svenpetersen1965/C64-Keyboard/C64 Keyboard Standard Version/Rev. 0/Text/223_cover_sheet.docx

Project Documentation

C64 Mechanical Keyboard & Kernal Switcher

Project number: 223

Revision: 0

Date: 17.01.2025
