svenpetersen1965/C64-Keyboard/C64 Keyboard with Hot Swap Sockets/Rev. 2/Text/225_cover_sheet.docx

Project Documentation

C64 Mechanical Keyboard & Kernal Switcher
with Hot Swap Sockets

Project number: 225

Revision: 2

Date: 12.06.2026
