svenpetersen1965/C64-Keyboard/C64 Keyboard Standard Version/Rev. 2/Text/223_cover_sheet.docx

Project Documentation

C64 Mechanical Keyboard & Kernal Switcher

Project number: 223

Revision: 2

Date: 12.06.2026
