svenpetersen1965/C64-Keyboard/C64 Keyboard Standard Version/Rev. 1/Text/223_cover_sheet.docx

Project Documentation

C64 Mechanical Keyboard & Kernal Switcher

Project number: 223

Revision: 1

Date: 21.05.2026
