svenpetersen1965/C64-Keyboard/C64 Keyboard connector PCB/Rev. 0/text/224_cover_sheet.docx

Project Documentation

C64 Keyboard Connector PCB

Project number: 224

Revision: 0

Date: 04.06.2026
