svenpetersen1965/C64-Keyboard/Keycaps/text/230_cover_sheet.docx

How to: Keycaps

Project number: 230

Revision: 0.0

Date: 04.09.2026

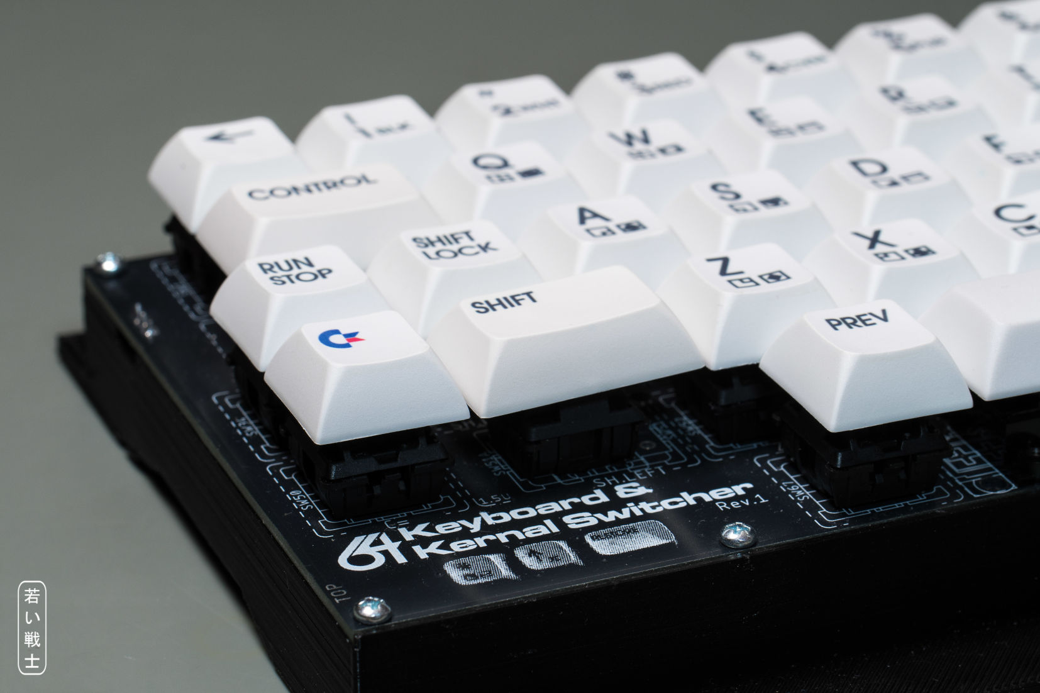
[picture p92: figure]
