svenpetersen1965/C64-Keyboard/C64 Keyboard Standard Version/Rev. 0/pictures/0258_-_C64_KB_PCBs.JPG

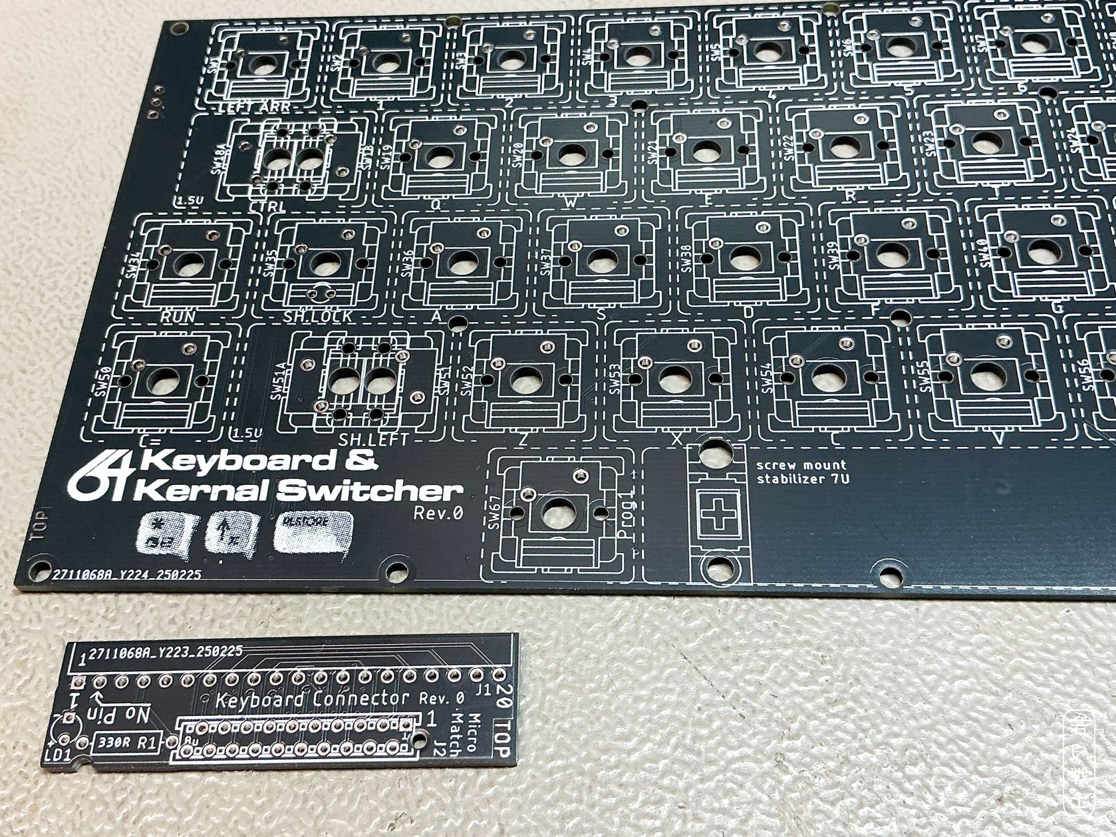
C64 Keyboard Standard Version/Rev. 0/pictures/0258_-_C64_KB_PCBs.JPG
