svenpetersen1965/C64-Keyboard/C64 Keyboard Standard Version/Rev. 0/pictures/0268_-_7U_stabilizer_L.JPG

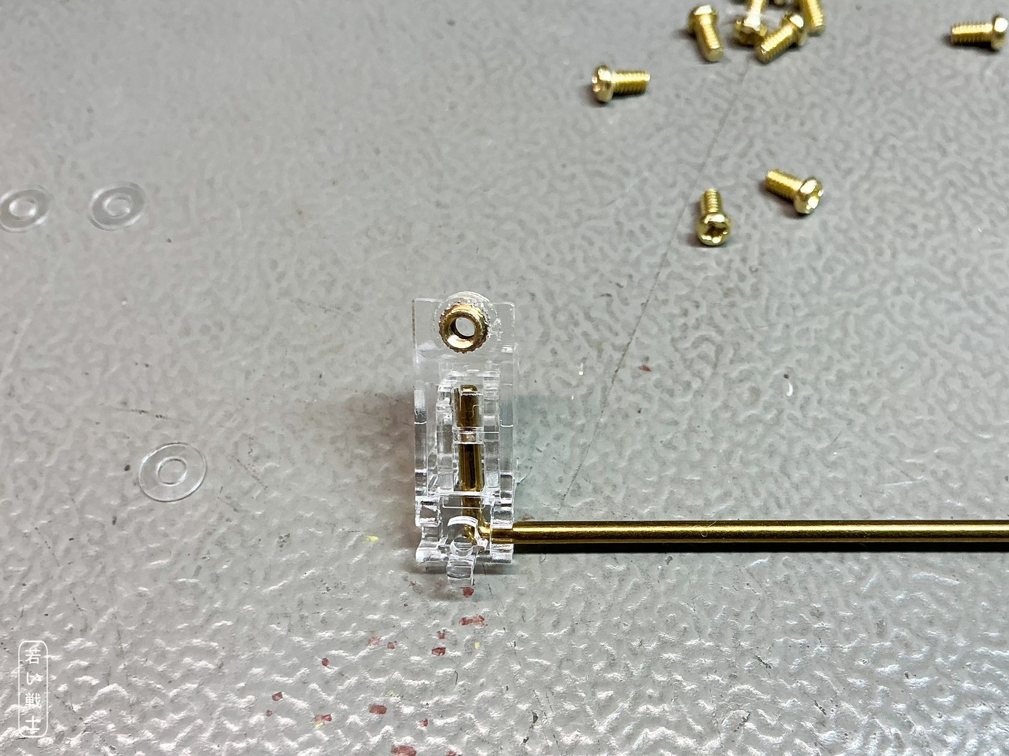
C64 Keyboard Standard Version/Rev. 0/pictures/0268_-_7U_stabilizer_L.JPG
