svenpetersen1965/C64-Keyboard/C64 Keyboard Standard Version/Rev. 0/pictures/0269_-_7U_stabilizer_R.JPG

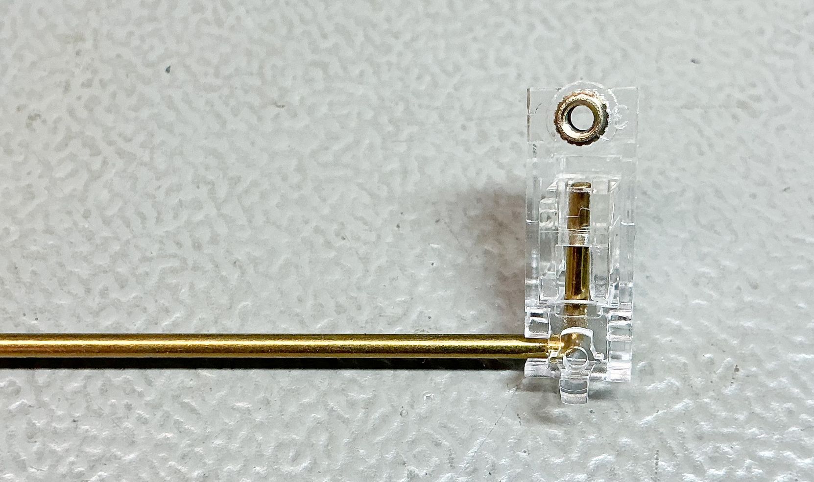
C64 Keyboard Standard Version/Rev. 0/pictures/0269_-_7U_stabilizer_R.JPG
