svenpetersen1965/C64-Keyboard/C64 Keyboard Standard Version/Rev. 0/pictures/0293_-_kb_in_retro_fuzion_case.JPG

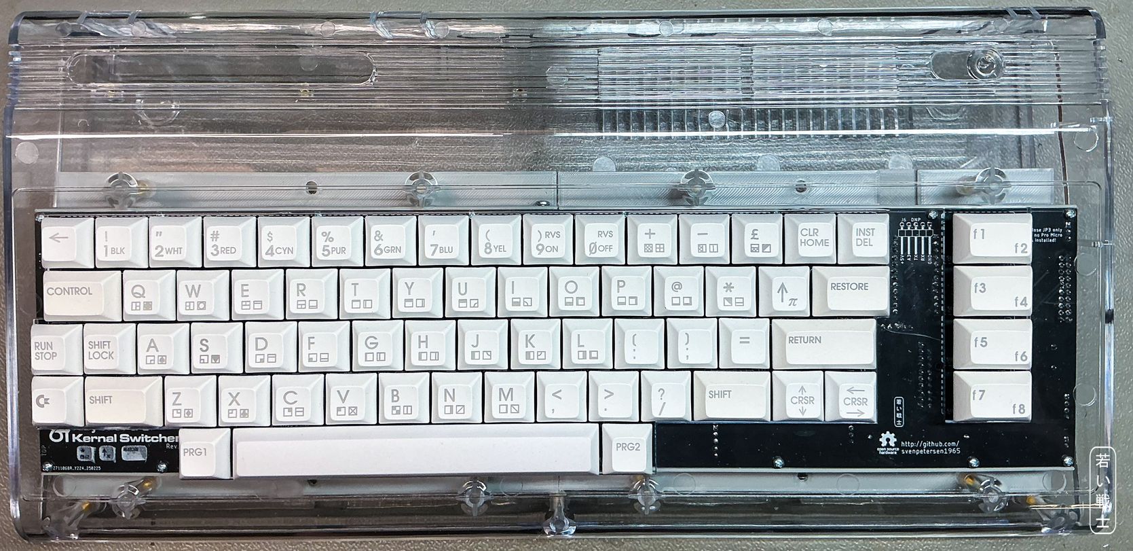
C64 Keyboard Standard Version/Rev. 0/pictures/0293_-_kb_in_retro_fuzion_case.JPG
