svenpetersen1965/C64-Keyboard/C64 Keyboard Standard Version/Rev. 0/pictures/0296_-_kb_in_dirty_breadbin.JPG

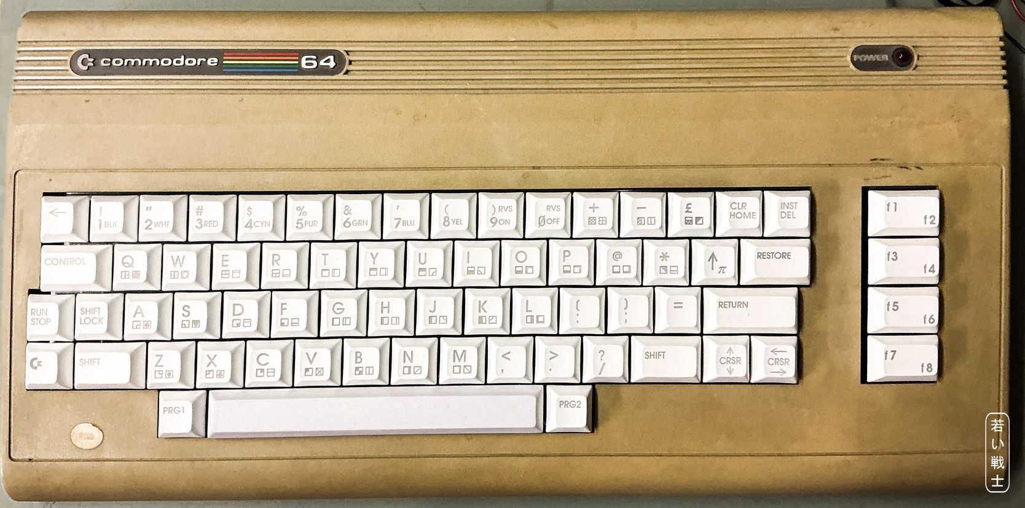
C64 Keyboard Standard Version/Rev. 0/pictures/0296_-_kb_in_dirty_breadbin.JPG
