svenpetersen1965/C64-Keyboard/C64 Keyboard Standard Version/Rev. 0/pictures/0303_-_collision_C64C.JPG

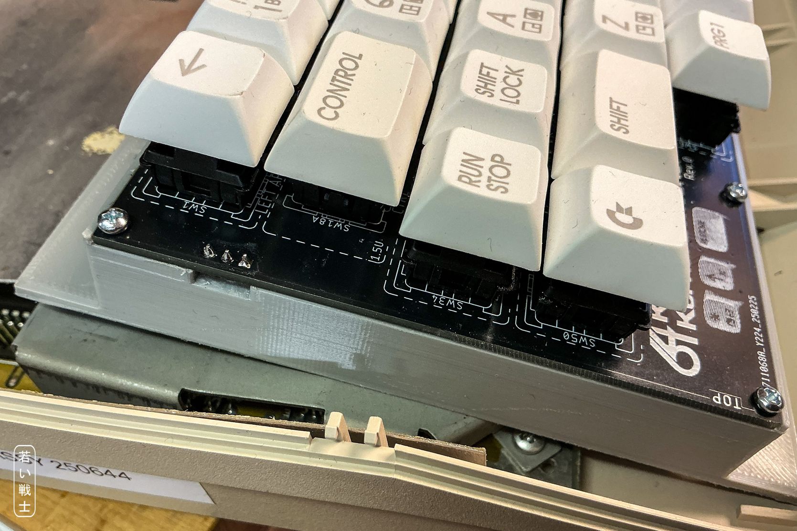
C64 Keyboard Standard Version/Rev. 0/pictures/0303_-_collision_C64C.JPG
