svenpetersen1965/C64-Keyboard/C64 Keyboard Standard Version/Rev. 0/pictures/0335_-_SE_layxout.JPG

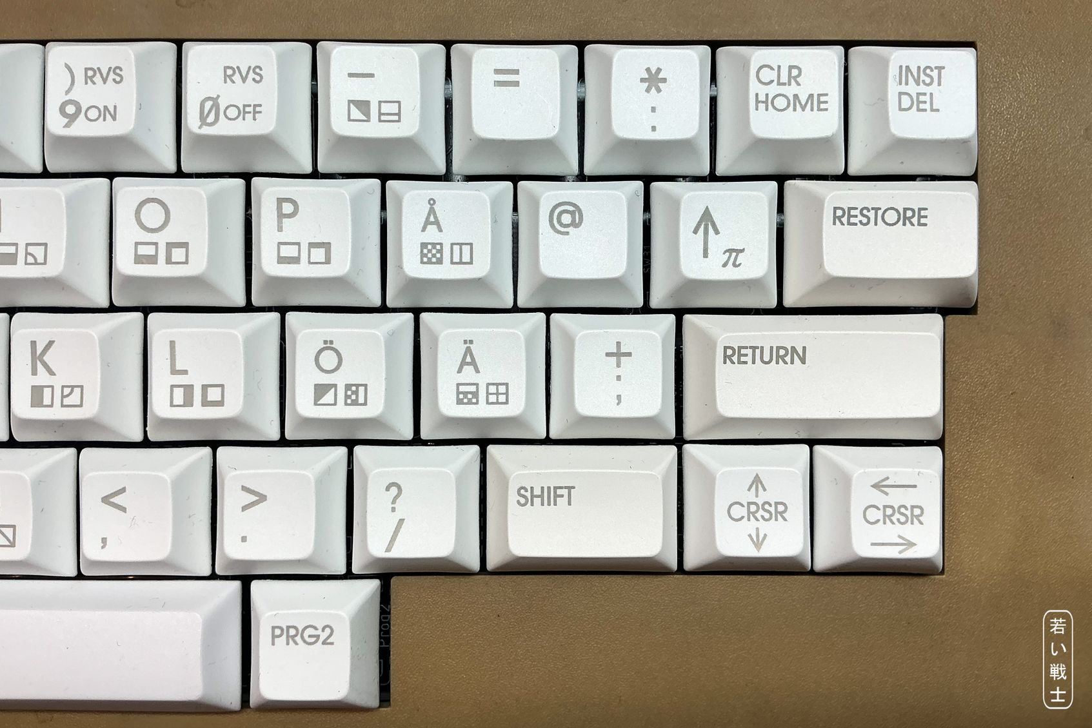
C64 Keyboard Standard Version/Rev. 0/pictures/0335_-_SE_layxout.JPG
