svenpetersen1965/C64-Keyboard/C64 Keyboard Standard Version/Rev. 0/pictures/0339_-_ES_layout.JPG

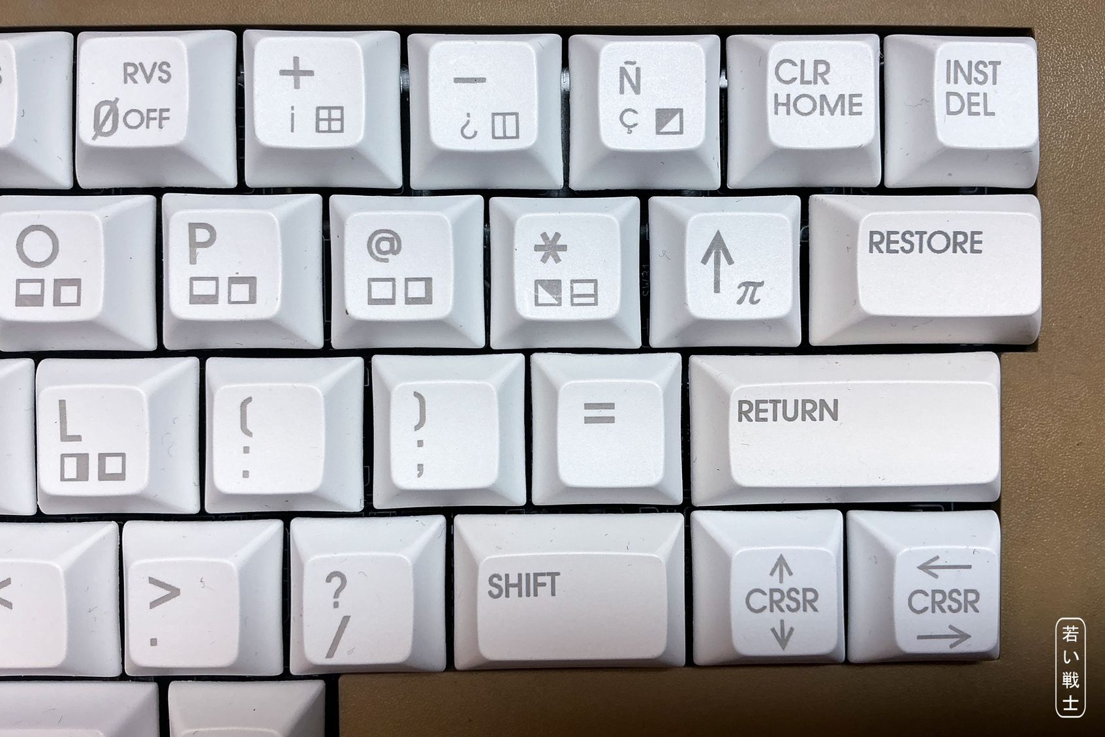
C64 Keyboard Standard Version/Rev. 0/pictures/0339_-_ES_layout.JPG
