svenpetersen1965/C64-Keyboard/C64 Keyboard Standard Version/Rev. 0/pictures/0346_-_complete_keyboard.JPG

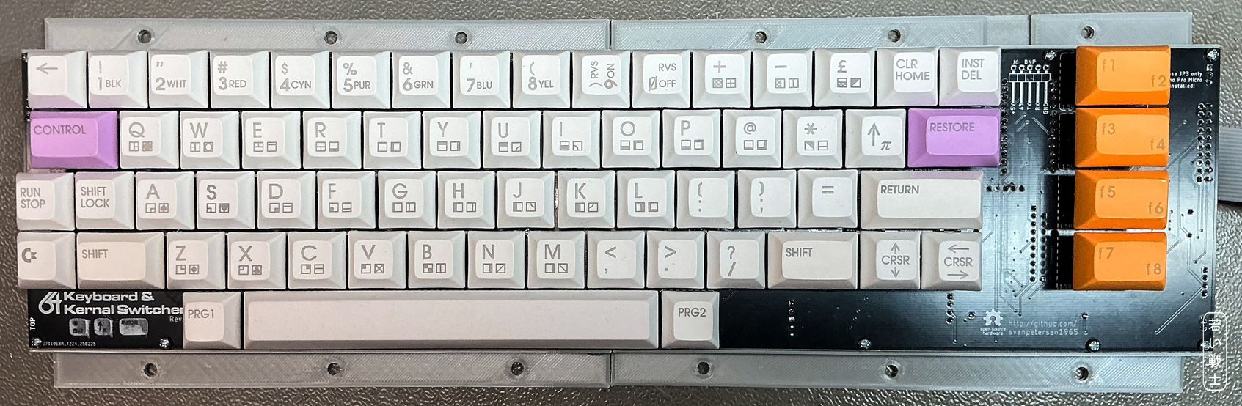
C64 Keyboard Standard Version/Rev. 0/pictures/0346_-_complete_keyboard.JPG
