svenpetersen1965/C64-Keyboard/C64 Keyboard Standard Version/Rev. 0/pictures/0347_-_bottom_w_stiffner.JPG

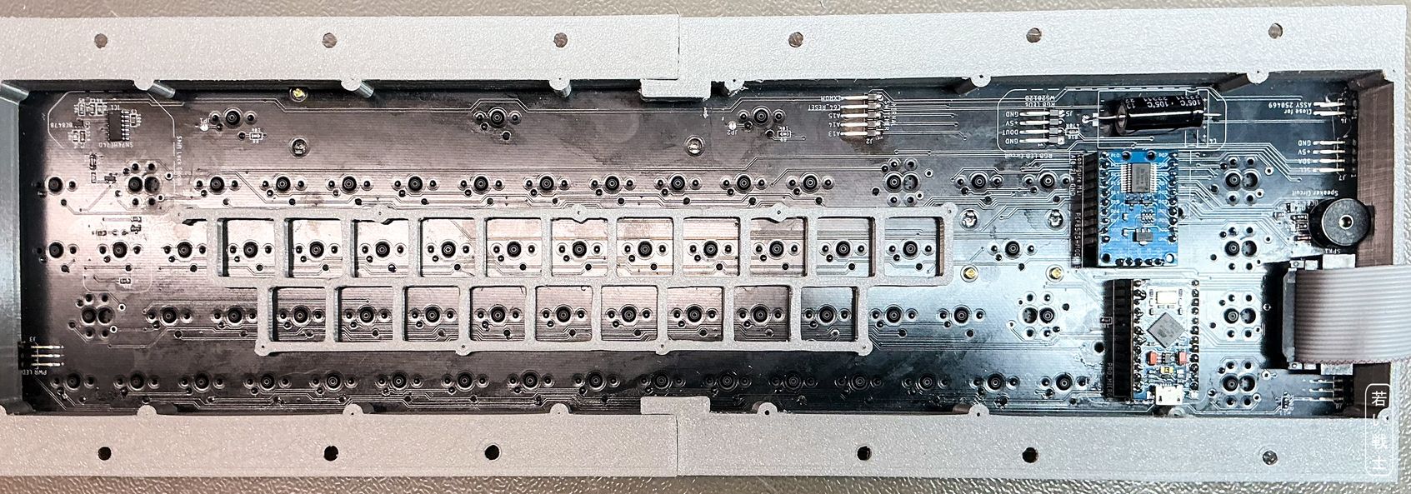
C64 Keyboard Standard Version/Rev. 0/pictures/0347_-_bottom_w_stiffner.JPG
