svenpetersen1965/C64-Keyboard/C64 Keyboard Standard Version/Rev. 0/pictures/4119_-_PCF8575_top.JPG

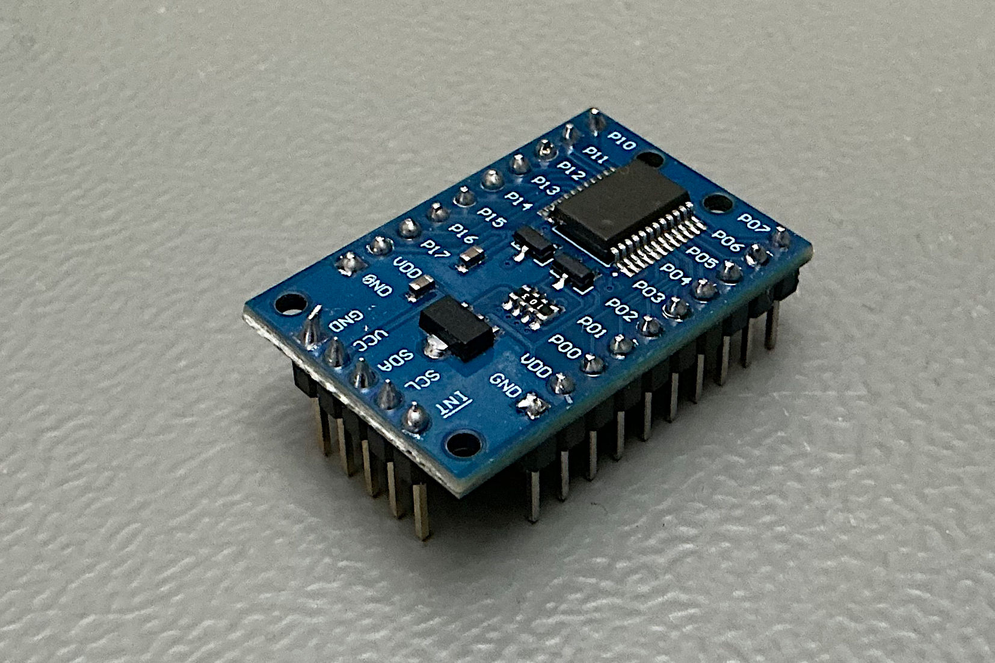
C64 Keyboard Standard Version/Rev. 0/pictures/4119_-_PCF8575_top.JPG
