svenpetersen1965/C64-Keyboard/C64 Keyboard Standard Version/Rev. 0/pictures/4126_-_J2_Kernal_Select.JPG

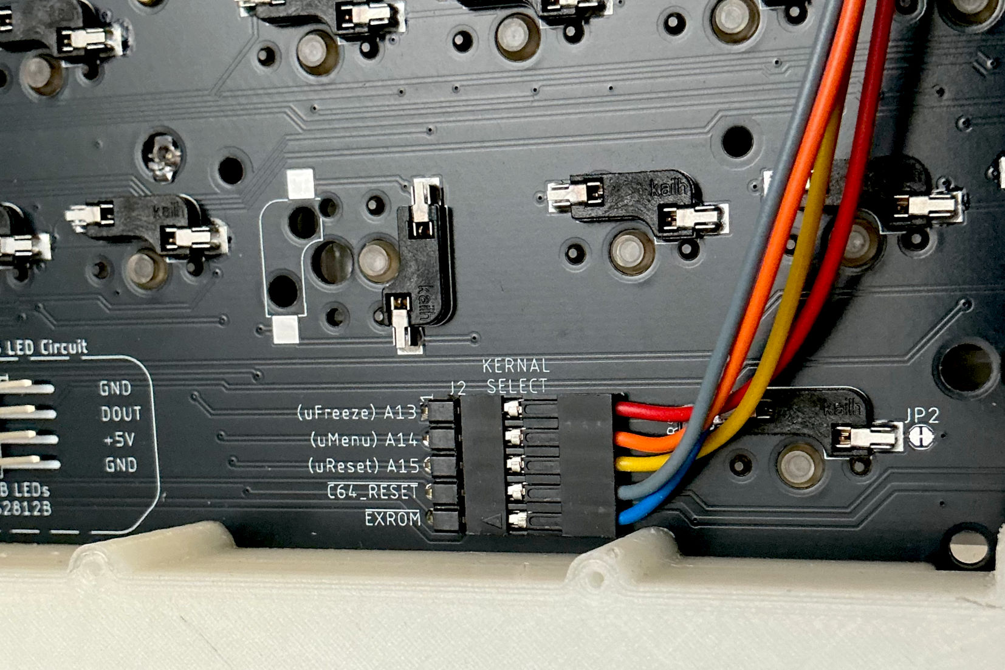
C64 Keyboard Standard Version/Rev. 0/pictures/4126_-_J2_Kernal_Select.JPG
