svenpetersen1965/C64-Keyboard/C64 Keyboard Standard Version/Rev. 0/pictures/4128_-_top_w_cables.JPG

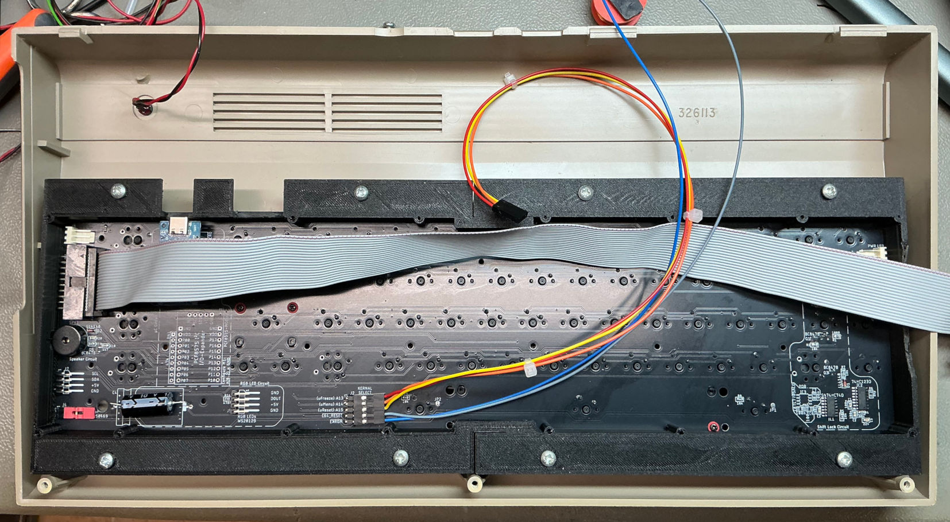
C64 Keyboard Standard Version/Rev. 0/pictures/4128_-_top_w_cables.JPG
