svenpetersen1965/C64-Keyboard/C64 Keyboard Standard Version/Rev. 0/pictures/4382_-_Shift_Lock.JPG

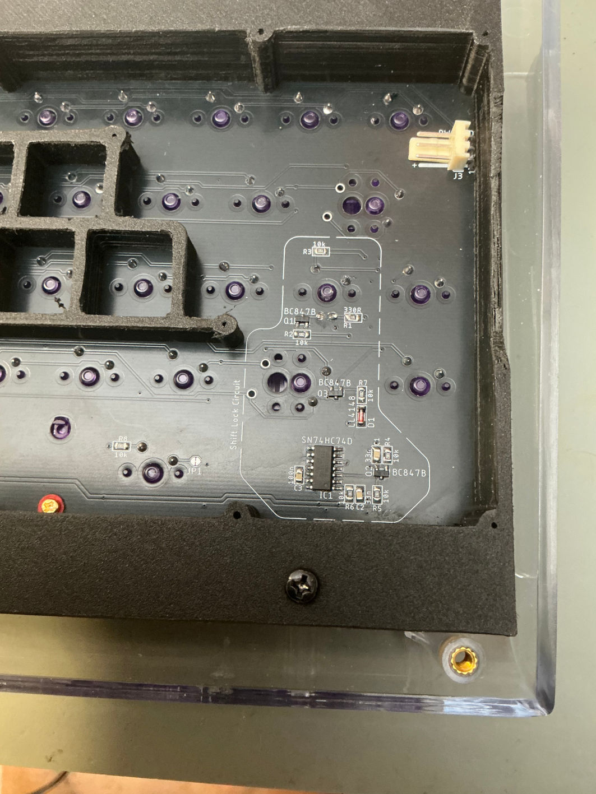
C64 Keyboard Standard Version/Rev. 0/pictures/4382_-_Shift_Lock.JPG
