svenpetersen1965/C64-Keyboard/C64 Keyboard Standard Version/Rev. 0/pictures/4384_-_RGB_LED.JPG

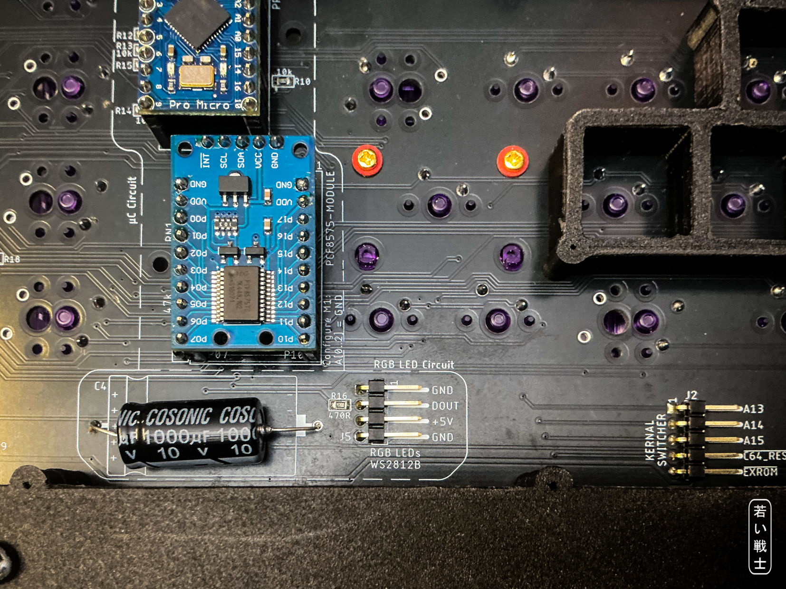
C64 Keyboard Standard Version/Rev. 0/pictures/4384_-_RGB_LED.JPG
