svenpetersen1965/C64-Keyboard/C64 Keyboard Standard Version/Rev. 0/pictures/4387_-_pro_micro_circuit.JPG

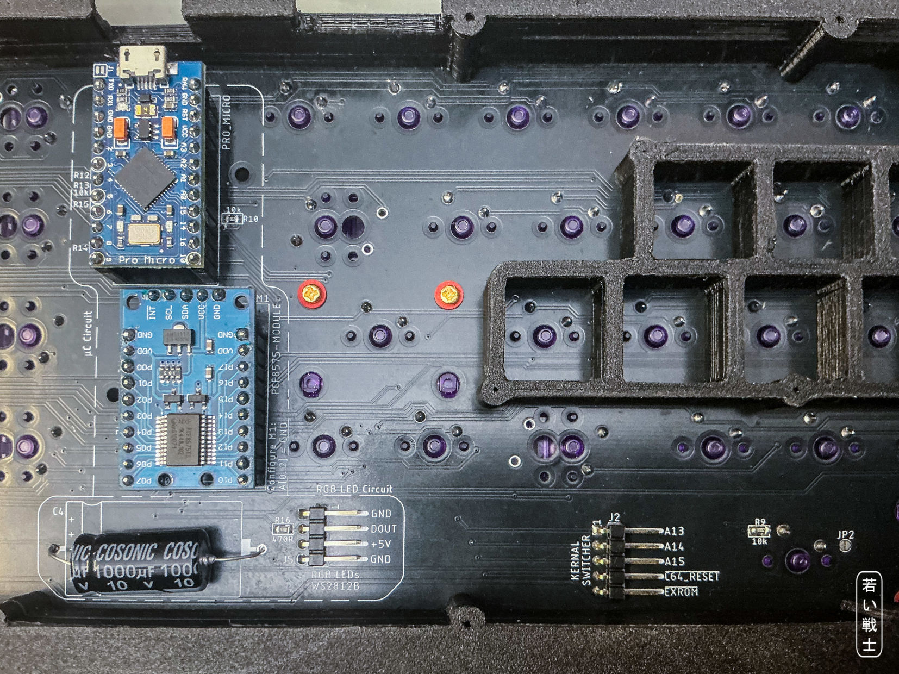
C64 Keyboard Standard Version/Rev. 0/pictures/4387_-_pro_micro_circuit.JPG
