svenpetersen1965/C64-Keyboard/C64 Keyboard Standard Version/Rev. 0/pictures/4558_-_ultimate_button_connector.JPG

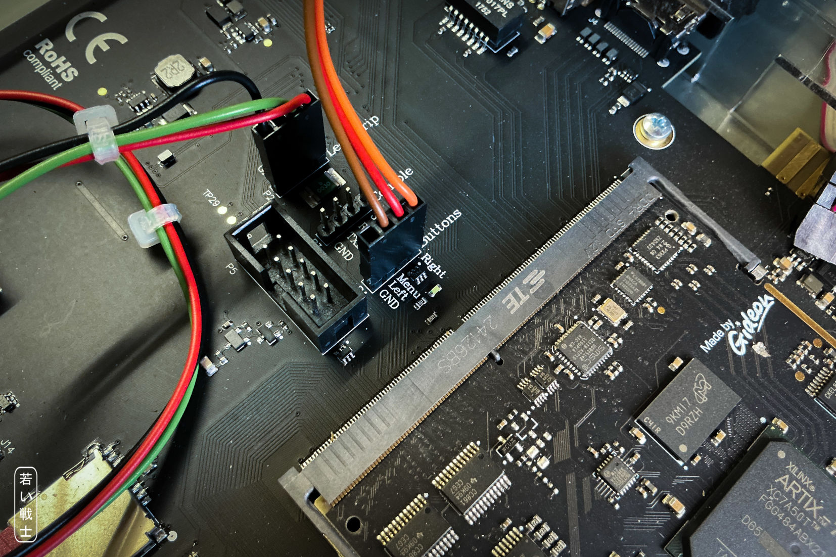
C64 Keyboard Standard Version/Rev. 0/pictures/4558_-_ultimate_button_connector.JPG
