svenpetersen1965/C64-Keyboard/C64 Keyboard Standard Version/Rev. 0/pictures/4559_-_ultimate_button_cable.JPG

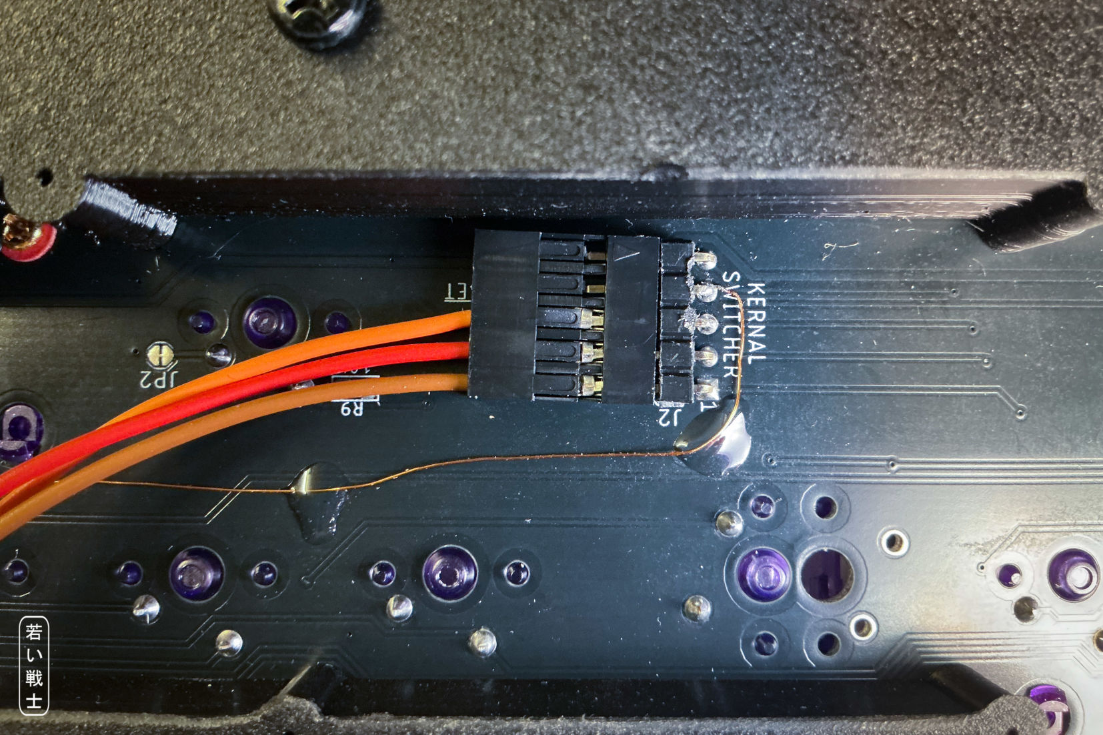
C64 Keyboard Standard Version/Rev. 0/pictures/4559_-_ultimate_button_cable.JPG
