svenpetersen1965/C64-Keyboard/C64 Keyboard Standard Version/Rev. 0/pictures/9813_-_switch_bouncing.JPG

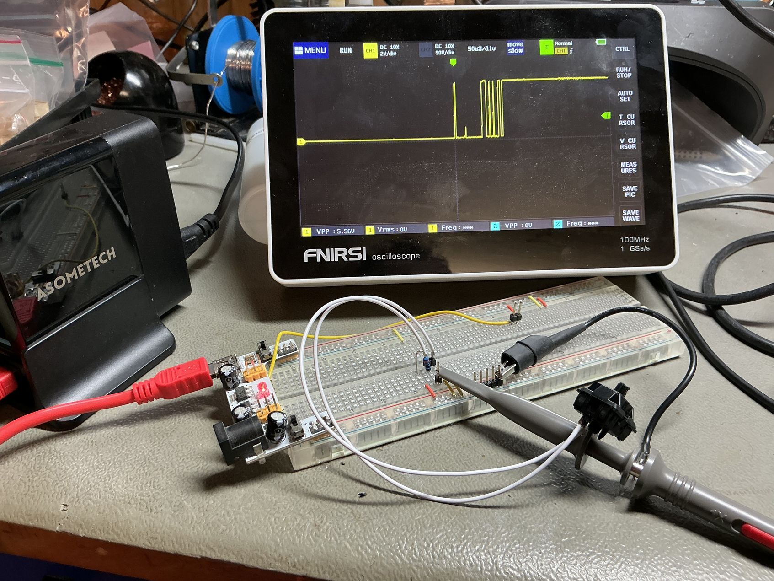
C64 Keyboard Standard Version/Rev. 0/pictures/9813_-_switch_bouncing.JPG
