svenpetersen1965/C64-Keyboard/C64 Keyboard Standard Version/Rev. 0/pictures/9957_-_measuring_key_position.JPG

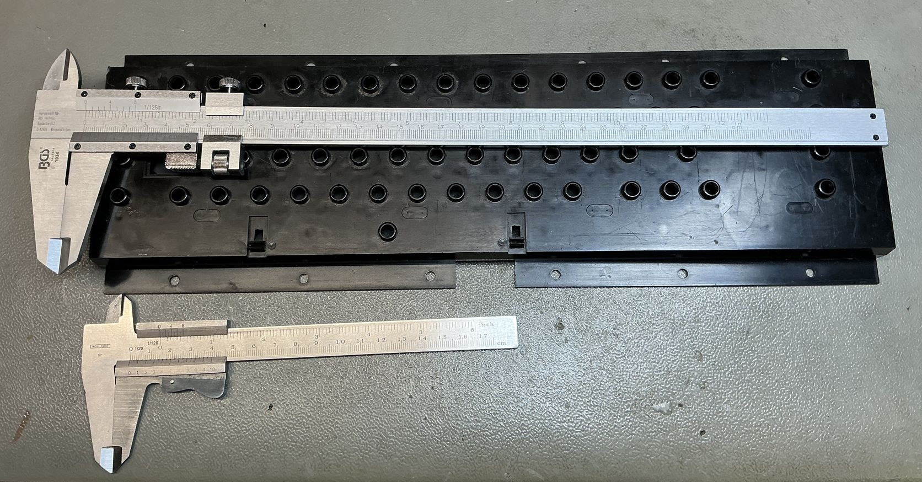
C64 Keyboard Standard Version/Rev. 0/pictures/9957_-_measuring_key_position.JPG
