svenpetersen1965/C64-Keyboard/C64 Keyboard Standard Version/Rev. 0/pictures/Ultimate_freeze_falling.png

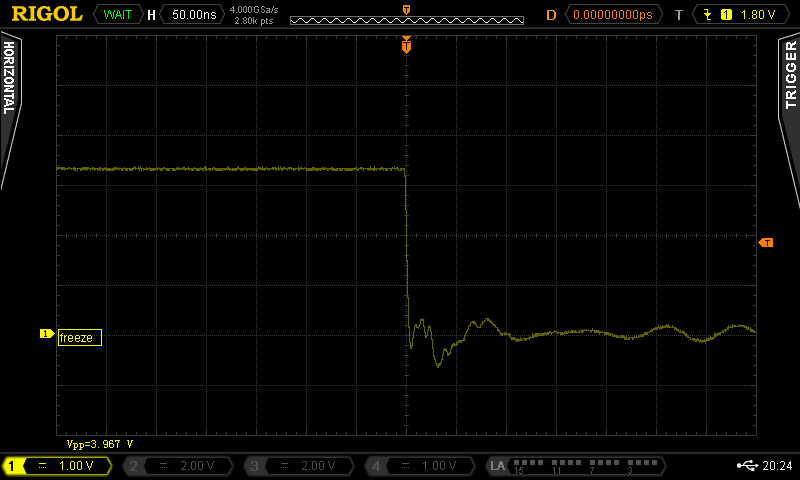
C64 Keyboard Standard Version/Rev. 0/pictures/Ultimate_freeze_falling.png
