svenpetersen1965/C64-Keyboard/C64 Keyboard Standard Version/Rev. 1/pictures/3988_-_v1_stabilizer.JPG

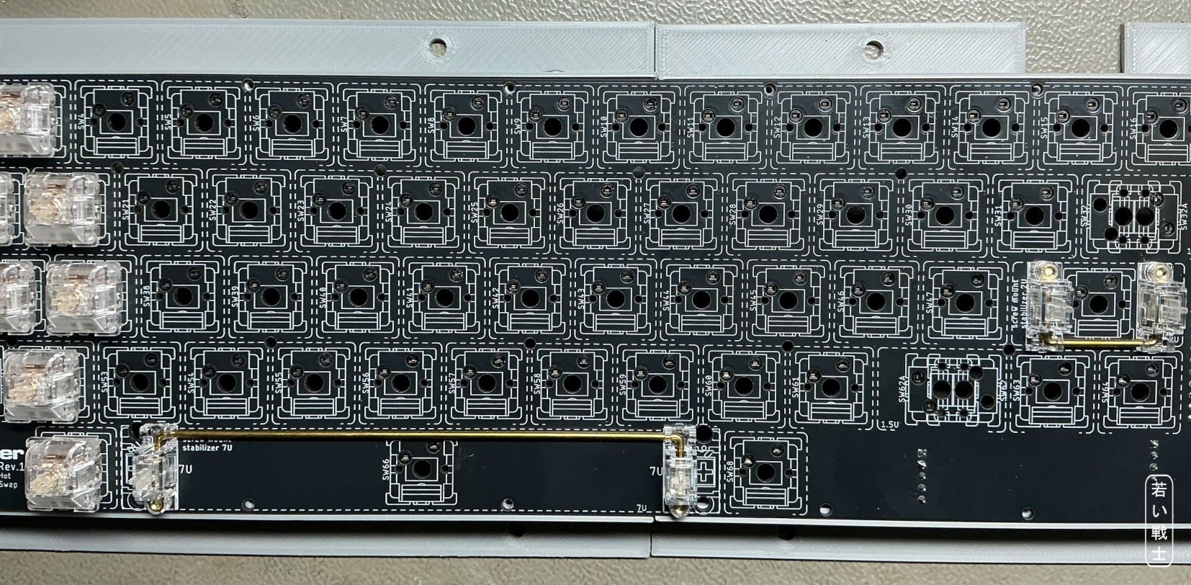
C64 Keyboard Standard Version/Rev. 1/pictures/3988_-_v1_stabilizer.JPG
