svenpetersen1965/C64-Keyboard/C64 Keyboard Standard Version/Rev. 1/pictures/3989_-_C64KB_v1_complete.JPG

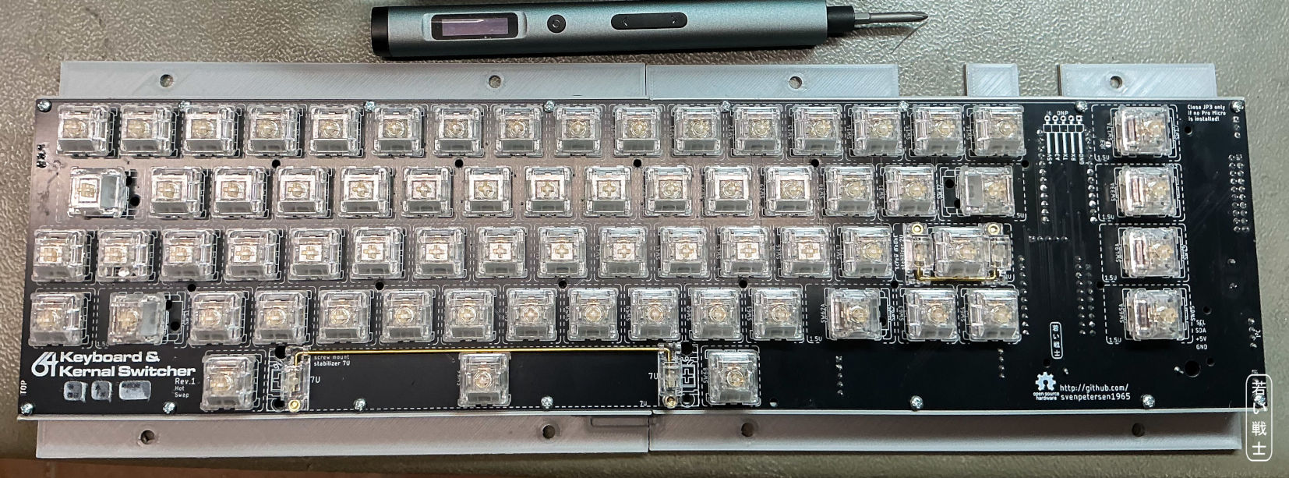
C64 Keyboard Standard Version/Rev. 1/pictures/3989_-_C64KB_v1_complete.JPG
