svenpetersen1965/C64-Keyboard/C64 Keyboard Standard Version/Rev. 1/pictures/4592_-_9U_stabilizer.JPG

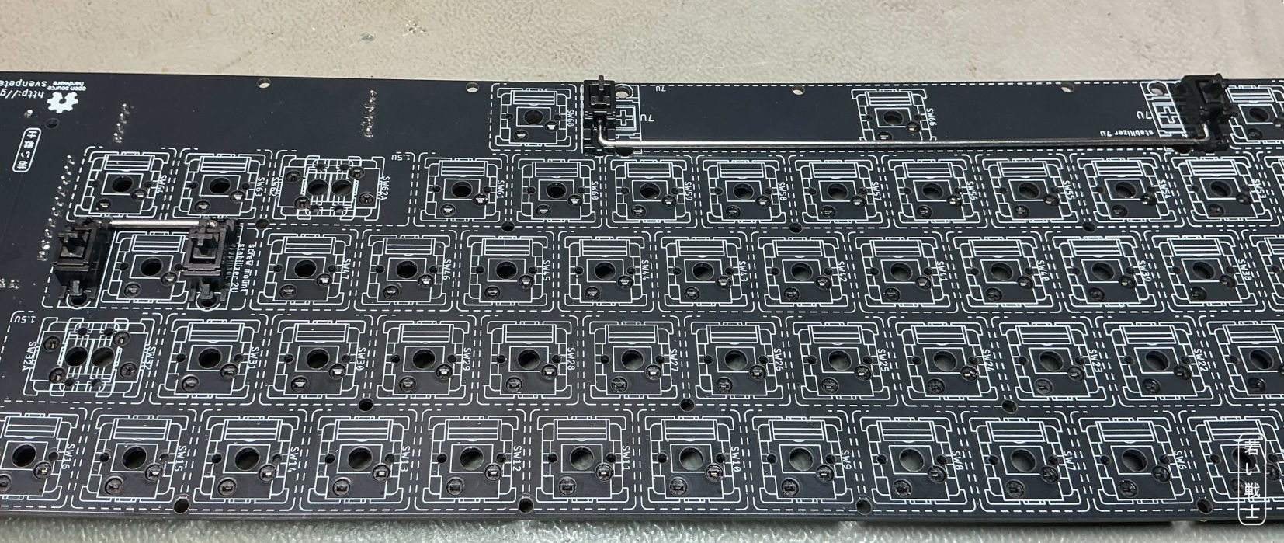
C64 Keyboard Standard Version/Rev. 1/pictures/4592_-_9U_stabilizer.JPG
