svenpetersen1965/C64-Keyboard/Cables/pictures/4047_-_Detail_MicroMatch.JPG

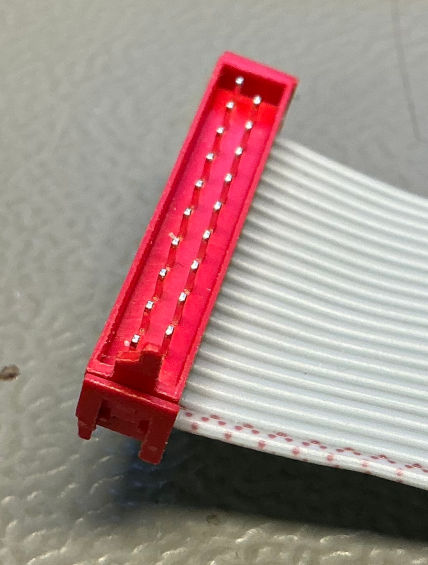
Cables/pictures/4047_-_Detail_MicroMatch.JPG
