svenpetersen1965/C64-Keyboard/Cables/pictures/4127_-_kernal_switcher_cable.JPG

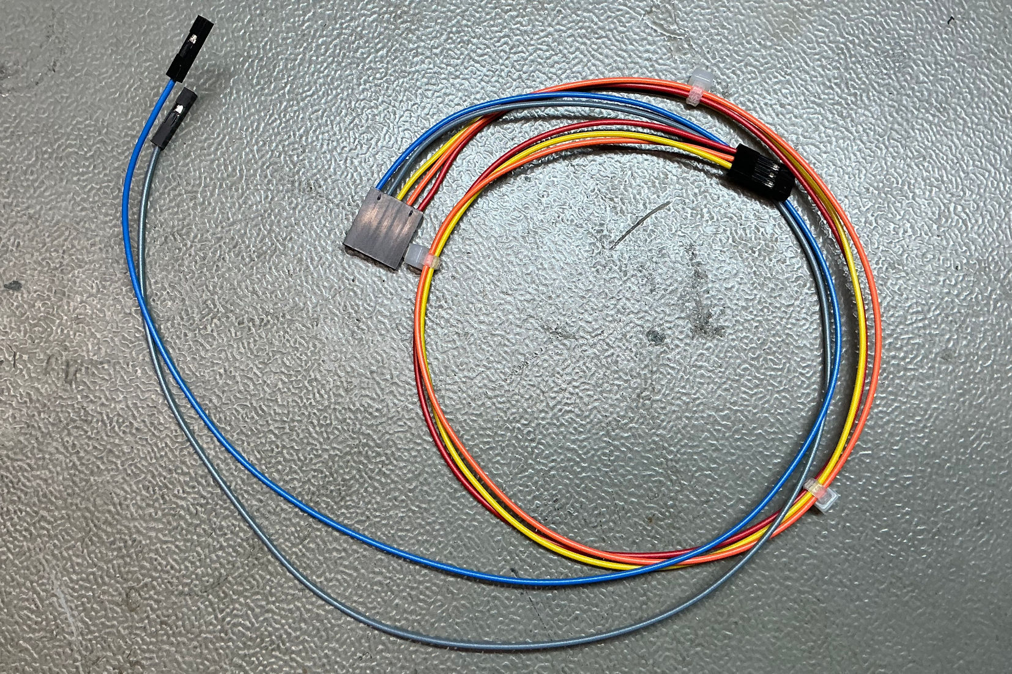
Cables/pictures/4127_-_kernal_switcher_cable.JPG
