svenpetersen1965/C64-Keyboard/Keycaps/Exported-DSA-keycaps/Danisch/SW45_AE.png

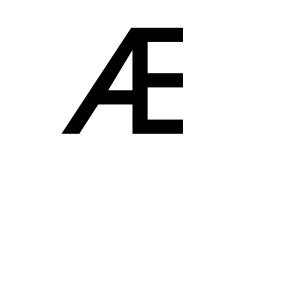
Keycaps/Exported-DSA-keycaps/Danisch/SW45_AE.png
