svenpetersen1965/C64-Keyboard/Keycaps/Exported-DSA-keycaps/Danisch/SW47_semicolon.png

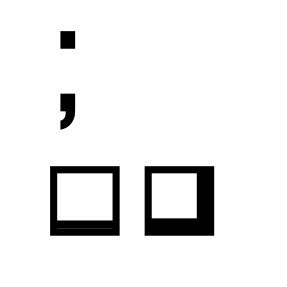
Keycaps/Exported-DSA-keycaps/Danisch/SW47_semicolon.png
