svenpetersen1965/C64-Keyboard/Keycaps/Exported-DSA-keycaps/Spanish/SW14_Ntilde.png

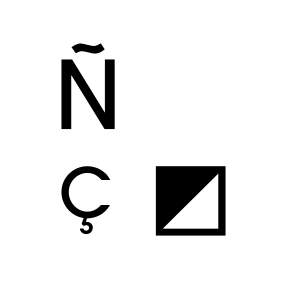
Keycaps/Exported-DSA-keycaps/Spanish/SW14_Ntilde.png
