svenpetersen1965/C64-Keyboard/Keycaps/Exported-DSA-keycaps/SW1_left_arrow.png

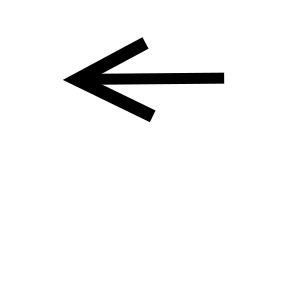
Keycaps/Exported-DSA-keycaps/SW1_left_arrow.png
