svenpetersen1965/C64-Keyboard/Keycaps/Exported-DSA-keycaps/SW2_1.png

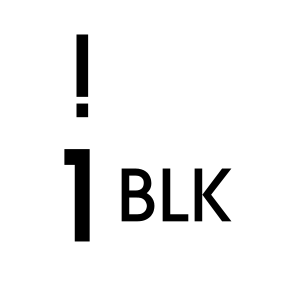
Keycaps/Exported-DSA-keycaps/SW2_1.png
