svenpetersen1965/C64-Keyboard/Keycaps/Exported-DSA-keycaps/SW4_3.png

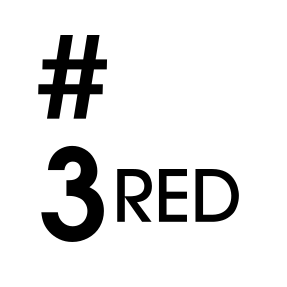
Keycaps/Exported-DSA-keycaps/SW4_3.png
