svenpetersen1965/C64-Keyboard/Keycaps/Exported-DSA-keycaps/SW6_5.png

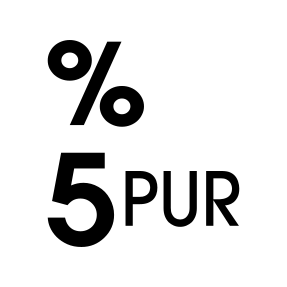
Keycaps/Exported-DSA-keycaps/SW6_5.png
