svenpetersen1965/C64-Keyboard/Keycaps/Exported-DSA-keycaps/SW11_0.png

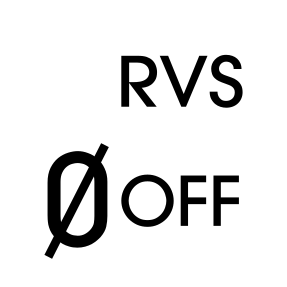
Keycaps/Exported-DSA-keycaps/SW11_0.png
