svenpetersen1965/C64-Keyboard/Keycaps/Exported-DSA-keycaps/SW15_clrhome.png

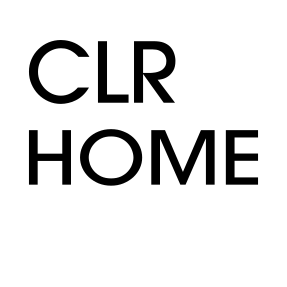
Keycaps/Exported-DSA-keycaps/SW15_clrhome.png
