svenpetersen1965/C64-Keyboard/Keycaps/Exported-DSA-keycaps/SW17_f1f2.png

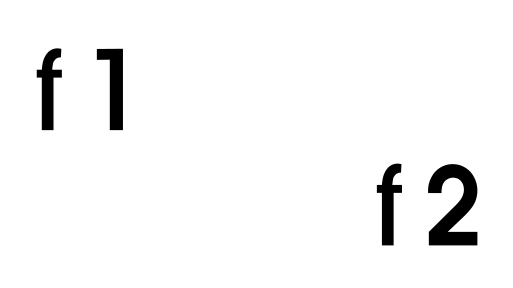
Keycaps/Exported-DSA-keycaps/SW17_f1f2.png
