svenpetersen1965/C64-Keyboard/Keycaps/Exported-DSA-keycaps/SW18_CONTROL.png

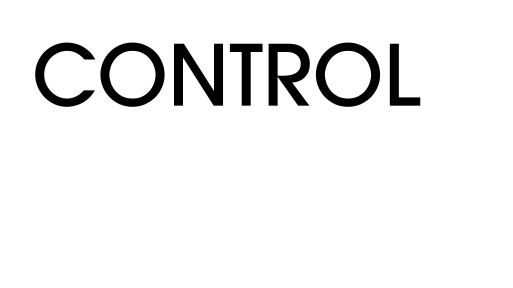
Keycaps/Exported-DSA-keycaps/SW18_CONTROL.png
