svenpetersen1965/C64-Keyboard/Keycaps/Exported-DSA-keycaps/SW22_R.png

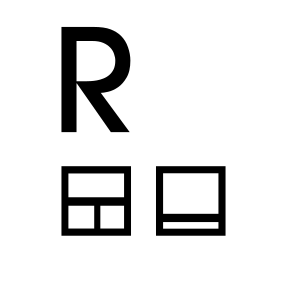
Keycaps/Exported-DSA-keycaps/SW22_R.png
