svenpetersen1965/C64-Keyboard/Keycaps/Exported-DSA-keycaps/SW24_Y.png

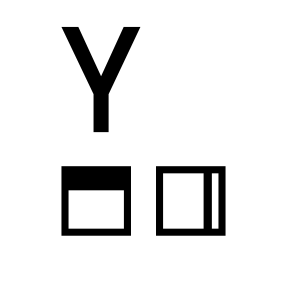
Keycaps/Exported-DSA-keycaps/SW24_Y.png
