svenpetersen1965/C64-Keyboard/Keycaps/Exported-DSA-keycaps/SW25_U.png

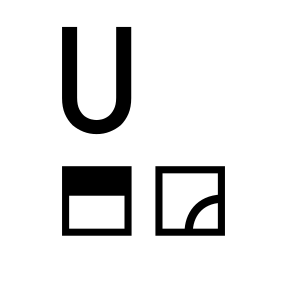
Keycaps/Exported-DSA-keycaps/SW25_U.png
