svenpetersen1965/C64-Keyboard/Keycaps/Exported-DSA-keycaps/SW26_I.png

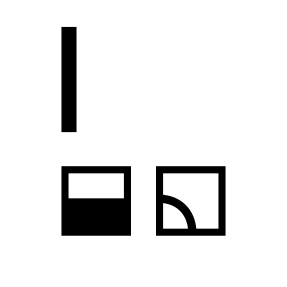
Keycaps/Exported-DSA-keycaps/SW26_I.png
