svenpetersen1965/C64-Keyboard/Keycaps/Exported-DSA-keycaps/SW29_at.png

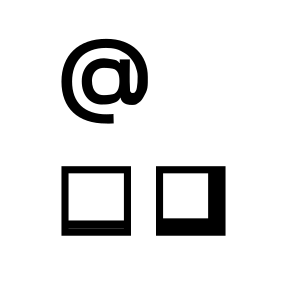
Keycaps/Exported-DSA-keycaps/SW29_at.png
