svenpetersen1965/C64-Keyboard/Keycaps/Exported-DSA-keycaps/SW31_up_arrow.png

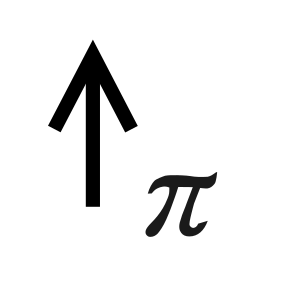
Keycaps/Exported-DSA-keycaps/SW31_up_arrow.png
