svenpetersen1965/C64-Keyboard/Keycaps/Exported-DSA-keycaps/SW33_f3f4.png

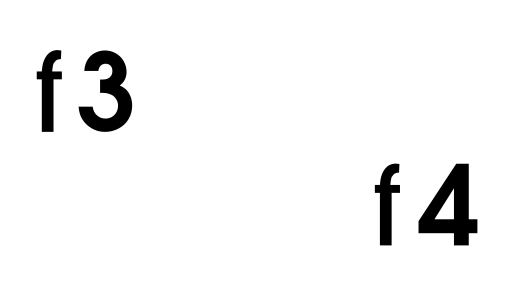
Keycaps/Exported-DSA-keycaps/SW33_f3f4.png
