svenpetersen1965/C64-Keyboard/Keycaps/Exported-DSA-keycaps/SW38_D.png

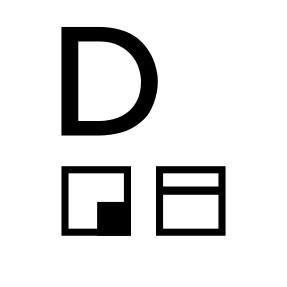
Keycaps/Exported-DSA-keycaps/SW38_D.png
