svenpetersen1965/C64-Keyboard/Keycaps/Exported-DSA-keycaps/SW39_F.png

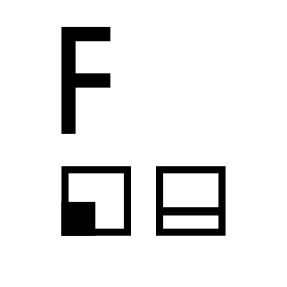
Keycaps/Exported-DSA-keycaps/SW39_F.png
