svenpetersen1965/C64-Keyboard/Keycaps/Exported-DSA-keycaps/SW44_L.png

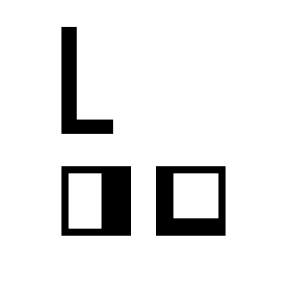
Keycaps/Exported-DSA-keycaps/SW44_L.png
