svenpetersen1965/C64-Keyboard/Keycaps/Exported-DSA-keycaps/SW50_64.png

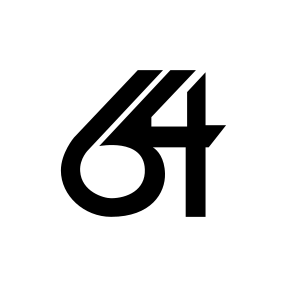
Keycaps/Exported-DSA-keycaps/SW50_64.png
