svenpetersen1965/C64-Keyboard/Keycaps/Exported-DSA-keycaps/SW50_C=.png

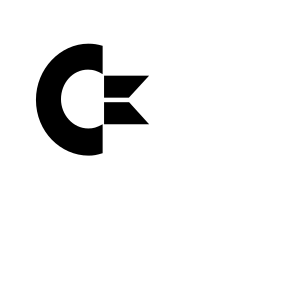
Keycaps/Exported-DSA-keycaps/SW50_C=.png
