svenpetersen1965/C64-Keyboard/Keycaps/Exported-DSA-keycaps/SW51_shift.png

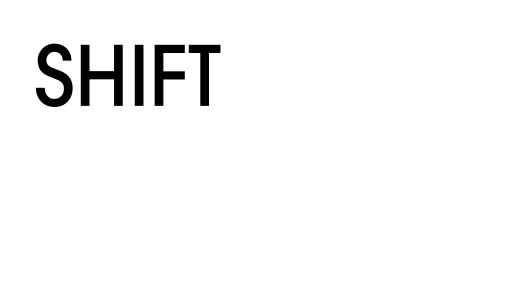
Keycaps/Exported-DSA-keycaps/SW51_shift.png
