svenpetersen1965/C64-Keyboard/Keycaps/Exported-DSA-keycaps/SW55_V.png

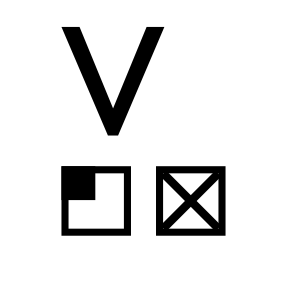
Keycaps/Exported-DSA-keycaps/SW55_V.png
