svenpetersen1965/C64-Keyboard/Keycaps/Exported-DSA-keycaps/SW56_B.png

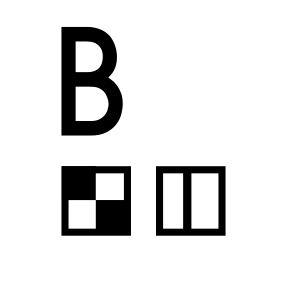
Keycaps/Exported-DSA-keycaps/SW56_B.png
