svenpetersen1965/C64-Keyboard/Keycaps/Exported-DSA-keycaps/SW59_comma.png

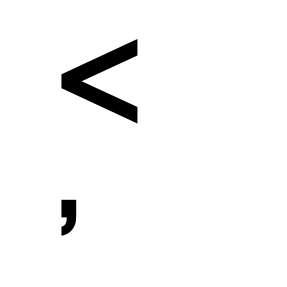
Keycaps/Exported-DSA-keycaps/SW59_comma.png
