svenpetersen1965/C64-Keyboard/Keycaps/Exported-DSA-keycaps/SW64_CRSRlr.png

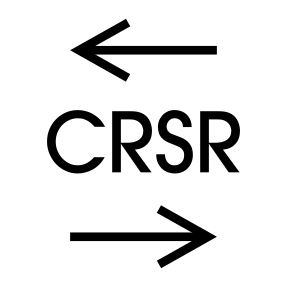
Keycaps/Exported-DSA-keycaps/SW64_CRSRlr.png
