svenpetersen1965/C64-Keyboard/Keycaps/Exported-DSA-keycaps/Swedish/SW12_minus.png

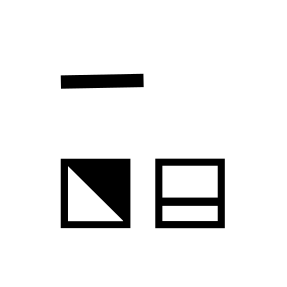
Keycaps/Exported-DSA-keycaps/Swedish/SW12_minus.png
