svenpetersen1965/C64-Keyboard/Keycaps/Exported-DSA-keycaps/Swedish/SW14_colon.png

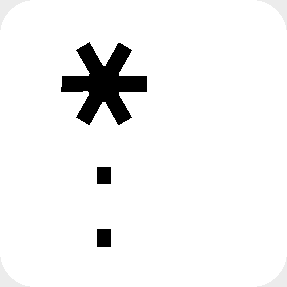
Keycaps/Exported-DSA-keycaps/Swedish/SW14_colon.png
