svenpetersen1965/C64-Keyboard/Keycaps/Exported-DSA-keycaps/Swedish/SW45_OE.png

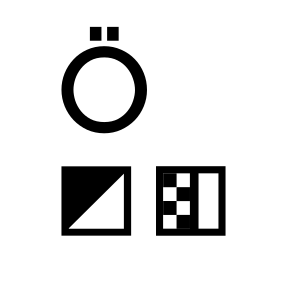
Keycaps/Exported-DSA-keycaps/Swedish/SW45_OE.png
