svenpetersen1965/C64-Keyboard/Keycaps/Exported-DSA-keycaps/Tray_1_0U_02.png

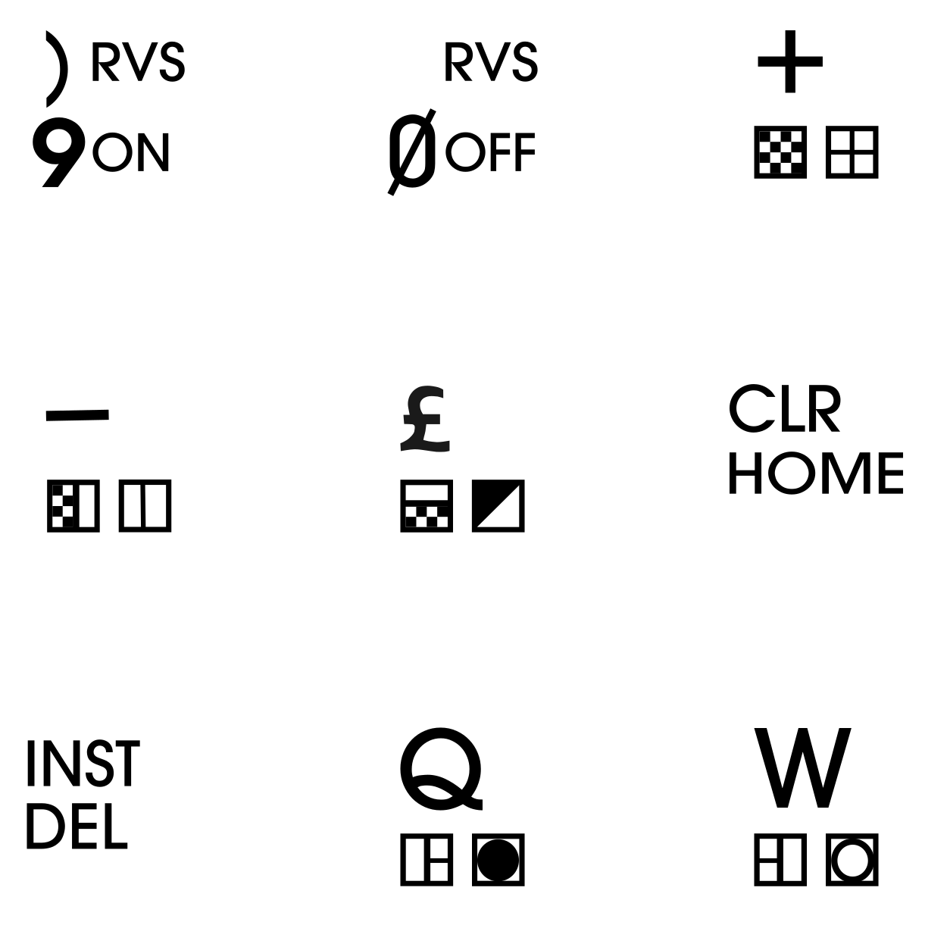
Keycaps/Exported-DSA-keycaps/Tray_1_0U_02.png
