svenpetersen1965/C64-Keyboard/Keycaps/Inkscape/resources/Ice-skating_bird_demon .png

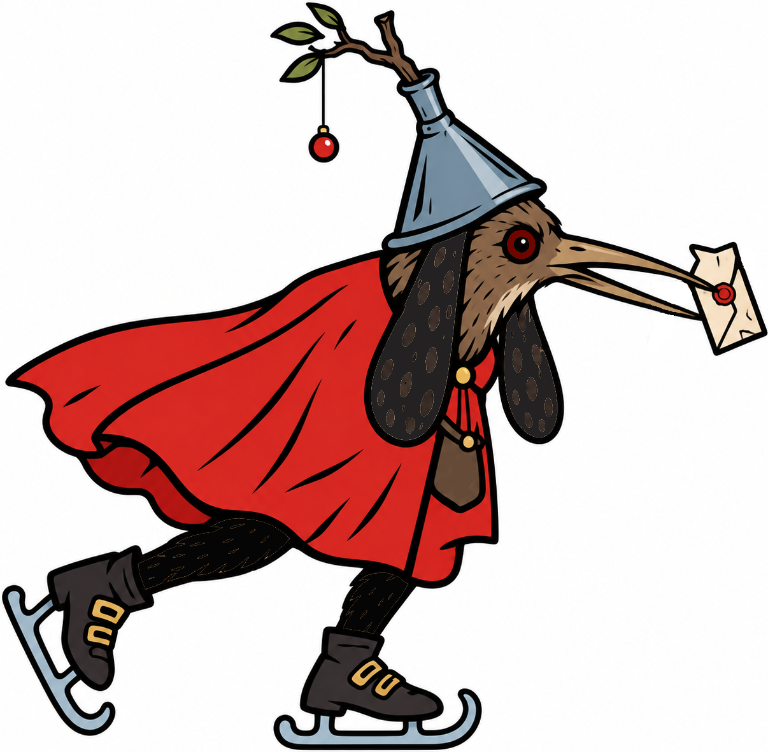
Keycaps/Inkscape/resources/Ice-skating_bird_demon .png
