svenpetersen1965/C64-Keyboard/Keycaps/pictures/0327_-_danish.JPG

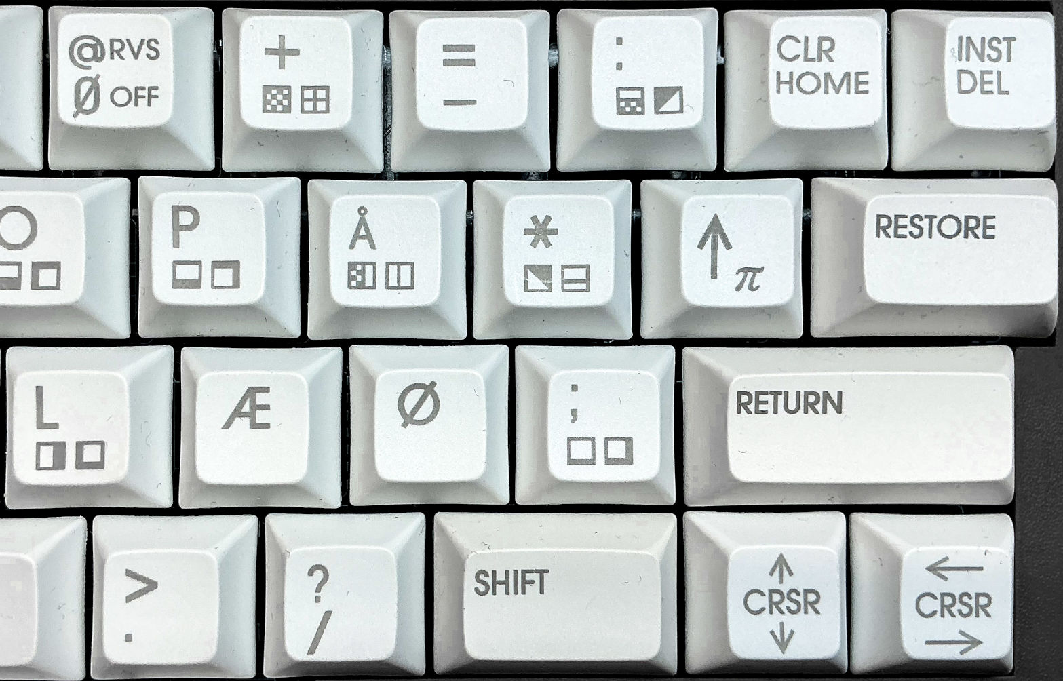
Keycaps/pictures/0327_-_danish.JPG
