svenpetersen1965/C64-Keyboard/Keycaps/pictures/0335_-_swedish.JPG

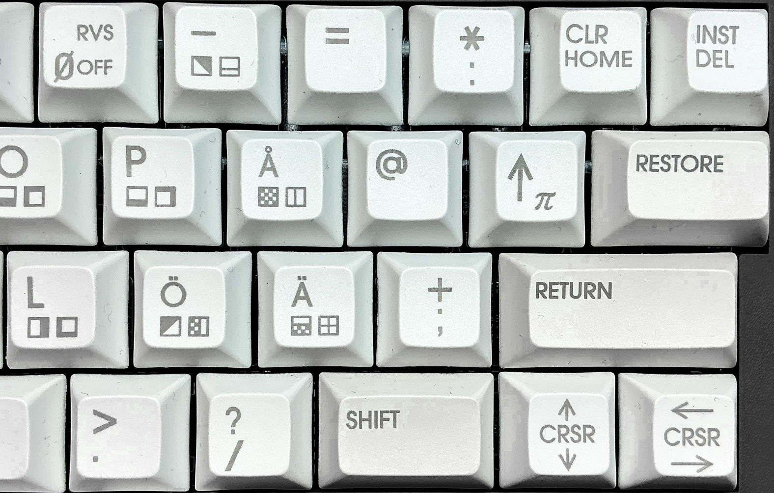
Keycaps/pictures/0335_-_swedish.JPG
