svenpetersen1965/C64-Keyboard/Keycaps/pictures/0339_-_spanish.JPG

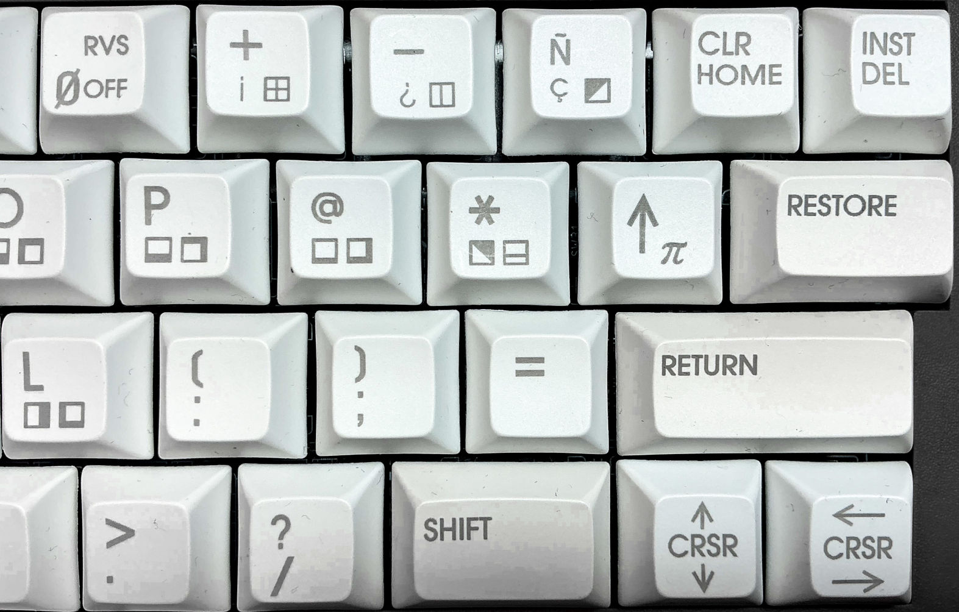
Keycaps/pictures/0339_-_spanish.JPG
