svenpetersen1965/C64-Keyboard/Keycaps/pictures/4339_-_Laser_marking_tray.jpg

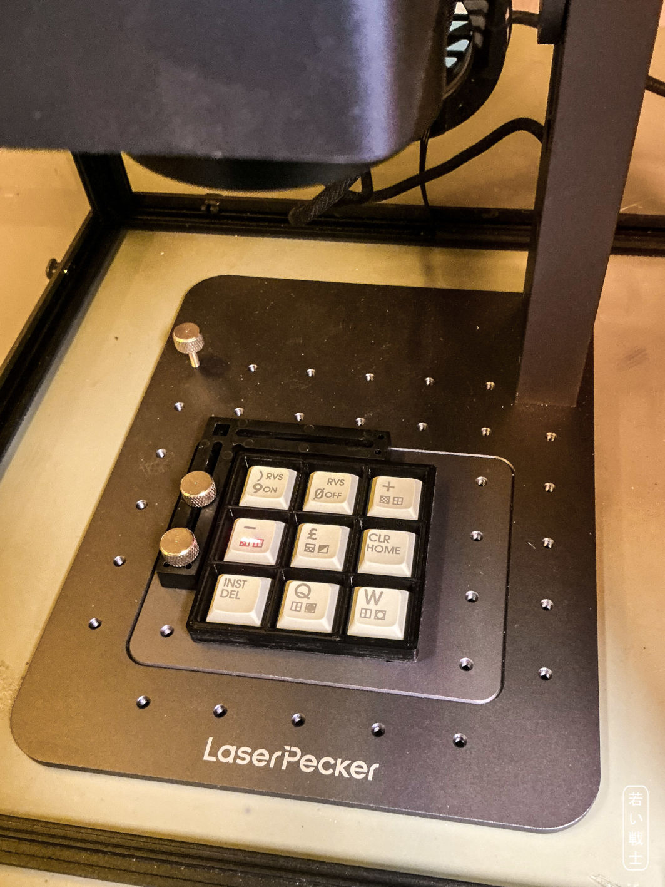
Keycaps/pictures/4339_-_Laser_marking_tray.jpg
