svenpetersen1965/C64-Keyboard/Keycaps/pictures/4645_-_UV-decals.JPG

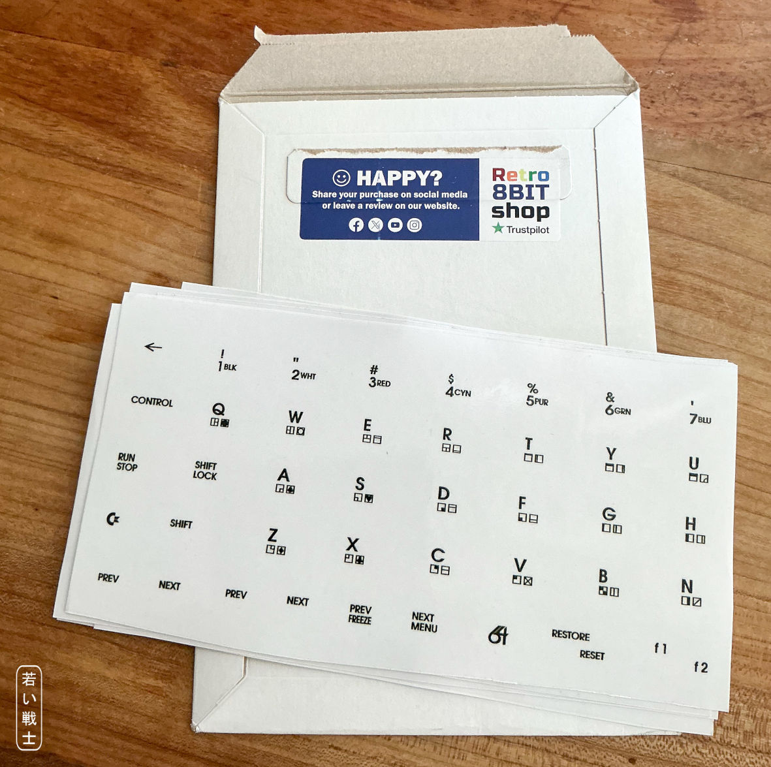
Keycaps/pictures/4645_-_UV-decals.JPG
