svenpetersen1965/C64-Keyboard/Keycaps/pictures/4649_-_UV_decals_application_tools.JPG

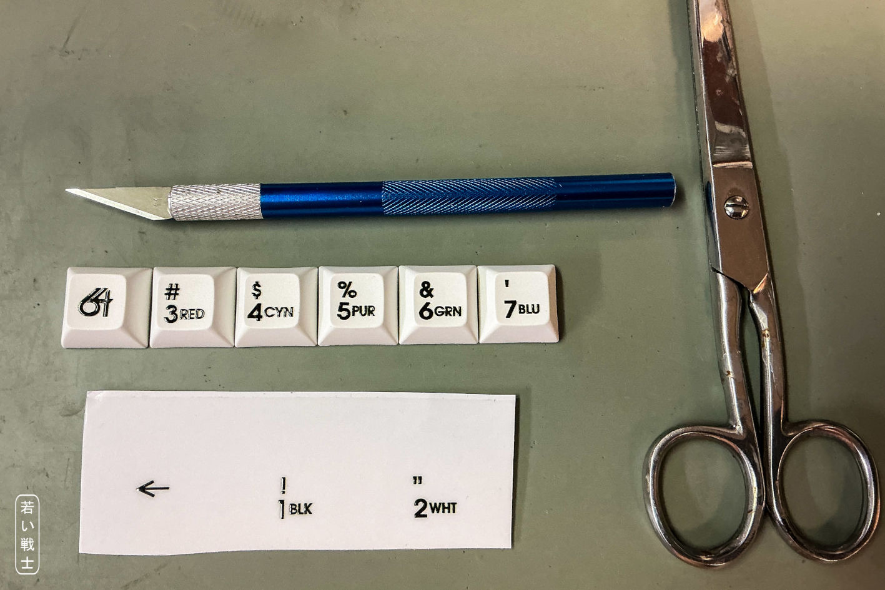
Keycaps/pictures/4649_-_UV_decals_application_tools.JPG
