svenpetersen1965/C64-Keyboard/Keycaps/pictures/4667_-_UV_decals_keycap_set.JPG

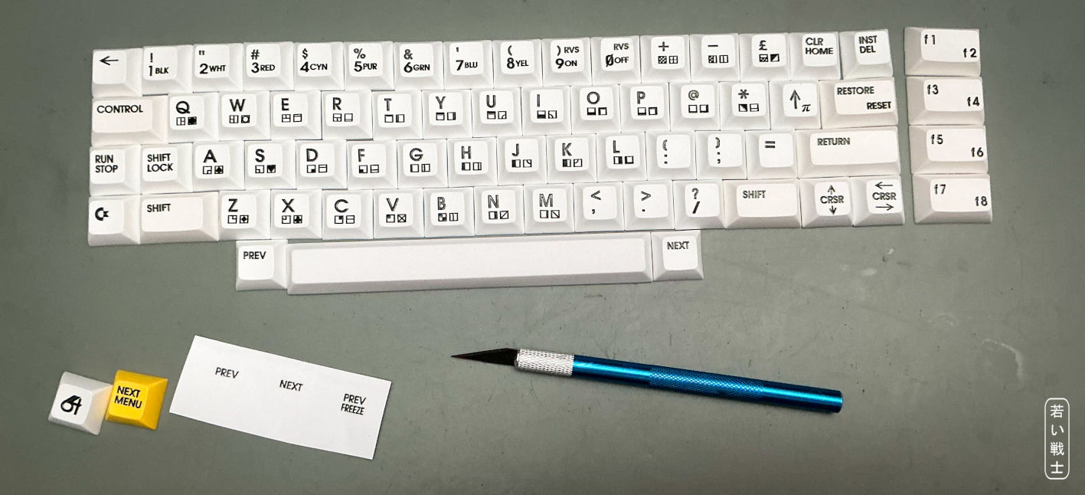
Keycaps/pictures/4667_-_UV_decals_keycap_set.JPG
