svenpetersen1965/C64-Keyboard/Keycaps/pictures/4779_-_white_UV_decals.JPG

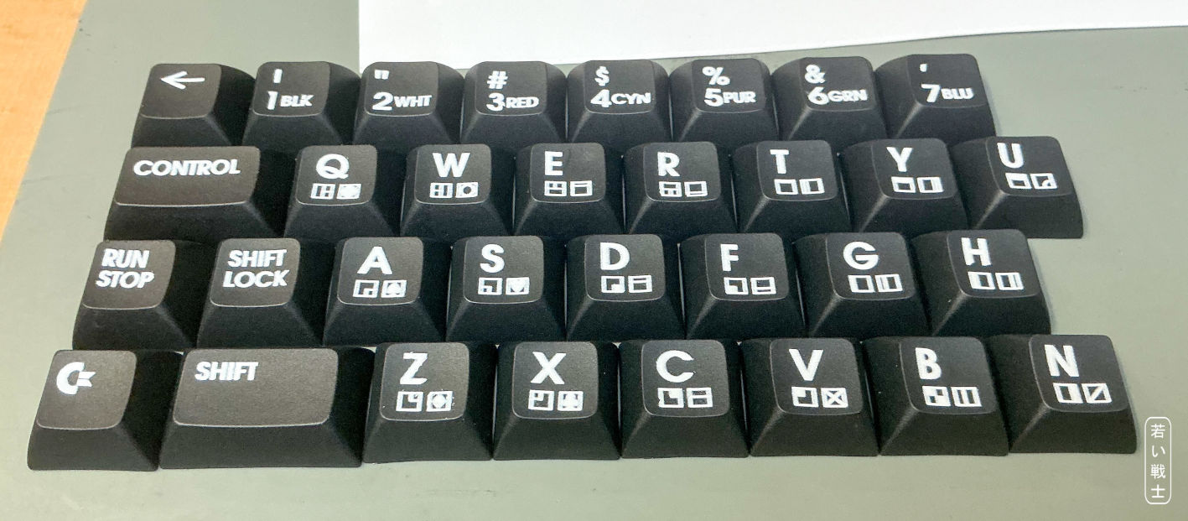
Keycaps/pictures/4779_-_white_UV_decals.JPG
