svenpetersen1965/C64-Keyboard/Keycaps/pictures/4784_-_all_all_black_keyboard.JPG

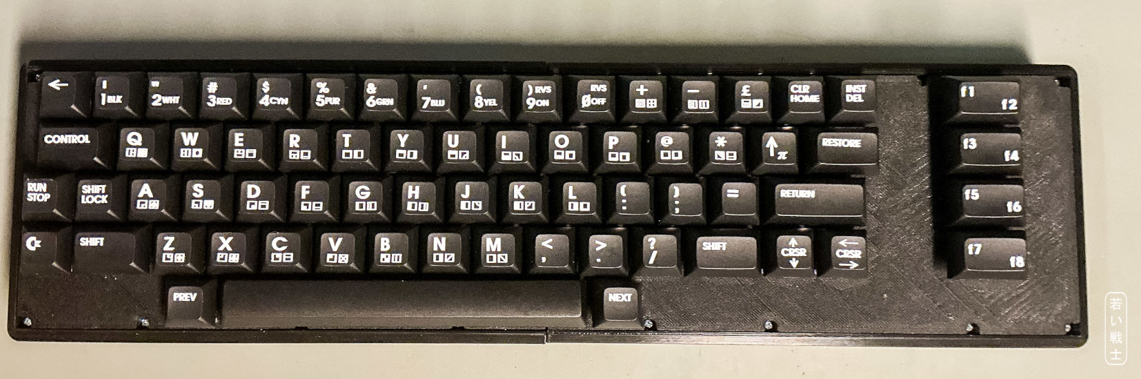
Keycaps/pictures/4784_-_all_all_black_keyboard.JPG
