svenpetersen1965/C64-Keyboard/Keycaps/pictures/4918_-_USB_keyb_original_keycaps.JPG

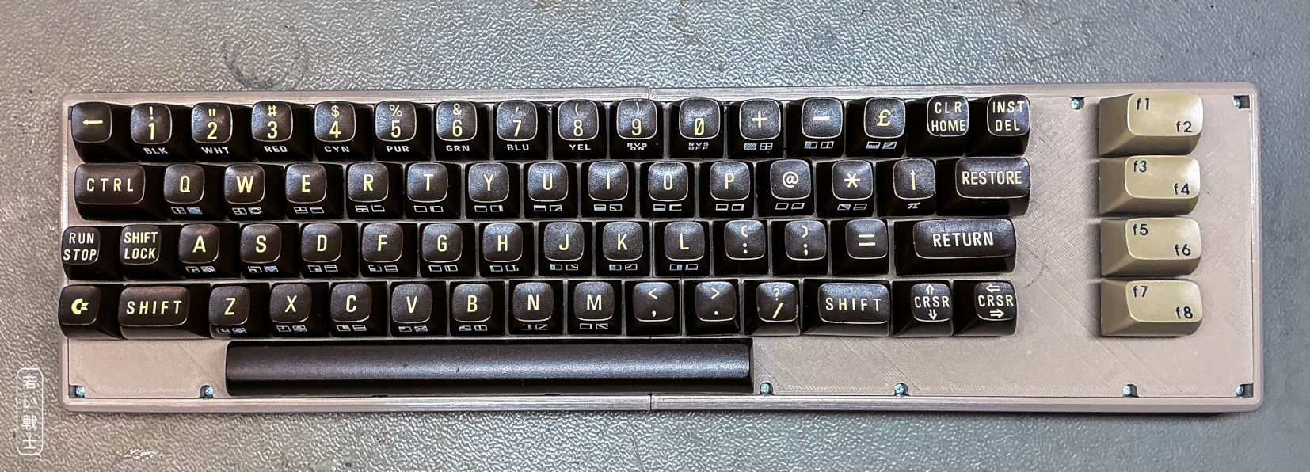
Keycaps/pictures/4918_-_USB_keyb_original_keycaps.JPG
