svenpetersen1965/C64-Keyboard/Keycaps/pictures/4963_-_laser_colors.jpg

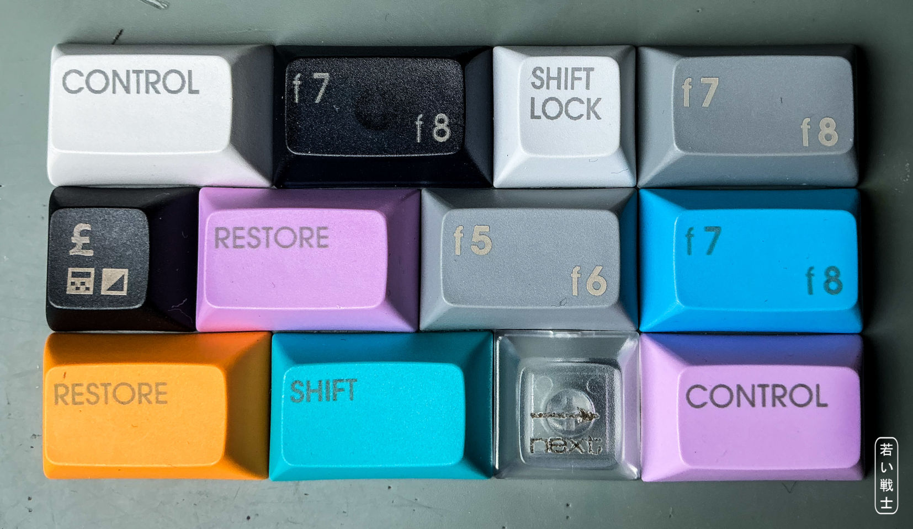
Keycaps/pictures/4963_-_laser_colors.jpg
