svenpetersen1965/C64-Keyboard/Keycaps/pictures/5132_-_engraved_keycap.JPG

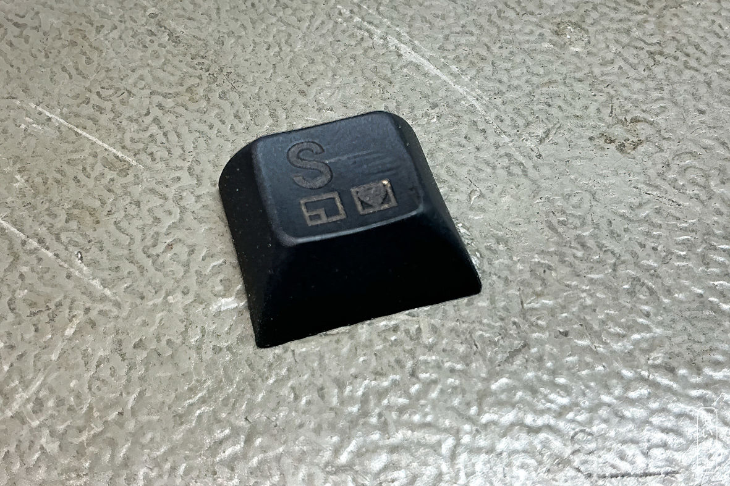
Keycaps/pictures/5132_-_engraved_keycap.JPG
