svenpetersen1965/C64-Keyboard/Keycaps/pictures/5200_-_filled_legends_rotary_tool.JPG

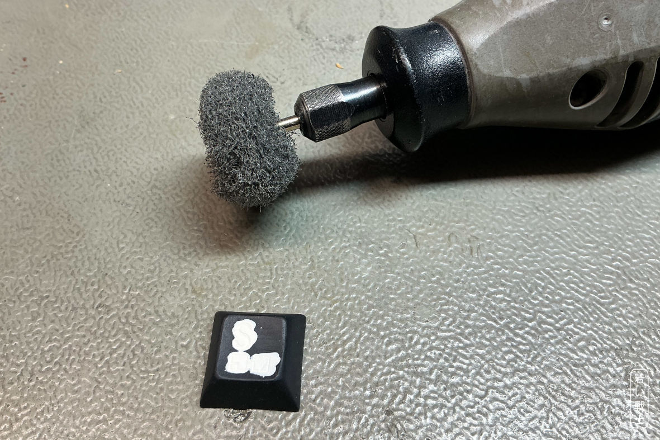
Keycaps/pictures/5200_-_filled_legends_rotary_tool.JPG
