svenpetersen1965/C64-Keyboard/Keycaps/pictures/5201_-_polished_filled_keycap.JPG

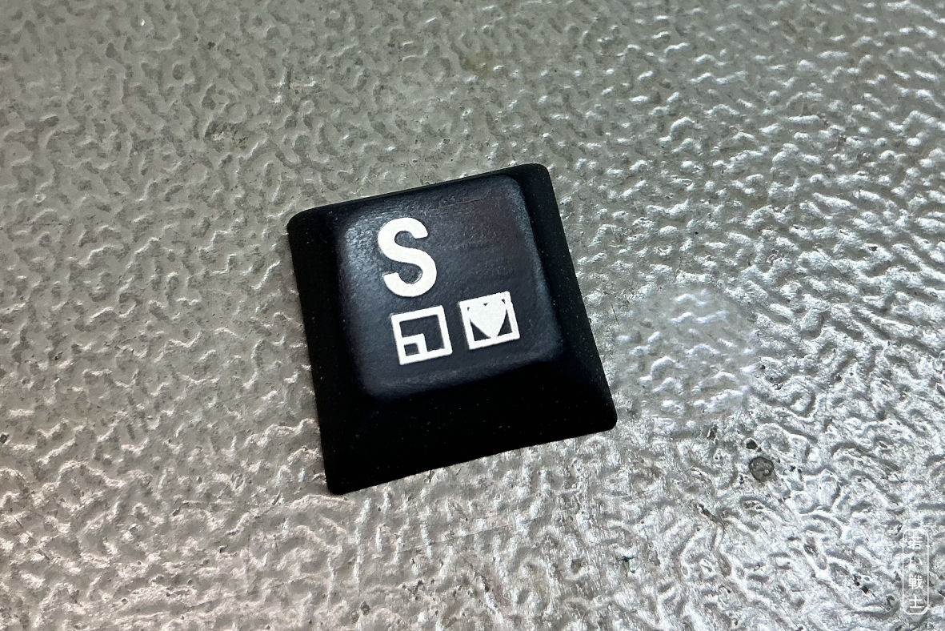
Keycaps/pictures/5201_-_polished_filled_keycap.JPG
