svenpetersen1965/C64-Keyboard/Keycaps/pictures/5218_-_Keycap_adapters.JPG

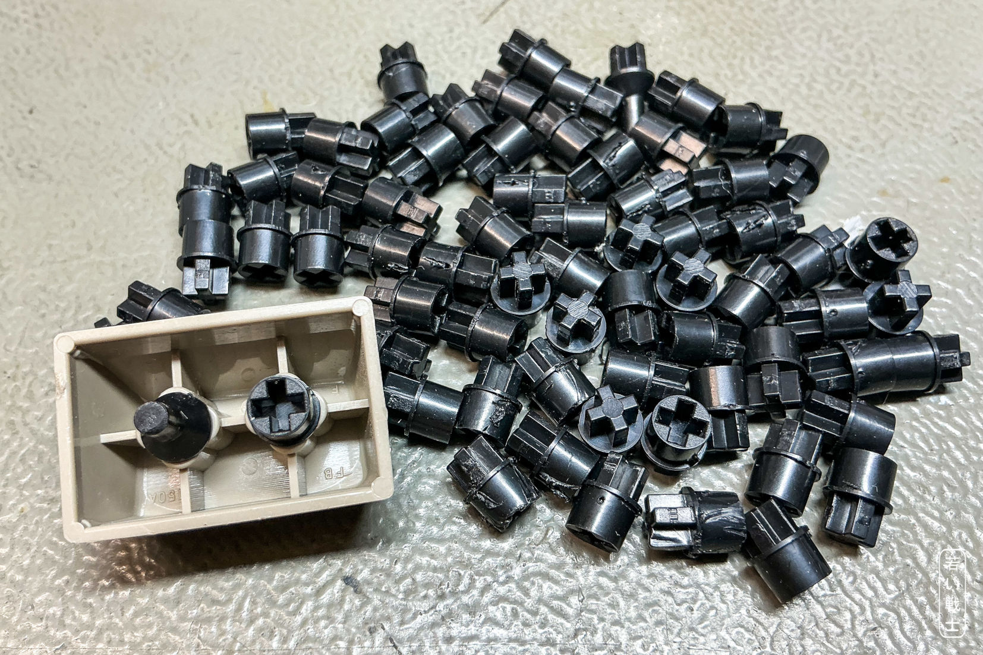
Keycaps/pictures/5218_-_Keycap_adapters.JPG
