svenpetersen1965/C64-Keyboard/Keycaps/pictures/5257_-_DyeSub_cutting.JPG

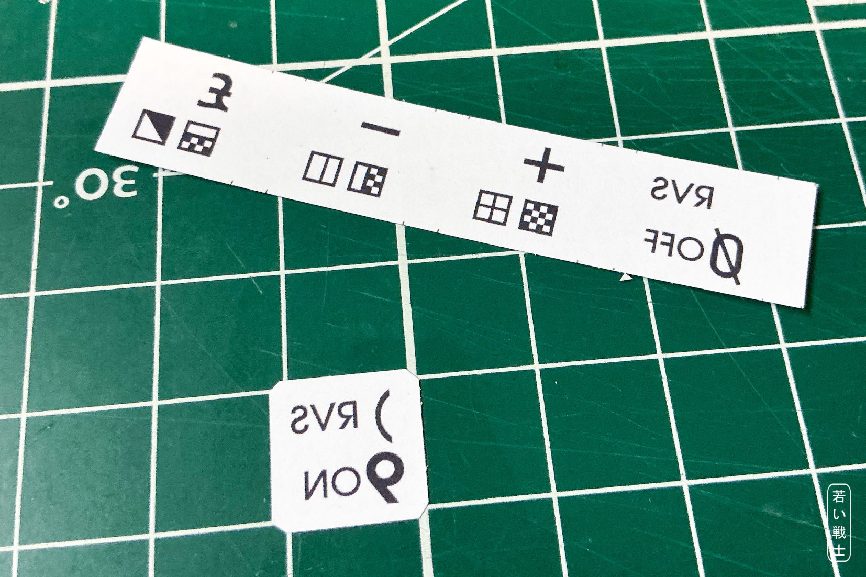
Keycaps/pictures/5257_-_DyeSub_cutting.JPG
