svenpetersen1965/C64-Keyboard/Keycaps/pictures/5258_-_DyeSub_paper_on_tape.JPG

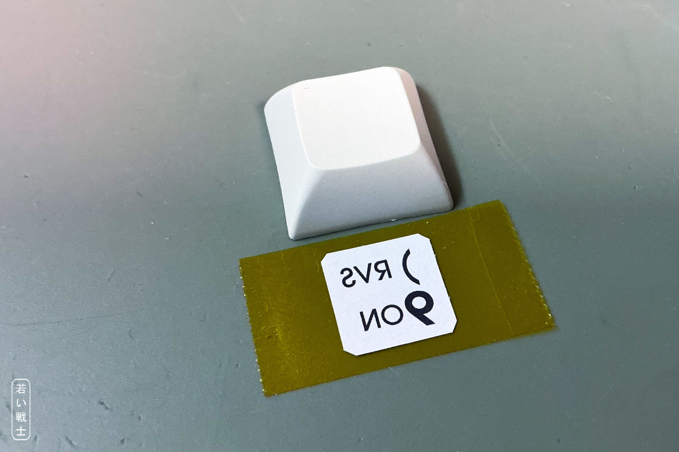
Keycaps/pictures/5258_-_DyeSub_paper_on_tape.JPG
