svenpetersen1965/C64-Keyboard/Keycaps/pictures/5259_-_DyeSub_Tape_on_keycap.JPG

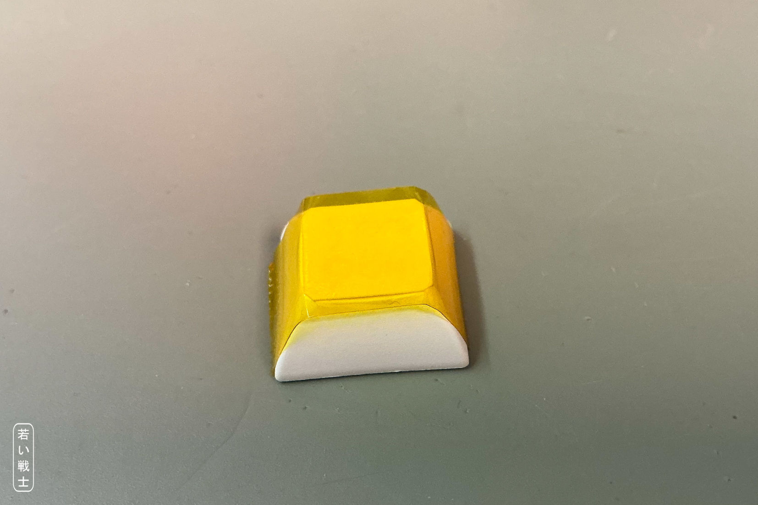
Keycaps/pictures/5259_-_DyeSub_Tape_on_keycap.JPG
