svenpetersen1965/C64-Keyboard/Keycaps/pictures/5260_-_DyeSub_finished.JPG

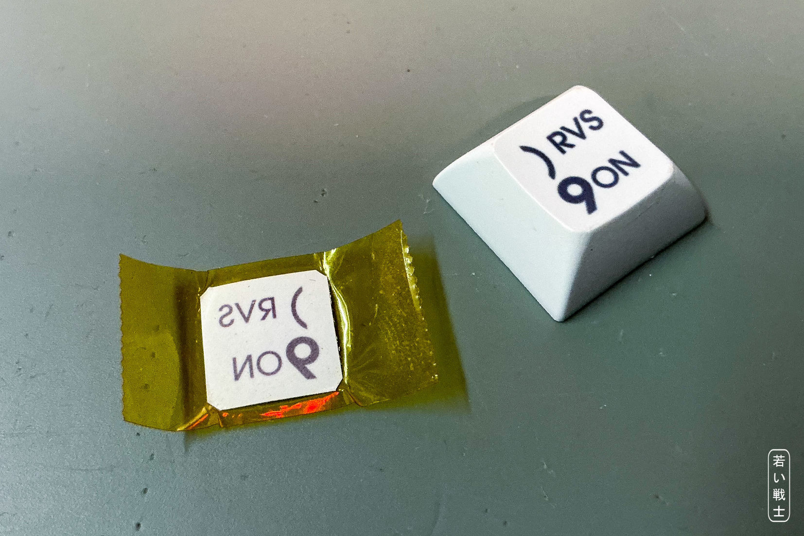
Keycaps/pictures/5260_-_DyeSub_finished.JPG
