svenpetersen1965/C64-Keyboard/Keycaps/pictures/5277_-_DyeSub_Aluminium_Foil_Mold.JPG

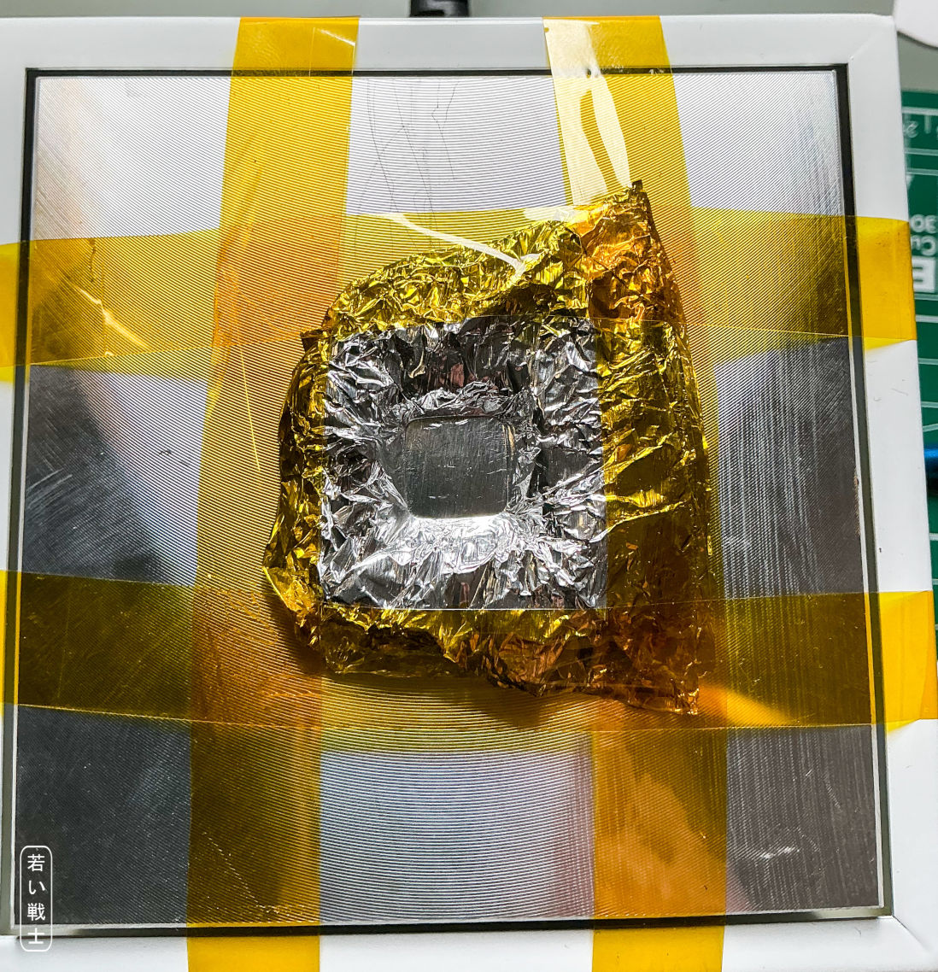
Keycaps/pictures/5277_-_DyeSub_Aluminium_Foil_Mold.JPG
