svenpetersen1965/C64-Keyboard/Keycaps/pictures/5301_-_DyeSub_pressing.JPG

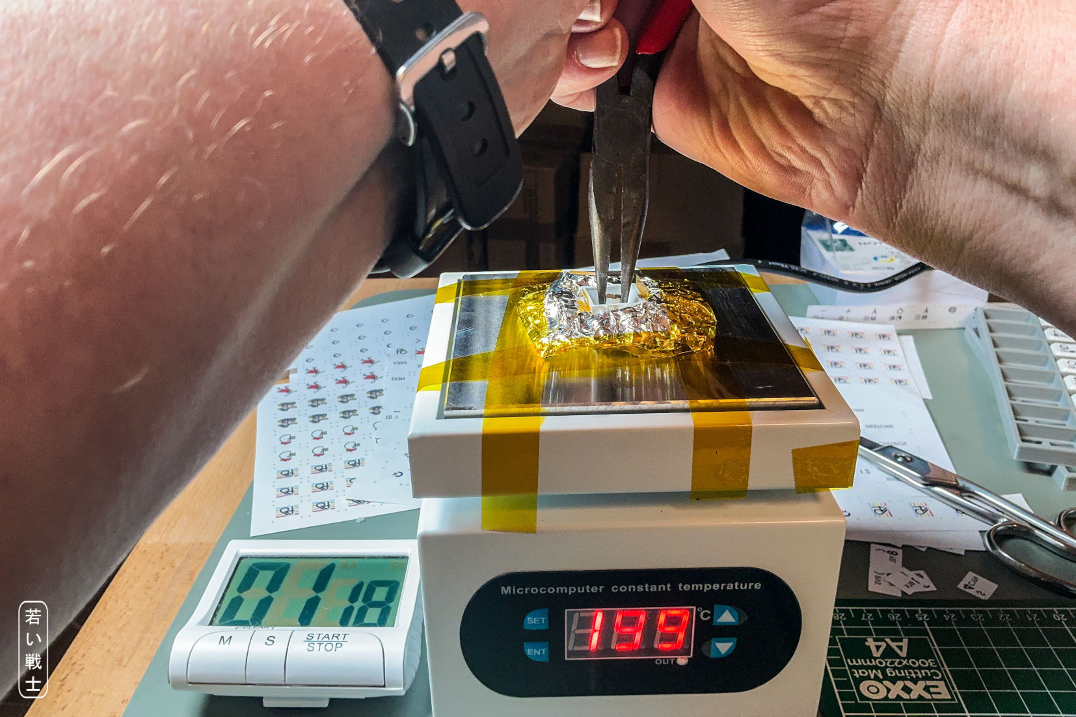
Keycaps/pictures/5301_-_DyeSub_pressing.JPG
