svenpetersen1965/C64-Keyboard/Keycaps/pictures/5308_-_transfer_paper_residues.JPG

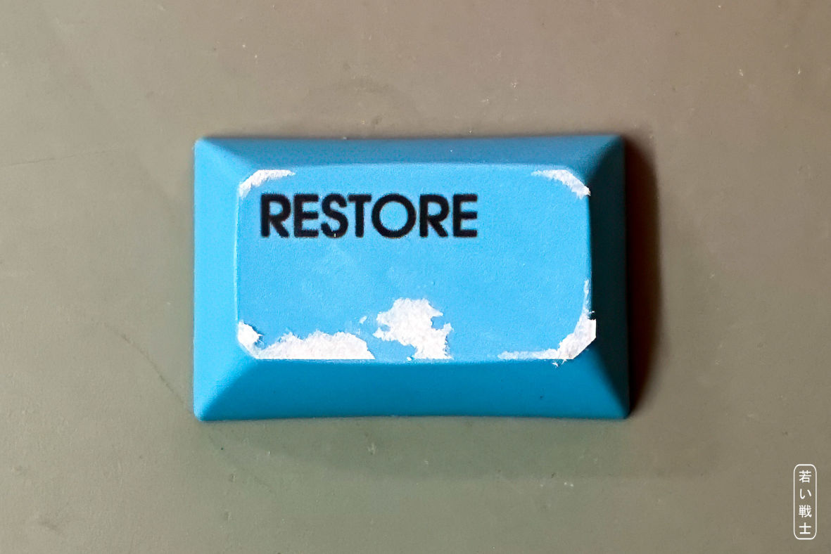
Keycaps/pictures/5308_-_transfer_paper_residues.JPG
