svenpetersen1965/C64-Keyboard/Keycaps/pictures/5314_-_DyeSub_Keycaps_in_IPA.JPG

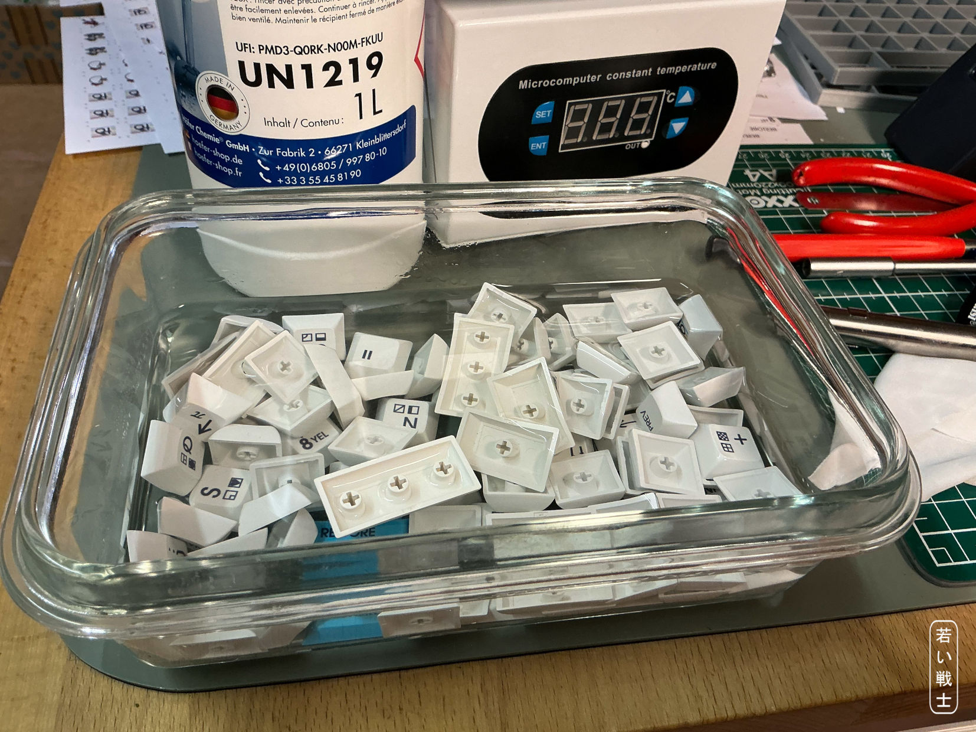
Keycaps/pictures/5314_-_DyeSub_Keycaps_in_IPA.JPG
