svenpetersen1965/C64-Keyboard/Keycaps/pictures/5317_-_DyeSub_Hot_soapy_water.JPG

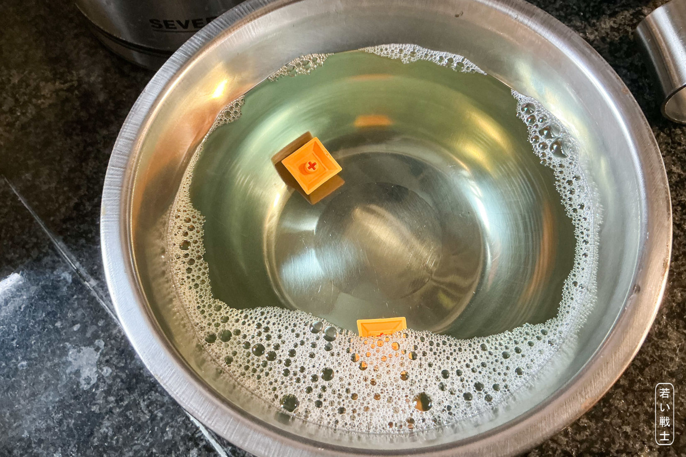
Keycaps/pictures/5317_-_DyeSub_Hot_soapy_water.JPG
