svenpetersen1965/C64-Keyboard/Keycaps/pictures/5320_-_DyeSub_Work_bench.JPG

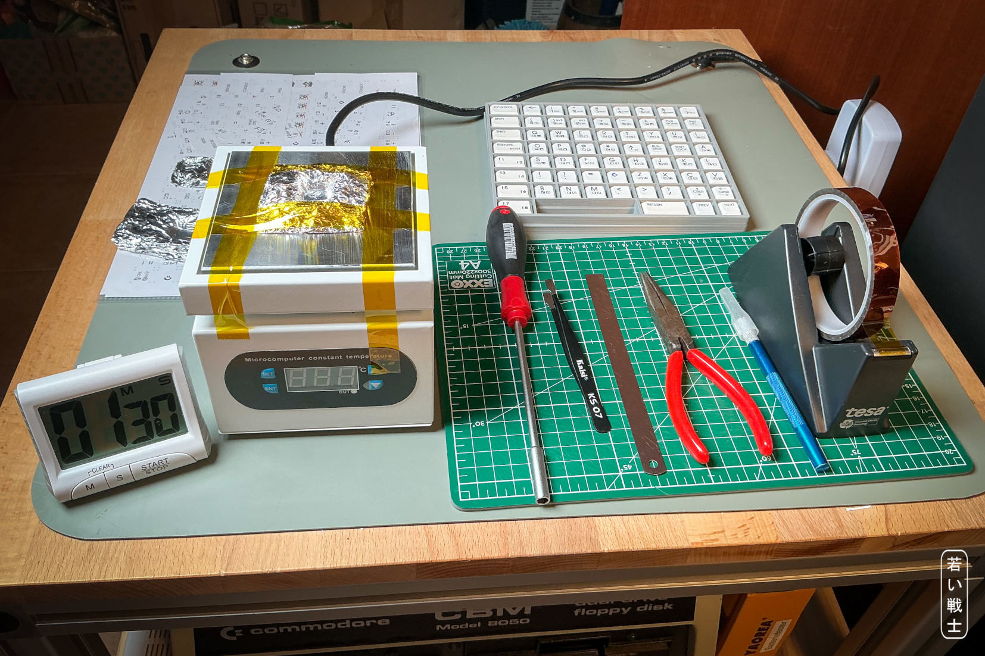
Keycaps/pictures/5320_-_DyeSub_Work_bench.JPG
