svenpetersen1965/C64-Keyboard/Keycaps/pictures/5922_-_Fiber_Laser_Keycaps.JPG

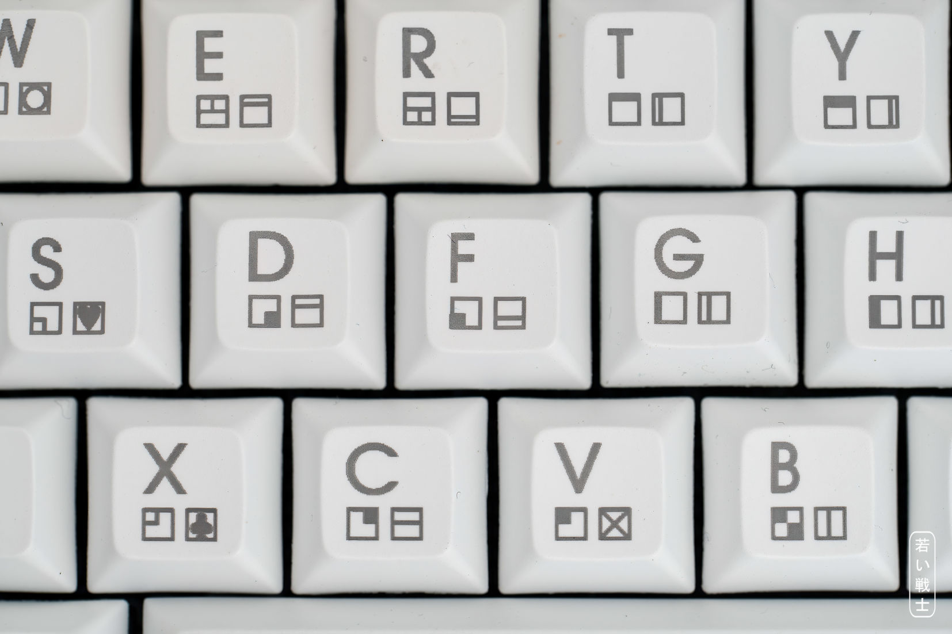
Keycaps/pictures/5922_-_Fiber_Laser_Keycaps.JPG
