svenpetersen1965/C64-Keyboard/Keycaps/pictures/5930_-_black_UV-decals_Keycaps.JPG

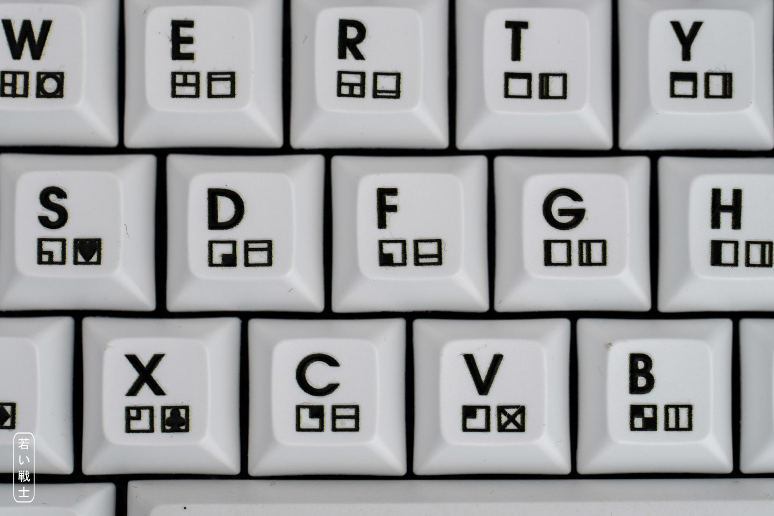
Keycaps/pictures/5930_-_black_UV-decals_Keycaps.JPG
