svenpetersen1965/C64-Keyboard/Keycaps/pictures/5945_-_laser_marking_colored_keycaps.JPG

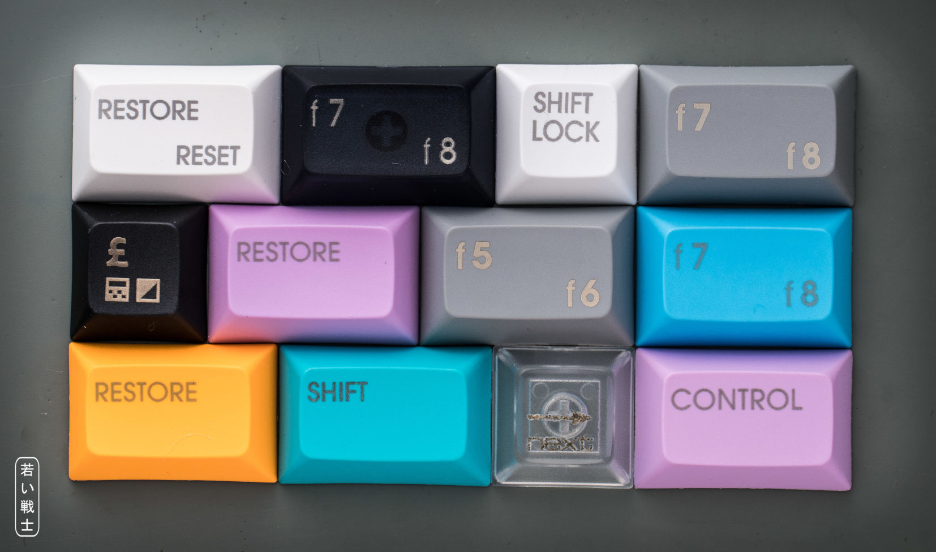
Keycaps/pictures/5945_-_laser_marking_colored_keycaps.JPG
