svenpetersen1965/C64-Keyboard/Keycaps/pictures/5947_-_UV-decal_M.JPG

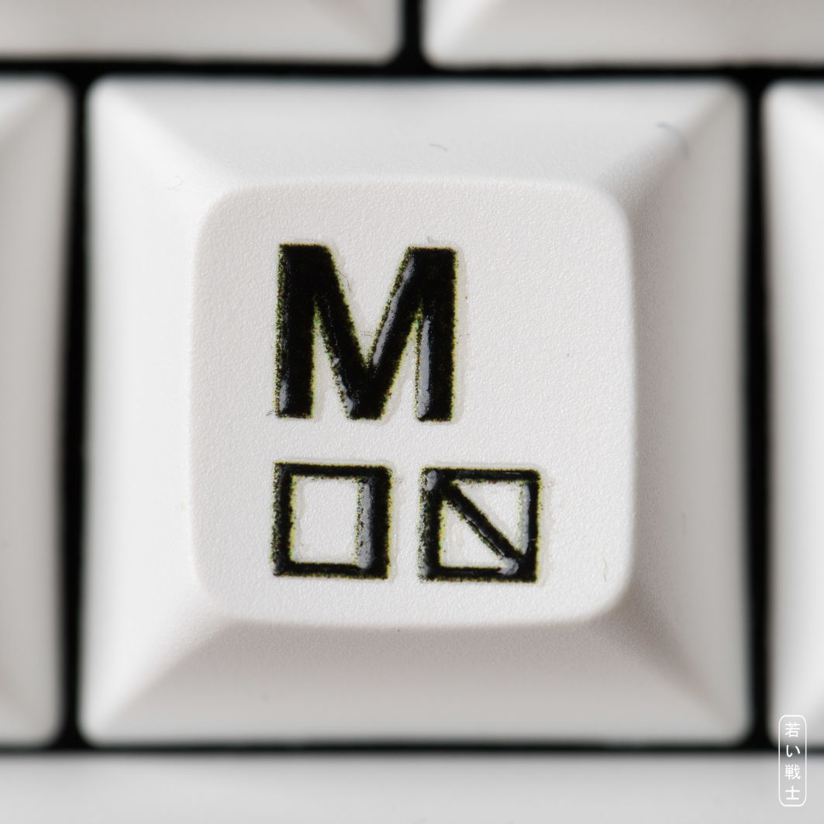
Keycaps/pictures/5947_-_UV-decal_M.JPG
