svenpetersen1965/C64-Keyboard/Keycaps/pictures/5952_-_laser_G.JPG

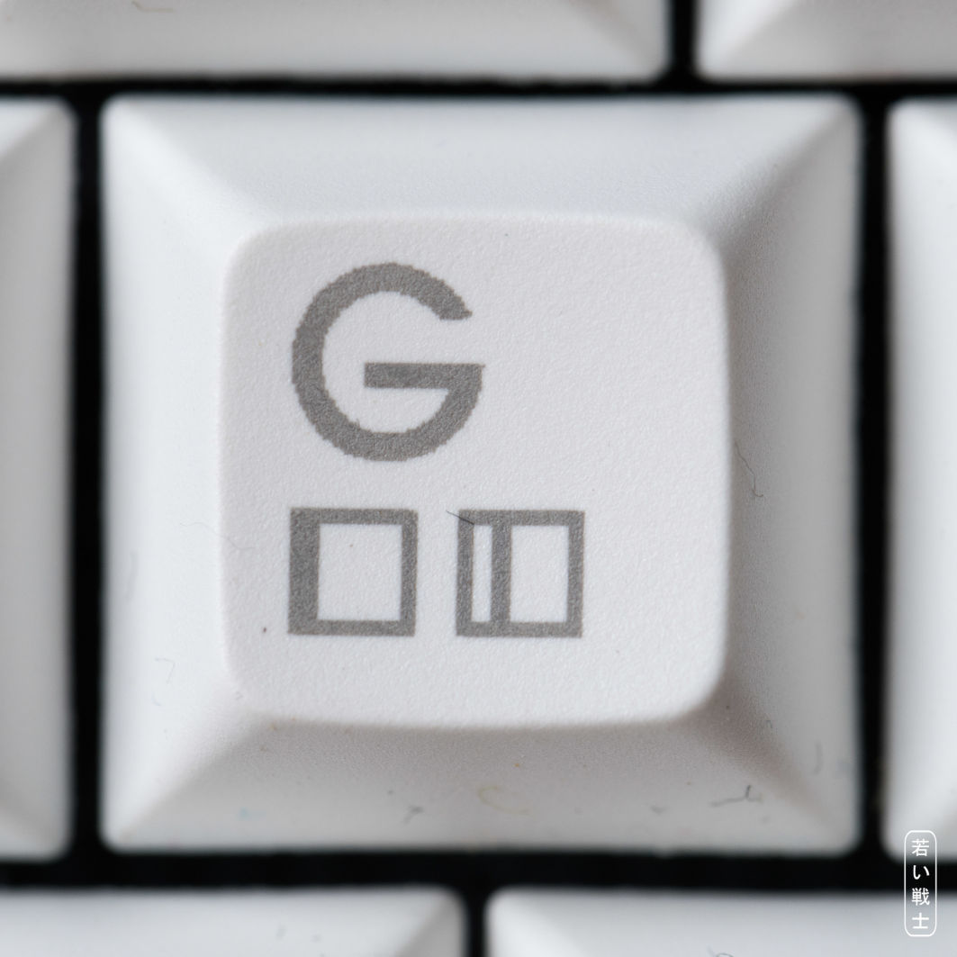
Keycaps/pictures/5952_-_laser_G.JPG
