svenpetersen1965/C64-Keyboard/Keycaps/pictures/5961_-_UV-decal_+.JPG

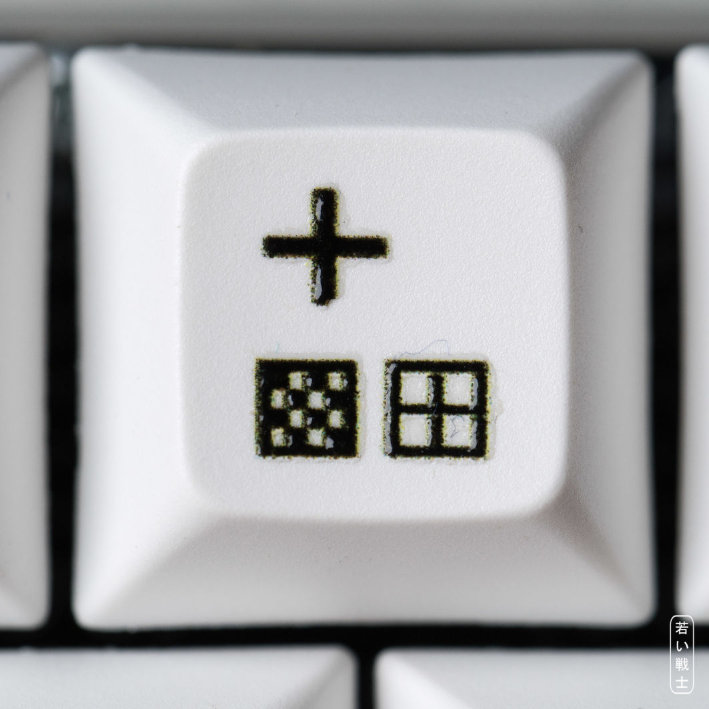
Keycaps/pictures/5961_-_UV-decal_+.JPG
