svenpetersen1965/C64-Keyboard/Keycaps/pictures/5962_-_UV-decal_Q.JPG

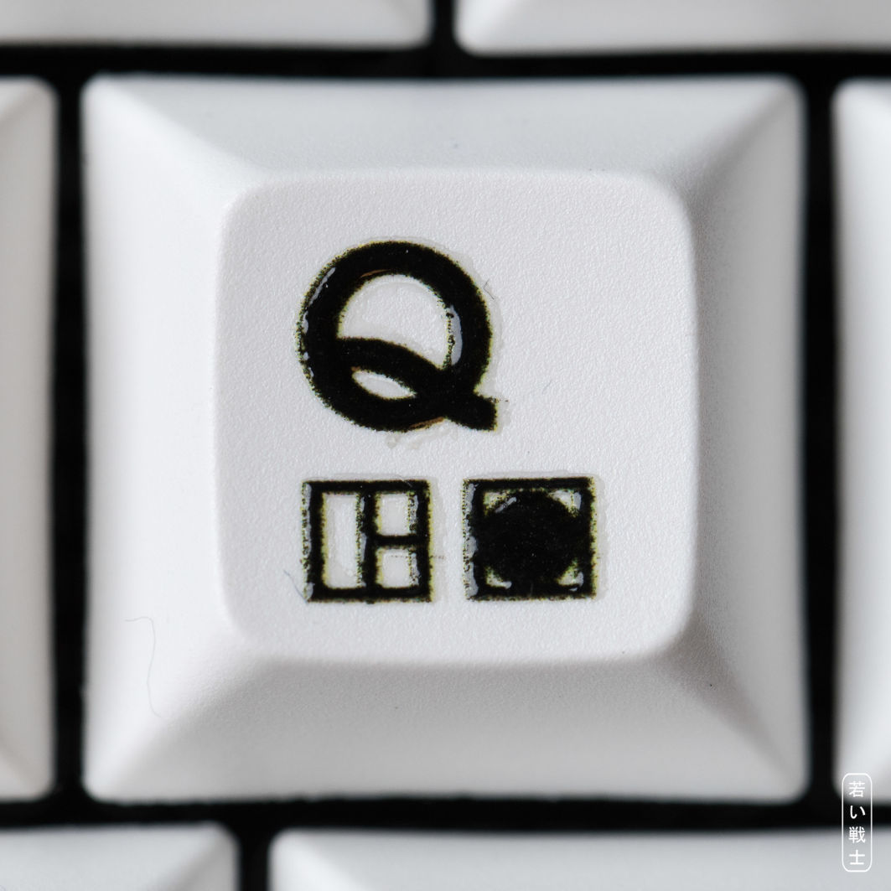
Keycaps/pictures/5962_-_UV-decal_Q.JPG
