svenpetersen1965/C64-Keyboard/Keycaps/pictures/5964_-_UV-decal_white_M.JPG

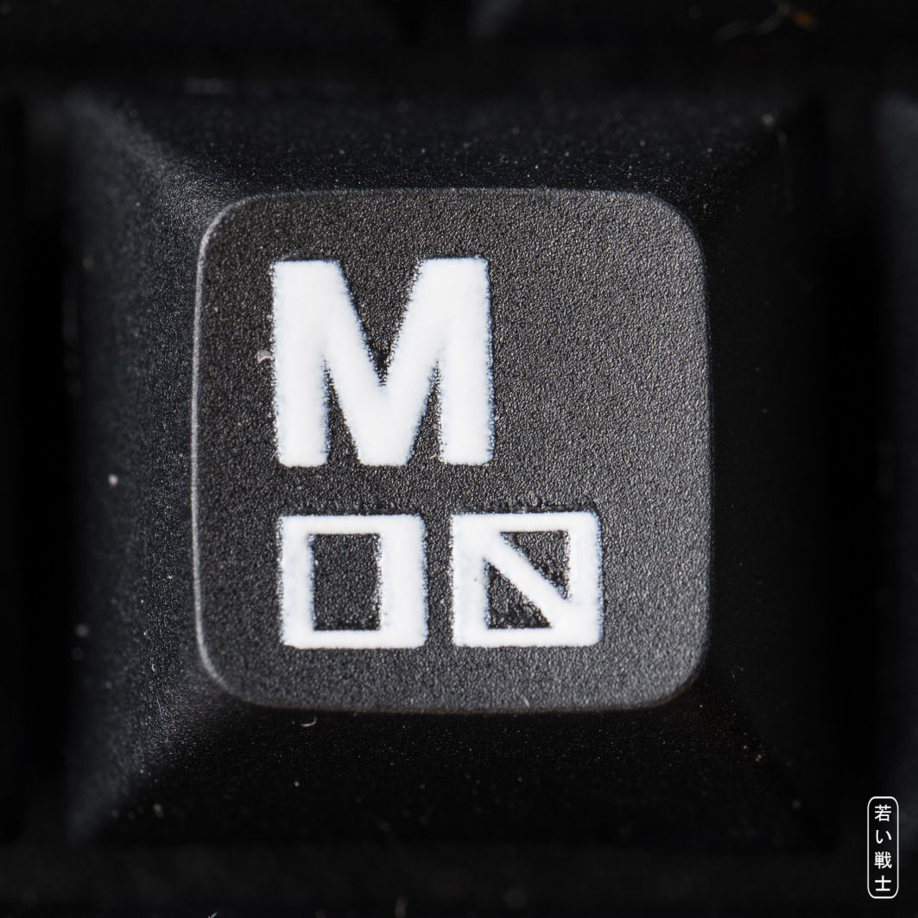
Keycaps/pictures/5964_-_UV-decal_white_M.JPG
