svenpetersen1965/C64-Keyboard/Keycaps/pictures/5966_-_UV-decal_white_SHIFT.JPG

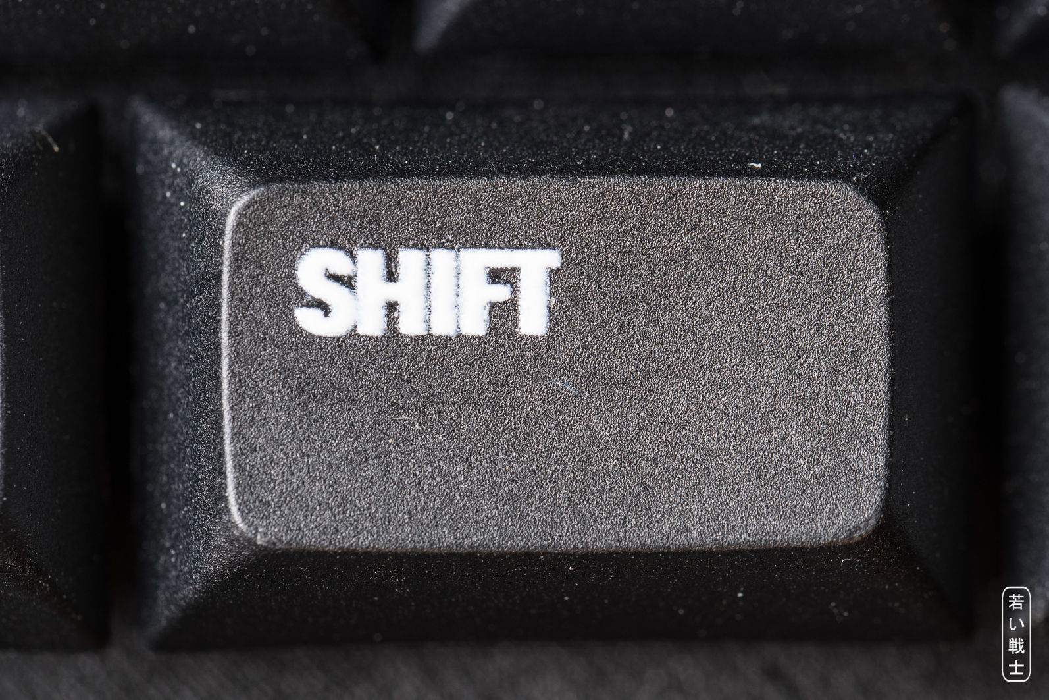
Keycaps/pictures/5966_-_UV-decal_white_SHIFT.JPG
