svenpetersen1965/C64-Keyboard/Keycaps/pictures/5968_-_UV-decal_white_+.JPG

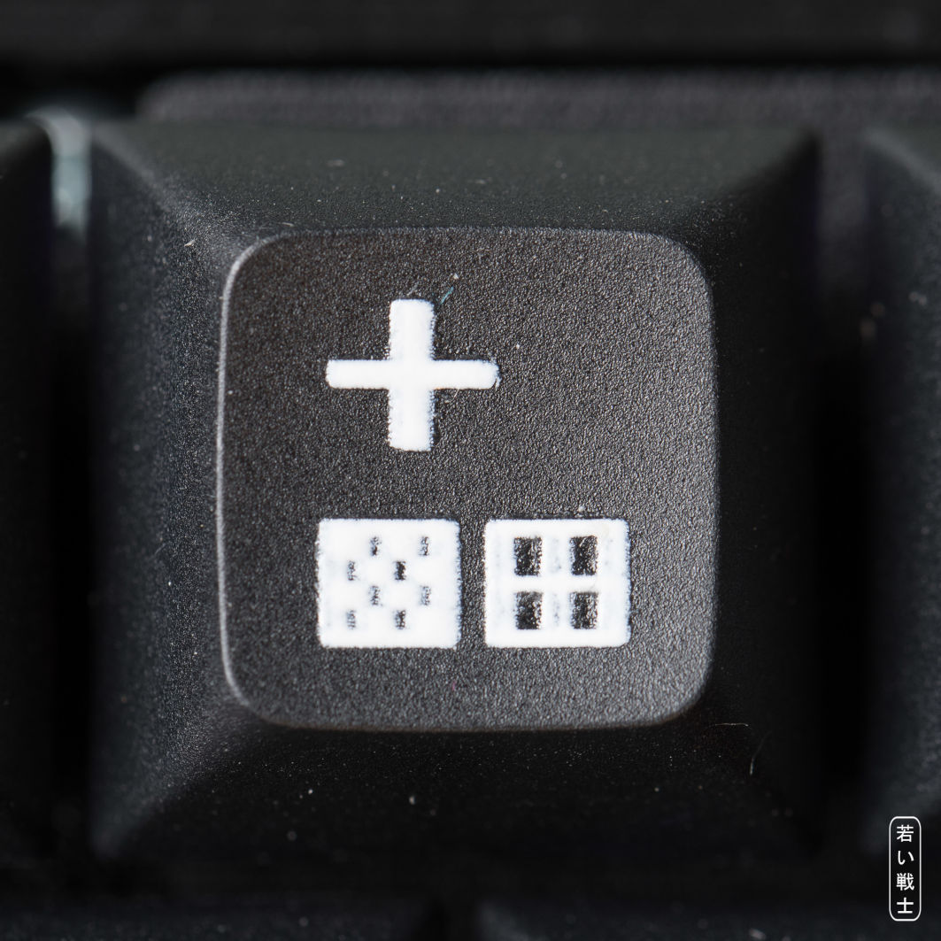
Keycaps/pictures/5968_-_UV-decal_white_+.JPG
