svenpetersen1965/C64-Keyboard/Keycaps/pictures/5970_-_UV-decal_white_Q.JPG

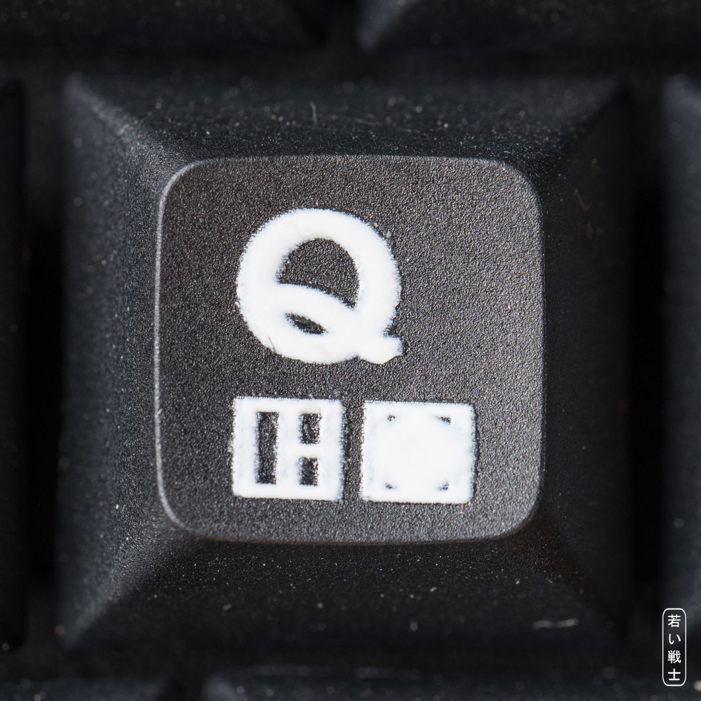
Keycaps/pictures/5970_-_UV-decal_white_Q.JPG
