svenpetersen1965/C64-Keyboard/Keycaps/pictures/5971_-_laser_M.JPG

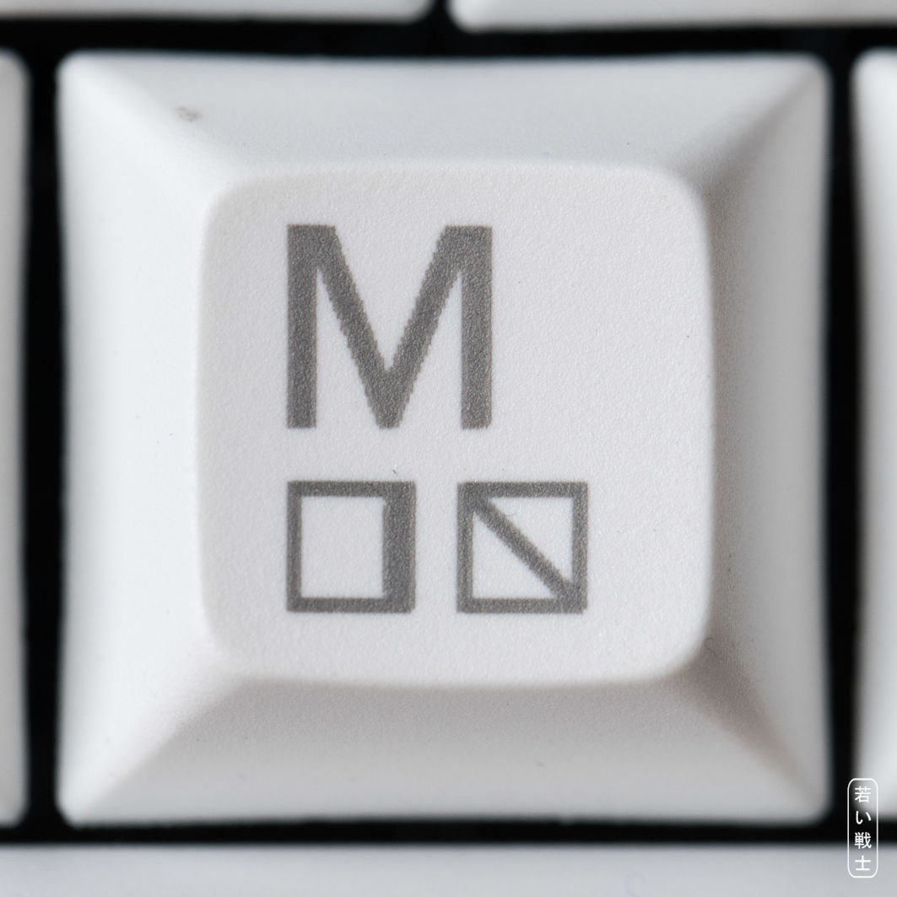
Keycaps/pictures/5971_-_laser_M.JPG
