svenpetersen1965/C64-Keyboard/Keycaps/pictures/5974_-_laser_+.JPG

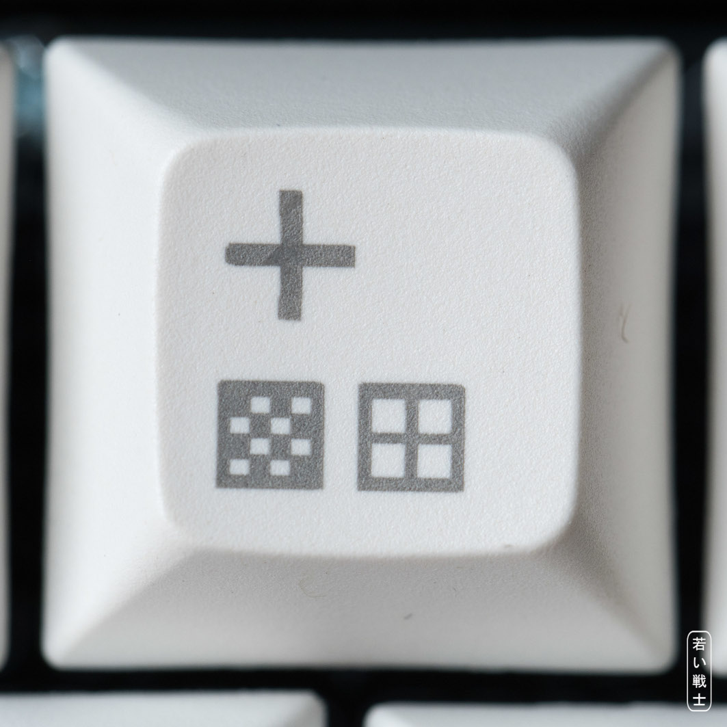
Keycaps/pictures/5974_-_laser_+.JPG
