svenpetersen1965/C64-Keyboard/Keycaps/pictures/5976_-_laser_Q.JPG

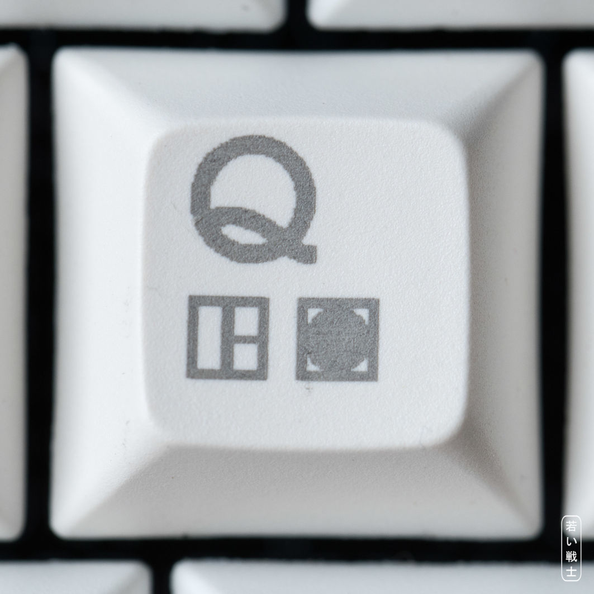
Keycaps/pictures/5976_-_laser_Q.JPG
