svenpetersen1965/C64-Keyboard/Keycaps/pictures/5977_-_laser_SHIFT.JPG

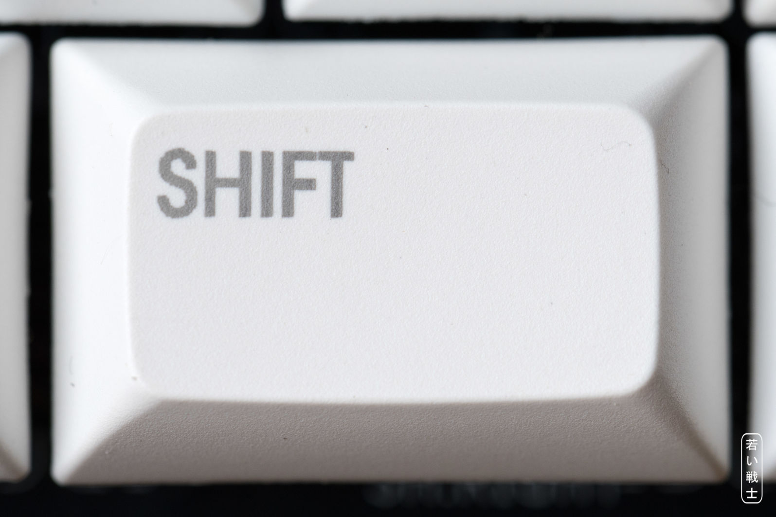
Keycaps/pictures/5977_-_laser_SHIFT.JPG
