svenpetersen1965/C64-Keyboard/Keycaps/pictures/5981_-_UV-decal_SHIFT.JPG

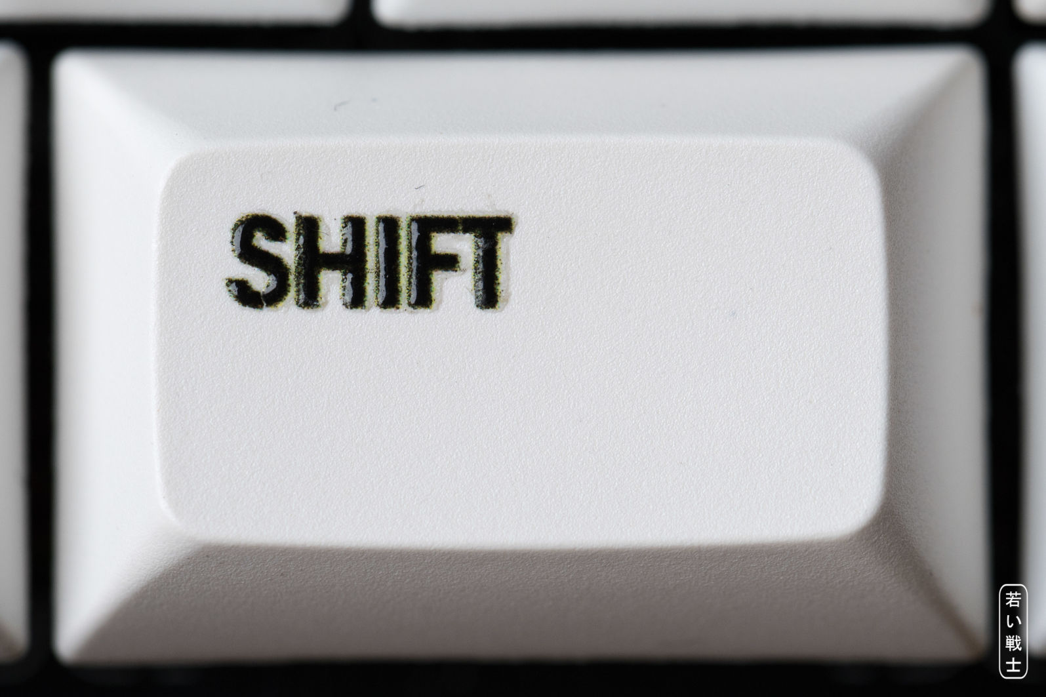
Keycaps/pictures/5981_-_UV-decal_SHIFT.JPG
