svenpetersen1965/C64-Keyboard/Keycaps/pictures/6025_-_DSA_keycap_G_profile.JPG

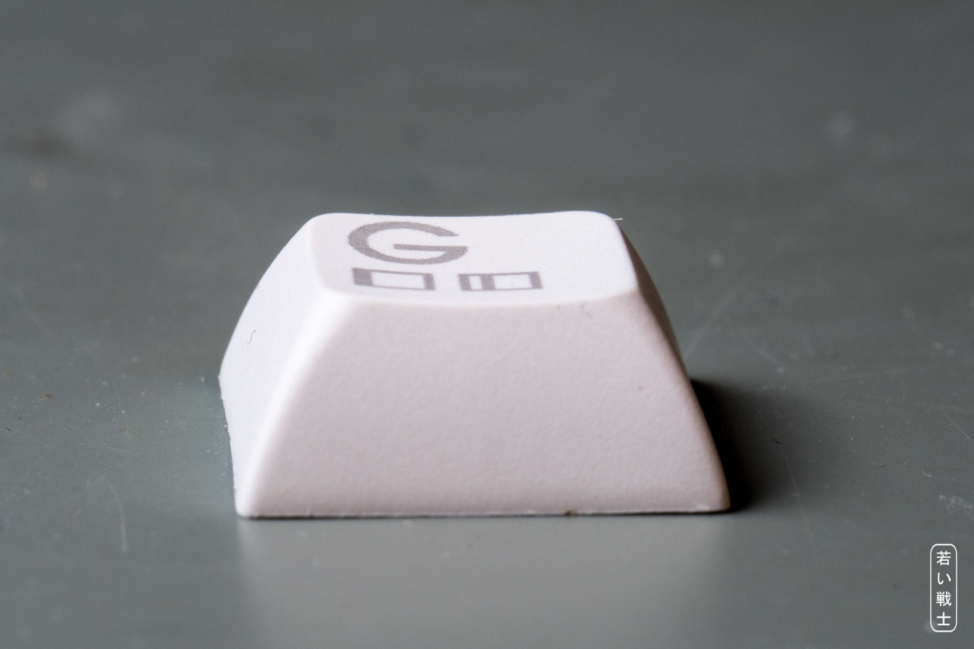
Keycaps/pictures/6025_-_DSA_keycap_G_profile.JPG
