svenpetersen1965/C64-Keyboard/Keycaps/pictures/6040_-_cleanroom_whipes.JPG

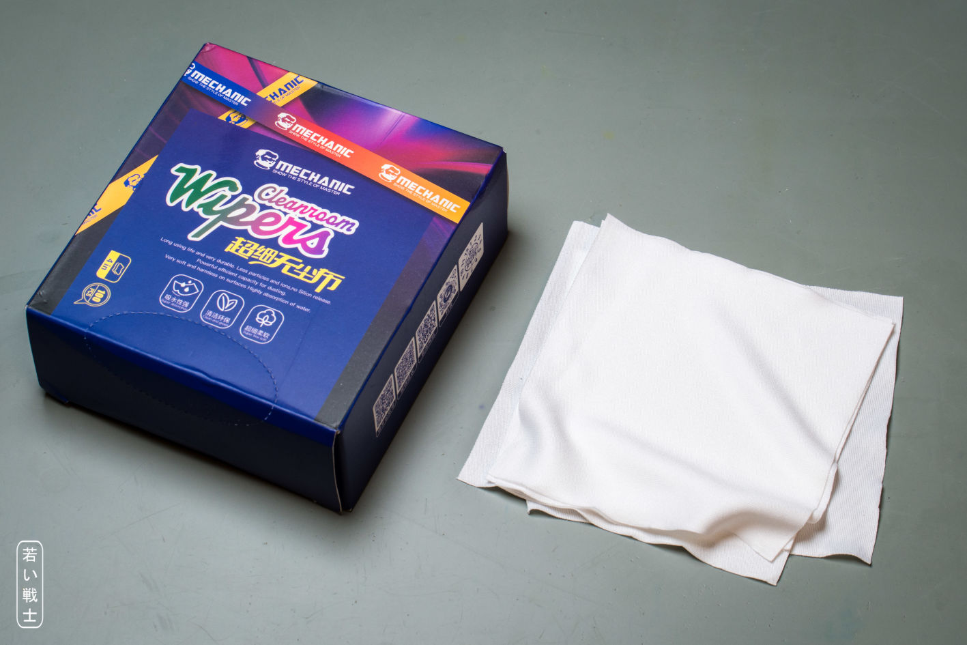
Keycaps/pictures/6040_-_cleanroom_whipes.JPG
