svenpetersen1965/C64-Keyboard/Keycaps/pictures/6083_-_pollished_filled_S.JPG

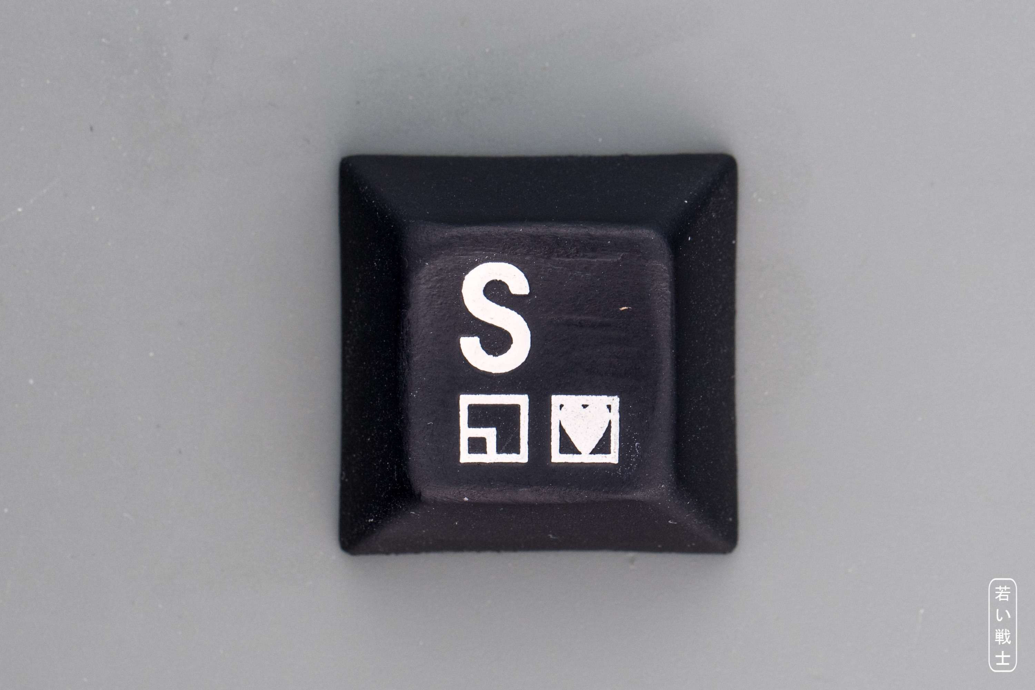
Keycaps/pictures/6083_-_pollished_filled_S.JPG
