svenpetersen1965/C64-Keyboard/Keycaps/pictures/6097_-_colored_keycaps.JPG

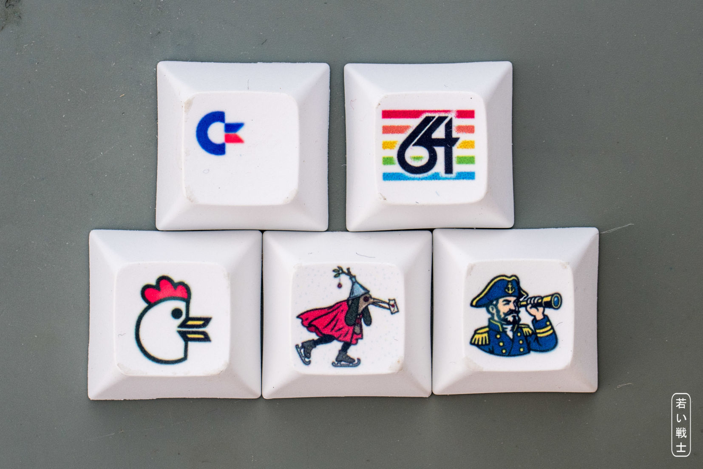
Keycaps/pictures/6097_-_colored_keycaps.JPG
