svenpetersen1965/C64-Keyboard/Keycaps/pictures/6099_-_F_J_Homing_keycaps.JPG

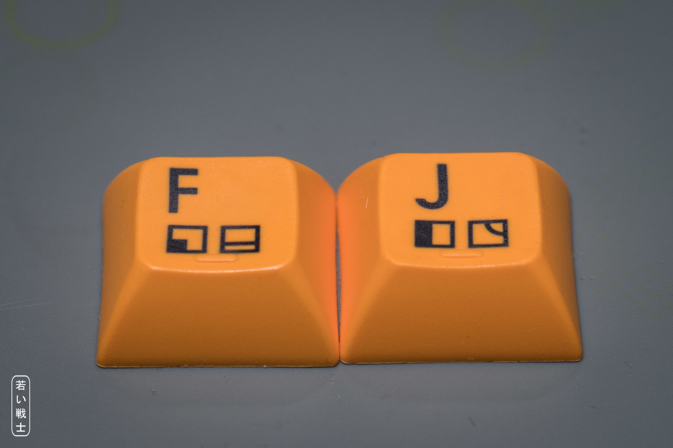
Keycaps/pictures/6099_-_F_J_Homing_keycaps.JPG
