svenpetersen1965/C64-Keyboard/Keycaps/pictures/6117_-_Dye_Sub_Keyboard_frontal.JPG

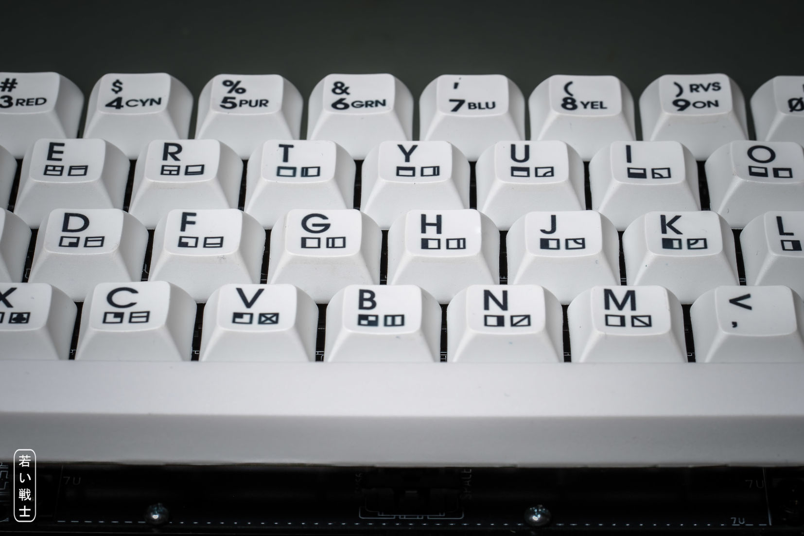
Keycaps/pictures/6117_-_Dye_Sub_Keyboard_frontal.JPG
