svenpetersen1965/C64-Keyboard/Keycaps/pictures/6123_-_Dye_Sublimation_Keycaps.JPG

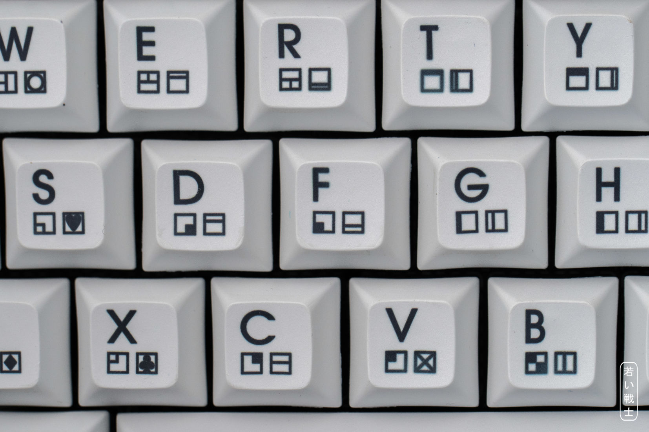
Keycaps/pictures/6123_-_Dye_Sublimation_Keycaps.JPG
