svenpetersen1965/C64-Keyboard/Keycaps/pictures/6125_-_DyeSub_M.JPG

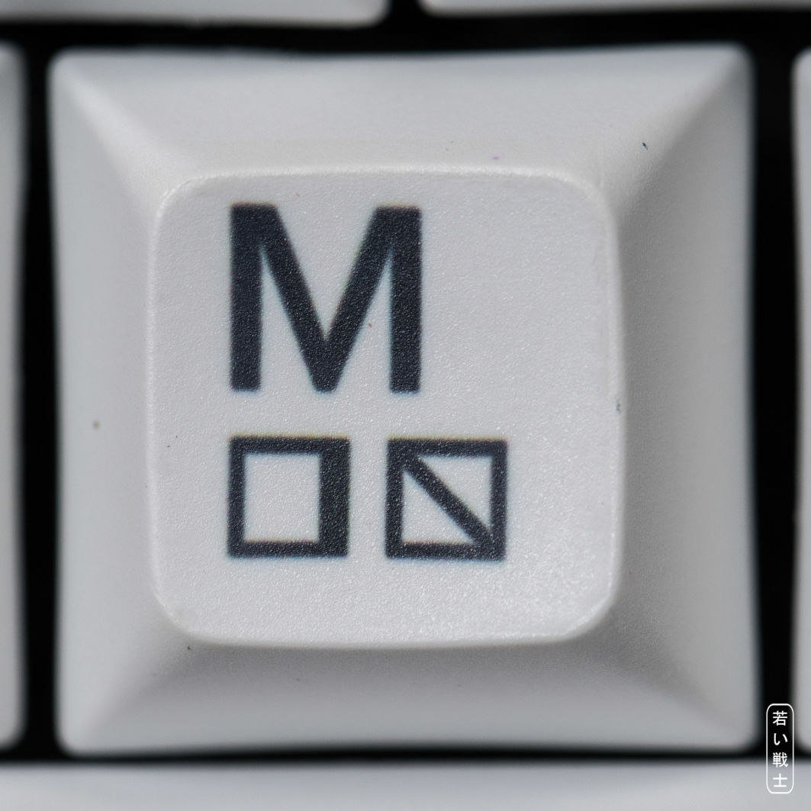
Keycaps/pictures/6125_-_DyeSub_M.JPG
