svenpetersen1965/C64-Keyboard/Keycaps/pictures/6133_-_DyeSub_Q.JPG

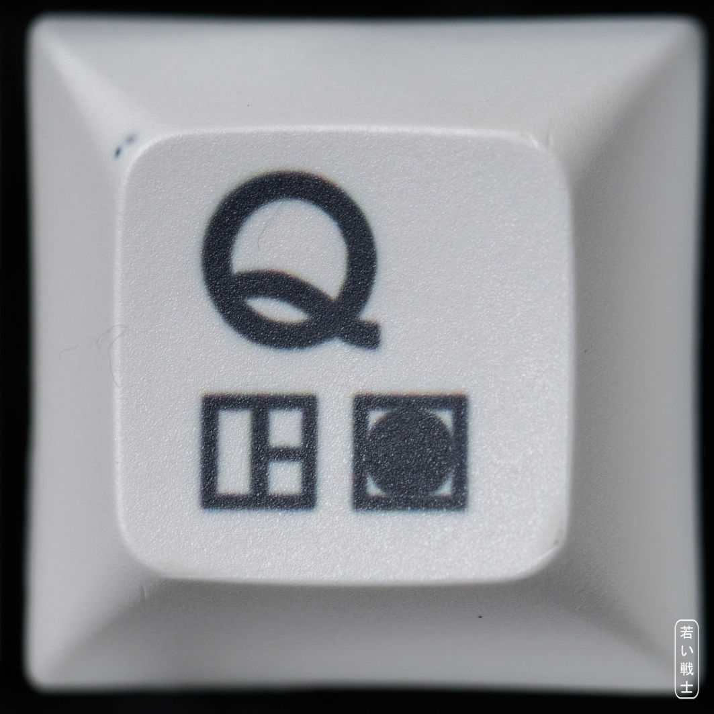
Keycaps/pictures/6133_-_DyeSub_Q.JPG
