svenpetersen1965/C64-Keyboard/Keycaps/pictures/6136_-_DyeSub_SHIFT.JPG

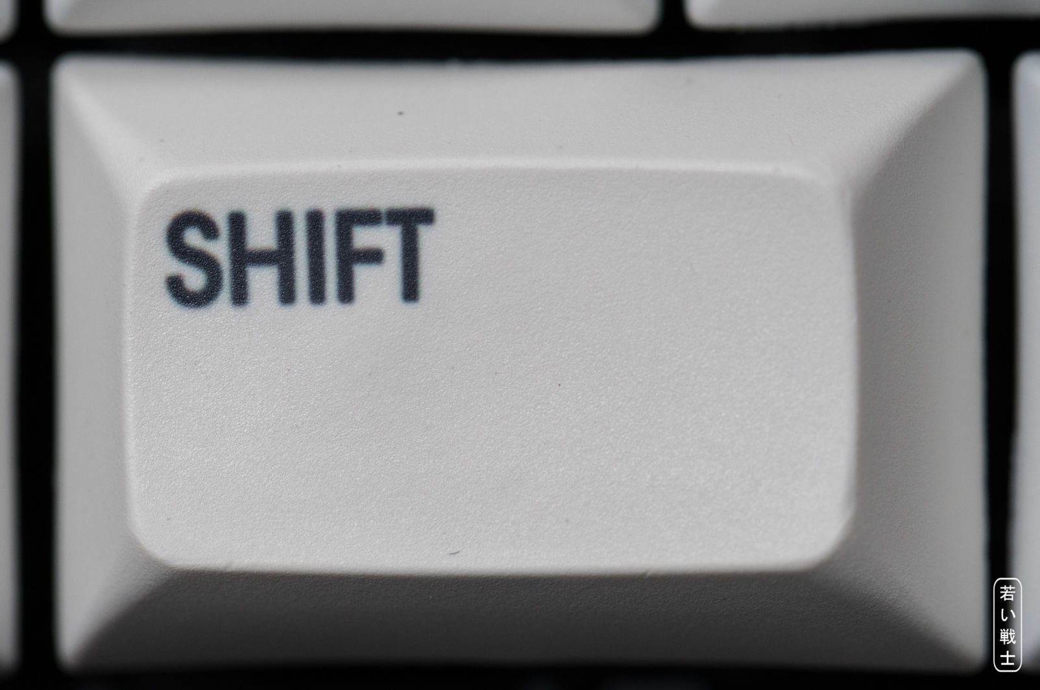
Keycaps/pictures/6136_-_DyeSub_SHIFT.JPG
