svenpetersen1965/C64-Keyboard/Keycaps/pictures/6142_-_DyeSub_Fails.JPG

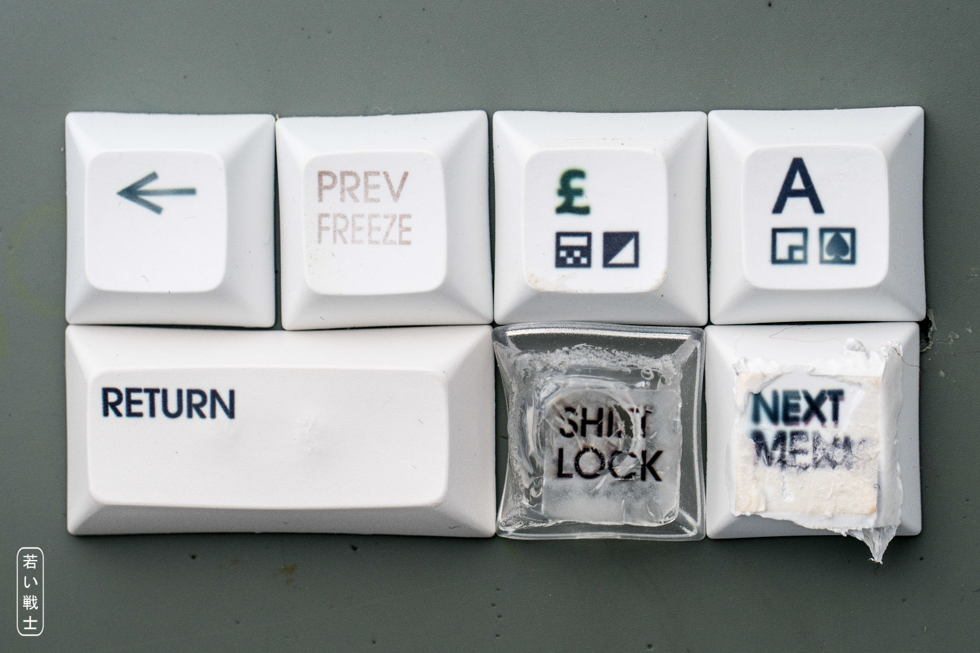
Keycaps/pictures/6142_-_DyeSub_Fails.JPG
