svenpetersen1965/C64-Keyboard/Keycaps/pictures/6144_-_DyeSub_colors.JPG

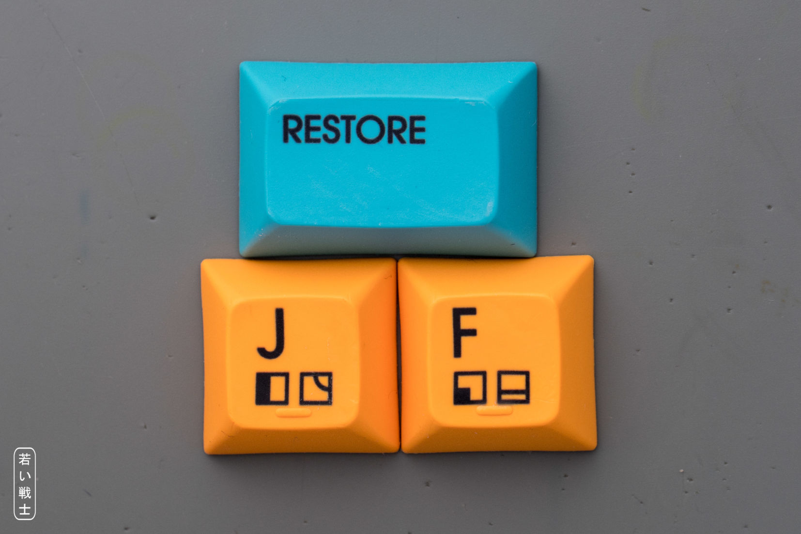
Keycaps/pictures/6144_-_DyeSub_colors.JPG
