svenpetersen1965/C64-Keyboard/Keycaps/pictures/6149_-_DyeSub_Fail_corners.JPG

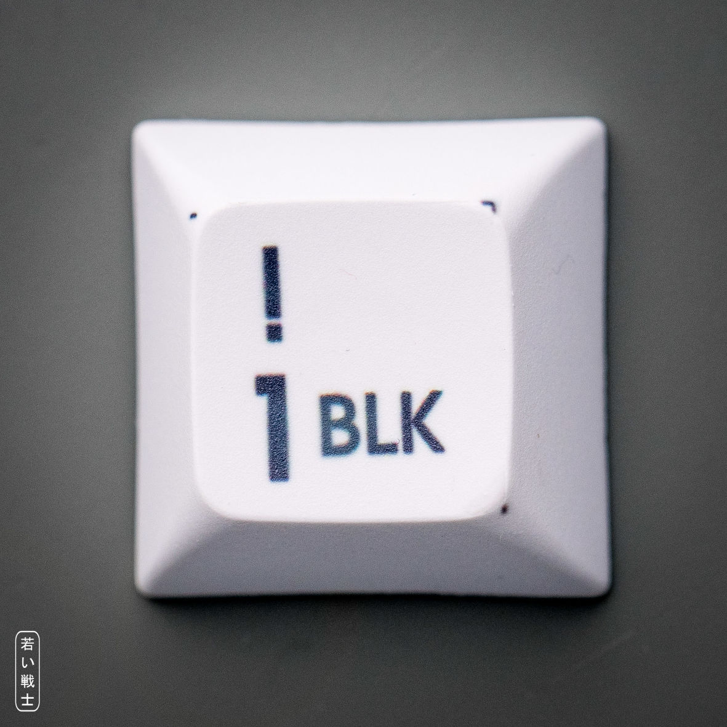
Keycaps/pictures/6149_-_DyeSub_Fail_corners.JPG
