svenpetersen1965/C64-Keyboard/Keycaps/pictures/9963_-_scanning_keycaps.JPG

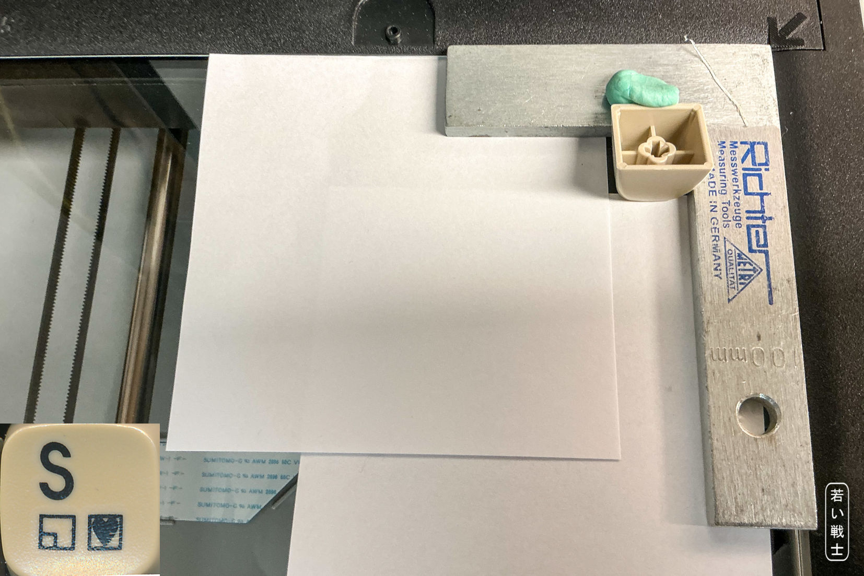
Keycaps/pictures/9963_-_scanning_keycaps.JPG
