svenpetersen1965/C64-Keyboard/Keycaps/pictures/DSA_keycaps_DyeSub_scaled_down.png

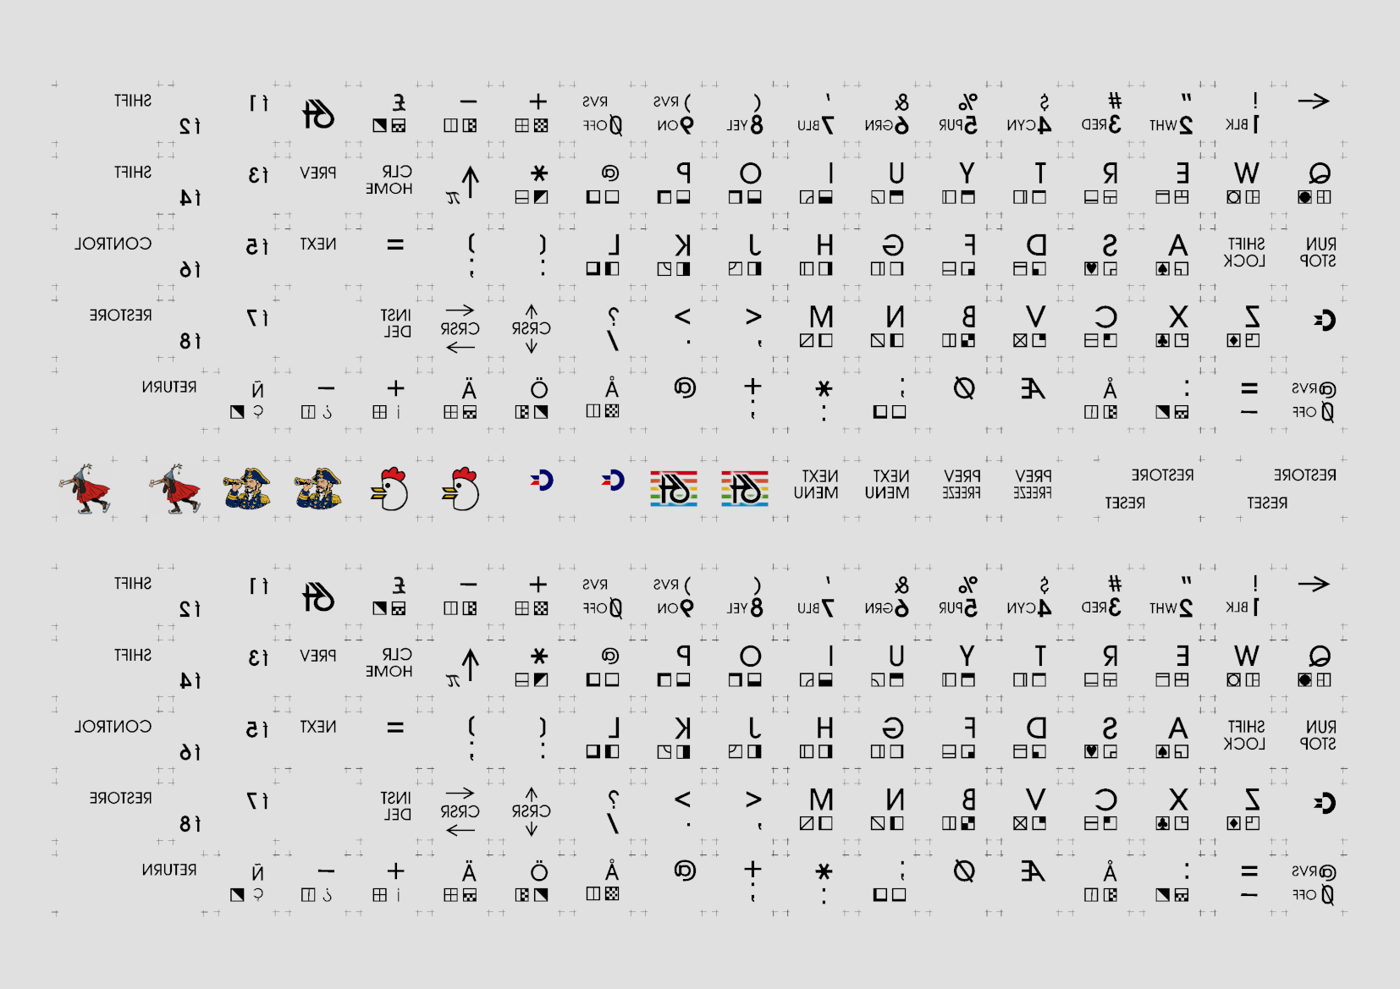
Keycaps/pictures/DSA_keycaps_DyeSub_scaled_down.png
