svenpetersen1965/C64-Keyboard/Keycaps/pictures/DSA_keycaps_in_single_tray_no_font.png

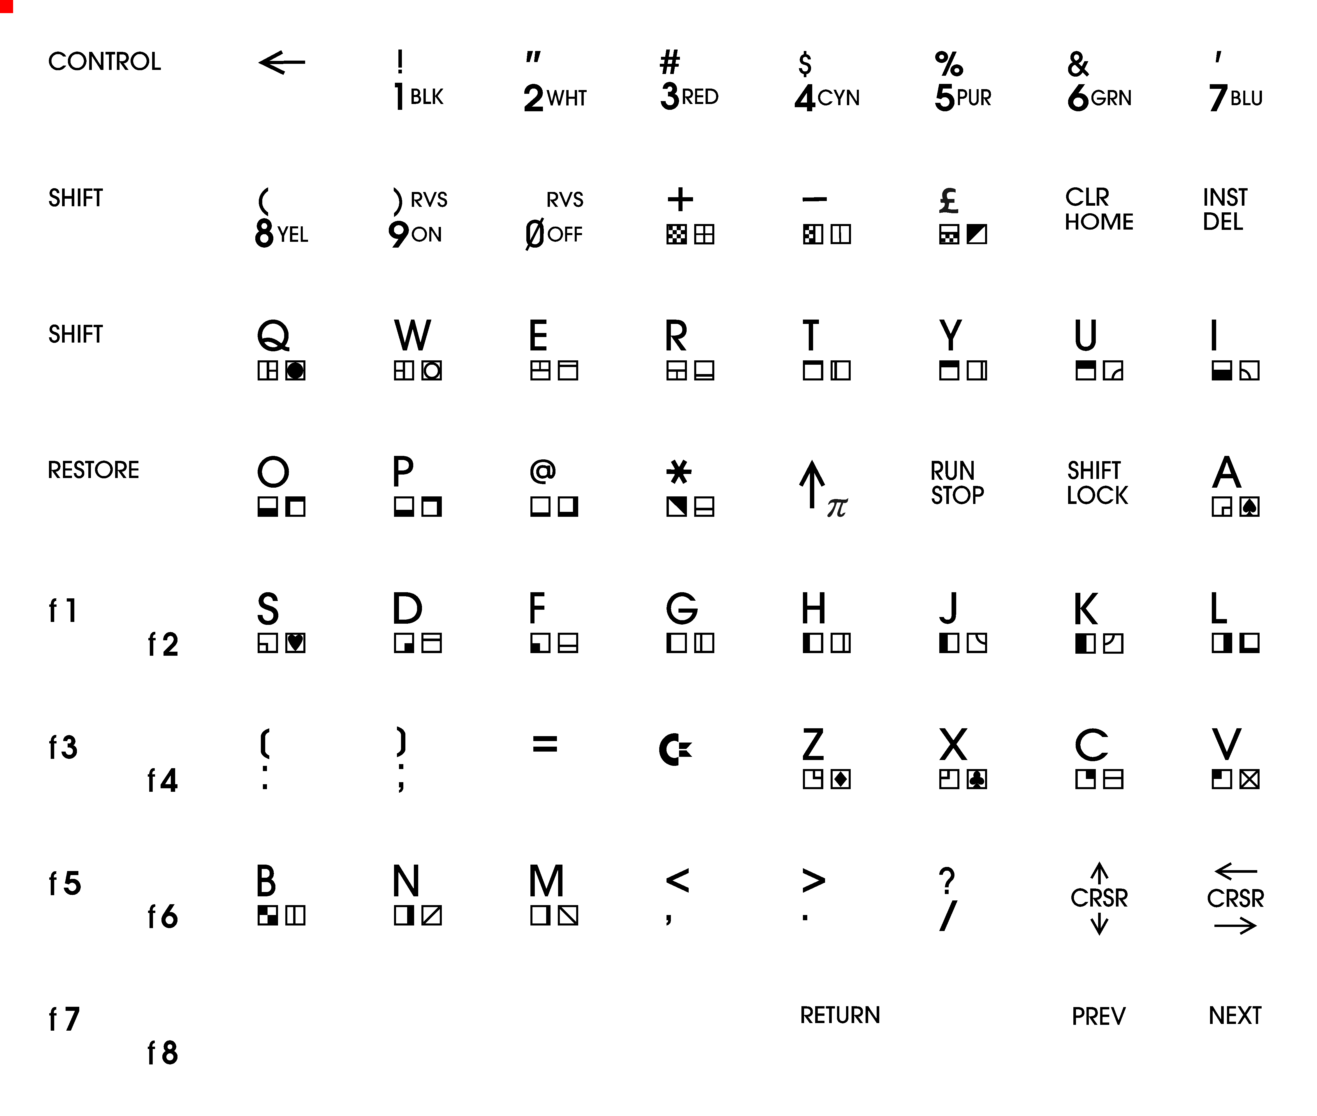
Keycaps/pictures/DSA_keycaps_in_single_tray_no_font.png
