svenpetersen1965/C64-Keyboard/Keycaps/pictures/kb_layout_danish.png

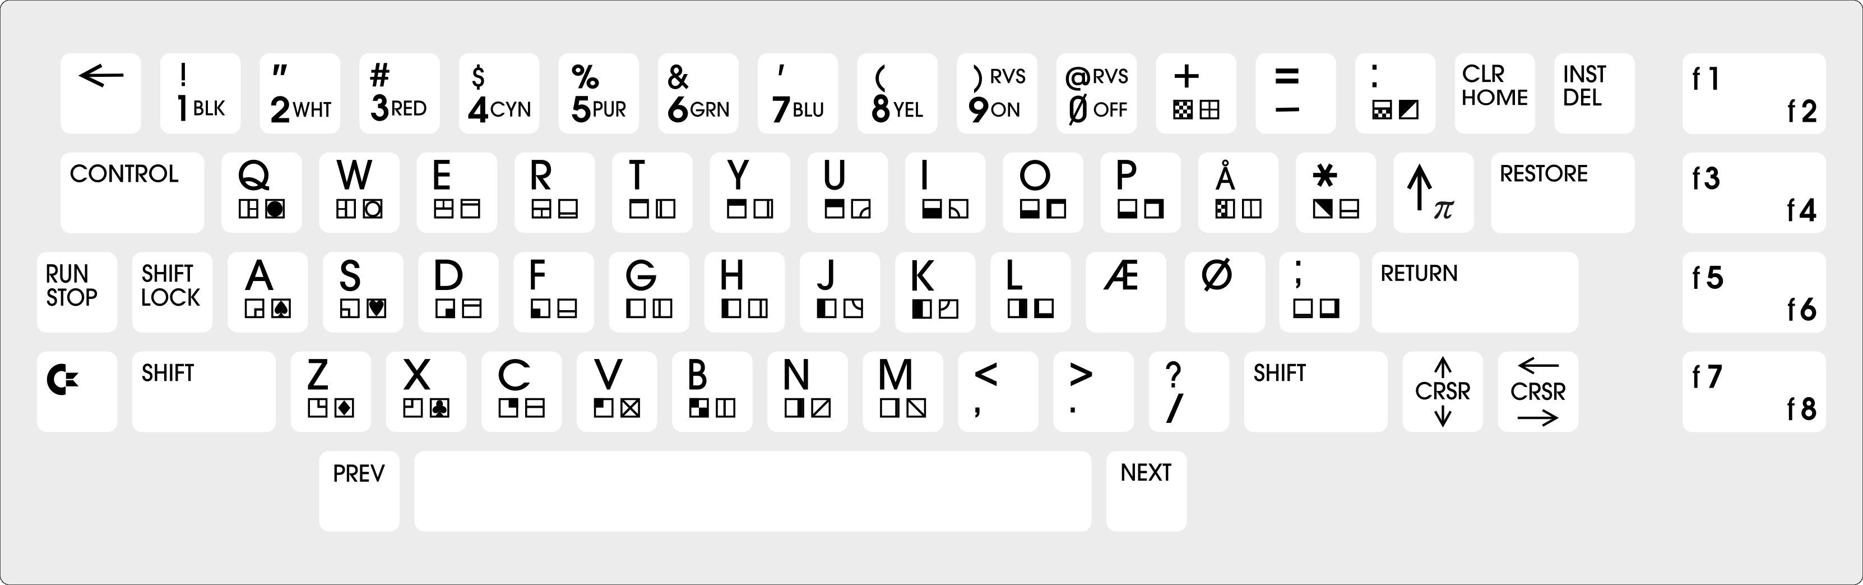
Keycaps/pictures/kb_layout_danish.png
