svenpetersen1965/C64-Keyboard/Keycaps/pictures/KB_layout_spanish.png

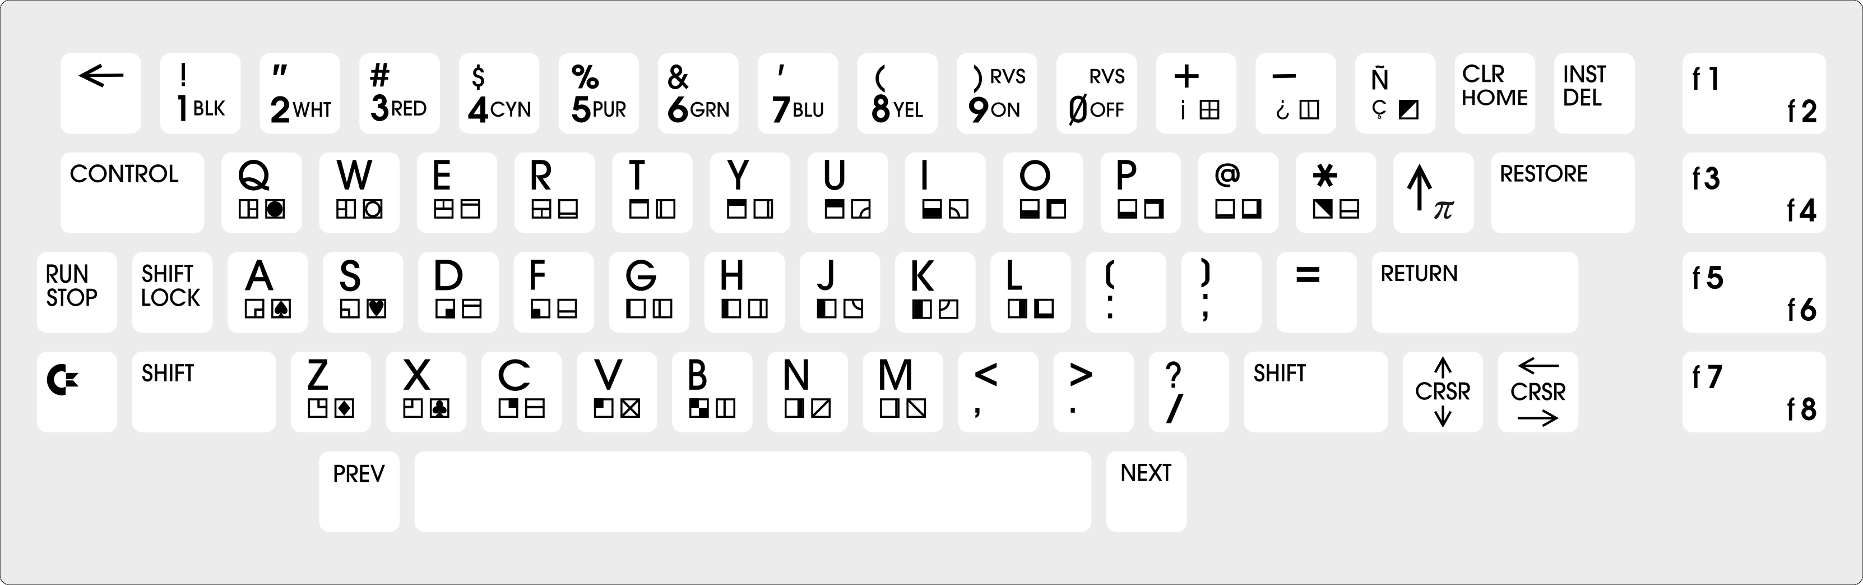
Keycaps/pictures/KB_layout_spanish.png
