svenpetersen1965/C64-Keyboard/Keycaps/pictures/kb_layout_swedish.png

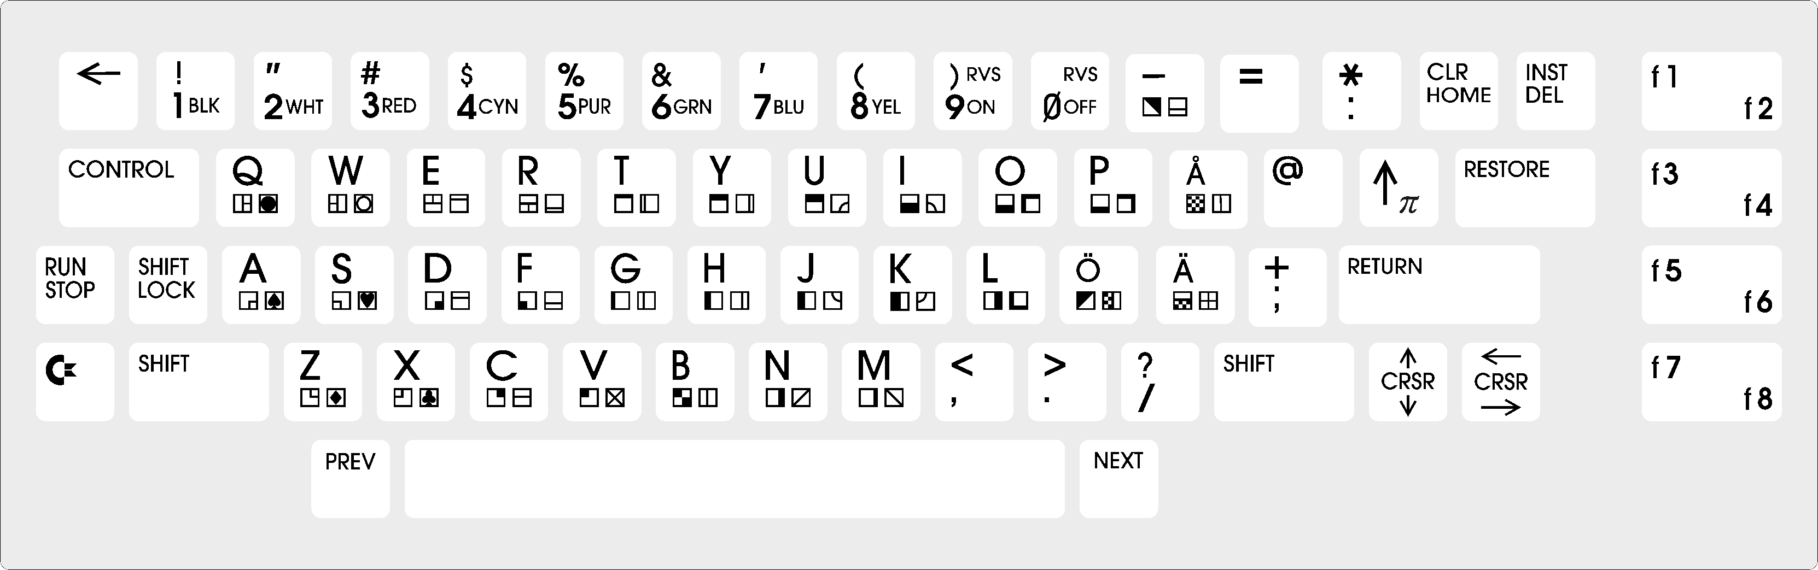
Keycaps/pictures/kb_layout_swedish.png
