svenpetersen1965/C64-Keyboard/Keycaps/pictures/keycap_Profiles_rnd.png

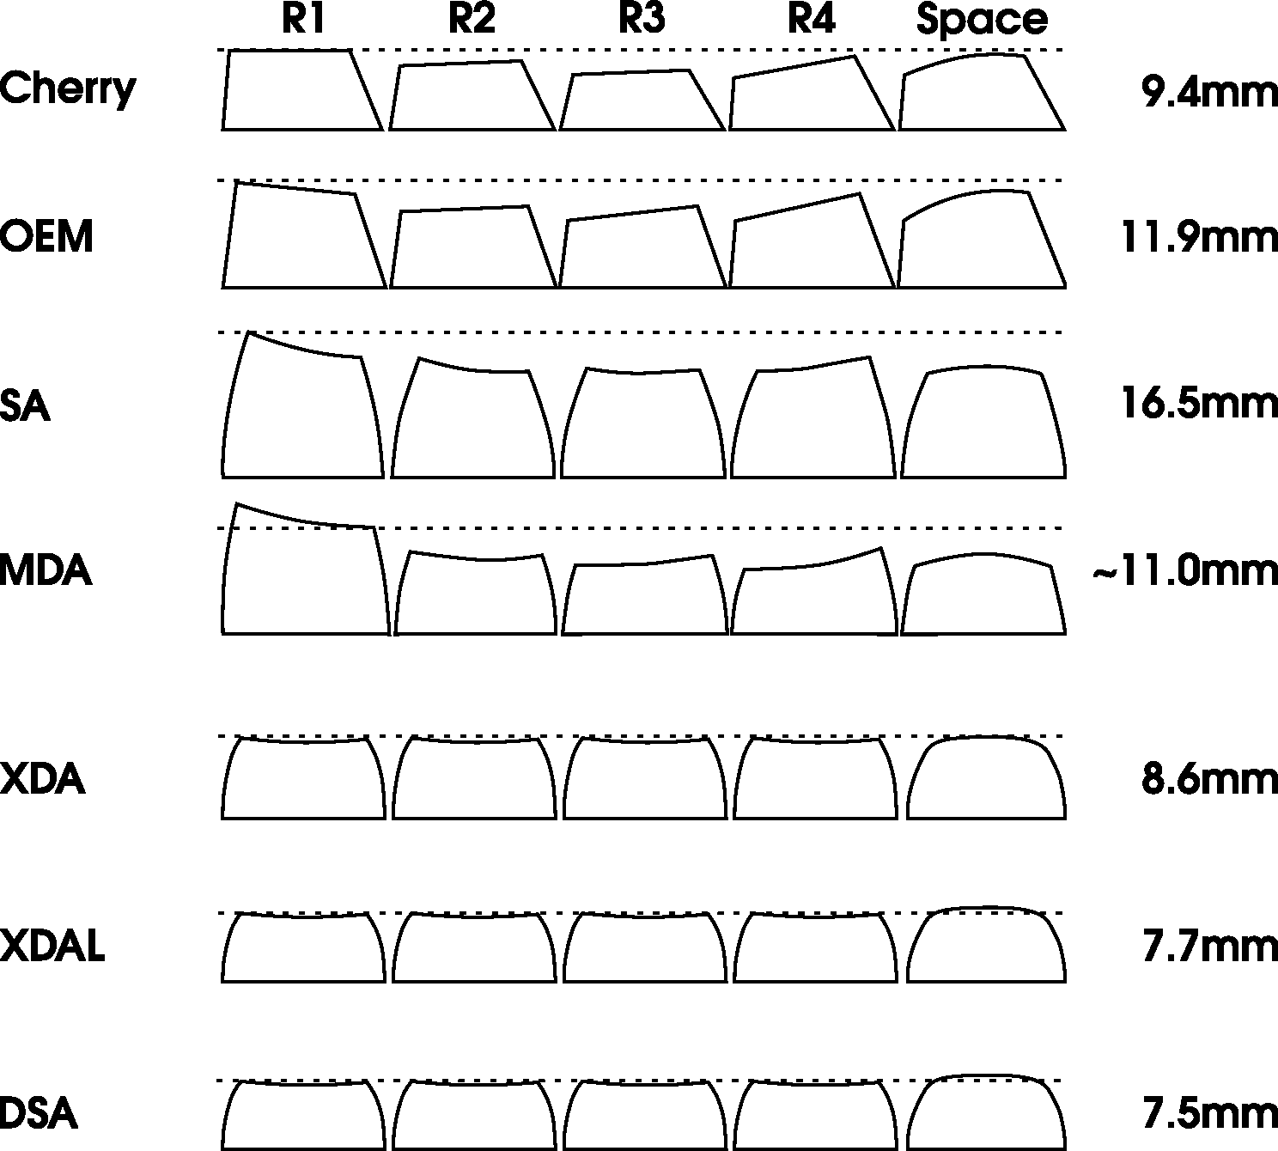
Keycaps/pictures/keycap_Profiles_rnd.png
