svenpetersen1965/C64-Keyboard/Keycaps/pictures/UV-decal_perspective.JPG

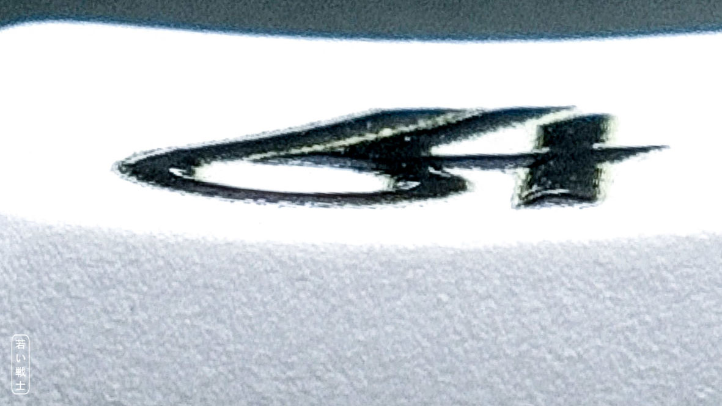
Keycaps/pictures/UV-decal_perspective.JPG
