svenpetersen1965/C64-Keyboard/Keycaps/Scans_original_keycaps/SW1_arrow_left.jpg

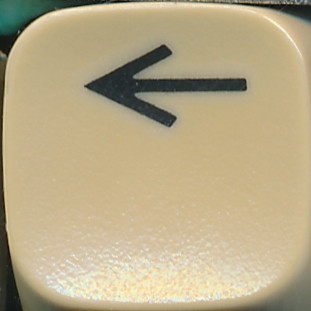
Keycaps/Scans_original_keycaps/SW1_arrow_left.jpg
