svenpetersen1965/C64-Keyboard/Keycaps/Scans_original_keycaps/SW2_1.jpg

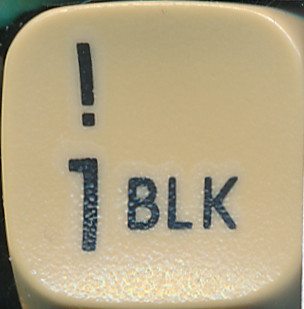
Keycaps/Scans_original_keycaps/SW2_1.jpg
