svenpetersen1965/C64-Keyboard/Keycaps/Scans_original_keycaps/SW5_4.jpg

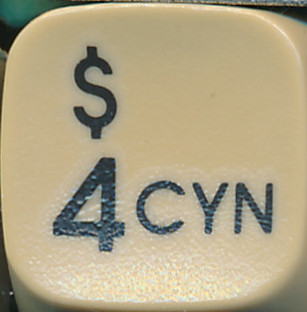
Keycaps/Scans_original_keycaps/SW5_4.jpg
