svenpetersen1965/C64-Keyboard/Keycaps/Scans_original_keycaps/SW6_5.jpg

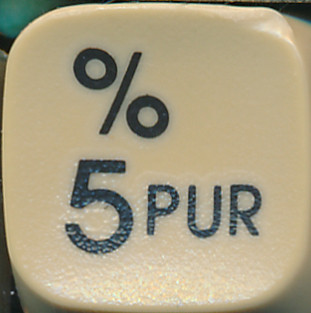
Keycaps/Scans_original_keycaps/SW6_5.jpg
