svenpetersen1965/C64-Keyboard/Keycaps/Scans_original_keycaps/SW9_8.jpg

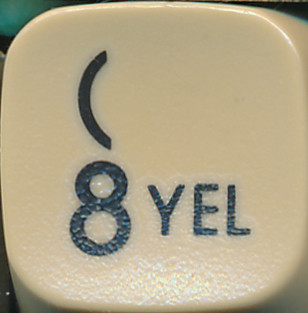
Keycaps/Scans_original_keycaps/SW9_8.jpg
