svenpetersen1965/C64-Keyboard/Keycaps/Scans_original_keycaps/SW12_plus.jpg

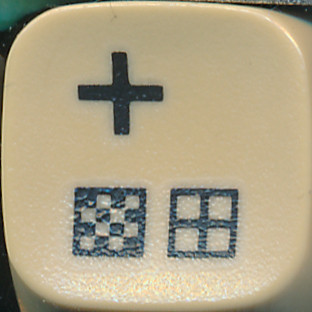
Keycaps/Scans_original_keycaps/SW12_plus.jpg
