svenpetersen1965/C64-Keyboard/Keycaps/Scans_original_keycaps/SW18_control.jpg

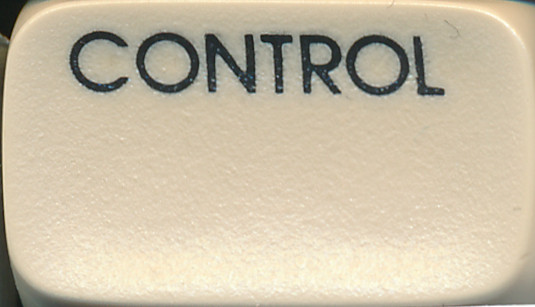
Keycaps/Scans_original_keycaps/SW18_control.jpg
