svenpetersen1965/C64-Keyboard/Keycaps/Scans_original_keycaps/SW20_w.jpg

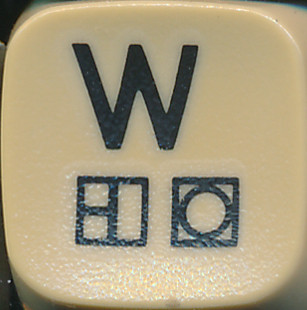
Keycaps/Scans_original_keycaps/SW20_w.jpg
