svenpetersen1965/C64-Keyboard/Keycaps/Scans_original_keycaps/SW21_e.jpg

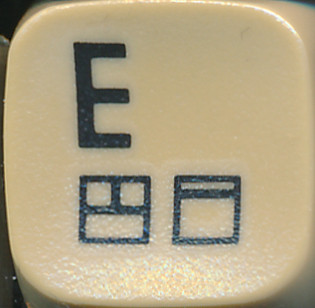
Keycaps/Scans_original_keycaps/SW21_e.jpg
