svenpetersen1965/C64-Keyboard/Keycaps/Scans_original_keycaps/SW23_t.jpg

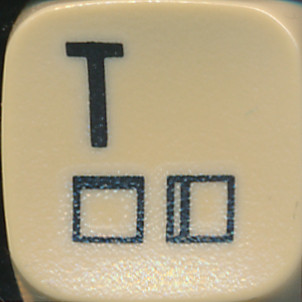
Keycaps/Scans_original_keycaps/SW23_t.jpg
