svenpetersen1965/C64-Keyboard/Keycaps/Scans_original_keycaps/SW24_y.jpg

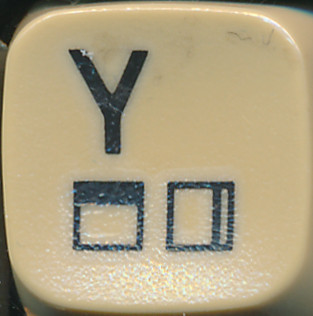
Keycaps/Scans_original_keycaps/SW24_y.jpg
