svenpetersen1965/C64-Keyboard/Keycaps/Scans_original_keycaps/SW29_at.jpg

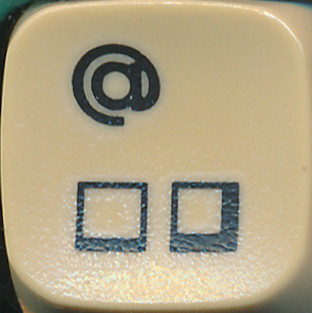
Keycaps/Scans_original_keycaps/SW29_at.jpg
