svenpetersen1965/C64-Keyboard/Keycaps/Scans_original_keycaps/SW30_asterisk.jpg

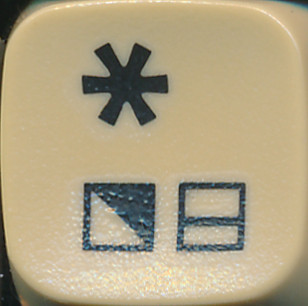
Keycaps/Scans_original_keycaps/SW30_asterisk.jpg
