svenpetersen1965/C64-Keyboard/Keycaps/Scans_original_keycaps/SW31_up_arrow.jpg

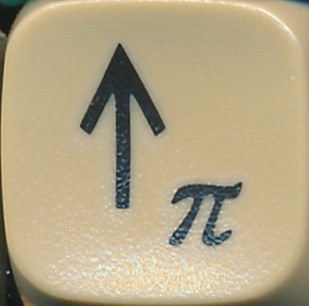
Keycaps/Scans_original_keycaps/SW31_up_arrow.jpg
