svenpetersen1965/C64-Keyboard/Keycaps/Scans_original_keycaps/SW32_restore.jpg

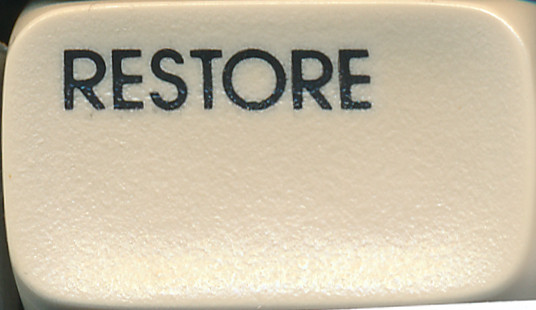
Keycaps/Scans_original_keycaps/SW32_restore.jpg
