svenpetersen1965/C64-Keyboard/Keycaps/Scans_original_keycaps/SW34_run.jpg

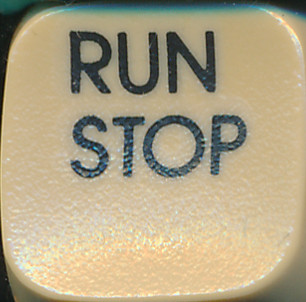
Keycaps/Scans_original_keycaps/SW34_run.jpg
