svenpetersen1965/C64-Keyboard/Keycaps/Scans_original_keycaps/SW38_d.jpg

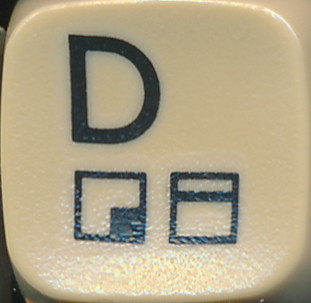
Keycaps/Scans_original_keycaps/SW38_d.jpg
