svenpetersen1965/C64-Keyboard/Keycaps/Scans_original_keycaps/SW45_colon.jpg

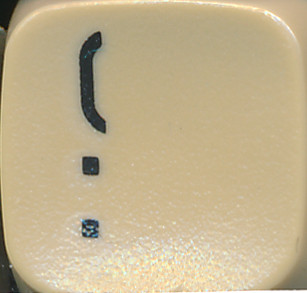
Keycaps/Scans_original_keycaps/SW45_colon.jpg
