svenpetersen1965/C64-Keyboard/Keycaps/Scans_original_keycaps/SW48_return.jpg

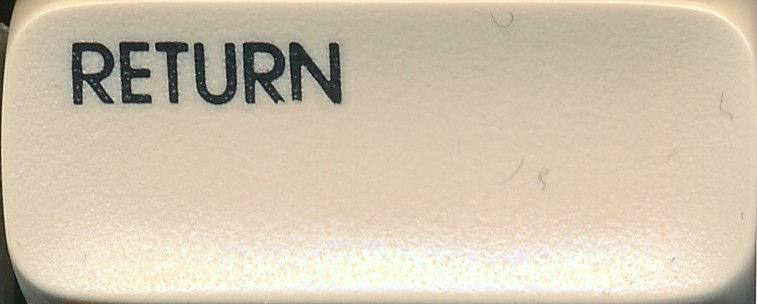
Keycaps/Scans_original_keycaps/SW48_return.jpg
