svenpetersen1965/C64-Keyboard/Keycaps/Scans_original_keycaps/SW50_commodore.jpg

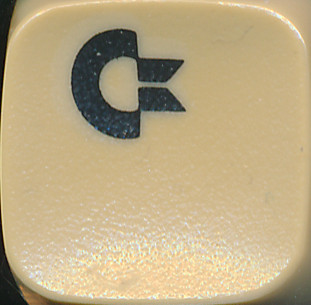
Keycaps/Scans_original_keycaps/SW50_commodore.jpg
