svenpetersen1965/C64-Keyboard/Keycaps/Scans_original_keycaps/SW53_x.jpg

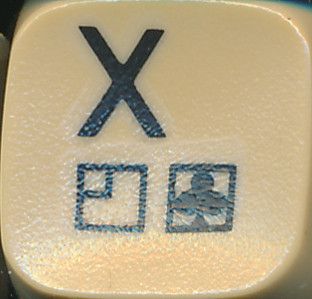
Keycaps/Scans_original_keycaps/SW53_x.jpg
