svenpetersen1965/C64-Keyboard/Keycaps/Scans_original_keycaps/SW54_c.jpg

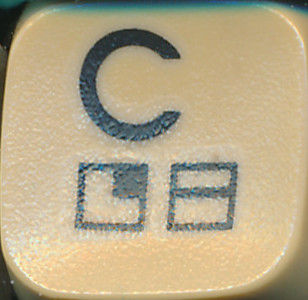
Keycaps/Scans_original_keycaps/SW54_c.jpg
