svenpetersen1965/C64-Keyboard/Keycaps/Scans_original_keycaps/SW55_v.jpg

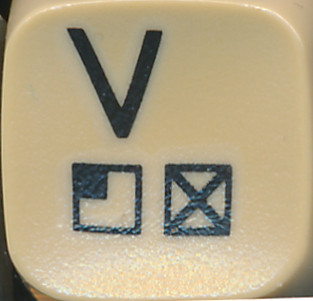
Keycaps/Scans_original_keycaps/SW55_v.jpg
