svenpetersen1965/C64-Keyboard/Keycaps/Scans_original_keycaps/SW56_b.jpg

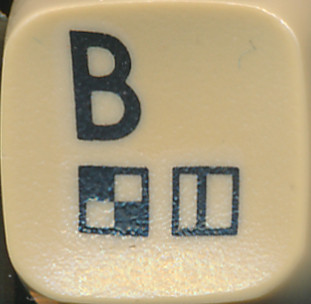
Keycaps/Scans_original_keycaps/SW56_b.jpg
