svenpetersen1965/C64-Keyboard/Keycaps/Scans_original_keycaps/SW60_period.jpg

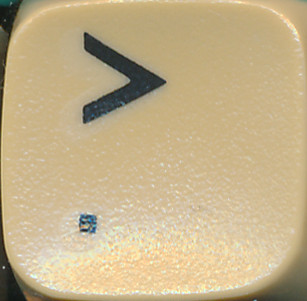
Keycaps/Scans_original_keycaps/SW60_period.jpg
