svenpetersen1965/C64-Keyboard/Keycaps/Scans_original_keycaps/SW61_slash.jpg

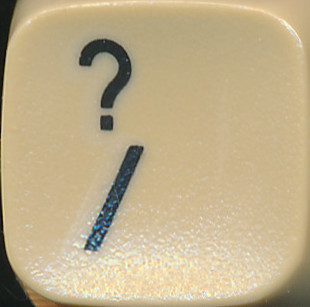
Keycaps/Scans_original_keycaps/SW61_slash.jpg
