svenpetersen1965/C64-Keyboard/Keycaps/Scans_original_keycaps/SW63_crsr_ud.jpg

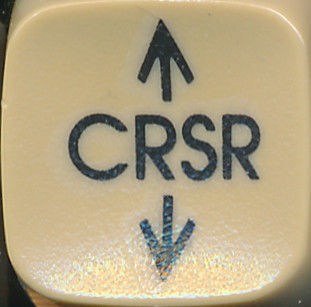
Keycaps/Scans_original_keycaps/SW63_crsr_ud.jpg
