svenpetersen1965/C64-Keyboard/Keycaps/Scans_original_keycaps/SW65_f7.jpg

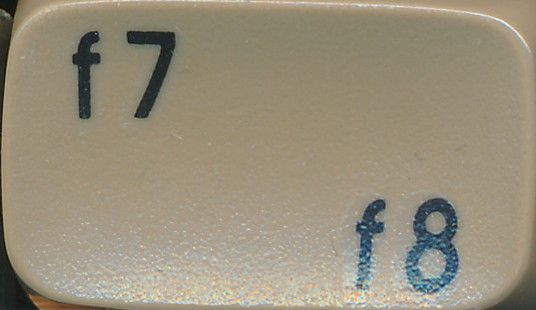
Keycaps/Scans_original_keycaps/SW65_f7.jpg
