svenpetersen1965/C64-Keyboard/pictures/6162_-_C64KBD_DyeSub.JPG

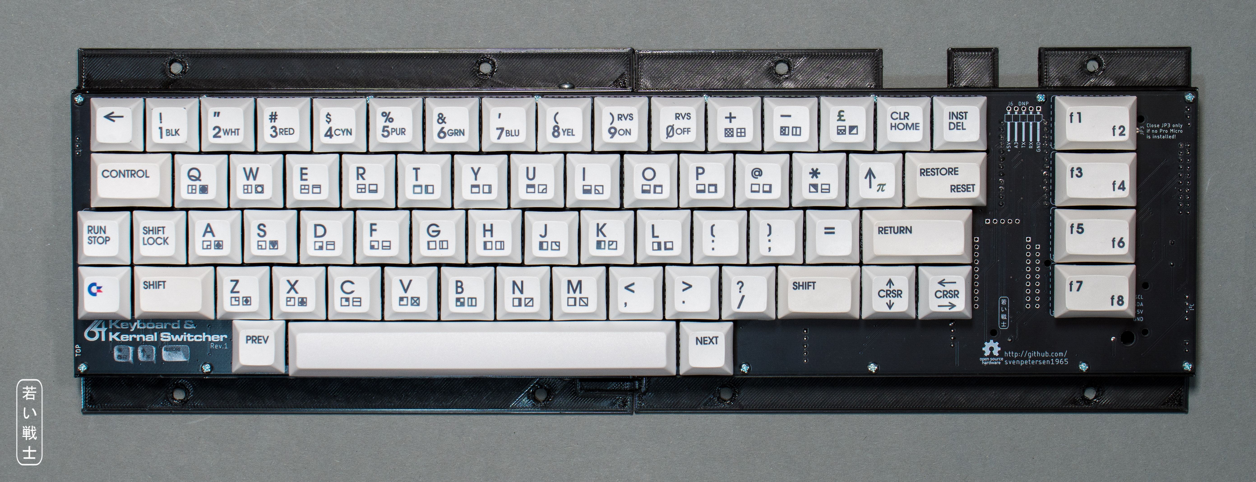
pictures/6162_-_C64KBD_DyeSub.JPG
