svenpetersen1965/C64-Keyboard/pictures/6164_-_C64KBD_black_usb.JPG

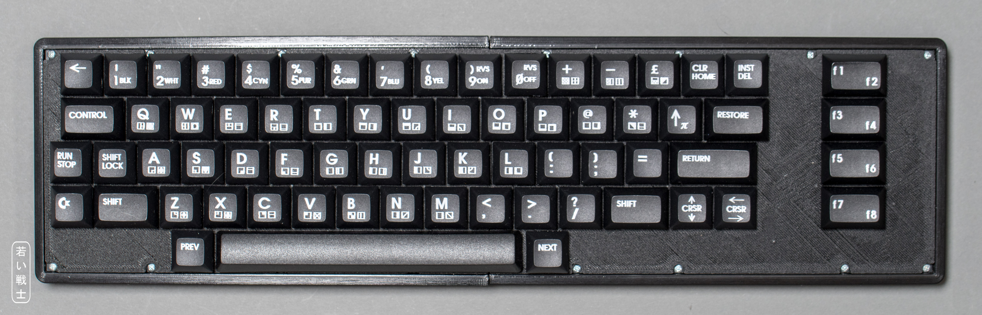
pictures/6164_-_C64KBD_black_usb.JPG
