svenpetersen1965/C64-Keyboard/Software/Pictures/4634_-_reset_switch.JPG

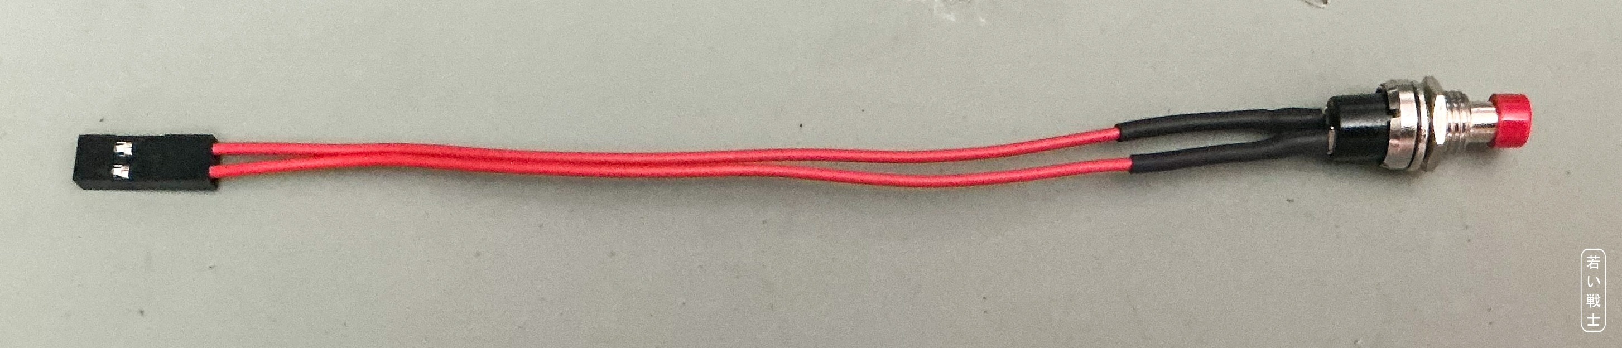
Software/Pictures/4634_-_reset_switch.JPG
