svenpetersen1965/C64-Keyboard/Software/Pictures/Arduino_IDE_done_uploading..png

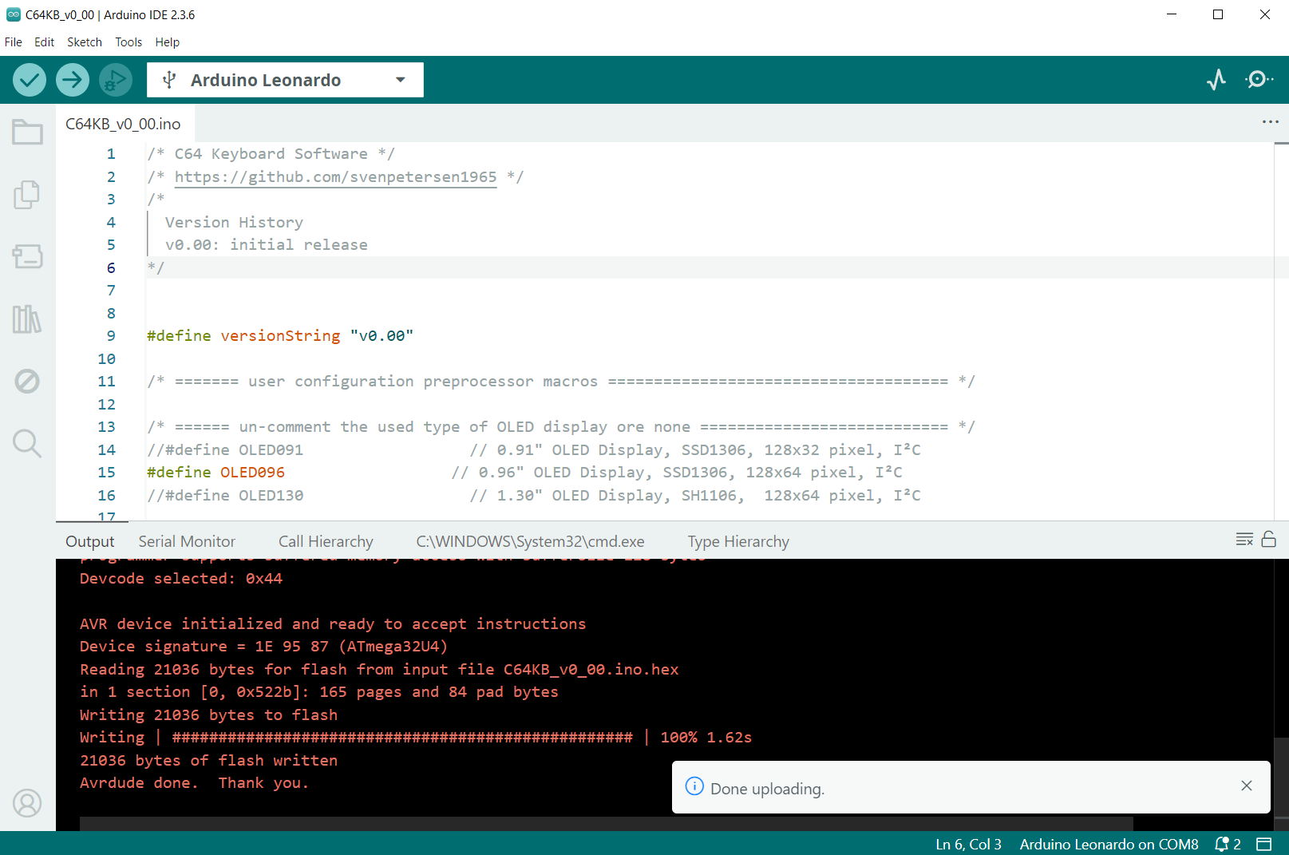
Software/Pictures/Arduino_IDE_done_uploading..png
