svenpetersen1965/C64-Keyboard/Software/Pictures/Arduino_IDE_waiting..png

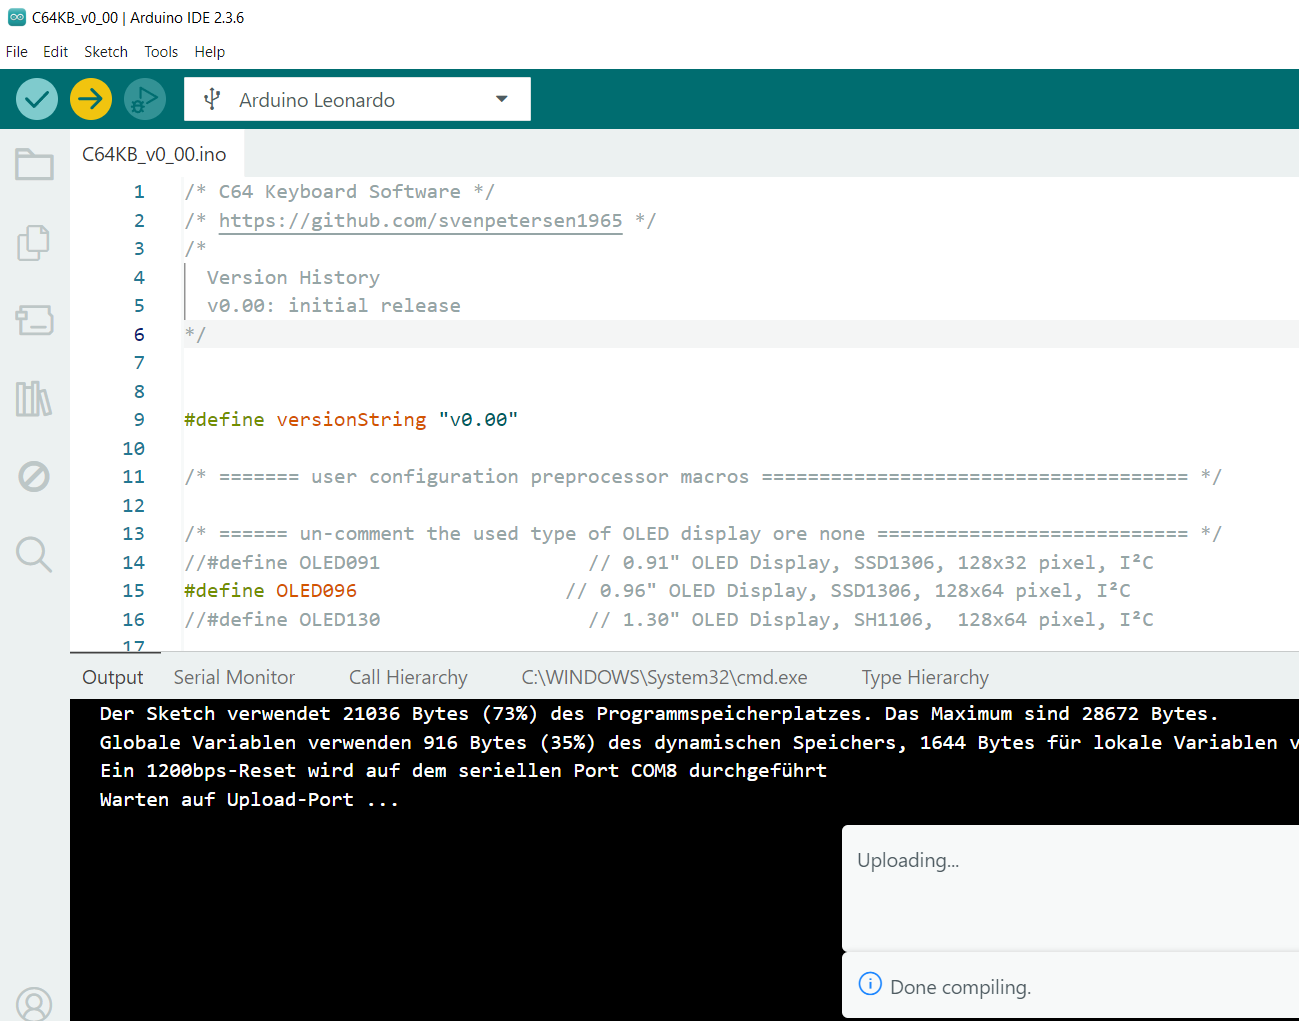
Software/Pictures/Arduino_IDE_waiting..png
