svenpetersen1965/C64-Keyboard/Software/Pictures/Clips-key.png

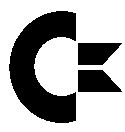
Software/Pictures/Clips-key.png
