svenpetersen1965/C64-Keyboard/Software/Pictures/f1-key.png

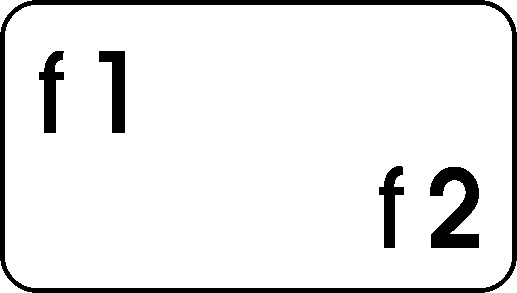
Software/Pictures/f1-key.png
