svenpetersen1965/C64-Keyboard/Software/Pictures/f3-key.png

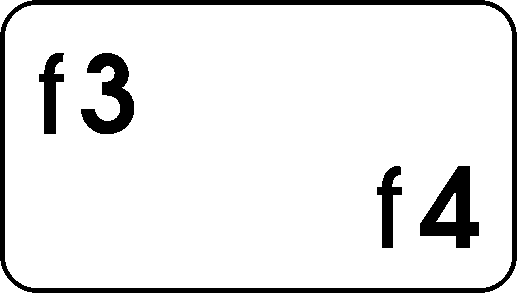
Software/Pictures/f3-key.png
