svenpetersen1965/C64-Keyboard/Software/Pictures/f7-key.png

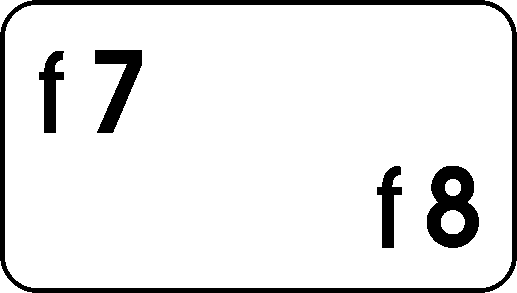
Software/Pictures/f7-key.png
