svenpetersen1965/C64-Keyboard/Software/Pictures/FREEZE-key.png

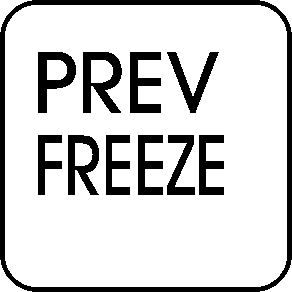
Software/Pictures/FREEZE-key.png
