svenpetersen1965/C64-Keyboard/Software/Pictures/MENU-key.png

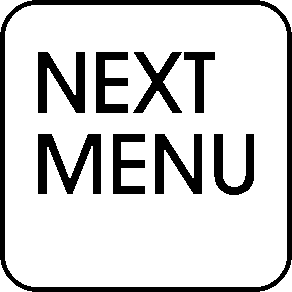
Software/Pictures/MENU-key.png
