svenpetersen1965/C64-Keyboard/Software/Pictures/NEXT-key.png

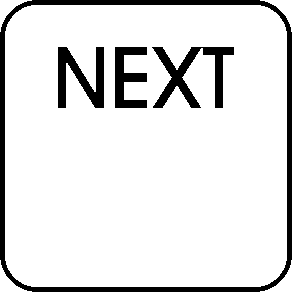
Software/Pictures/NEXT-key.png
