svenpetersen1965/C64-Keyboard/Software/Pictures/PREV-key.png

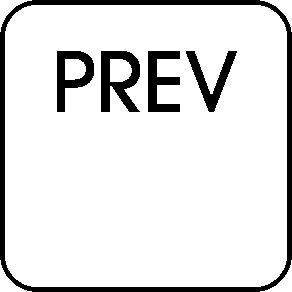
Software/Pictures/PREV-key.png
