svenpetersen1965/C64-Keyboard/Software/Pictures/RESTORE-key.png

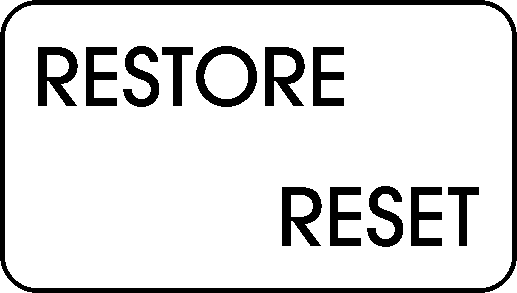
Software/Pictures/RESTORE-key.png
