svenpetersen1965/C64-Keyboard/C64 Keyboard connector PCB/Rev. 0/Excel/Keyboard_C64_connector_PCB.csv

Qty | Value | Device | Package | Parts | Description
1 |  | 3MM | 3MM | LD1
1 | 330R | RES04 | R-10 | R1
1 | BL1-85AXX-20U | BL1-85AXX-20U | BL1-85AXX-20U | J1
1 | MICMA20B | MICMA20B | MICMA20B | J2
1 | OPEN_SOURCE_HW | OPEN_SOURCE_HW | OPENHW | U$9
