svenpetersen1965/C64-Keyboard/Key_Positions/C64_keyboard_meassures.xlsx

Sheet: measured
h = | 97.2 | mm
h(pcb) = | 96.4 | mm
Δh/2 = | 0.4 | mm
w = | 385.6 | mm
key | dia | x | y | Cx | Cy | dx | Spalte1
left arrow | 9.25 | 17.77 | 10.78 | 1 | 5 | 0.00
1 | 9.30 | 36.65 | 10.75 | 2 | 5 | 18.88
2 | 9.30 | 55.65 | 10.85 | 3 | 5 | 19.00
3 | 9.30 | 74.75 | 10.65 | 4 | 5 | 19.10
4 | 9.30 | 93.75 | 10.65 | 5 | 5 | 19.00
5 | 9.25 | 112.78 | 10.68 | 6 | 5 | 19.03 |  | row5
6 | 9.30 | 131.90 | 10.75 | 7 | 5 | 19.12 |  | avg(dx) | geo avg | med(dx) | Stdev(dx)
7 | 9.35 | 150.77 | 10.68 | 8 | 5 | 18.87 |  | 19.03 | 19.02 | 19.00 | 0.14
8 | 9.30 | 170.05 | 10.80 | 9 | 5 | 19.28
9 | 9.30 | 189.10 | 10.60 | 10 | 5 | 19.05 | measured | avg(y) | median(y) | Stdev(y)
0 | 9.35 | 208.07 | 10.77 | 11 | 5 | 18.97 |  | 10.73 | 10.75 | 0.08
+ | 9.30 | 227.05 | 10.75 | 12 | 5 | 18.97
- | 9.30 | 245.95 | 10.85 | 13 | 5 | 18.90 |  | xoffs
£ | 9.35 | 264.82 | 10.68 | 14 | 5 | 18.88 |  | 17.77
CLR | 9.35 | 284.18 | 10.68 | 15 | 5 | 19.35
INST | 9.30 | 303.10 | 10.85 | 16 | 5 | 18.92
F1 | 9.35 | 353.77 | 10.62 | 17 | 5
CONTROL | 9.30 | 27.20 | 29.90 | 1 | 4 | 0.00 |  | row4
Q | 9.20 | 46.25 | 29.95 | 2 | 4 | 19.05 |  | avg(dx) | geo avg | med(dx) | Stdev(dx)
W | 9.30 | 65.30 | 29.80 | 3 | 4 | 19.05 |  | 19.03 | 19.03 | 19.01 | 0.18
E | 9.20 | 84.15 | 29.80 | 4 | 4 | 18.85
R | 9.25 | 103.12 | 29.77 | 5 | 4 | 18.98 |  | avg(y) | median(y) | Stdev(y)
T | 9.25 | 122.08 | 30.08 | 6 | 4 | 18.95 |  | 29.81 | 29.80 | 0.13
Y | 9.30 | 141.45 | 29.75 | 7 | 4 | 19.37
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
f1 | 27.5 | 9.5 | -4.75 | 1.5 |  |  | dx avg(row5) | 19.03
f3 | 27.5 | 9.5 | -4.75 | 1.5 |  |  | dx avg(row4) | 19.03
f5 | 27.5 | 9.5 | -4.75 | 1.5 |  |  | dx avg(row3) | 19.04
f7 | 27.5 | 9.5 | -4.75 | 1.5 |  |  | dx avg(row2) | 19.06
all others | 18 |  |  | 1.0 |  |  | avg | 19.04

Sheet: calculated
Errechnet | dx | dy
 | 19.04 | 19.05 | mm
key | x | y | Cx | Cy
left arrow | 17.60 | 10.75 | 1 | 5 | 0,7"
1 | 36.64 | 10.75 | 2 | 5
2 | 55.68 | 10.75 | 3 | 5
3 | 74.72 | 10.75 | 4 | 5
4 | 93.76 | 10.75 | 5 | 5
5 | 112.80 | 10.75 | 6 | 5
6 | 131.84 | 10.75 | 7 | 5
7 | 150.88 | 10.75 | 8 | 5
8 | 169.92 | 10.75 | 9 | 5
9 | 188.96 | 10.75 | 10 | 5
0 | 208.00 | 10.75 | 11 | 5
+ | 227.04 | 10.75 | 12 | 5
- | 246.08 | 10.75 | 13 | 5
£ | 265.12 | 10.75 | 14 | 5
CLR | 284.16 | 10.75 | 15 | 5
INST | 303.20 | 10.75 | 16 | 5
F1 | 353.85 | 10.75 | 17 | 5
CONTROL | 27.20 | 29.80 | 1 | 4 | 1,07"
Q | 46.24 | 29.80 | 2 | 4
W | 65.28 | 29.80 | 3 | 4
E | 84.32 | 29.80 | 4 | 4
R | 103.36 | 29.80 | 5 | 4
T | 122.40 | 29.80 | 6 | 4
Y | 141.44 | 29.80 | 7 | 4
U | 160.48 | 29.80 | 8 | 4
I | 179.52 | 29.80 | 9 | 4
O | 198.56 | 29.80 | 10 | 4
P | 217.60 | 29.80 | 11 | 4
@ | 236.64 | 29.80 | 12 | 4
* | 255.68 | 29.80 | 13 | 4
up arrow | 274.72 | 29.80 | 14 | 4
RESTORE | 293.76 | 29.80 | 15 | 4
F3 | 353.85 | 29.80 | 16 | 4
RUN | 12.80 | 48.85 | 1 | 3 | 0,51"
SHIFT LOCK | 31.84 | 48.85 | 2 | 3
A | 50.88 | 48.85 | 3 | 3
S | 69.92 | 48.85 | 4 | 3
D | 88.96 | 48.85 | 5 | 3
F | 108.00 | 48.85 | 6 | 3
G | 127.04 | 48.85 | 7 | 3
H | 146.08 | 48.85 | 8 | 3
J | 165.12 | 48.85 | 9 | 3
K | 184.16 | 48.85 | 10 | 3
L | 203.20 | 48.85 | 11 | 3
[ | 222.24 | 48.85 | 12 | 3
] | 241.28 | 48.85 | 13 | 3
equals | 260.32 | 48.85 | 14 | 3
RETURN | 288.88 | 48.85 | 15 | 3
F5 | 353.85 | 48.85 | 16 | 3
C= | 12.80 | 67.90 | 1 | 2 | 0,51"
Shift Left | 41.36 | 67.90 | 2 | 2
Z | 60.40 | 67.90 | 3 | 2
X | 79.44 | 67.90 | 4 | 2
C | 98.48 | 67.90 | 5 | 2
V | 117.52 | 67.90 | 6 | 2
B | 136.56 | 67.90 | 7 | 2
N | 155.60 | 67.90 | 8 | 2
M | 174.64 | 67.90 | 9 | 2
, | 193.68 | 67.90 | 10 | 2
. | 212.72 | 67.90 | 11 | 2
/ | 231.76 | 67.90 | 12 | 2
Shift Right | 260.32 | 67.90 | 13 | 2
CRSR up/dn | 279.36 | 67.90 | 14 | 2
CRSR l/r | 298.40 | 67.90 | 15 | 2
F7 | 353.85 | 67.90 | 16 | 2
Space | 141.38 | 86.95 | 1 | 1 | 5,57"

Sheet: deviation
Abweichungen
key | x | y | Cx | Cy | rx² | Σrx² | Stdev | ry² | Σry²
left arrow | -0.17 | -0.03 | 1 | 5 | 0.03 | 0.21 | 0.11 | 0.000625 | 0.11
1 | -0.01 | 0.00 | 2 | 5 | 0.0001 |  |  | 0.00
2 | 0.03 | -0.10 | 3 | 5 | 0.0009 |  |  | 0.01
3 | -0.03 | 0.10 | 4 | 5 | 0.0009 |  |  | 0.01
4 | 0.01 | 0.10 | 5 | 5 | 0.0001 |  |  | 0.01
5 | 0.02 | 0.07 | 6 | 5 | 0.000625 |  |  | 0.01
6 | -0.06 | 0.00 | 7 | 5 | 0.0036 |  |  | 0.00
7 | 0.10 | 0.07 | 8 | 5 | 0.01 |  |  | 0.01
8 | -0.13 | -0.05 | 9 | 5 | 0.02 |  |  | 0.0025
9 | -0.14 | 0.15 | 10 | 5 | 0.02 |  |  | 0.02
0 | -0.08 | -0.02 | 11 | 5 | 0.01 |  |  | 0.000625
+ | -0.01 | 0.00 | 12 | 5 | 0.0001 |  |  | 0.00
- | 0.13 | -0.10 | 13 | 5 | 0.02 |  |  | 0.01
£ | 0.29 | 0.07 | 14 | 5 | 0.09 |  |  | 0.01
CLR | -0.02 | 0.07 | 15 | 5 | 0.000225 |  |  | 0.01
INST | 0.10 | -0.10 | 16 | 5 | 0.01 |  |  | 0.01
F1 | 0.07 | 0.12 | 17 | 5 | 0.01 |  |  | 0.02
CONTROL | 0.00 | -0.10 | 1 | 4 | 0.00 | 0.39 | 0.15 | 0.01 | 0.28
Q | -0.01 | -0.15 | 2 | 4 | 0.0001 |  |  | 0.02
W | -0.02 | 0.00 | 3 | 4 | 0.0004 |  |  | 0.00
E | 0.17 | 0.00 | 4 | 4 | 0.03 |  |  | 0.00
R | 0.23 | 0.03 | 5 | 4 | 0.06 |  |  | 0.000625
T | 0.32 | -0.28 | 6 | 4 | 0.11 |  |  | 0.08
Y | -0.01 | 0.05 | 7 | 4 | 0.0001 |  |  | 0.0025
U | -0.32 | -0.05 | 8 | 4 | 0.10 |  |  | 0.0025
I | -0.18 | 0.05 | 9 | 4 | 0.03 |  |  | 0.0025
O | 0.01 | -0.05 | 10 | 4 | 0.0001 |  |  | 0.0025
P | 0.10 | 0.00 | 11 | 4 | 0.01 |  |  | 0.00
@ | -0.01 | 0.15 | 12 | 4 | 0.0001 |  |  | 0.02
* | -0.12 | 0.15 | 13 | 4 | 0.01 |  |  | 0.02
up arrow | 0.17 | -0.25 | 14 | 4 | 0.03 |  |  | 0.06
RESTORE | 0.11 | 0.05 | 15 | 4 | 0.01 |  |  | 0.0025
F3 | -0.03 | 0.23 | 16 | 4 | 0.000625 |  |  | 0.05
RUN | -0.05 | 0.05 | 1 | 3 | 0.0025 | 0.12 | 0.08 | 0.0025 | 0.17
SHIFT LOCK | 0.04 | -0.15 | 2 | 3 | 0.0016 |  |  | 0.02
A | -0.02 | 0.20 | 3 | 3 | 0.0004 |  |  | 0.04
S | -0.03 | 0.05 | 4 | 3 | 0.0009 |  |  | 0.0025
D | 0.11 | 0.10 | 5 | 3 | 0.01 |  |  | 0.01
F | 0.12 | 0.08 | 6 | 3 | 0.02 |  |  | 0.01
G | 0.04 | 0.05 | 7 | 3 | 0.0016 |  |  | 0.0025
H | -0.12 | 0.05 | 8 | 3 | 0.01 |  |  | 0.0025
J | -0.18 | 0.10 | 9 | 3 | 0.03 |  |  | 0.01
K | 0.01 | 0.20 | 10 | 3 | 0.0001 |  |  | 0.04
L | -0.13 | -0.02 | 11 | 3 | 0.02 |  |  | 0.000625
[ | -0.06 | 0.00 | 12 | 3 | 0.0036 |  |  | 0.00
] | -0.02 | -0.15 | 13 | 3 | 0.0004 |  |  | 0.02
equals | -0.01 | 0.02 | 14 | 3 | 2.5e-05 |  |  | 0.000625
RETURN | -0.12 | 0.05 | 15 | 3 | 0.01 |  |  | 0.0025
F5 | 0.00 | 0.05 | 16 | 3 | 0.00 |  |  | 0.0025
C= | -0.10 | -0.15 | 1 | 2 | 0.01 | 0.14 | 0.09 | 0.02 | 0.16
Shift Left | 0.19 | -0.07 | 2 | 2 | 0.03 |  |  | 0.01
Z | 0.05 | 0.05 | 3 | 2 | 0.0025 |  |  | 0.0025
X | -0.01 | -0.10 | 4 | 2 | 0.0001 |  |  | 0.01
C | 0.13 | -0.05 | 5 | 2 | 0.02 |  |  | 0.0025
V | 0.07 | 0.10 | 6 | 2 | 0.0049 |  |  | 0.01
B | -0.04 | -0.05 | 7 | 2 | 0.0016 |  |  | 0.0025
N | 0.02 | 0.03 | 8 | 2 | 0.000625 |  |  | 0.000625
M | -0.06 | 0.10 | 9 | 2 | 0.0036 |  |  | 0.01
, | -0.12 | 0.00 | 10 | 2 | 0.01 |  |  | 0.00
. | -0.08 | 0.20 | 11 | 2 | 0.01 |  |  | 0.04
/ | 0.01 | 0.10 | 12 | 2 | 0.0001 |  |  | 0.01
Shift Right | -0.13 | -0.05 | 13 | 2 | 0.02 |  |  | 0.0025
CRSR up/dn | -0.07 | 0.12 | 14 | 2 | 0.004225 |  |  | 0.02
CRSR l/r | -0.15 | 0.00 | 15 | 2 | 0.02 |  |  | 0.00
F7 | 0.00 | 0.15 | 16 | 2 | 0.00 |  |  | 0.02
Space | 0.00 | -0.03 | 1 | 1 | 0.00

Sheet: PCB
h = | 97.2 | mm
h(pcb) = | 96.4 | mm
Δh/2 = | 0.4 | mm
w = | 385.6 | mm
key | x | y | Cx | Cy | Reference | row | col
left arrow | 17.60 | 86.05 | 1 | 5 | SW1 | 1 | 7
1 | 36.64 | 86.05 | 2 | 5 | SW2 | 0 | 7
2 | 55.68 | 86.05 | 3 | 5 | SW3 | 3 | 7
3 | 74.72 | 86.05 | 4 | 5 | SW4 | 0 | 1
4 | 93.76 | 86.05 | 5 | 5 | SW5 | 3 | 1
5 | 112.80 | 86.05 | 6 | 5 | SW6 | 0 | 2
6 | 131.84 | 86.05 | 7 | 5 | SW7 | 3 | 2
7 | 150.88 | 86.05 | 8 | 5 | SW8 | 0 | 3
8 | 169.92 | 86.05 | 9 | 5 | SW9 | 3 | 3
9 | 188.96 | 86.05 | 10 | 5 | SW10 | 0 | 4
0 | 208.00 | 86.05 | 11 | 5 | SW11 | 3 | 4
+ | 227.04 | 86.05 | 12 | 5 | SW12 | 0 | 5
- | 246.08 | 86.05 | 13 | 5 | SW13 | 3 | 5
£ | 265.12 | 86.05 | 14 | 5 | SW14 | 0 | 6
CLR | 284.16 | 86.05 | 15 | 5 | SW15 | 3 | 6
INST | 303.20 | 86.05 | 16 | 5 | SW16 | 0 | 0
F1 | 353.85 | 86.05 | 17 | 5 | SW17 | 4 | 0
CONTROL | 27.20 | 67.00 | 1 | 4 | SW18 | 2 | 7
Q | 46.24 | 67.00 | 2 | 4 | SW19 | 6 | 7
W | 65.28 | 67.00 | 3 | 4 | SW20 | 1 | 1
E | 84.32 | 67.00 | 4 | 4 | SW21 | 6 | 1
R | 103.36 | 67.00 | 5 | 4 | SW22 | 1 | 2
T | 122.40 | 67.00 | 6 | 4 | SW23 | 6 | 2
Y | 141.44 | 67.00 | 7 | 4 | SW24 | 1 | 3
U | 160.48 | 67.00 | 8 | 4 | SW25 | 6 | 3
I | 179.52 | 67.00 | 9 | 4 | SW26 | 1 | 4
O | 198.56 | 67.00 | 10 | 4 | SW27 | 6 | 4
P | 217.60 | 67.00 | 11 | 4 | SW28 | 1 | 5
@ | 236.64 | 67.00 | 12 | 4 | SW29 | 6 | 5
* | 255.68 | 67.00 | 13 | 4 | SW30 | 1 | 6
up arrow | 274.72 | 67.00 | 14 | 4 | SW31 | 6 | 6
RESTORE | 293.76 | 67.00 | 15 | 4 | SW32 | GND | RESTORE
F3 | 353.85 | 67.00 | 16 | 4 | SW33 | 5 | 0
RUN | 12.80 | 47.95 | 1 | 3 | SW34 | 7 | 7
SHIFT LOCK | 31.84 | 47.95 | 2 | 3 | SW35 | 7 | 1
A | 50.88 | 47.95 | 3 | 3 | SW36 | 2 | 1
S | 69.92 | 47.95 | 4 | 3 | SW37 | 5 | 1
D | 88.96 | 47.95 | 5 | 3 | SW38 | 2 | 2
F | 108.00 | 47.95 | 6 | 3 | SW39 | 5 | 2
G | 127.04 | 47.95 | 7 | 3 | SW40 | 2 | 3
H | 146.08 | 47.95 | 8 | 3 | SW41 | 5 | 3
J | 165.12 | 47.95 | 9 | 3 | SW42 | 2 | 4
K | 184.16 | 47.95 | 10 | 3 | SW43 | 5 | 4
L | 203.20 | 47.95 | 11 | 3 | SW44 | 2 | 5
[ | 222.24 | 47.95 | 12 | 3 | SW45 | 5 | 5
] | 241.28 | 47.95 | 13 | 3 | SW46 | 2 | 6
equals | 260.32 | 47.95 | 14 | 3 | SW47 | 5 | 6
RETURN | 288.88 | 47.95 | 15 | 3 | SW48 | 1 | 0
F5 | 353.85 | 47.95 | 16 | 3 | SW49 | 6 | 0
C= | 12.80 | 28.90 | 1 | 2 | SW50 | 5 | 7
Shift Left | 41.36 | 28.90 | 2 | 2 | SW51 | 7 | 1
Z | 60.40 | 28.90 | 3 | 2 | SW52 | 4 | 1
X | 79.44 | 28.90 | 4 | 2 | SW53 | 7 | 2
C | 98.48 | 28.90 | 5 | 2 | SW54 | 4 | 2
V | 117.52 | 28.90 | 6 | 2 | SW55 | 7 | 3
B | 136.56 | 28.90 | 7 | 2 | SW56 | 4 | 3
N | 155.60 | 28.90 | 8 | 2 | SW57 | 7 | 4
M | 174.64 | 28.90 | 9 | 2 | SW58 | 4 | 4
, | 193.68 | 28.90 | 10 | 2 | SW59 | 7 | 5
. | 212.72 | 28.90 | 11 | 2 | SW60 | 4 | 5
/ | 231.76 | 28.90 | 12 | 2 | SW61 | 7 | 6
Shift Right | 260.32 | 28.90 | 13 | 2 | SW62 | 4 | 6
CRSR up/dn | 279.36 | 28.90 | 14 | 2 | SW63 | 7 | 0
CRSR l/r | 298.40 | 28.90 | 15 | 2 | SW64 | 2 | 0
F7 | 353.85 | 28.90 | 16 | 2 | SW65 | 3 | 0
Space | 141.38 | 9.85 | 1 | 1 | SW66 | 4 | 7

Sheet: Mounting holes
PCB y | 96.4
Width x | 385.60
Width y | 126.70
Drill diameter | 4.65
Distance y | 114.25
Distance box | 101.10
x1 | 34.12
x2 | 97.33
x3 | 160.82
x4 | 224.77
x5 | 288.27
x6 | 351.47
y1 | -8.925
y2 | 105.325
top | 111.55
bottom | -15.15
top box | 98.75
bottom box | -2.35
