svenpetersen1965/C64-Keyboard/C64 Keyboard with Hot Swap Sockets/Rev. 2/excel/Keyboard_C64_HotSwap.csv

Qty | Value | Device | Package | Parts | Description | KEY
2 |  | CLOSED | CP_CL | JP1, JP2 | Closed Cutpad
1 |  | OPEN | CP_OP | JP3 | open Cutpad
1 |  | PINHD-1X2/90 | 1X02/90 | J4
2 |  | PINHD-1X3/90 | 1X03/90 | J3, J8
2 |  | PINHD-1X4/90 | 1X04/90 | J5, J7
2 |  | PINHD-1X590° | 1X05/90 | J2, J6
1 |  | PINHD-2X10WH | 2X10WH | J1
1 | 1000u/16V | C30X16L | C30X16L | C4
1 | 100R | R-0805 | 0805 | R1
4 | 100n | C-0805 | 0805 | C1, C2, C3, C5
3 | 100n | CAP010805 | 0805 | C6, C8, C9
11 | 10k | R-0805 | 0805 | R2, R3, R5, R7, R8, R9, R10, R12, R13, R14, R15
2 | 27k | R-0805 | 0805 | R4, R20
1 | 330R | RES040805 | 0805 | R11
1 | 33R | R-0805 | 0805 | R19
1 | 470R | R-0805 | 0805 | R16
1 | 47k | RN08 | RN-9 | RN1
1 | 4k7 | R-0805 | 0805 | R18
1 | 4u7 | CAP010805 | 0805 | C7
1 | 74HC123D | 74123 | SO-16 | IC2
3 | BC847B | BC846 | SOT23 | Q1, Q3, Q5
2 | LL4148 | LL4148 | SOD80C | D1, D2
1 | MX+LEDHSWP | MX+LEDHSWP | CHERRYMX_HSWP_LD | SW35 |  | SH.LOCK
1 | MXHOTSWAP | MXHOTSWAP | CHERRYMX_HOTSWAP | SW30 |  | *
1 | MXHOTSWAP | MXHOTSWAP | CHERRYMX_HOTSWAP | SW12 |  | +
1 | MXHOTSWAP | MXHOTSWAP | CHERRYMX_HOTSWAP | SW13 |  | -
1 | MXHOTSWAP | MXHOTSWAP | CHERRYMX_HOTSWAP | SW61 |  | /
1 | MXHOTSWAP | MXHOTSWAP | CHERRYMX_HOTSWAP | SW11 |  | 0
1 | MXHOTSWAP | MXHOTSWAP | CHERRYMX_HOTSWAP | SW2 |  | 1
1 | MXHOTSWAP | MXHOTSWAP | CHERRYMX_HOTSWAP | SW3 |  | 2
1 | MXHOTSWAP | MXHOTSWAP | CHERRYMX_HOTSWAP | SW4 |  | 3
1 | MXHOTSWAP | MXHOTSWAP | CHERRYMX_HOTSWAP | SW5 |  | 4
1 | MXHOTSWAP | MXHOTSWAP | CHERRYMX_HOTSWAP | SW6 |  | 5
1 | MXHOTSWAP | MXHOTSWAP | CHERRYMX_HOTSWAP | SW7 |  | 6
1 | MXHOTSWAP | MXHOTSWAP | CHERRYMX_HOTSWAP | SW8 |  | 7
1 | MXHOTSWAP | MXHOTSWAP | CHERRYMX_HOTSWAP | SW9 |  | 8
1 | MXHOTSWAP | MXHOTSWAP | CHERRYMX_HOTSWAP | SW10 |  | 9
1 | MXHOTSWAP | MXHOTSWAP | CHERRYMX_HOTSWAP | SW47 |  | =
1 | MXHOTSWAP | MXHOTSWAP | CHERRYMX_HOTSWAP | SW29 |  | @
1 | MXHOTSWAP | MXHOTSWAP | CHERRYMX_HOTSWAP | SW36 |  | A
1 | MXHOTSWAP | MXHOTSWAP | CHERRYMX_HOTSWAP | SW56 |  | B
1 | MXHOTSWAP | MXHOTSWAP | CHERRYMX_HOTSWAP | SW54 |  | C
1 | MXHOTSWAP | MXHOTSWAP | CHERRYMX_HOTSWAP | SW50 |  | C=
1 | MXHOTSWAP | MXHOTSWAP | CHERRYMX_HOTSWAP | SW64 |  | CRSR.lr
1 | MXHOTSWAP | MXHOTSWAP | CHERRYMX_HOTSWAP | SW63 |  | CRSR.ud
2 | MXHOTSWAP | MXHOTSWAP | CHERRYMX_HOTSWAP | SW18, SW18A |  | CTRL
1 | MXHOTSWAP | MXHOTSWAP | CHERRYMX_HOTSWAP | SW38 |  | D
1 | MXHOTSWAP | MXHOTSWAP | CHERRYMX_HOTSWAP | SW16 |  | DEL
1 | MXHOTSWAP | MXHOTSWAP | CHERRYMX_HOTSWAP | SW21 |  | E
1 | MXHOTSWAP | MXHOTSWAP | CHERRYMX_HOTSWAP | SW39 |  | F
2 | MXHOTSWAP | MXHOTSWAP | CHERRYMX_HOTSWAP | SW17, SW17A |  | F1
2 | MXHOTSWAP | MXHOTSWAP | CHERRYMX_HOTSWAP | SW33, SW33A |  | F3
2 | MXHOTSWAP | MXHOTSWAP | CHERRYMX_HOTSWAP | SW49, SW49A |  | F5
2 | MXHOTSWAP | MXHOTSWAP | CHERRYMX_HOTSWAP | SW65, SW65A |  | F7
1 | MXHOTSWAP | MXHOTSWAP | CHERRYMX_HOTSWAP | SW40 |  | G
1 | MXHOTSWAP | MXHOTSWAP | CHERRYMX_HOTSWAP | SW41 |  | H
1 | MXHOTSWAP | MXHOTSWAP | CHERRYMX_HOTSWAP | SW15 |  | HOME
1 | MXHOTSWAP | MXHOTSWAP | CHERRYMX_HOTSWAP | SW26 |  | I
1 | MXHOTSWAP | MXHOTSWAP | CHERRYMX_HOTSWAP | SW42 |  | J
1 | MXHOTSWAP | MXHOTSWAP | CHERRYMX_HOTSWAP | SW43 |  | K
1 | MXHOTSWAP | MXHOTSWAP | CHERRYMX_HOTSWAP | SW44 |  | L
1 | MXHOTSWAP | MXHOTSWAP | CHERRYMX_HOTSWAP | SW1 |  | LEFT ARR
1 | MXHOTSWAP | MXHOTSWAP | CHERRYMX_HOTSWAP | SW58 |  | M
1 | MXHOTSWAP | MXHOTSWAP | CHERRYMX_HOTSWAP | SW57 |  | N
1 | MXHOTSWAP | MXHOTSWAP | CHERRYMX_HOTSWAP | SW68 |  | Next
1 | MXHOTSWAP | MXHOTSWAP | CHERRYMX_HOTSWAP | SW27 |  | O
1 | MXHOTSWAP | MXHOTSWAP | CHERRYMX_HOTSWAP | SW28 |  | P
1 | MXHOTSWAP | MXHOTSWAP | CHERRYMX_HOTSWAP | SW67 |  | Prev
1 | MXHOTSWAP | MXHOTSWAP | CHERRYMX_HOTSWAP | SW19 |  | Q
1 | MXHOTSWAP | MXHOTSWAP | CHERRYMX_HOTSWAP | SW22 |  | R
2 | MXHOTSWAP | MXHOTSWAP | CHERRYMX_HOTSWAP | SW32, SW32A |  | RESTORE
1 | MXHOTSWAP | MXHOTSWAP | CHERRYMX_HOTSWAP | SW48 |  | RETURN
1 | MXHOTSWAP | MXHOTSWAP | CHERRYMX_HOTSWAP | SW34 |  | RUN
1 | MXHOTSWAP | MXHOTSWAP | CHERRYMX_HOTSWAP | SW37 |  | S
2 | MXHOTSWAP | MXHOTSWAP | CHERRYMX_HOTSWAP | SW51, SW51A |  | SH.LEFT
2 | MXHOTSWAP | MXHOTSWAP | CHERRYMX_HOTSWAP | SW62, SW62A |  | SH.RIGHT
1 | MXHOTSWAP | MXHOTSWAP | CHERRYMX_HOTSWAP | SW66 |  | SPACE
1 | MXHOTSWAP | MXHOTSWAP | CHERRYMX_HOTSWAP | SW23 |  | T
1 | MXHOTSWAP | MXHOTSWAP | CHERRYMX_HOTSWAP | SW25 |  | U
1 | MXHOTSWAP | MXHOTSWAP | CHERRYMX_HOTSWAP | SW31 |  | UP ARR
1 | MXHOTSWAP | MXHOTSWAP | CHERRYMX_HOTSWAP | SW55 |  | V
1 | MXHOTSWAP | MXHOTSWAP | CHERRYMX_HOTSWAP | SW20 |  | W
1 | MXHOTSWAP | MXHOTSWAP | CHERRYMX_HOTSWAP | SW53 |  | X
1 | MXHOTSWAP | MXHOTSWAP | CHERRYMX_HOTSWAP | SW24 |  | Y
1 | MXHOTSWAP | MXHOTSWAP | CHERRYMX_HOTSWAP | SW52 |  | Z
1 | MXHOTSWAP | MXHOTSWAP | CHERRYMX_HOTSWAP | SW45 |  | [
1 | MXHOTSWAP | MXHOTSWAP | CHERRYMX_HOTSWAP | SW46 |  | ]
1 | MXHOTSWAP | MXHOTSWAP | CHERRYMX_HOTSWAP | SW59 |  | comma
1 | MXHOTSWAP | MXHOTSWAP | CHERRYMX_HOTSWAP | SW60 |  | period
1 | MXHOTSWAP | MXHOTSWAP | CHERRYMX_HOTSWAP | SW14 |  | £
1 | OPEN_SOURCE_HW | OPEN_SOURCE_HW | OPENHW | U$90
1 | PCF8575-MODULE | PCF8575-MODUL | PCF8575MODUL | M1
1 | PRO_MICRO | PRO_MICRO | PRO_MICRO | M2
1 | RMP-14P/HT | RMP-14P/HT | RMP-14P/HT | SPK1
1 | SN74HC74D | 7474HC | SO-14 | IC1 | Dual D-Flip-Flop SO14
1 | TL7705ACD | TL7705ACD | SO8 | IC3
