svenpetersen1965/C64-Keyboard/3D printables/pictures/4583_-_USB_case_parts.JPG

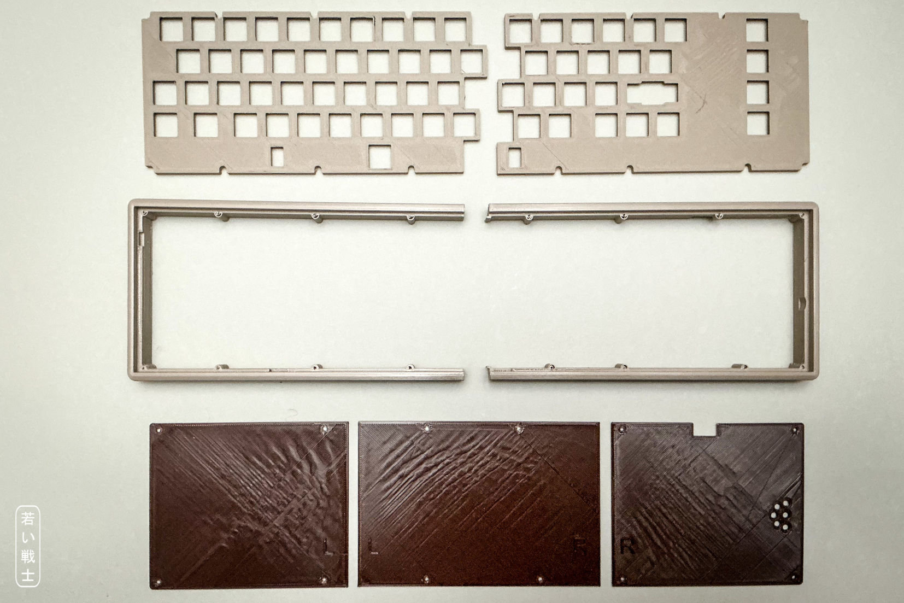
3D printables/pictures/4583_-_USB_case_parts.JPG
