svenpetersen1965/C64-Keyboard/3D printables/pictures/3991_-_C64KB_Mounting_frame.JPG

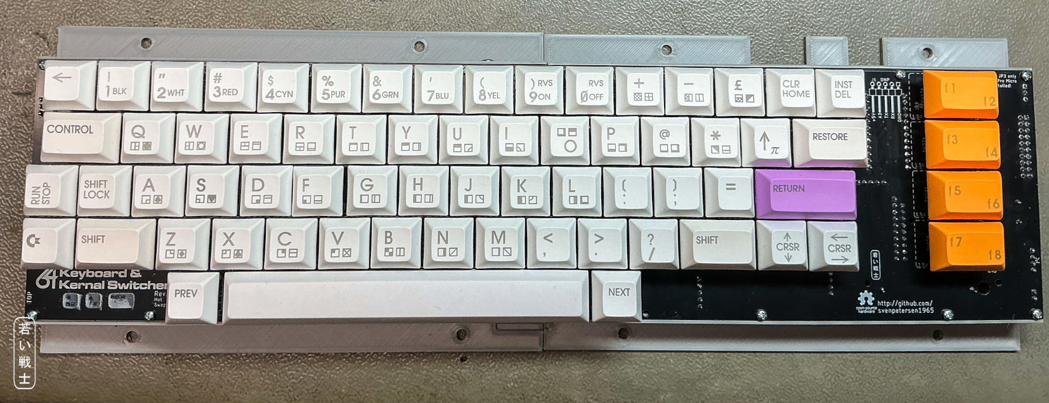
3D printables/pictures/3991_-_C64KB_Mounting_frame.JPG
