svenpetersen1965/C64-Keyboard/3D printables/pictures/4554_-_USB_case_Ultimate.JPG

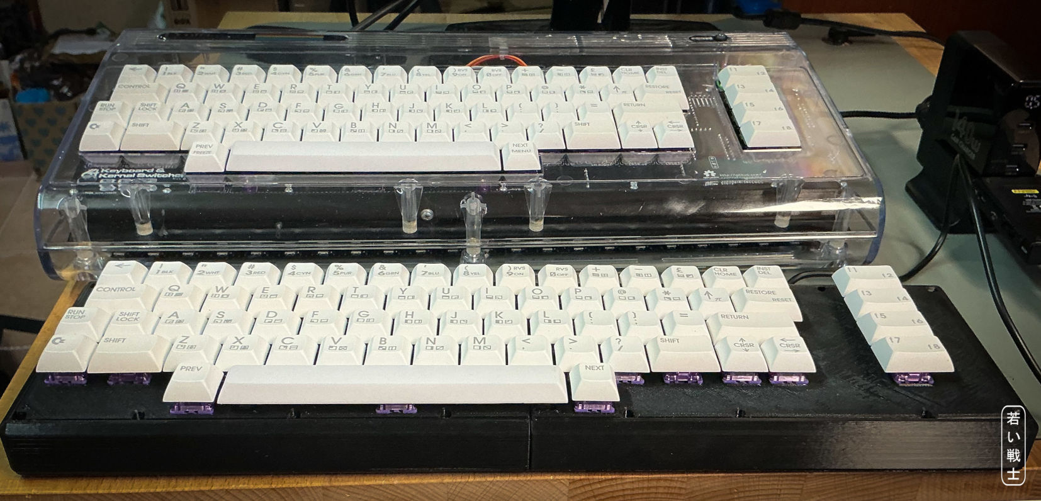
3D printables/pictures/4554_-_USB_case_Ultimate.JPG
