svenpetersen1965/C64-Keyboard/3D printables/pictures/4564_-_Switches_on_plate.JPG

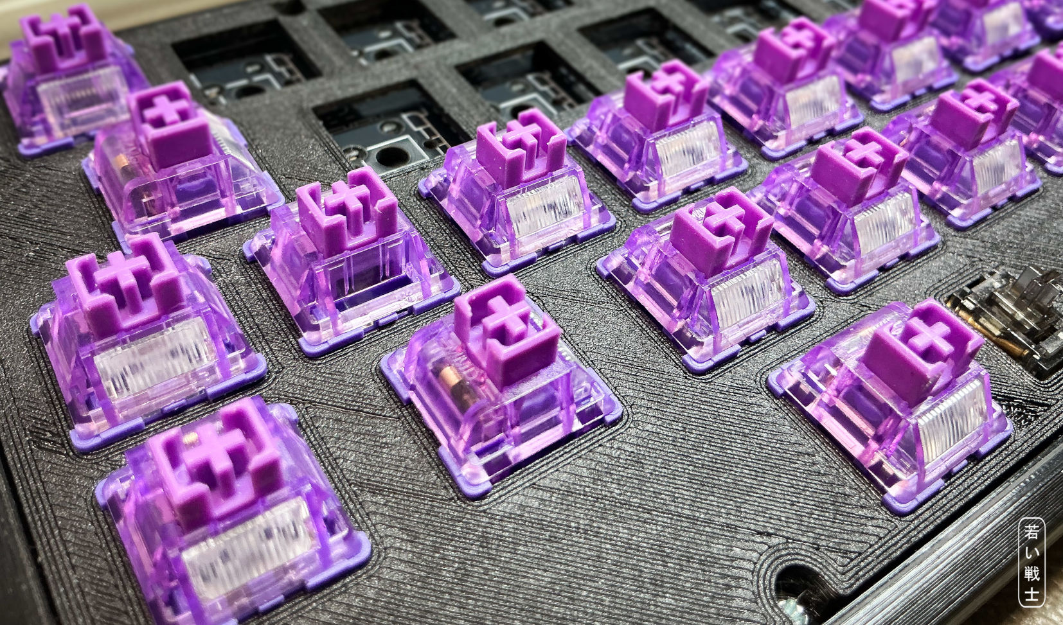
3D printables/pictures/4564_-_Switches_on_plate.JPG
