svenpetersen1965/C64-Keyboard/C64 Keyboard Standard Version/Rev. 0/pictures/0272_-_stabilizer_installation_top.JPG

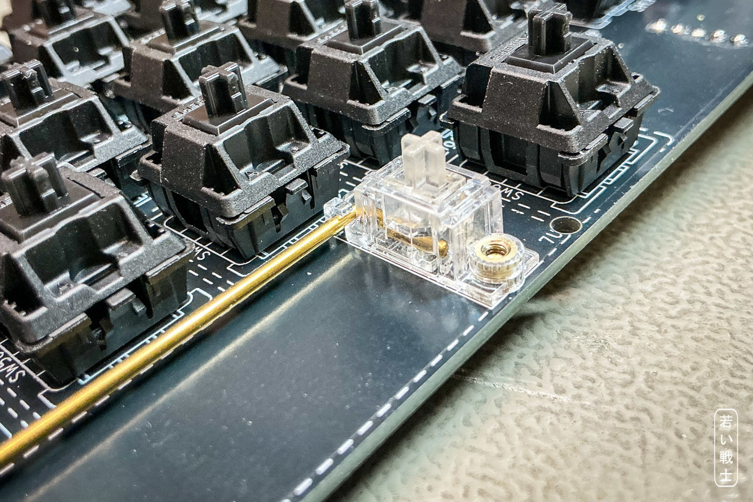
C64 Keyboard Standard Version/Rev. 0/pictures/0272_-_stabilizer_installation_top.JPG
