svenpetersen1965/C64-Keyboard/C64 Keyboard Standard Version/Rev. 0/pictures/0285_-_kb_cable_installed.JPG

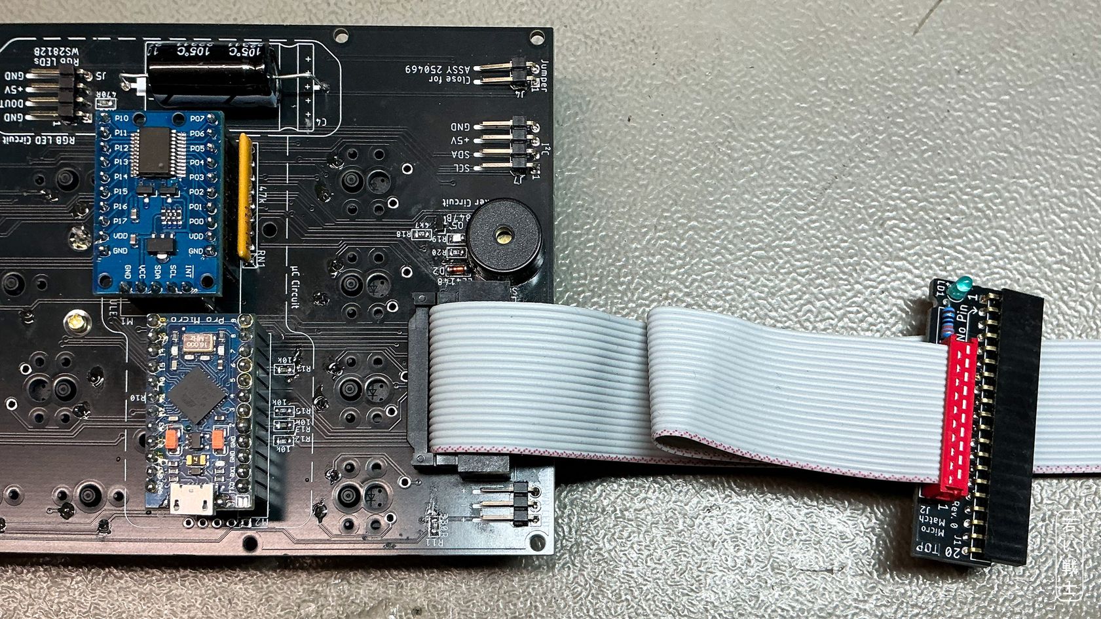
C64 Keyboard Standard Version/Rev. 0/pictures/0285_-_kb_cable_installed.JPG
