svenpetersen1965/C64-Keyboard/C64 Keyboard Standard Version/Rev. 0/pictures/0298_-_kb_installed_right.JPG

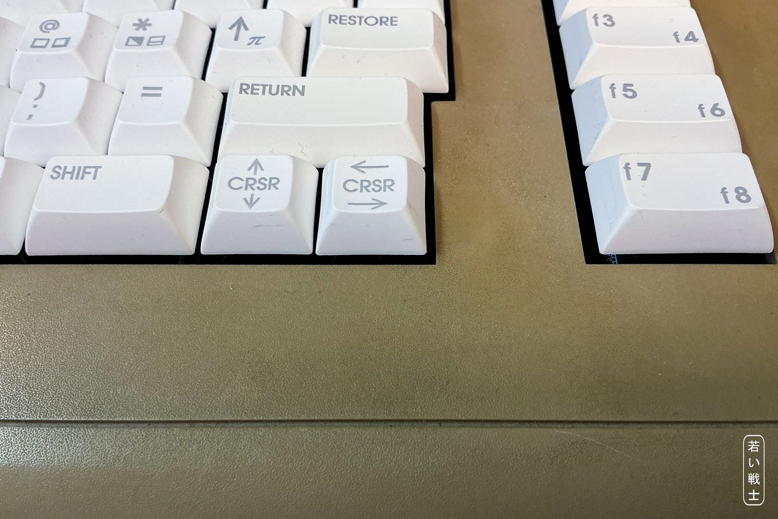
C64 Keyboard Standard Version/Rev. 0/pictures/0298_-_kb_installed_right.JPG
