svenpetersen1965/C64-Keyboard/C64 Keyboard Standard Version/Rev. 0/pictures/0299_-_kb_installed_left.JPG

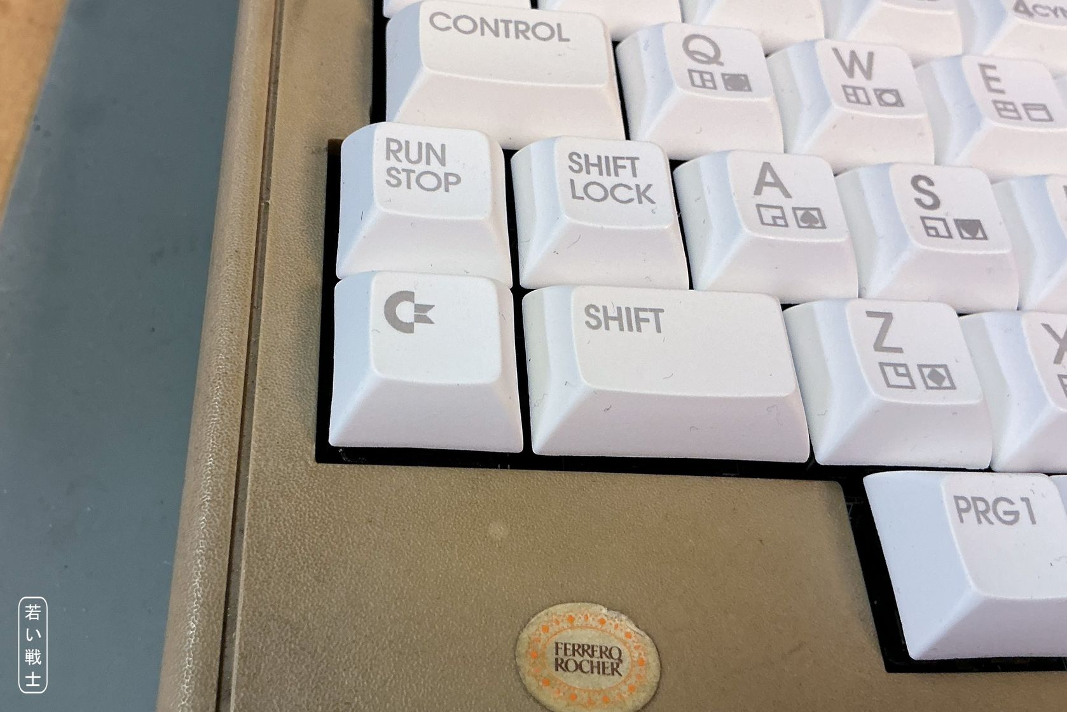
C64 Keyboard Standard Version/Rev. 0/pictures/0299_-_kb_installed_left.JPG
