svenpetersen1965/C64-Keyboard/C64 Keyboard Standard Version/Rev. 0/pictures/0300_-_kb_installed_bottom.JPG

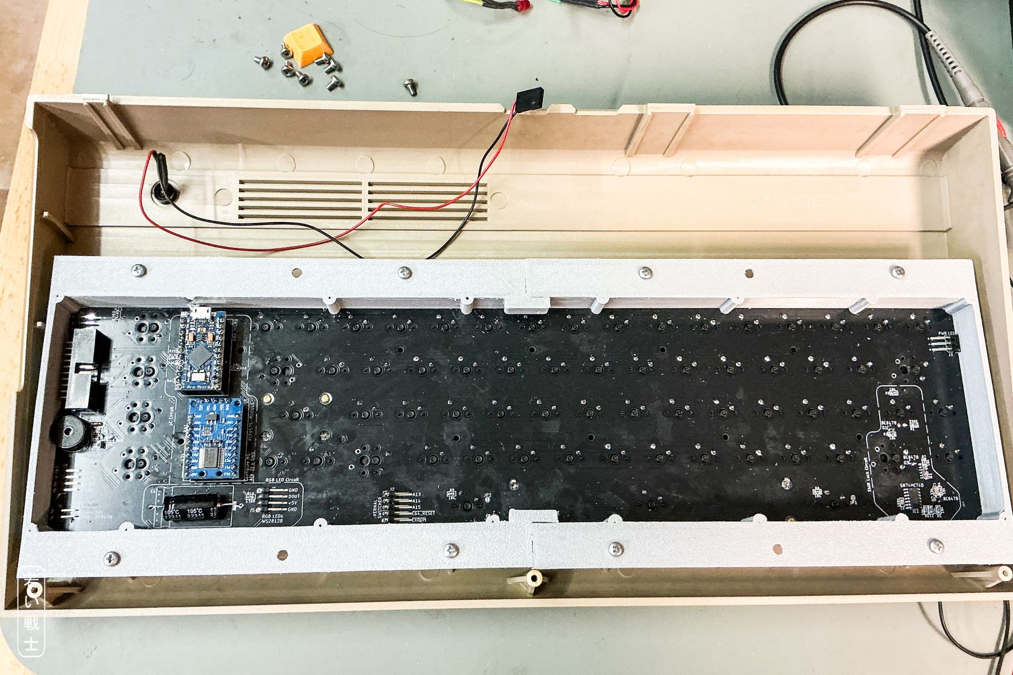
C64 Keyboard Standard Version/Rev. 0/pictures/0300_-_kb_installed_bottom.JPG
