svenpetersen1965/C64-Keyboard/C64 Keyboard Standard Version/Rev. 0/pictures/0301_-_kb_installed_C64C_clip_case.JPG

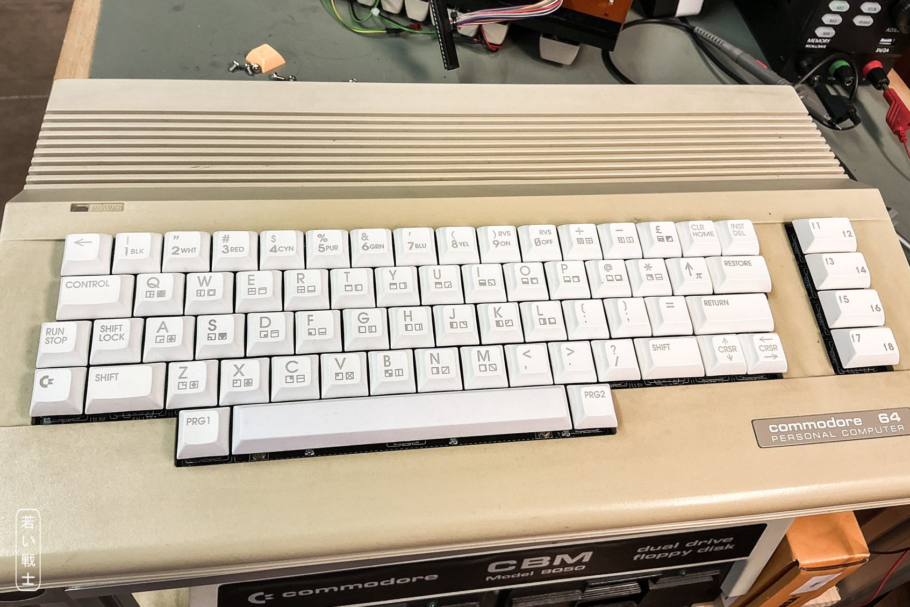
C64 Keyboard Standard Version/Rev. 0/pictures/0301_-_kb_installed_C64C_clip_case.JPG
