svenpetersen1965/C64-Keyboard/C64 Keyboard Standard Version/Rev. 0/pictures/0316_-_breadbin_installation_inside.JPG

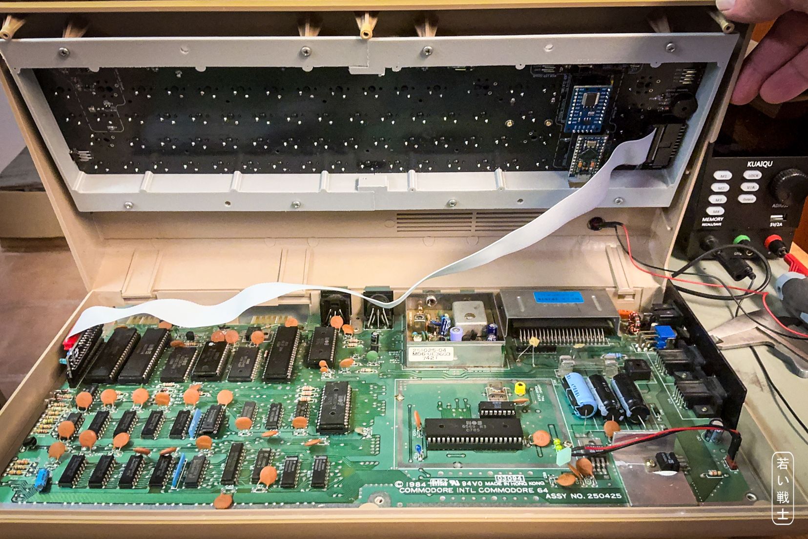
C64 Keyboard Standard Version/Rev. 0/pictures/0316_-_breadbin_installation_inside.JPG
