svenpetersen1965/C64-Keyboard/Keycaps/pictures/6078_-_C64_keyboard_UV_print_white.JPG

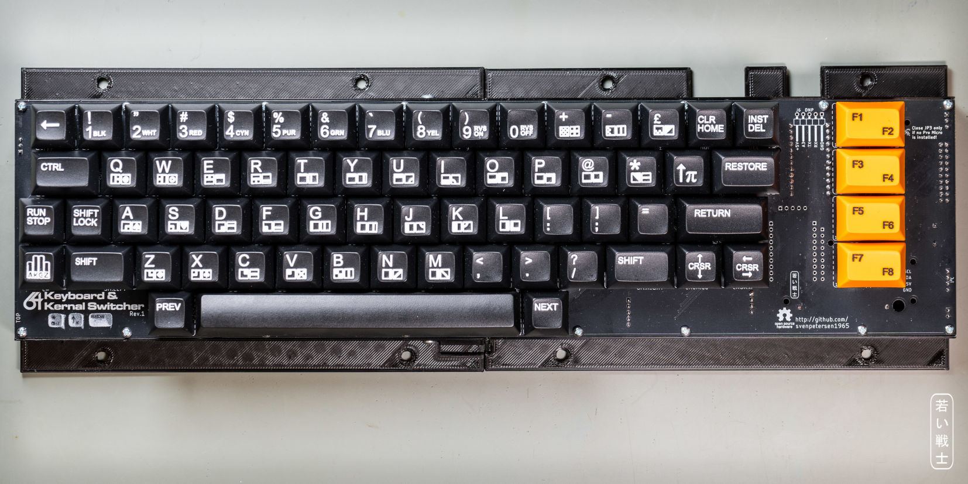
Keycaps/pictures/6078_-_C64_keyboard_UV_print_white.JPG
