svenpetersen1965/C64-Keyboard/pictures/3990_-_assembly_switches_stabilizers.JPG

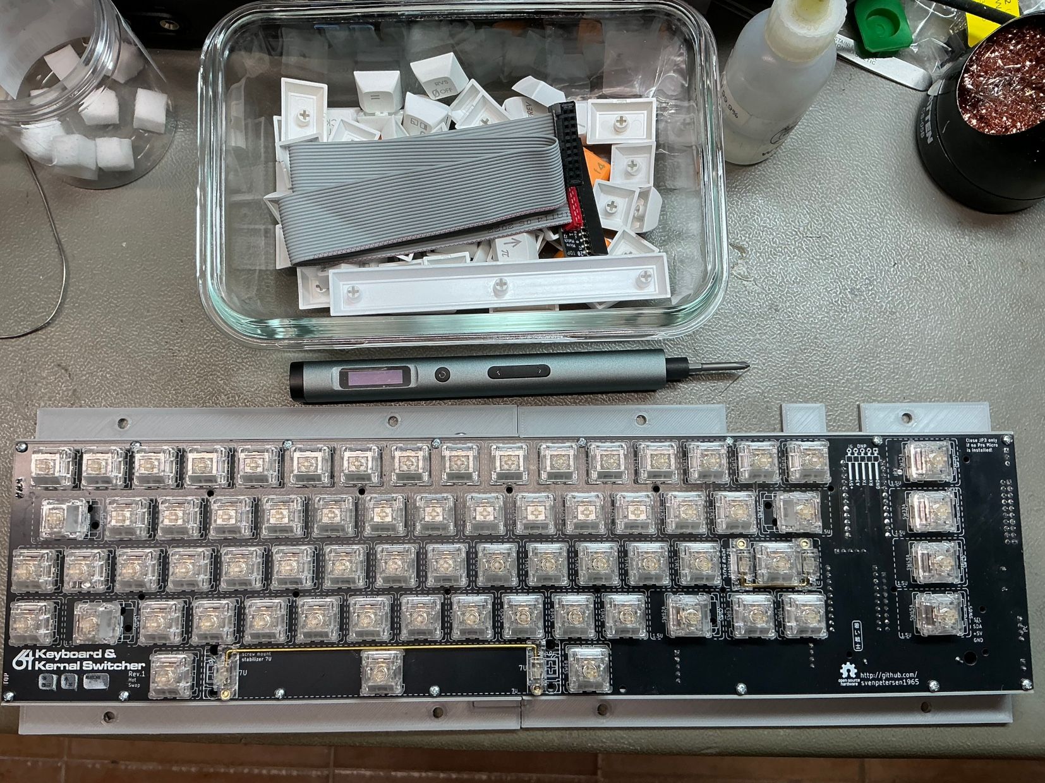
pictures/3990_-_assembly_switches_stabilizers.JPG
