svenpetersen1965/C64-Keyboard/C64 Keyboard Standard Version/Rev. 0/pictures/0284_-_KB_matrix_test.JPG

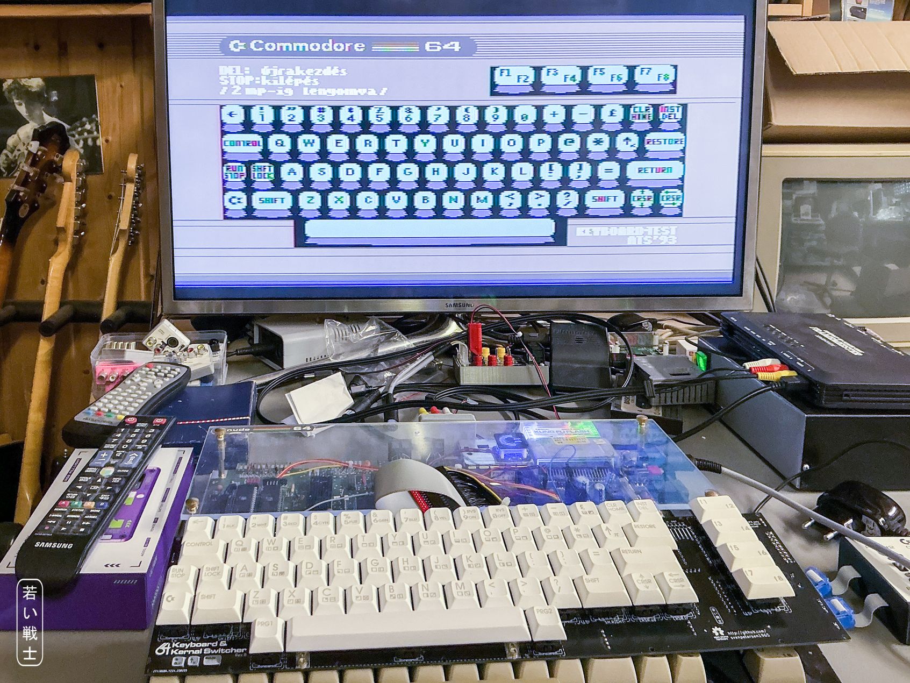
C64 Keyboard Standard Version/Rev. 0/pictures/0284_-_KB_matrix_test.JPG
