svenpetersen1965/C64-Keyboard/C64 Keyboard Standard Version/Rev. 0/pictures/4477_-_ultimate_button_test.JPG

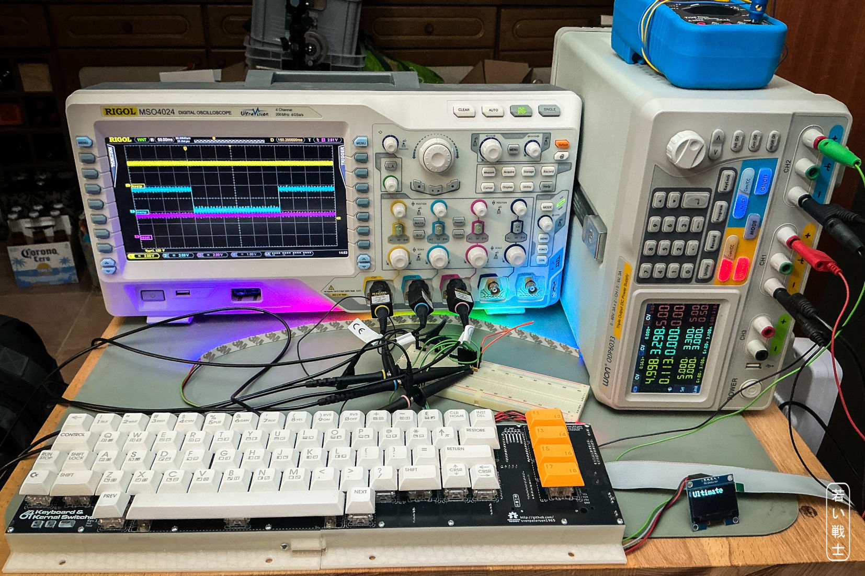
C64 Keyboard Standard Version/Rev. 0/pictures/4477_-_ultimate_button_test.JPG
