svenpetersen1965/C64-Keyboard/Keycaps/uv_decal_wear_test/UV_decal_after_isopropanol.JPG

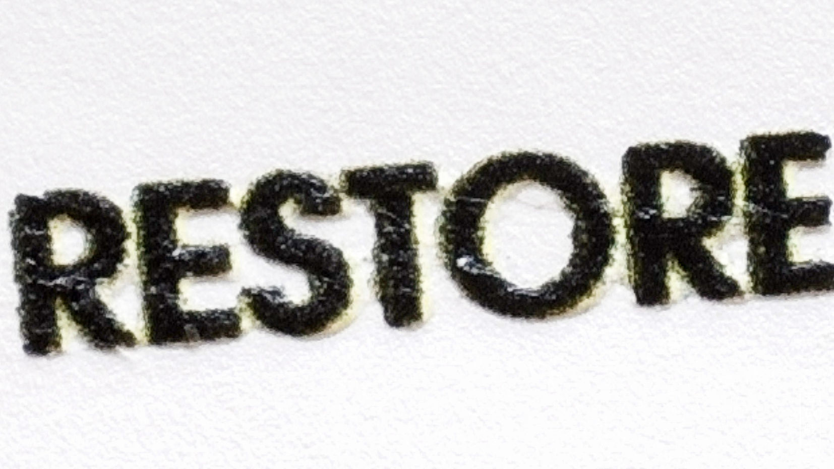
Keycaps/uv_decal_wear_test/UV_decal_after_isopropanol.JPG
