svenpetersen1965/C64-Keyboard/Keycaps/uv_decal_wear_test/UV_decal_embossed.JPG

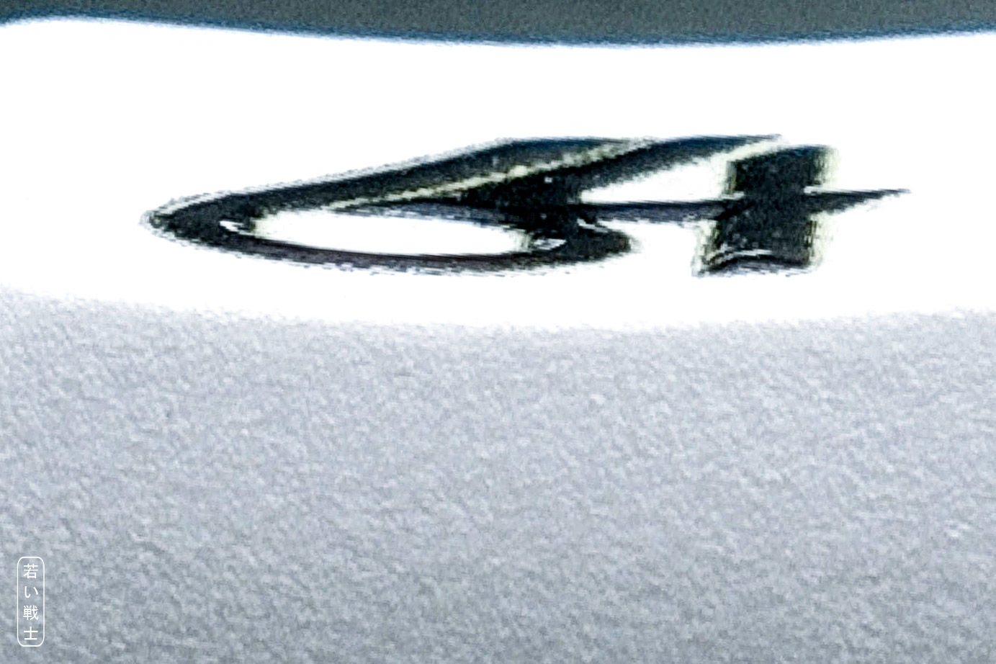
Keycaps/uv_decal_wear_test/UV_decal_embossed.JPG
