svenpetersen1965/C64-Keyboard/C64 Keyboard connector PCB/Rev. 0/pdf/C64KBConPCB_v0.pdf

# Project Documentation

## C64 Keyboard Connector PCB

## Project number: 224

## Revision: 0

## Date: 04.06.2026

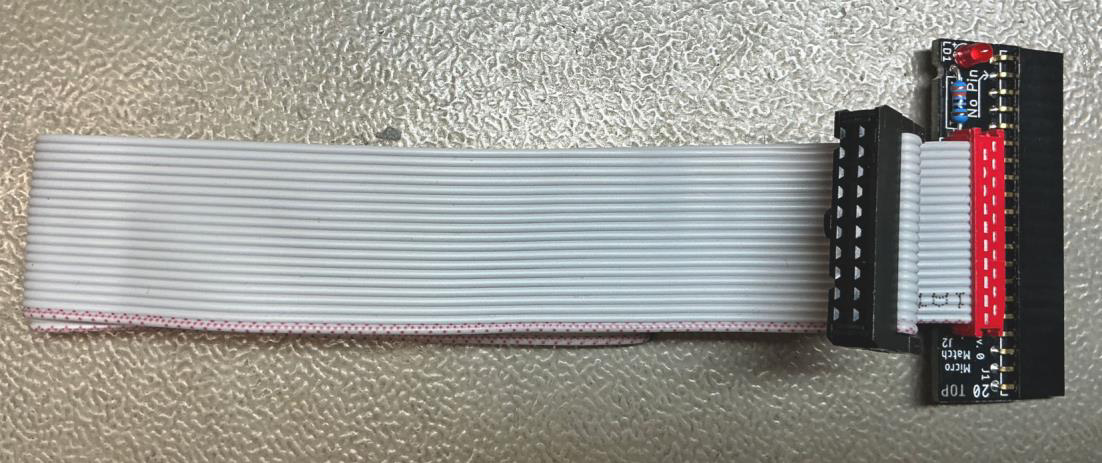
[picture p375: figure]
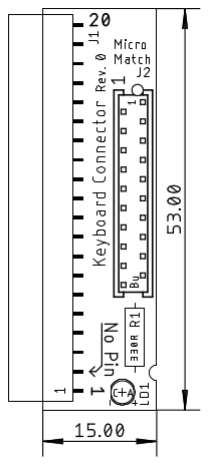
[picture p376: figure]

C64KBConPCB_ModD.docx | | 05.06.2026 16:21
Drafted by Sven Petersen | Page 1 of 3 | Doc.-No.: 224-6-01-00

### C64 Keyboard Connector PCB Rev. 0

### Module Description

## Introduction

The purpose of this PCB is to connect the C64 Keyboard (Project. No. 223 or 225) to the C64/Ultimate64 Keyboard Connector.

Figure 1: C64 Keyboard Connector PCB with ribbon cable

The connector for the ribbon cable is a MicroMatch series connector (red). They are low profile, so the cable does not collide with the side of the case when connected to a C64 long board. The C64 Keyboard has a 2x10p pin header, so the ribbon cable has two different types of connectors attached.

## Dimensions

Figure 2: Dimensions of the PCB

C64KBConPCB_ModD.docx | | 05.06.2026 16:21
Drafted by Sven Petersen | Page 2 of 3 | Doc.-No.: 224-6-01-00

## Pinouts

### J1 – Connector to mainboard

2.54mm pitch socket, 90°

Pin | Signal
1 GND
2 No pin
3 /RESTORE
4 +5V
5 ROW3
6 ROW6
7 ROW5
8 ROW4
9 ROW7
10 ROW2
11 ROW1
12 ROW0
13 COL0
14 COL6
15 COL5
16 COL4
17 COL3
18 COL2
19 COL1
20 COL7

### J2 – Ribbon Cable Connector

MicroMatch Socket, 20 pins

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

C64KBConPCB_ModD.docx | | 05.06.2026 16:21
Drafted by Sven Petersen | Page 3 of 3 | Doc.-No.: 224-6-01-00

## Cable

The cable is a 20p ribbon cable of 45cm with one side attached to a 2x10p IDC socket with strain relief on the keyboard side and a 20 pin MicroMatch connector (male) on the side of this PCB. The cable is shown in drawing number 224-3-01-00.

Both connector types are easy to attach, since they are both IDC (insulation-displacement contact), so you only require a vice to compress them, after the ribbon cable is positioned.

The length of 45cm is the longest possible, calculated for a C64 longboard (the keyboard connector is top left on the mainboard). For short boards, 30cm is long enough

## Revision History

### Rev. 0

- Working prototype

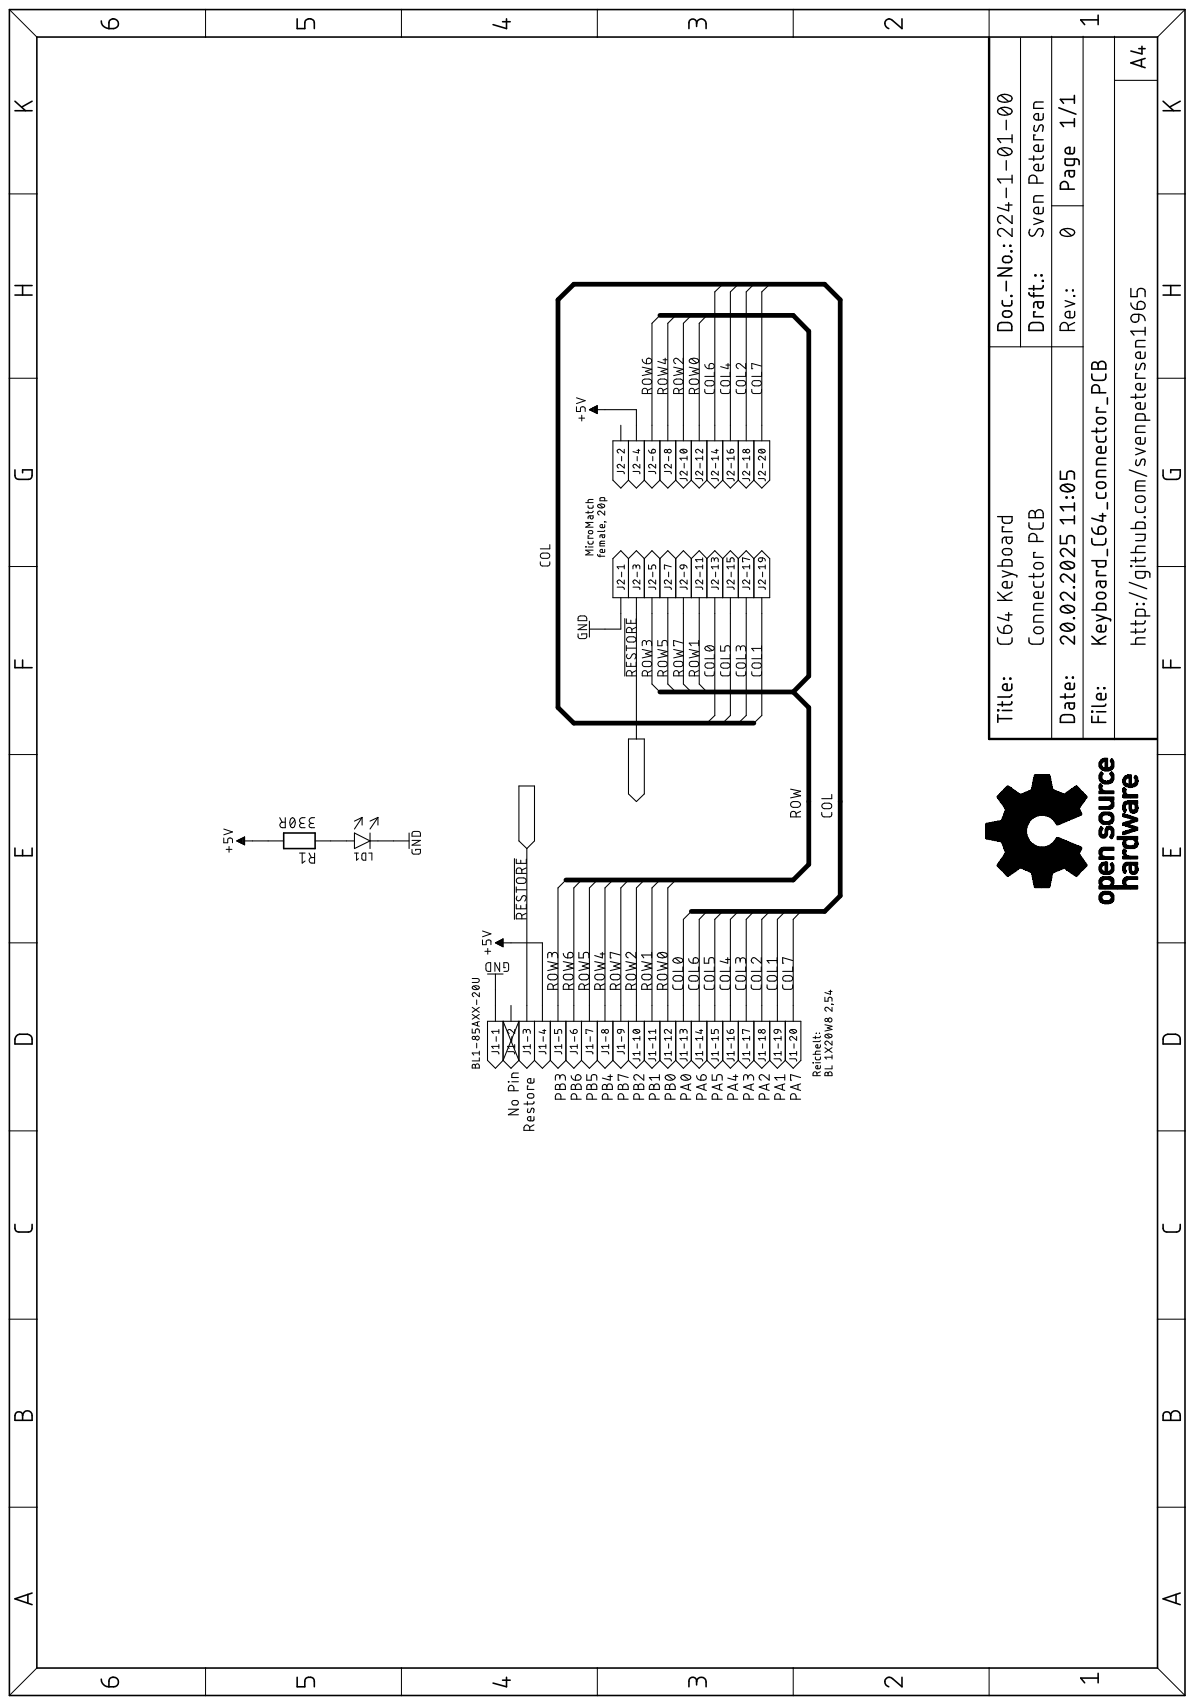
[picture p377: page 5]

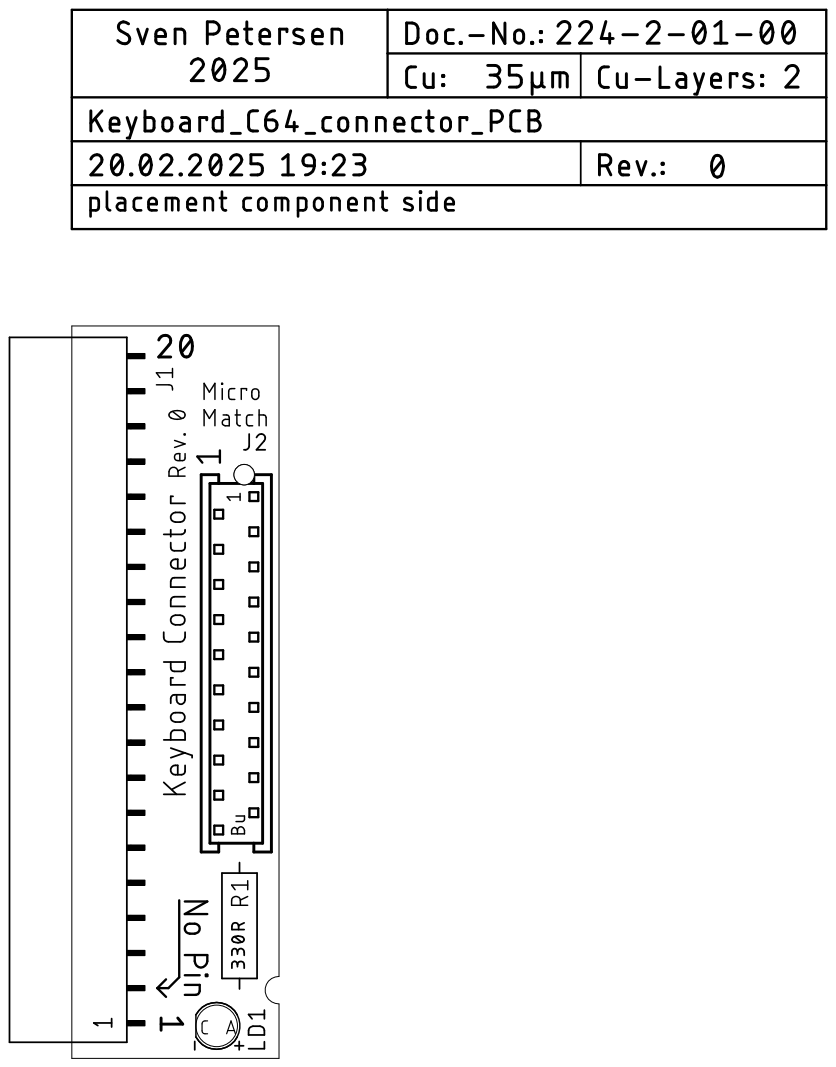
[picture p378: page 6]

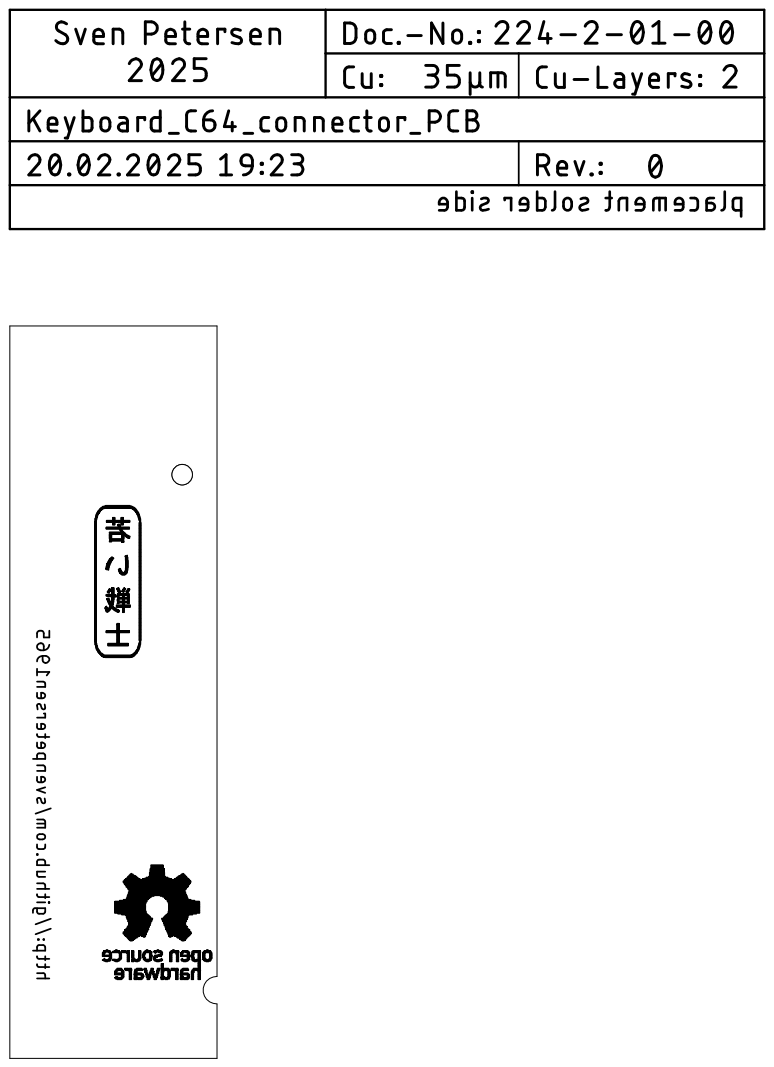
[picture p379: page 7]

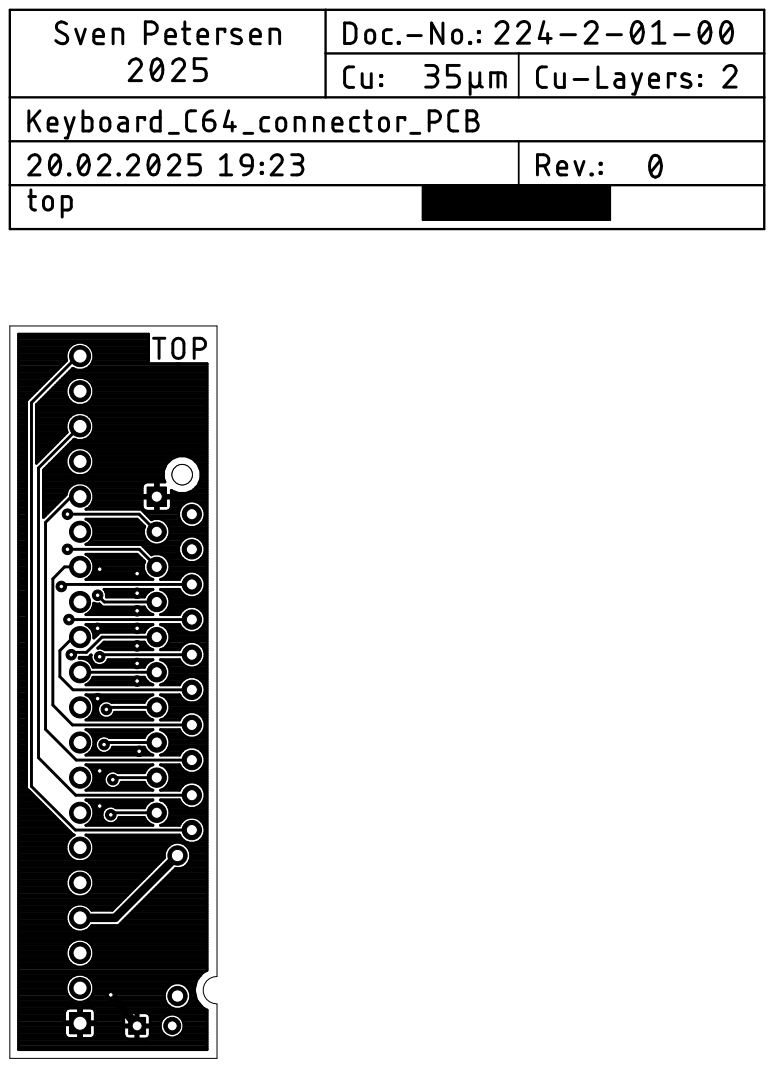
[picture p380: page 8]

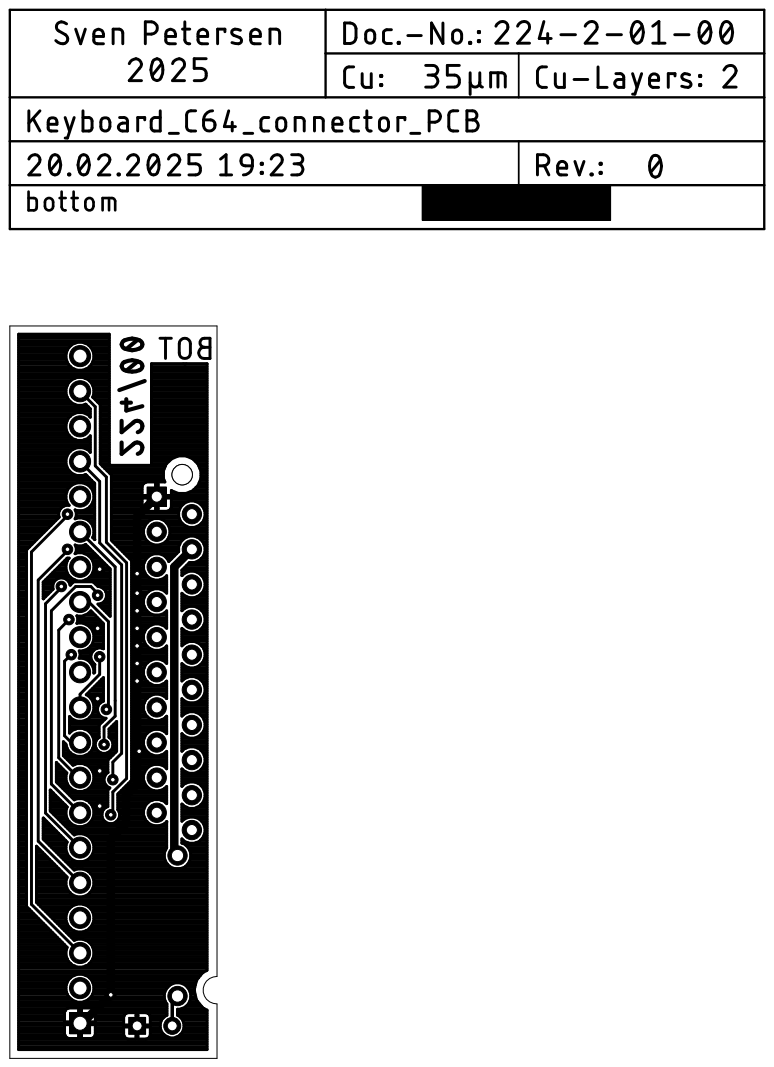
[picture p381: page 9]

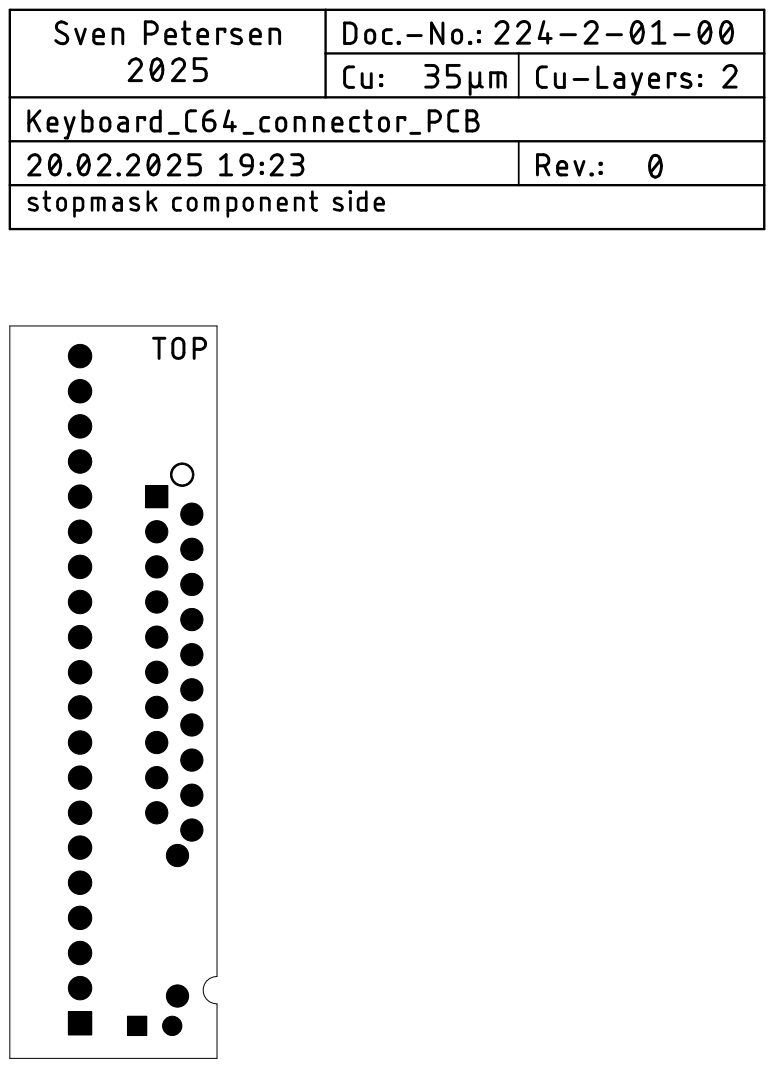
[picture p382: page 10]

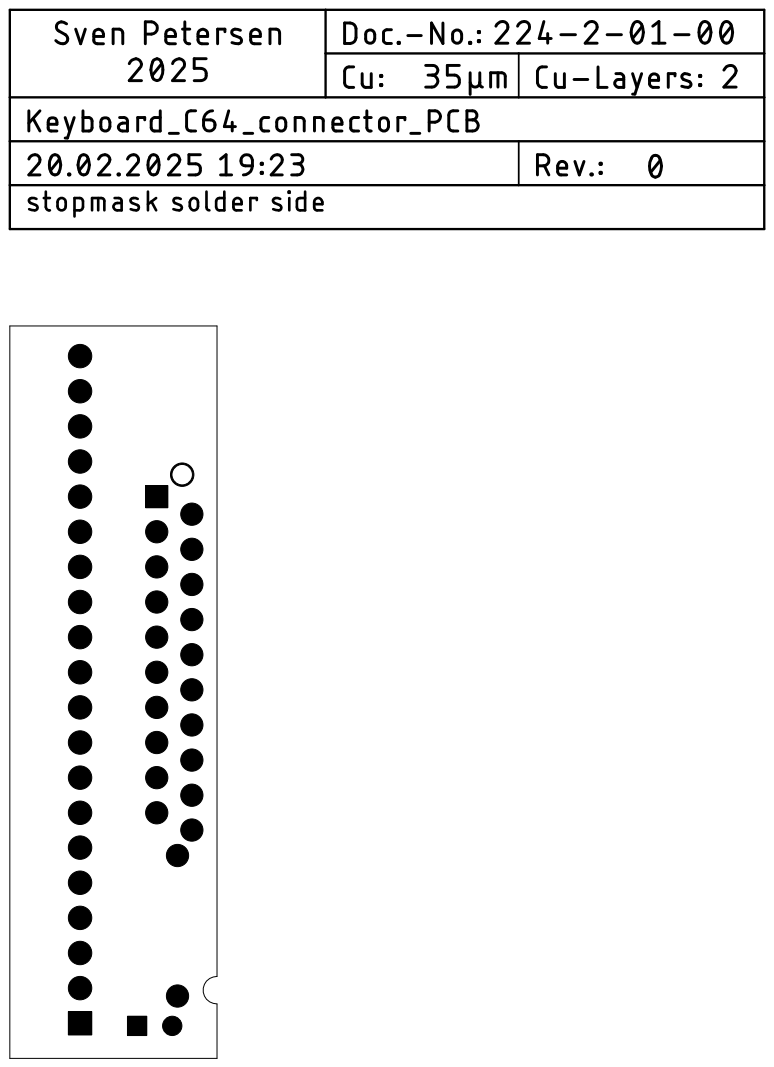
[picture p383: page 11]

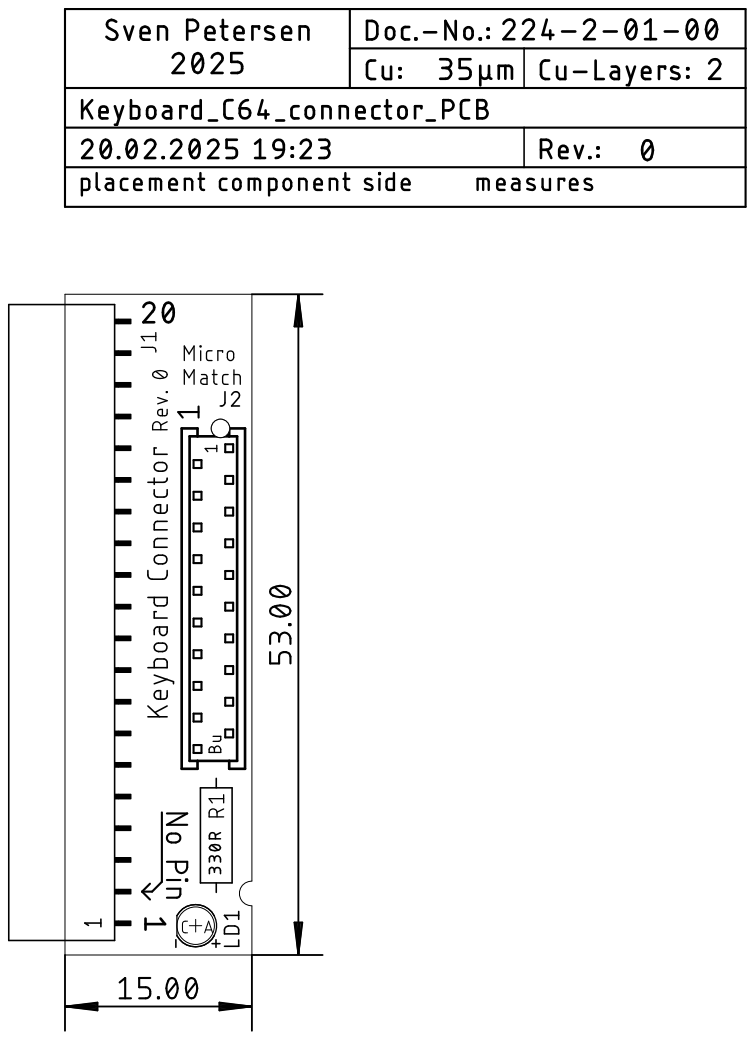
[picture p384: page 12]

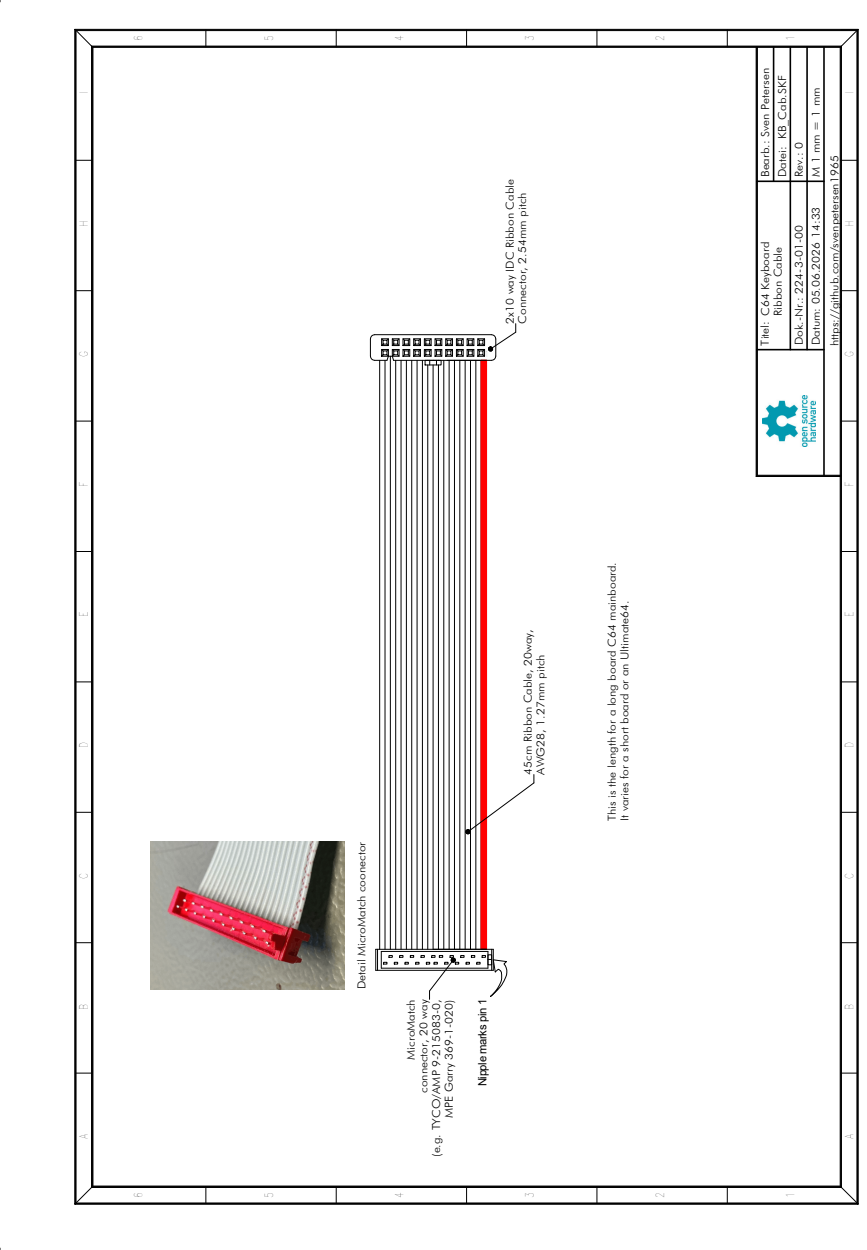
[picture p385: page 13]
Rev.: 0; Datei:; Titel:; Dok.-Nr.: 224-3-01-00; Datum: 05.06.2026 14:33; C64 Keyboard; Connector, 2.54mm pitch; MicroMatch; connector, 20 way; (e.g. TYCO/AMP 9-215083-0,; MPE Garry 369-1-020); 45cm Ribbon Cable, 20way,

Bearb.: Sven Petersen

Ribbon Cable KB_Cab.SKF

https://github.com/svenpetersen1965

2x10 way IDC Ribbon Cable

AWG28, 1.27mm pitch 1 Detail MicroMatch coonector

This is the length for a long board C64 mainboard.

It varies for a short board or an Ultimate64.

Nipple marks pin 1

Pos. Qty Value Footprint Ref.-No. Comment

1 1 224-2-01-00 2 Layer PCB Rev. 0 2 layer, Cu 35µ, HASL, 53.0mm x 15.0mm, 1.6mm FR4

### 1 LED, green, 3mm 3MM LD1 Standard LED, 3mm, green

1 330R R-10 R1 Metal film resistor, 1/4W & 10% or better

1 BL1-85AXX-20U BL1-85AXX-20U J1 1x20 pin socket connector, 90°, e.g. MPE Garry, Reichelt BL

1x20W8 2,54

1 369-1-020 or 2-215079-0 MICMA20B J2 20 pin MicroMatch, femal, PCB-mount, e.g. MPE Garry,

Reichelt MPE 369-1-020 or TE Connectivity 2-215079-0

1 45cm ribbon cable cable 20 way, AWG28, 1.27mm

1 IDC header Micro Match,

20-pin

cable Reichelt MPE 369-1-020 or TE Connectivity 9-215083-0

1 20-pin IDC socket with
strain relief, 2.54mm

cable e.g. Reichelt PFL 20

## C64 Keyboard Connector PCB Rev. 0

## Bill of Material Rev. 0.0

C64KB_ConPCB_BOM_v0_0.xlsx

Drafted by Sven Petersen Page 1 of 1

05.06.2026 16:45
Doc.No.: xxx-5-01-00.0
