svenpetersen1965/C64-Keyboard/C64 Keyboard Standard Version/Rev. 0/pdf/sch_brd.pdf

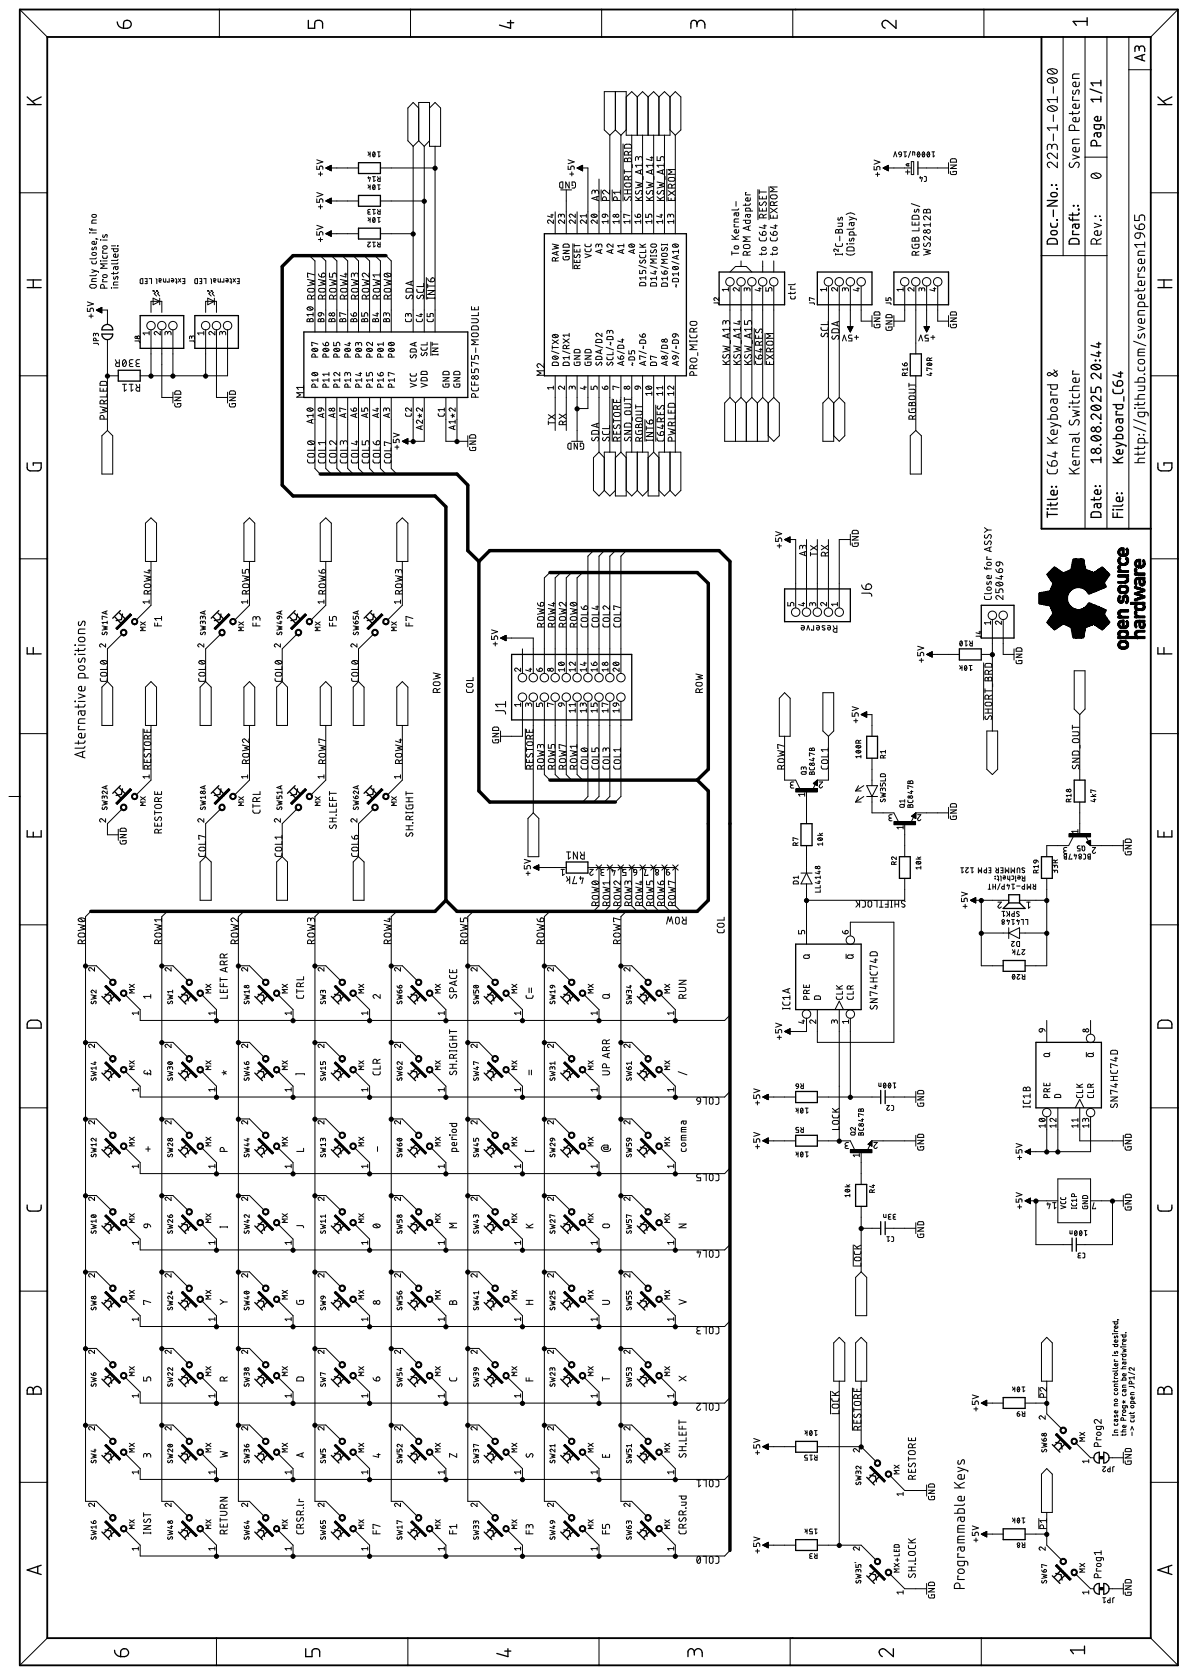
[picture p386: page 1]

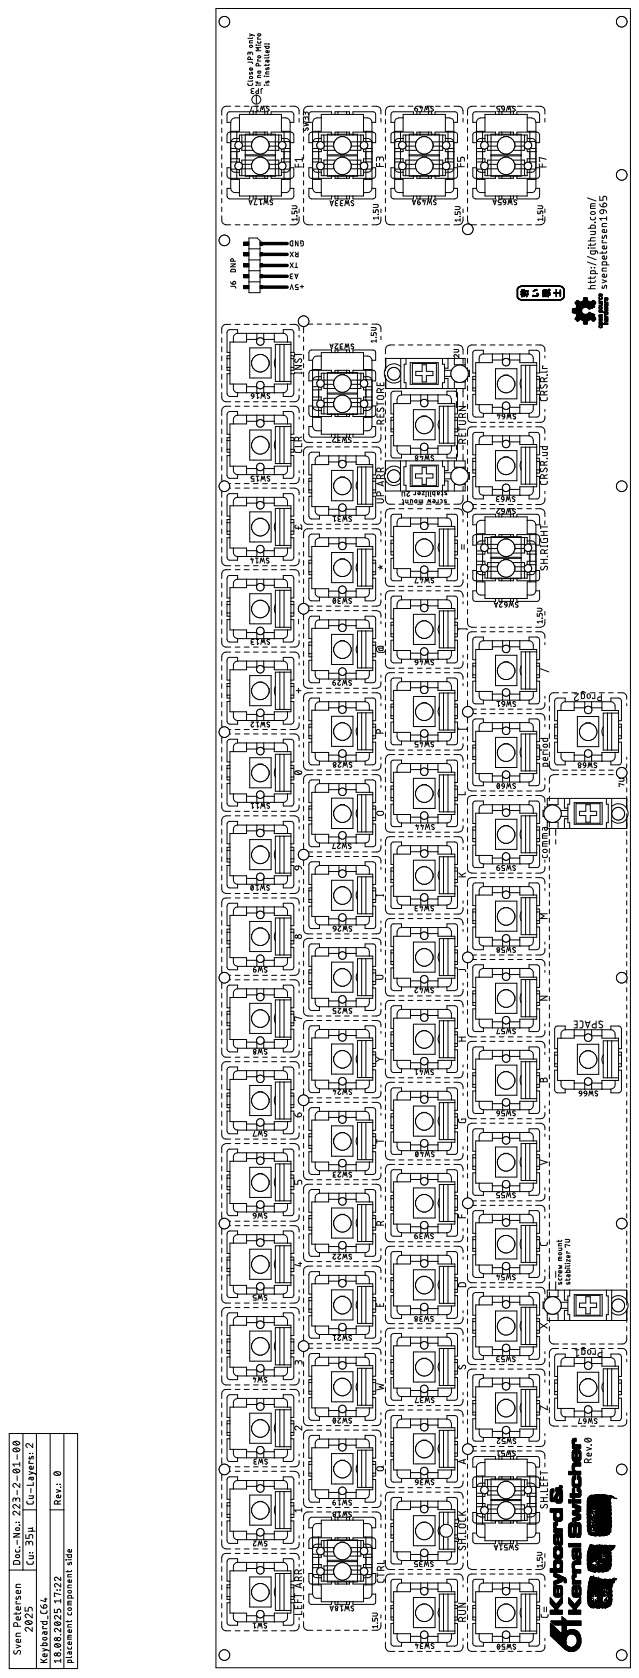
[picture p387: page 2]

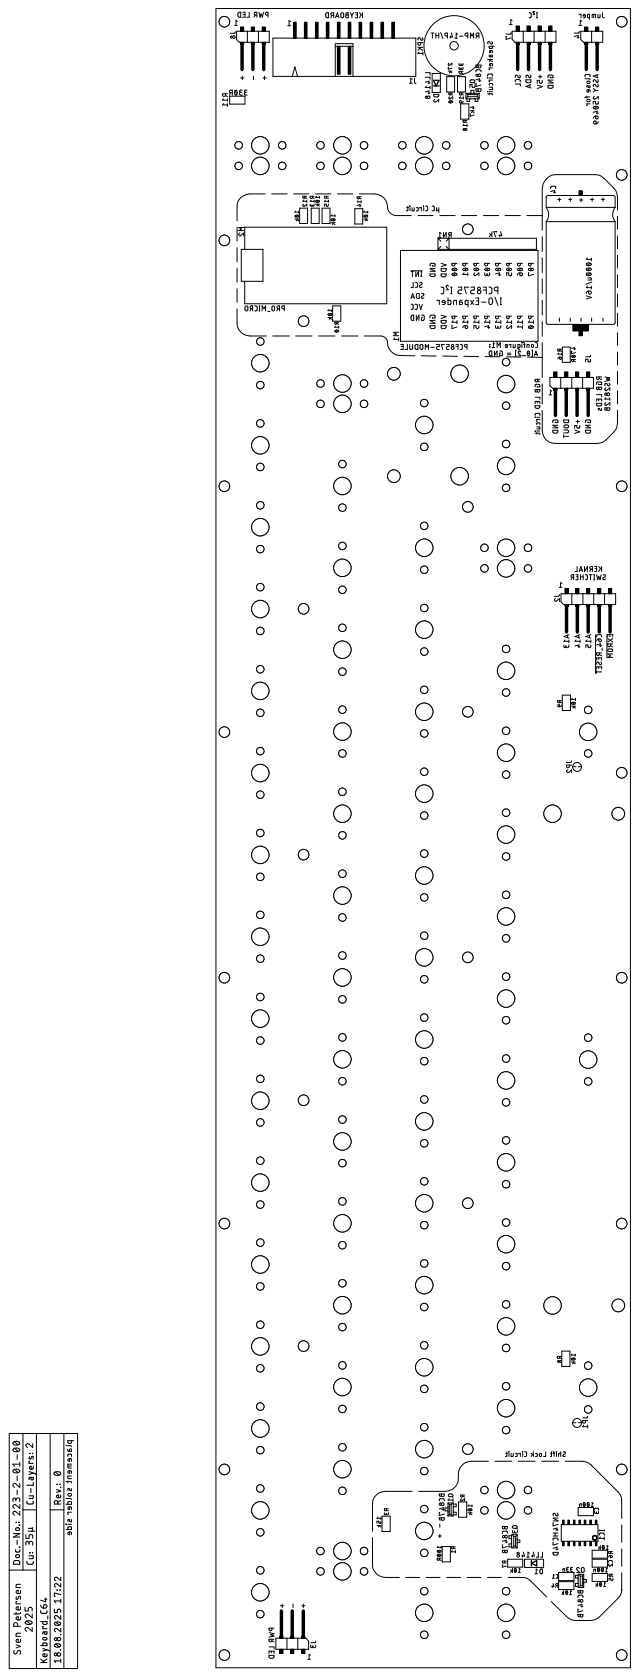
[picture p388: page 3]

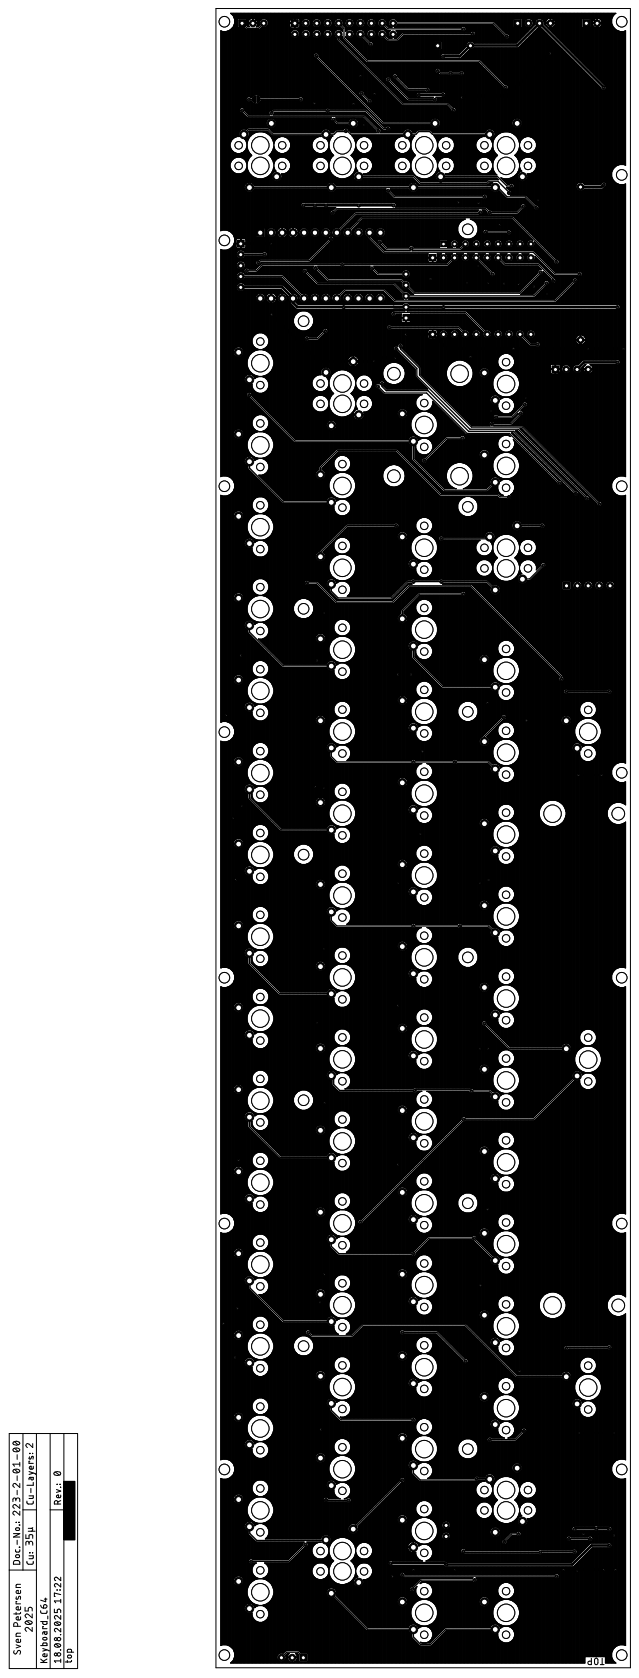
[picture p389: page 4]

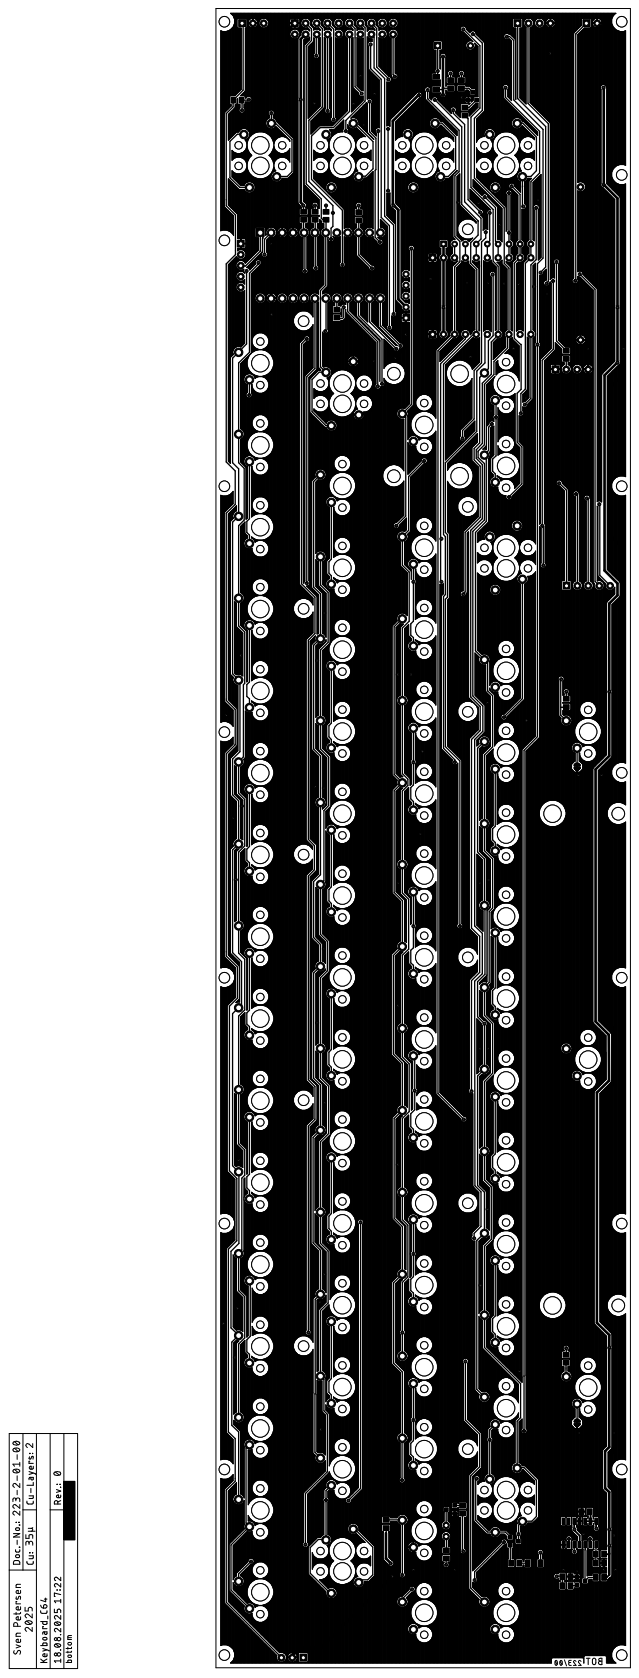
[picture p390: page 5]

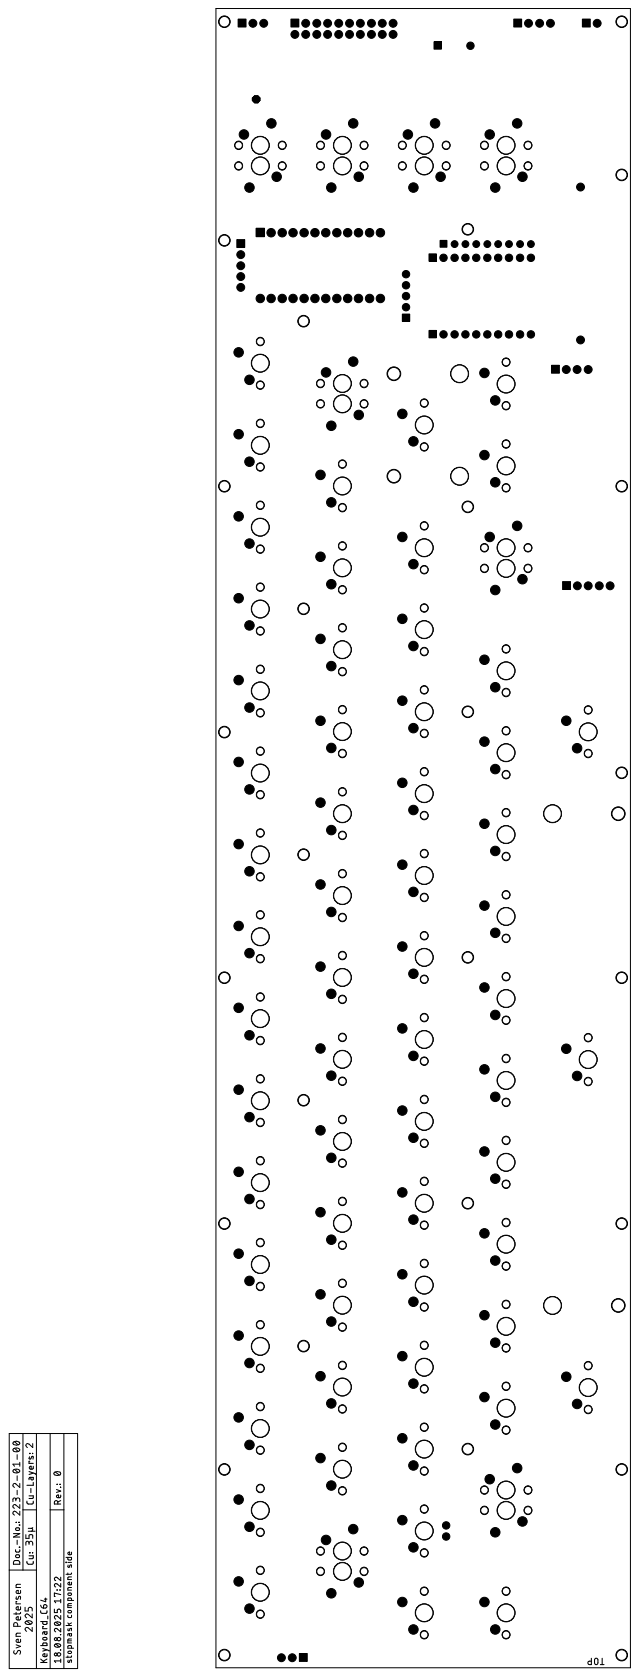
[picture p391: page 6]

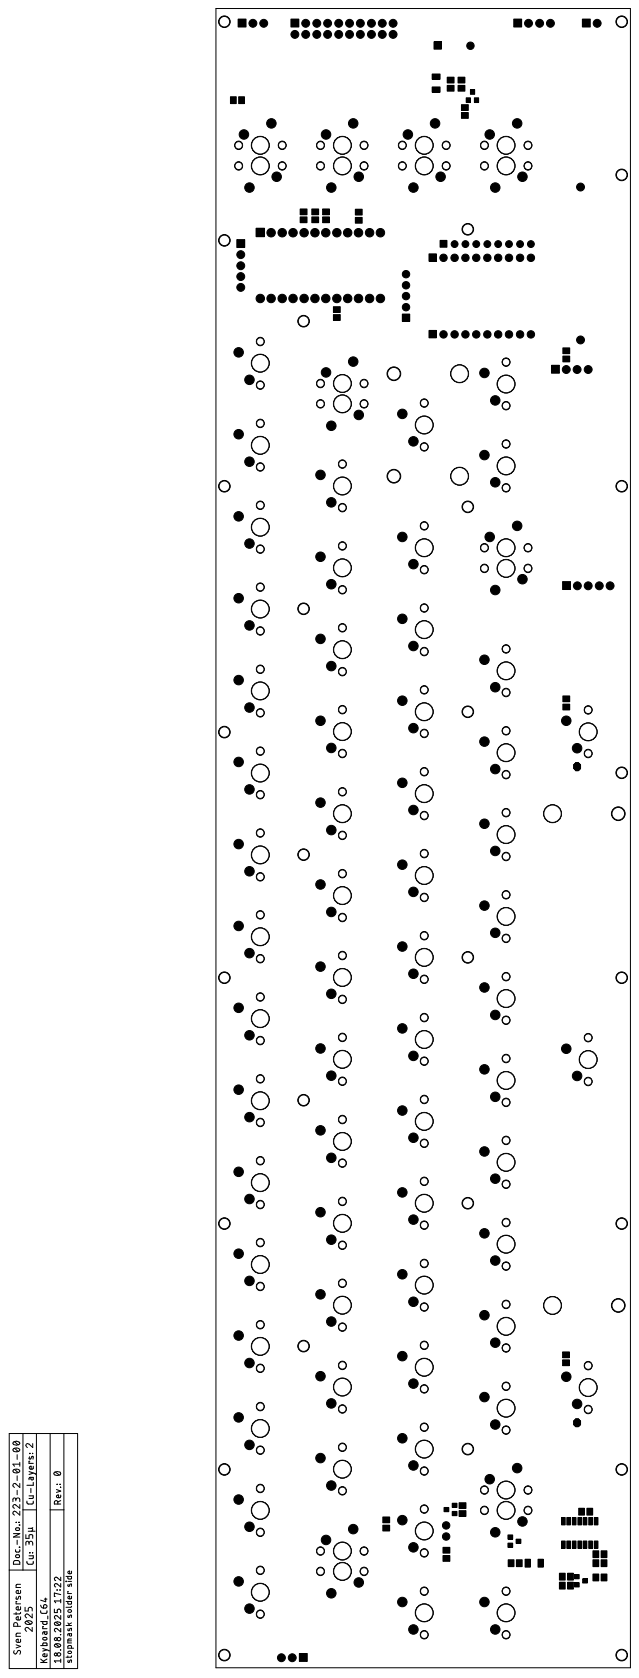
[picture p392: page 7]

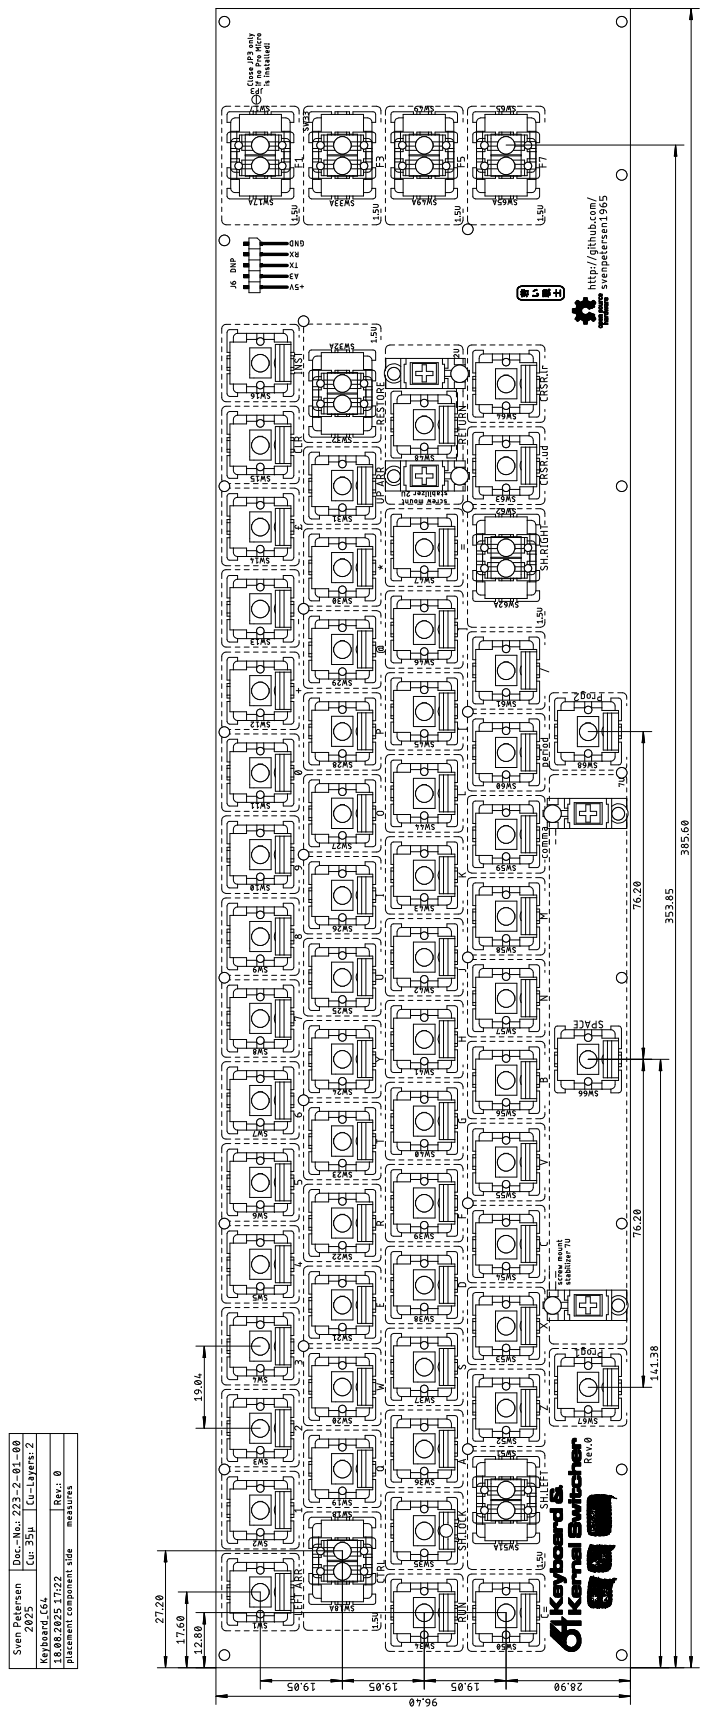
[picture p393: page 8]
