svenpetersen1965/C64-Keyboard/C64 Keyboard with Hot Swap Sockets/Rev. 2/pdf/sch_brd.pdf

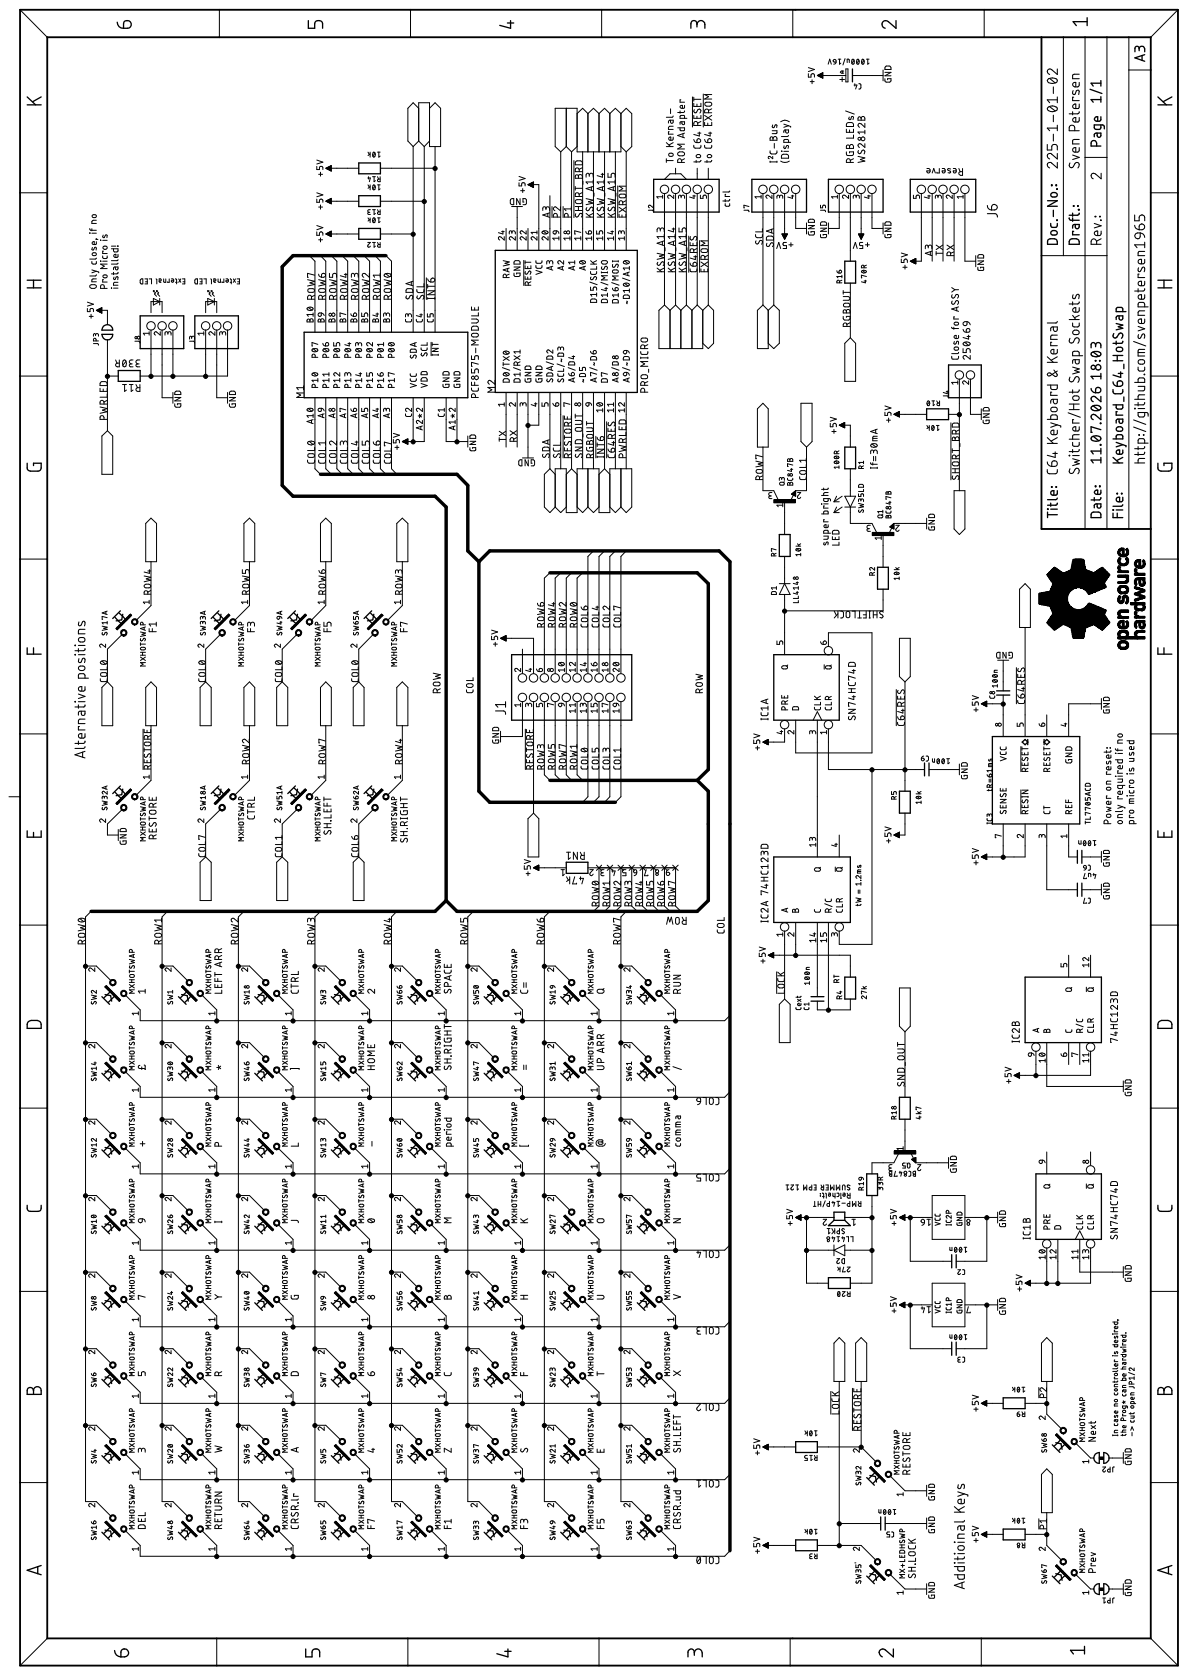
[picture p394: page 1]

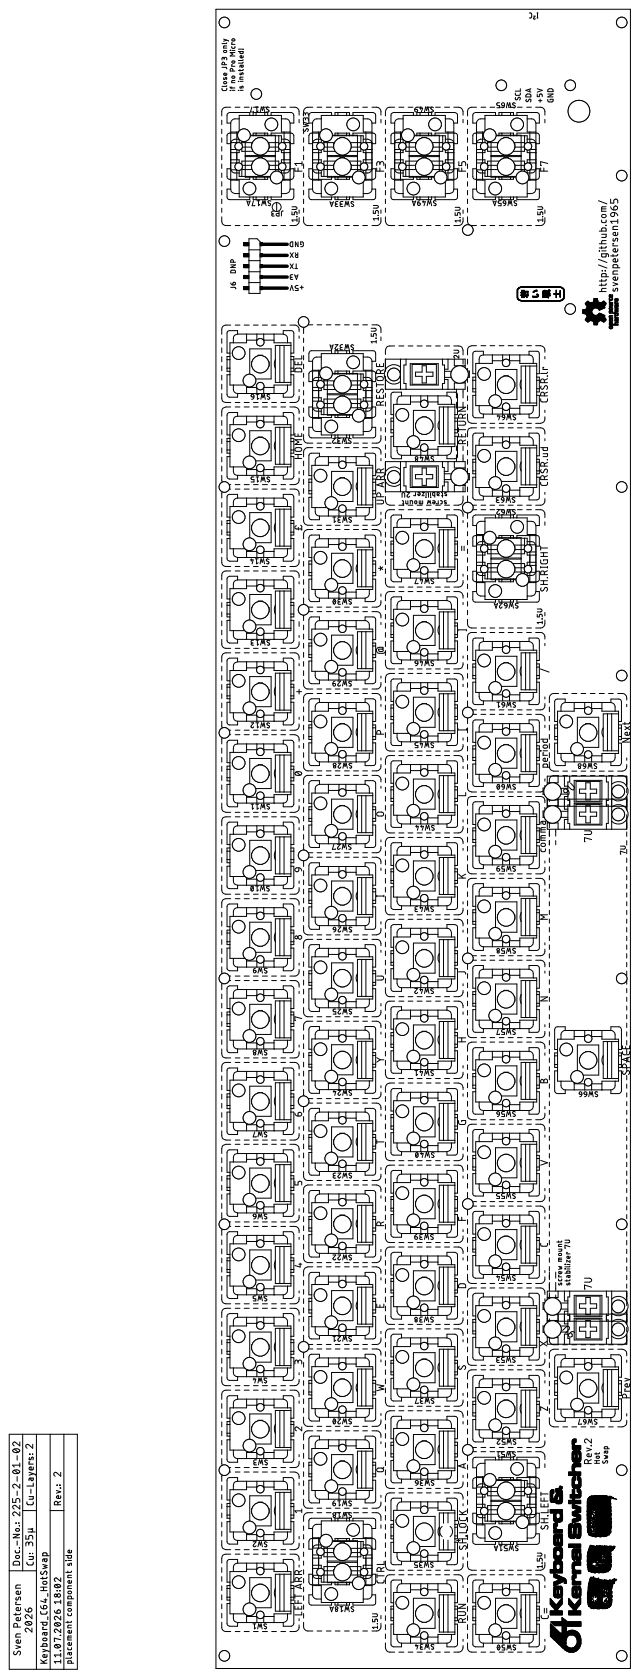
[picture p395: page 2]

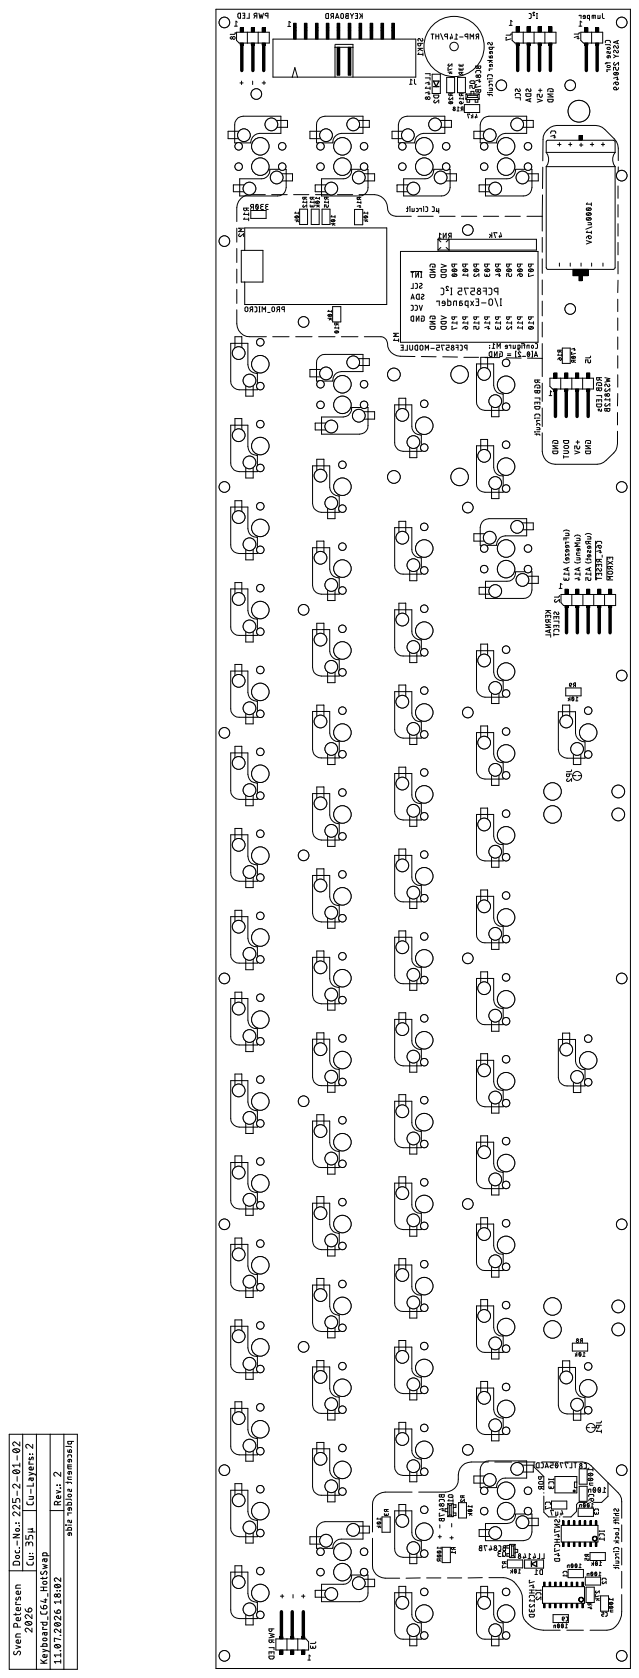
[picture p396: page 3]

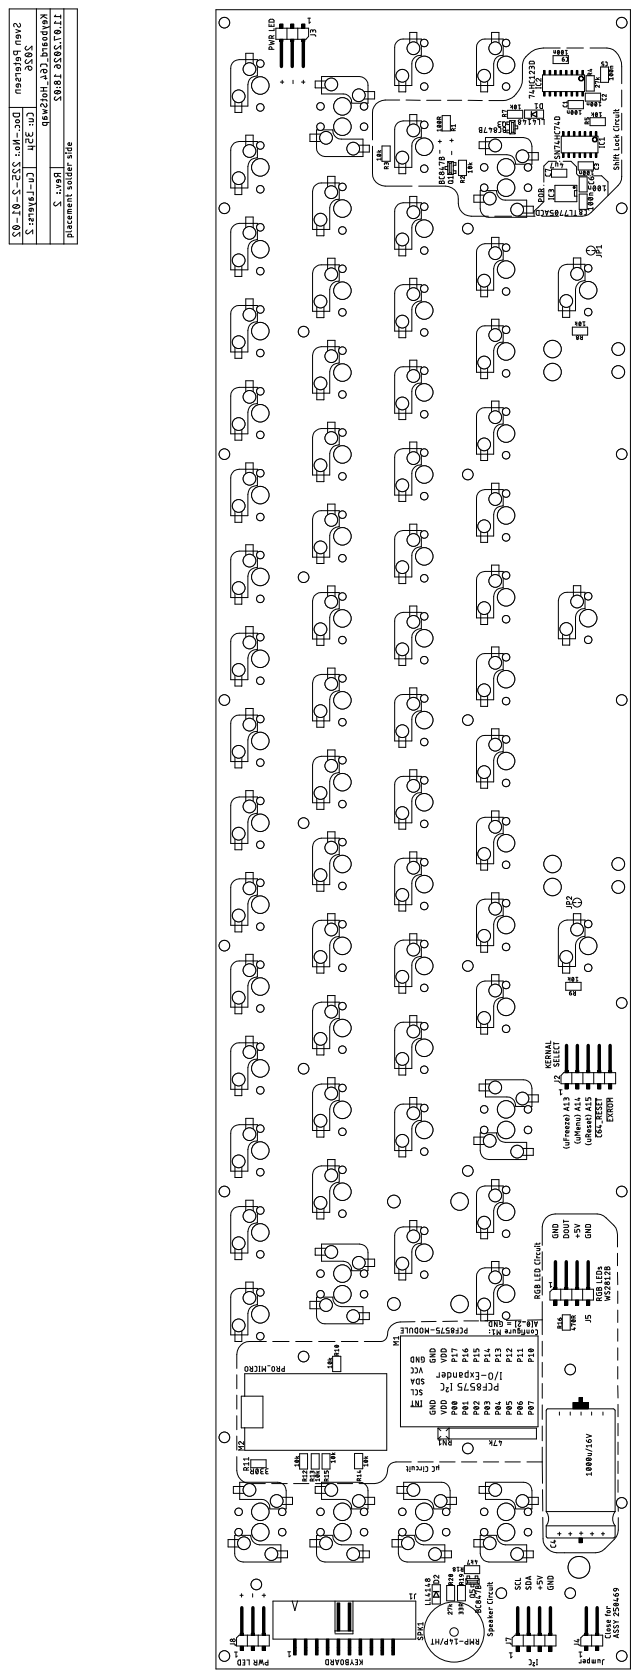
[picture p397: page 4]

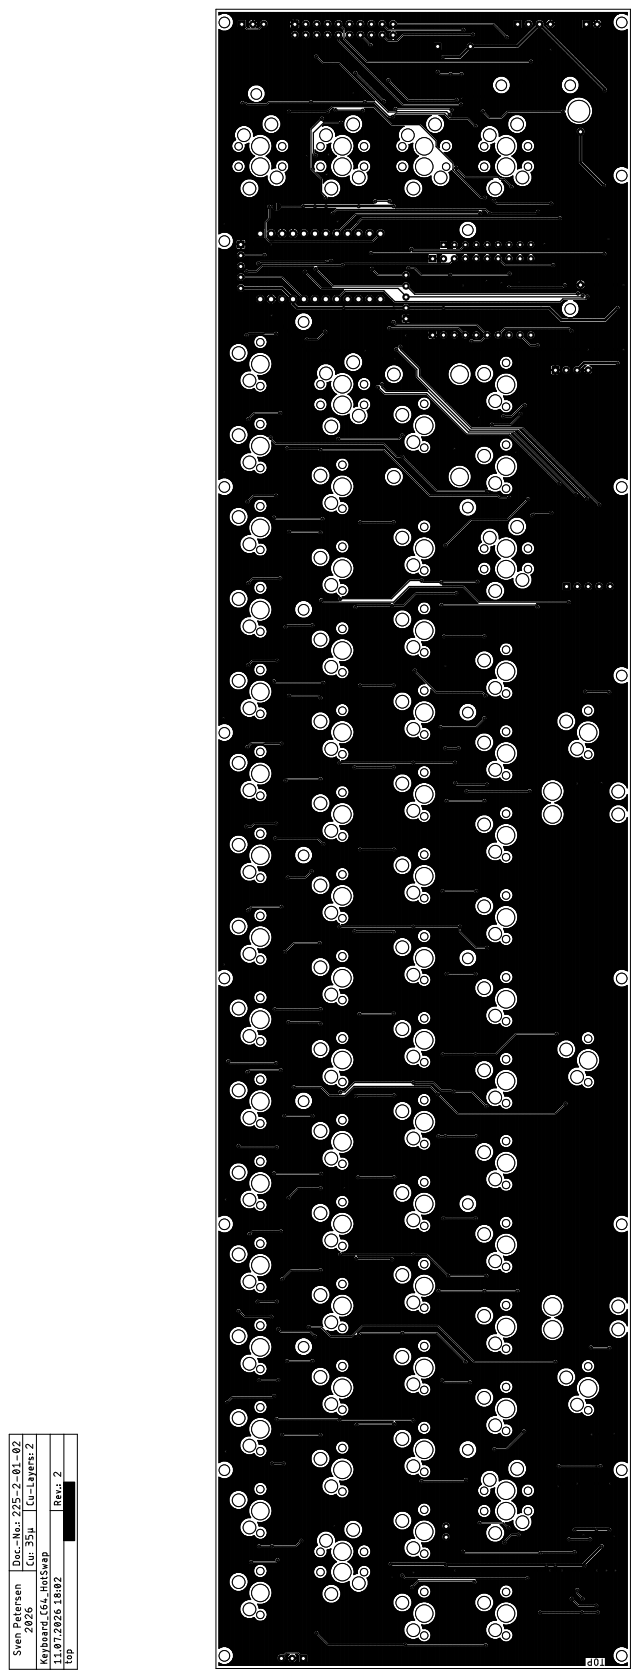
[picture p398: page 5]

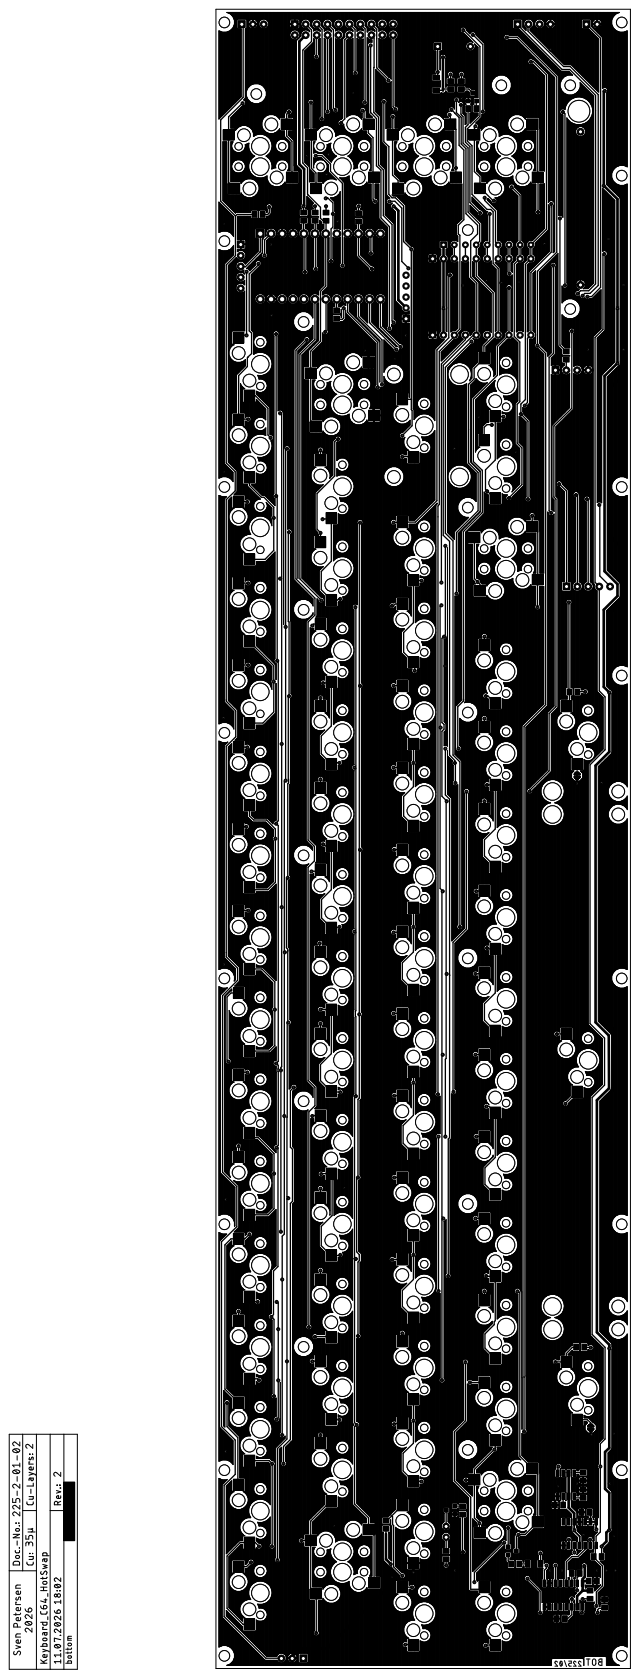
[picture p399: page 6]

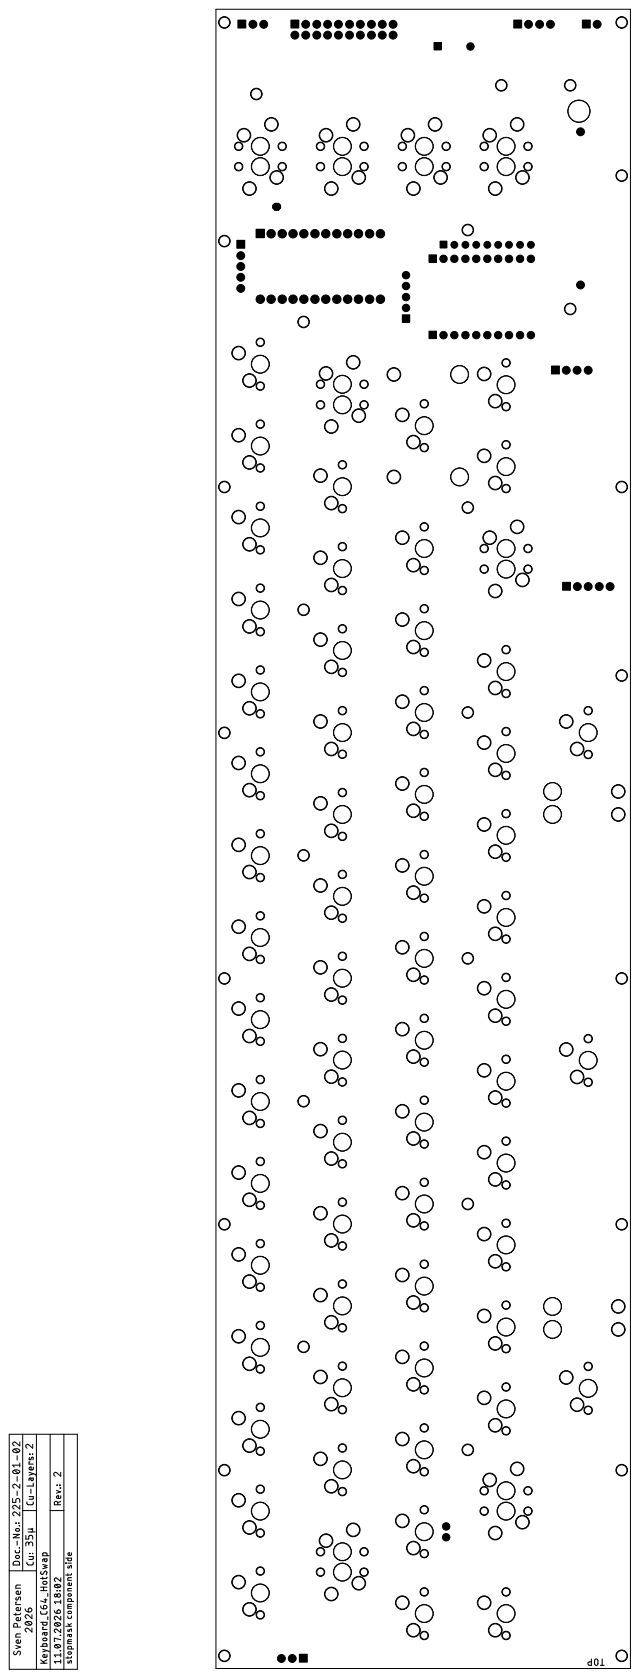
[picture p400: page 7]

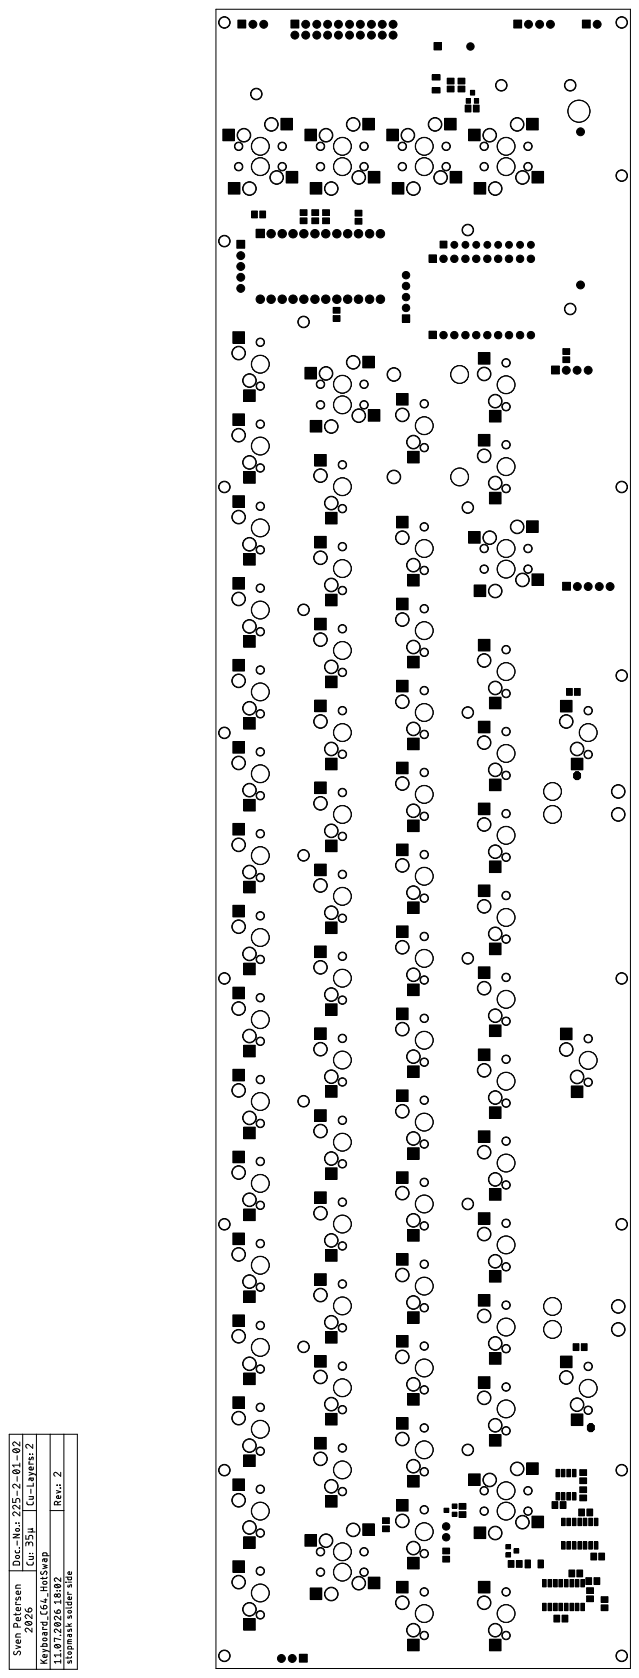
[picture p401: page 8]

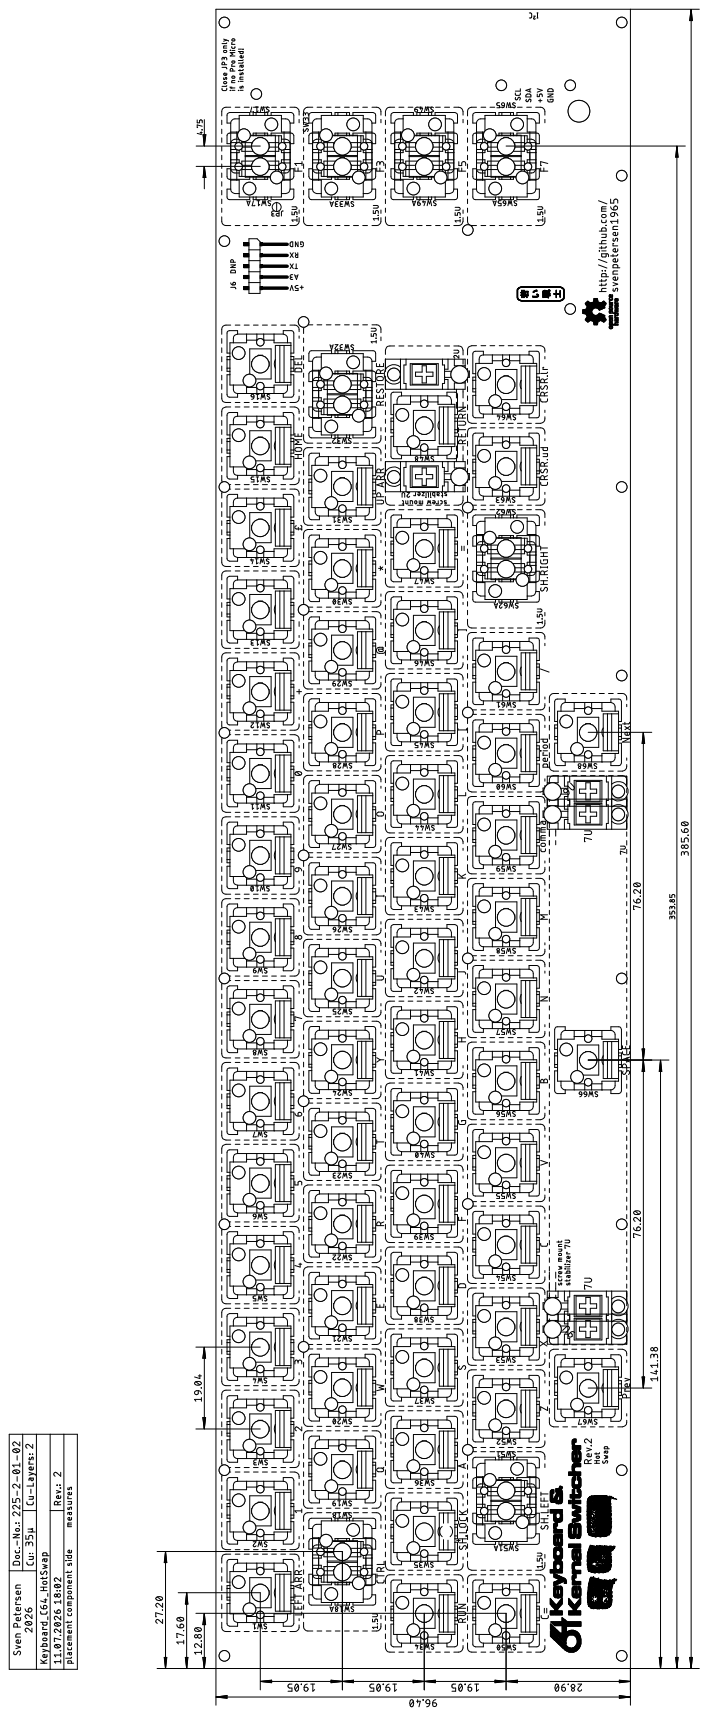
[picture p402: page 9]
