svenpetersen1965/C64-Keyboard/C64 Keyboard with Hot Swap Sockets/Rev. 1/pdf/sch_brd.pdf

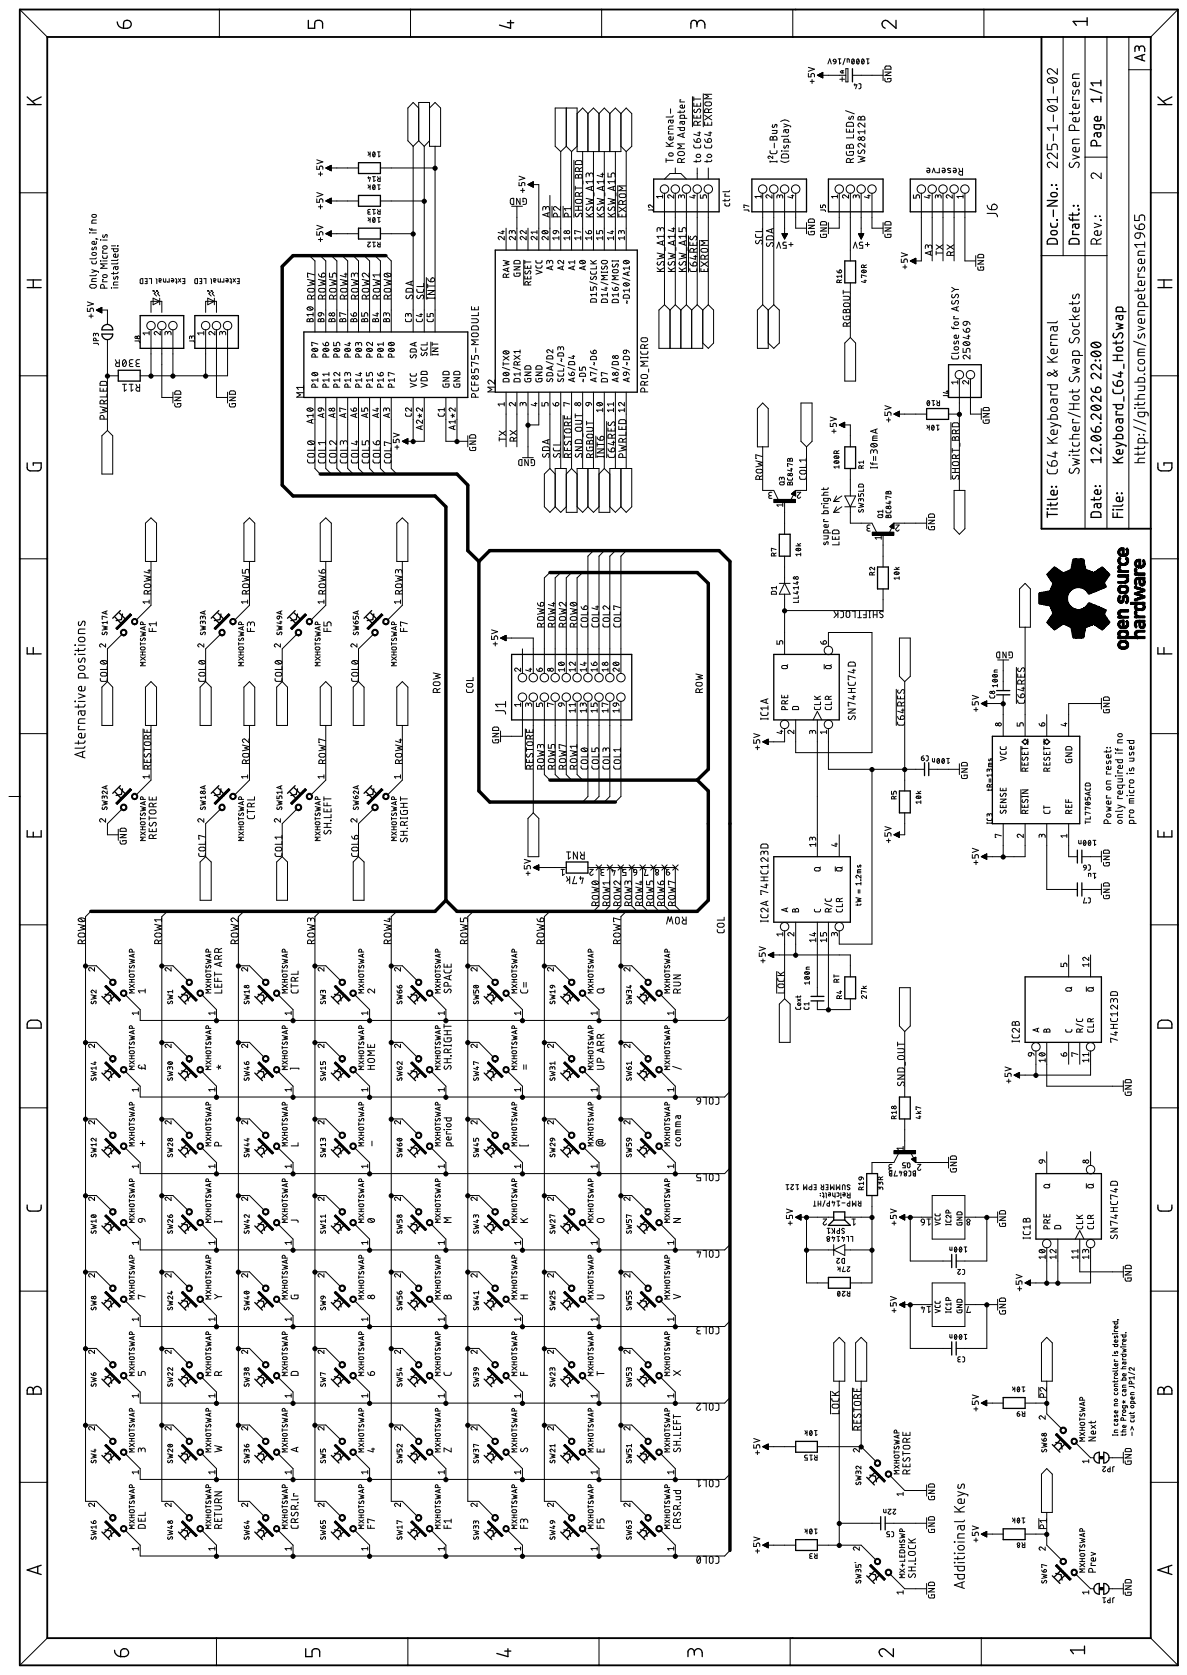
[picture p403: page 1]

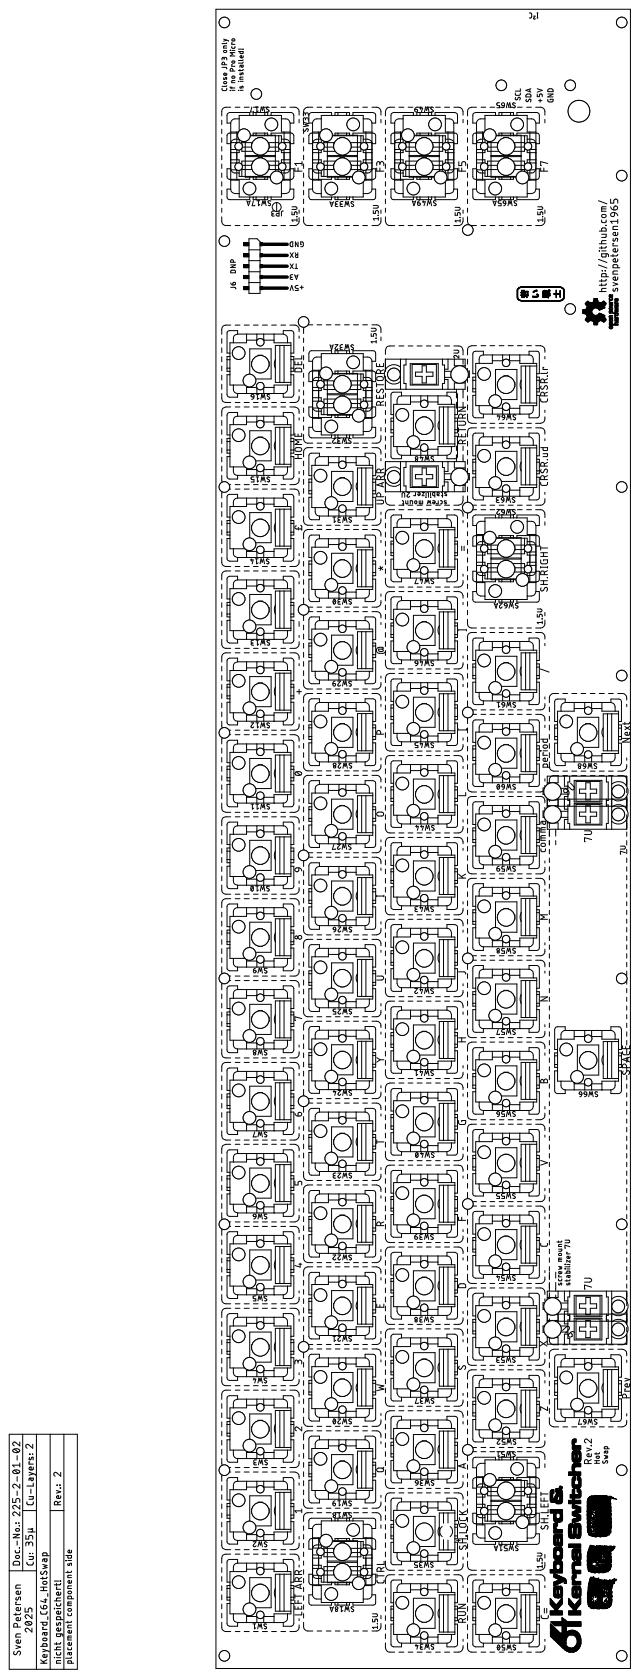
[picture p404: page 2]

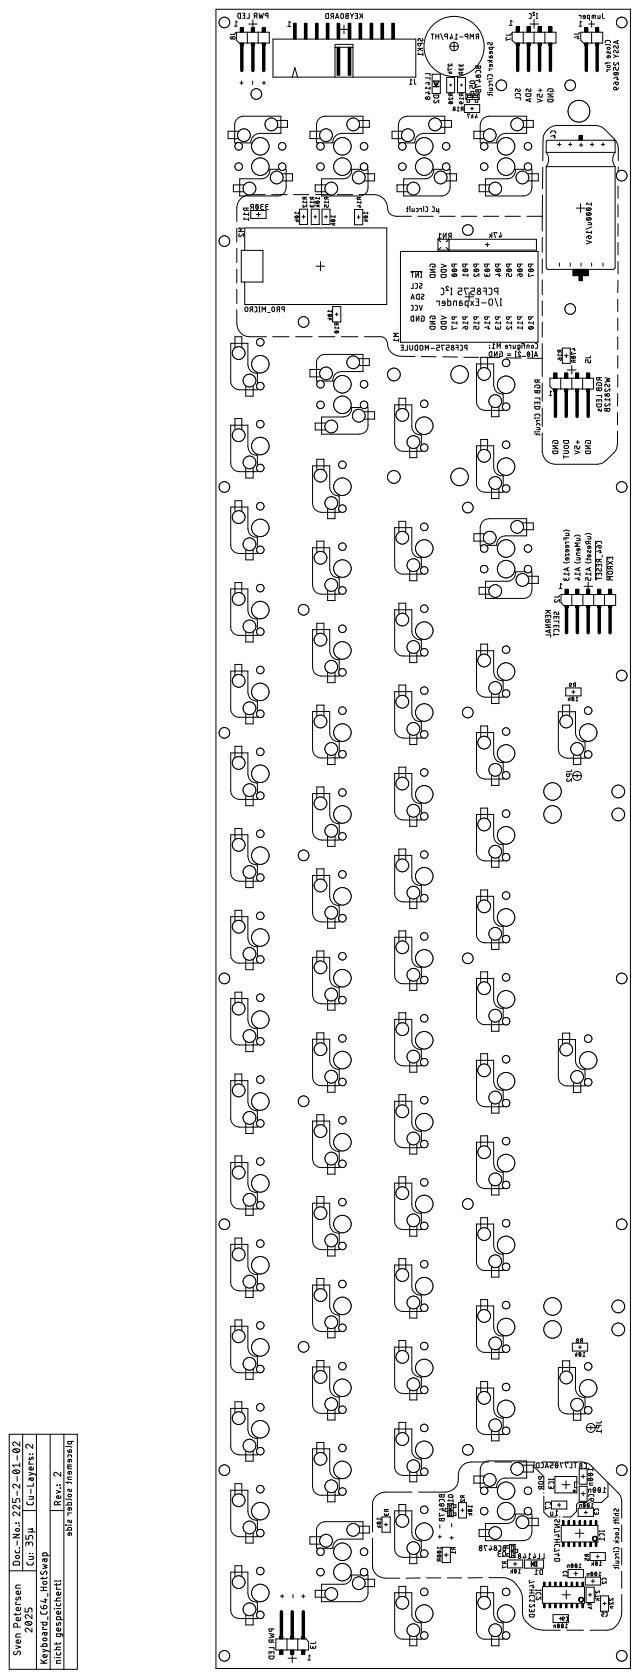
[picture p405: page 3]

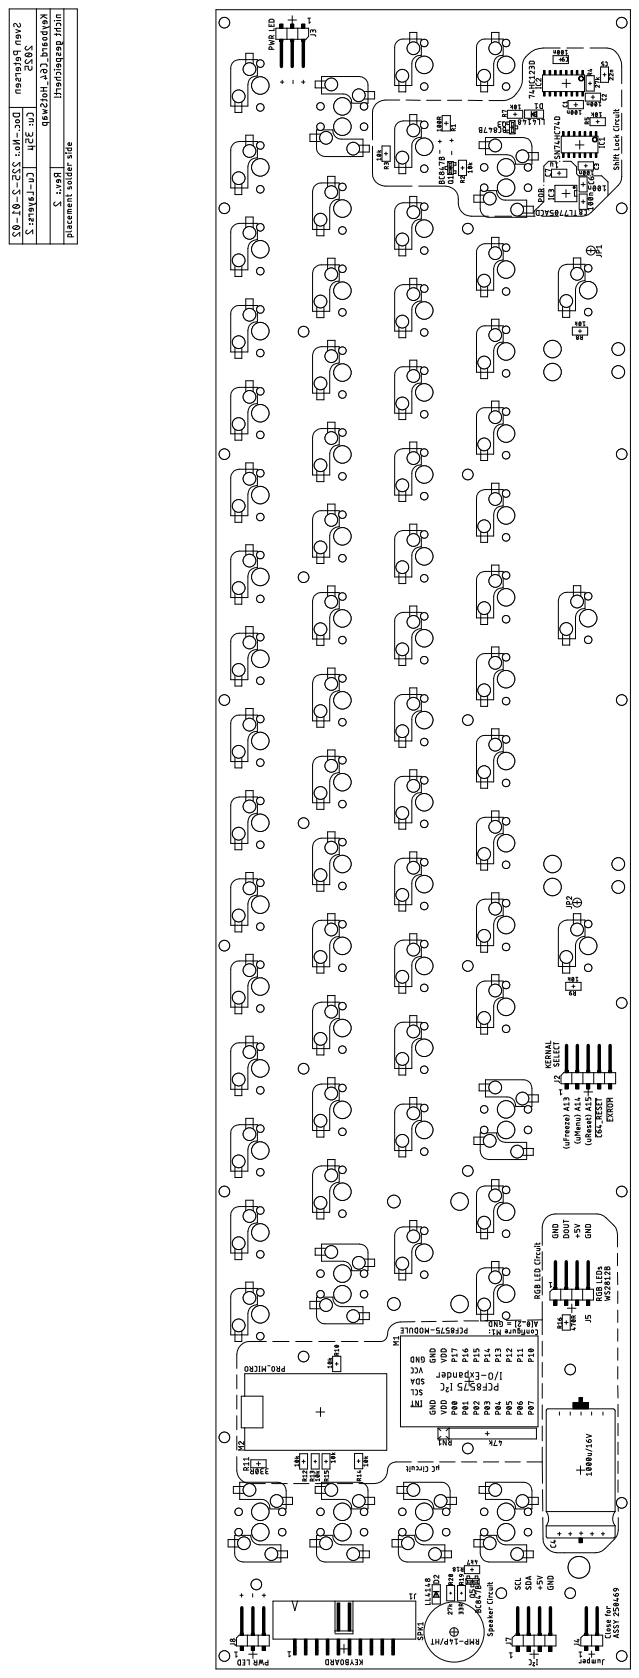
[picture p406: page 4]

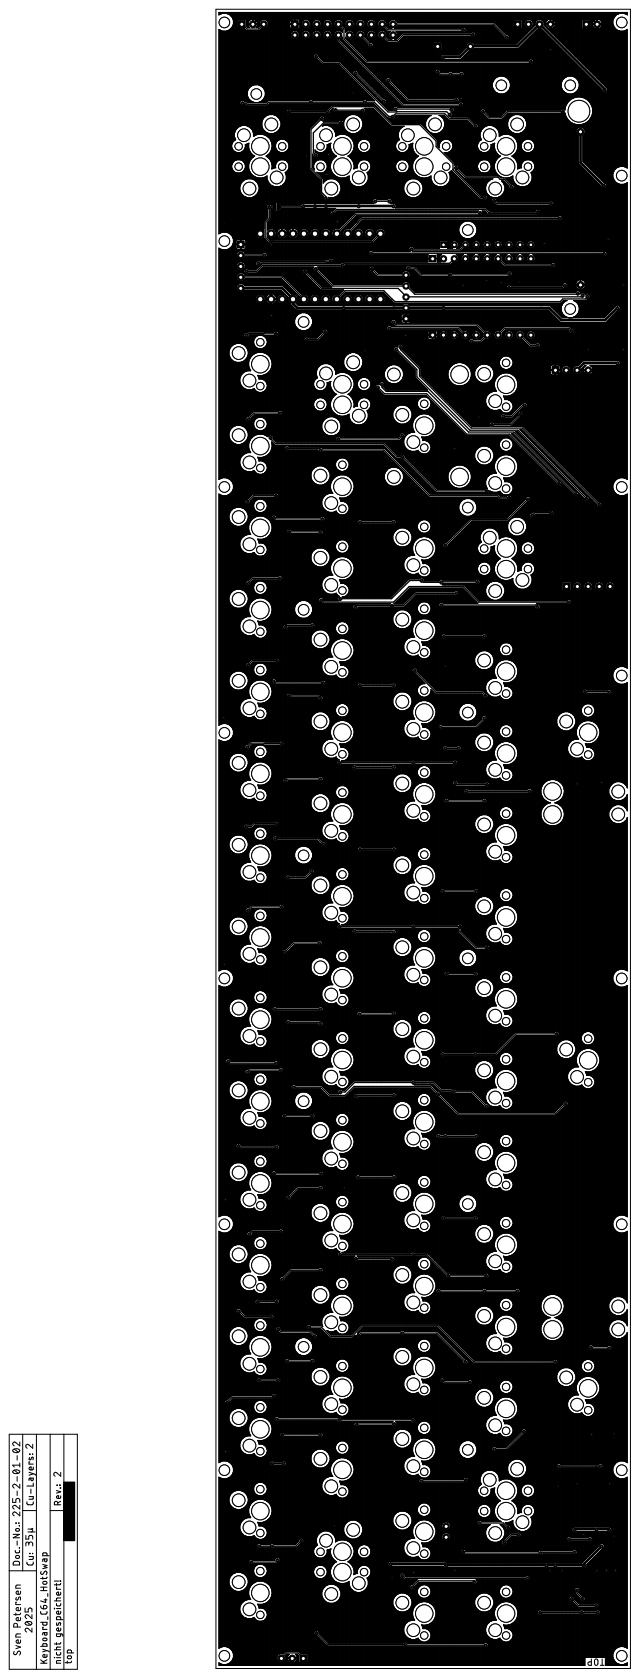
[picture p407: page 5]

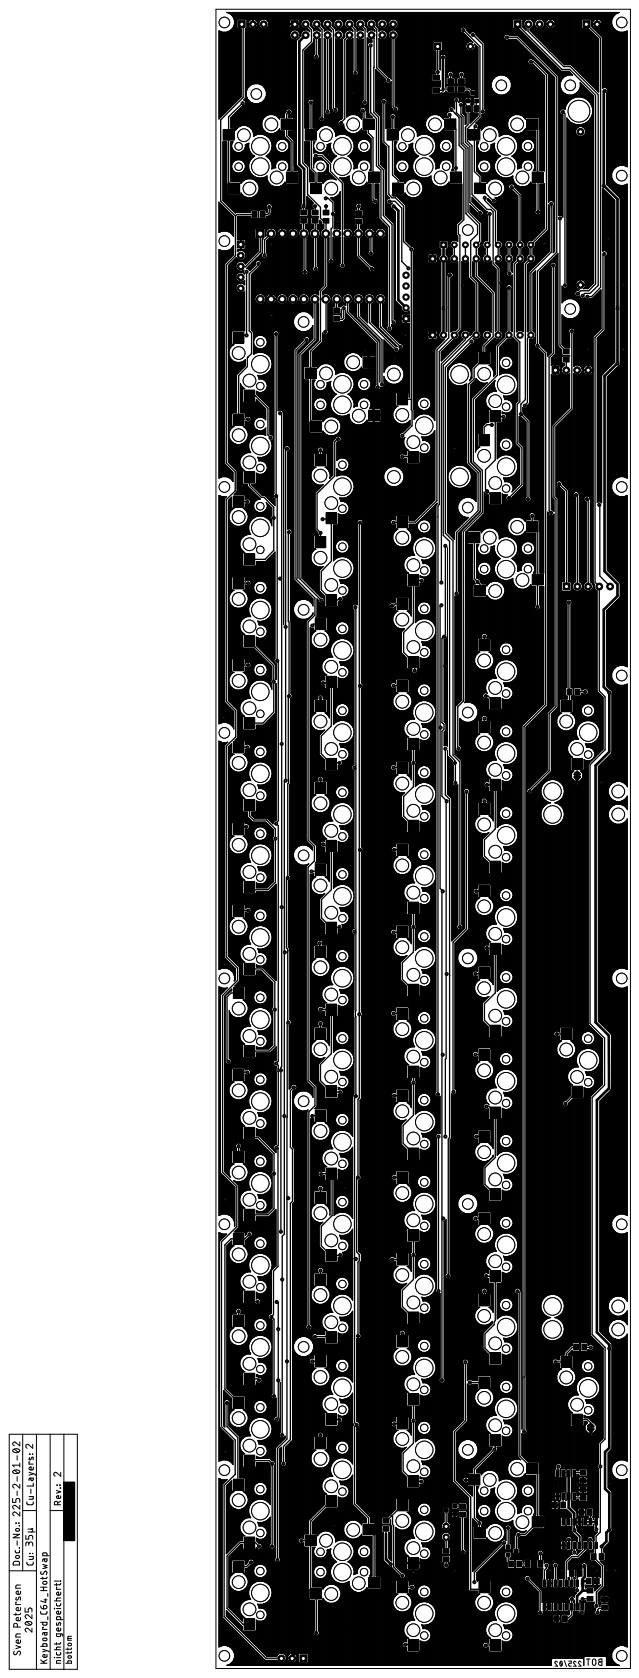
[picture p408: page 6]

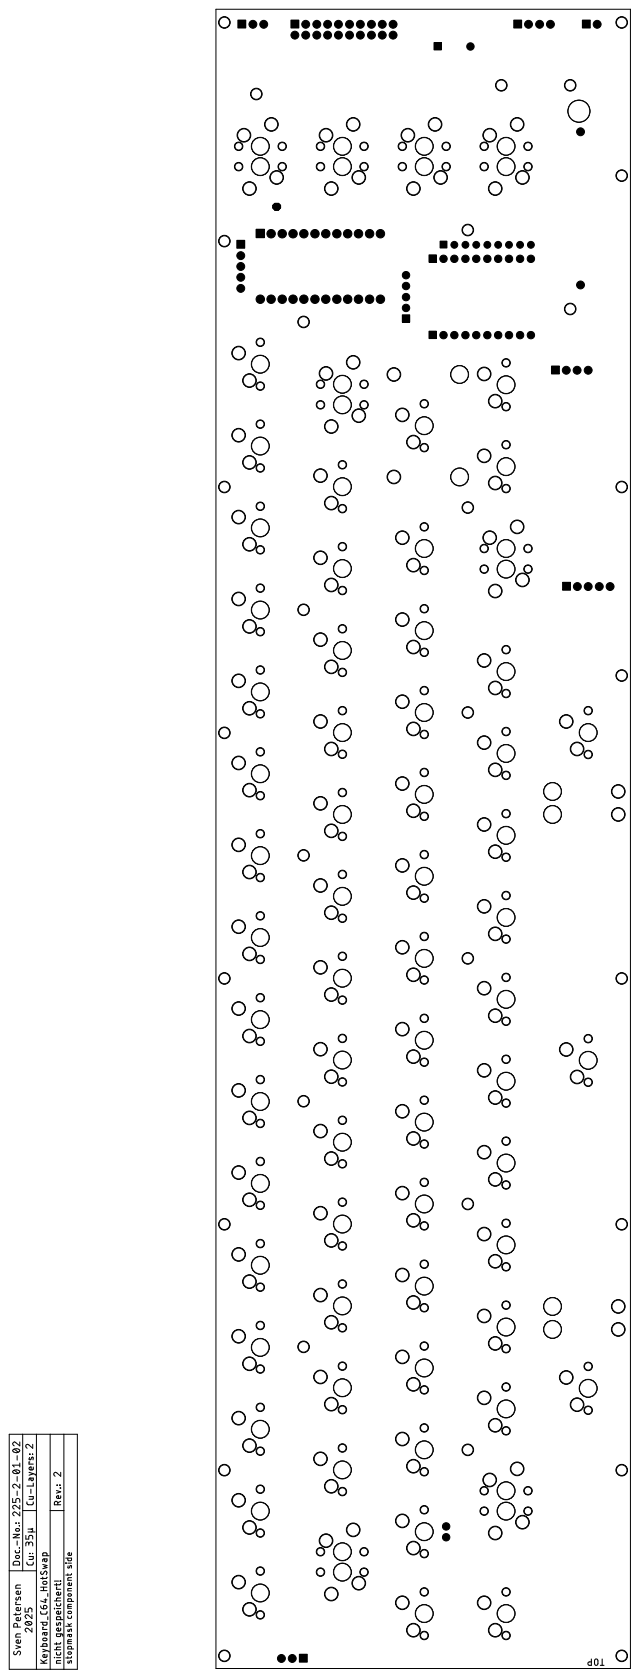
[picture p409: page 7]

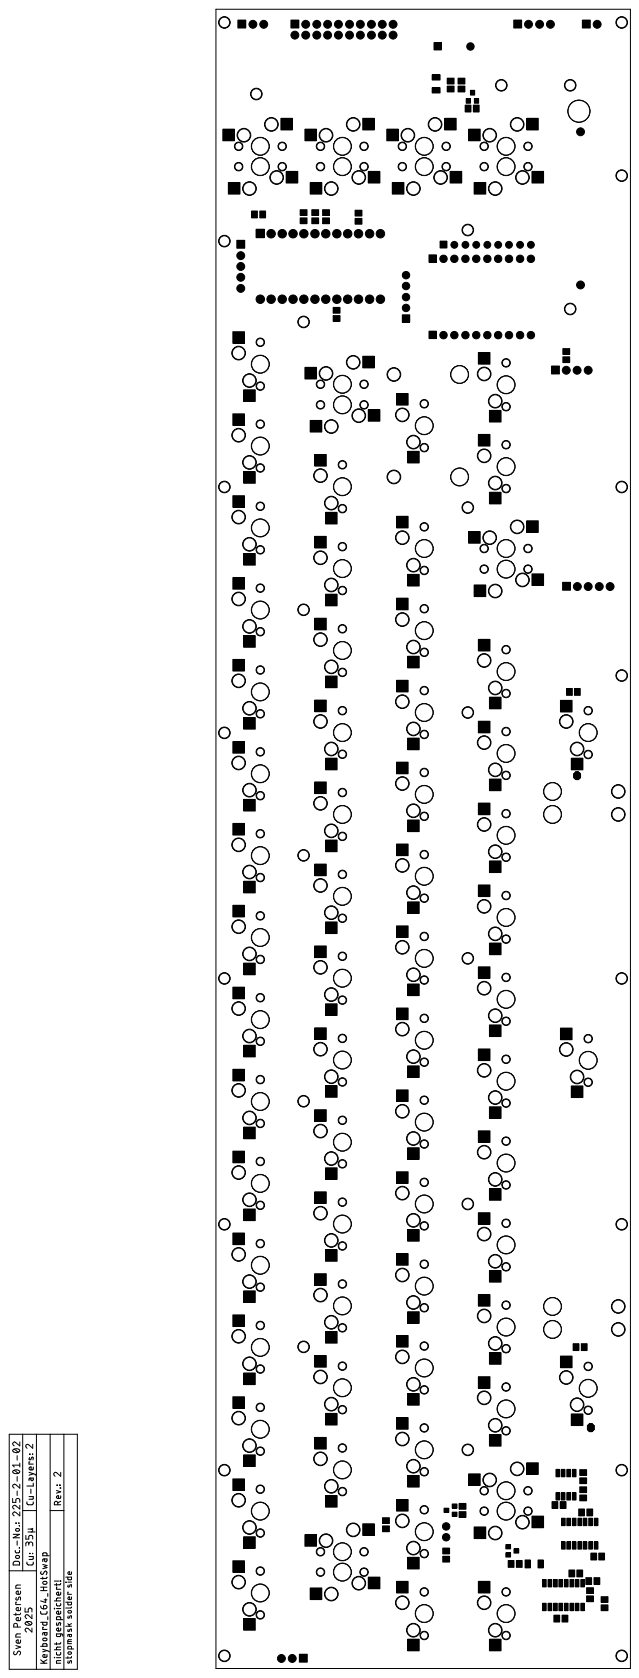
[picture p410: page 8]

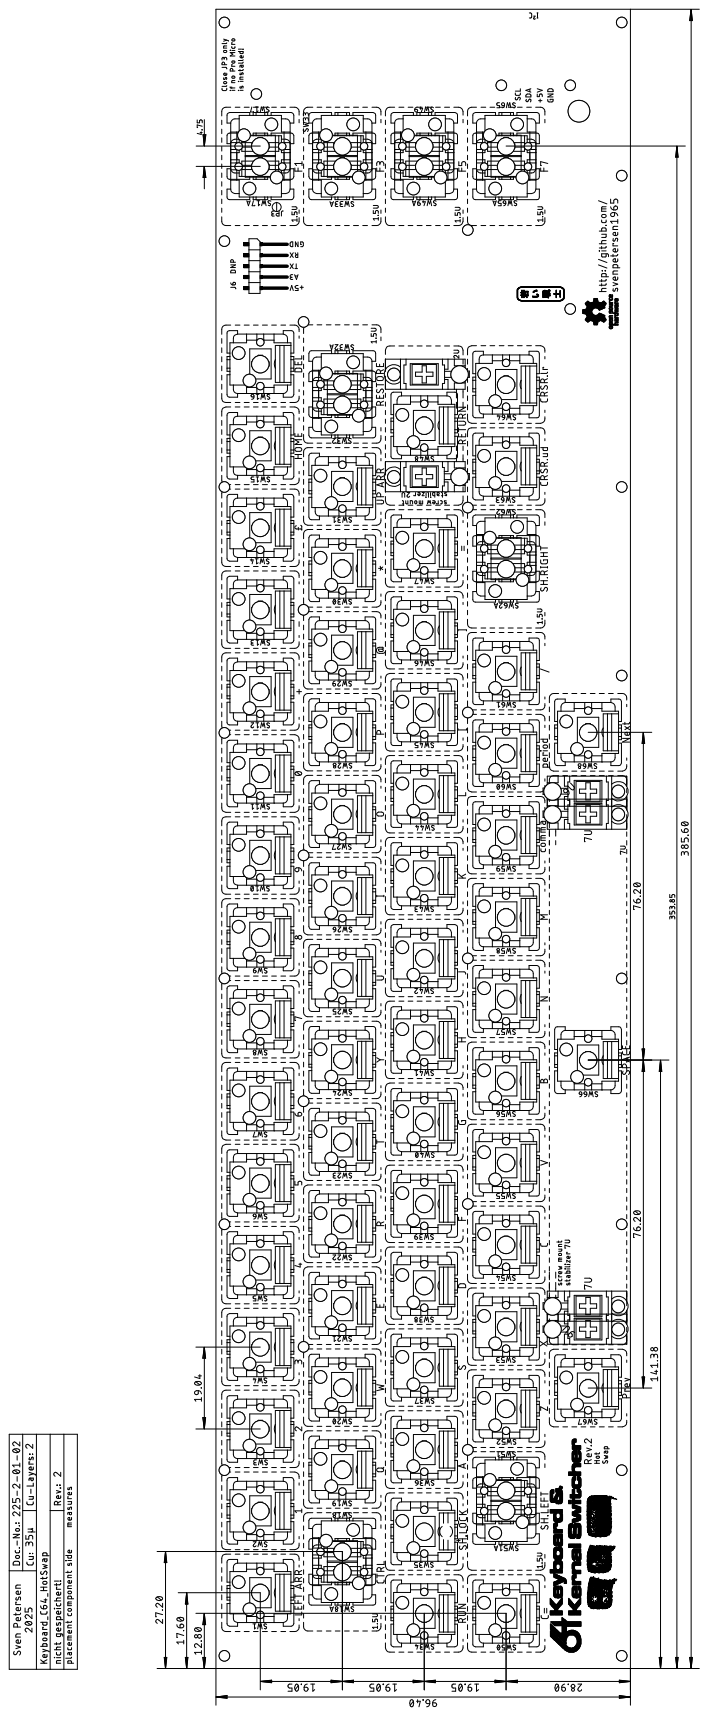
[picture p411: page 9]
