svenpetersen1965/C64-Keyboard/C64 Keyboard Standard Version/Rev. 2/pdf/sch_brd.pdf

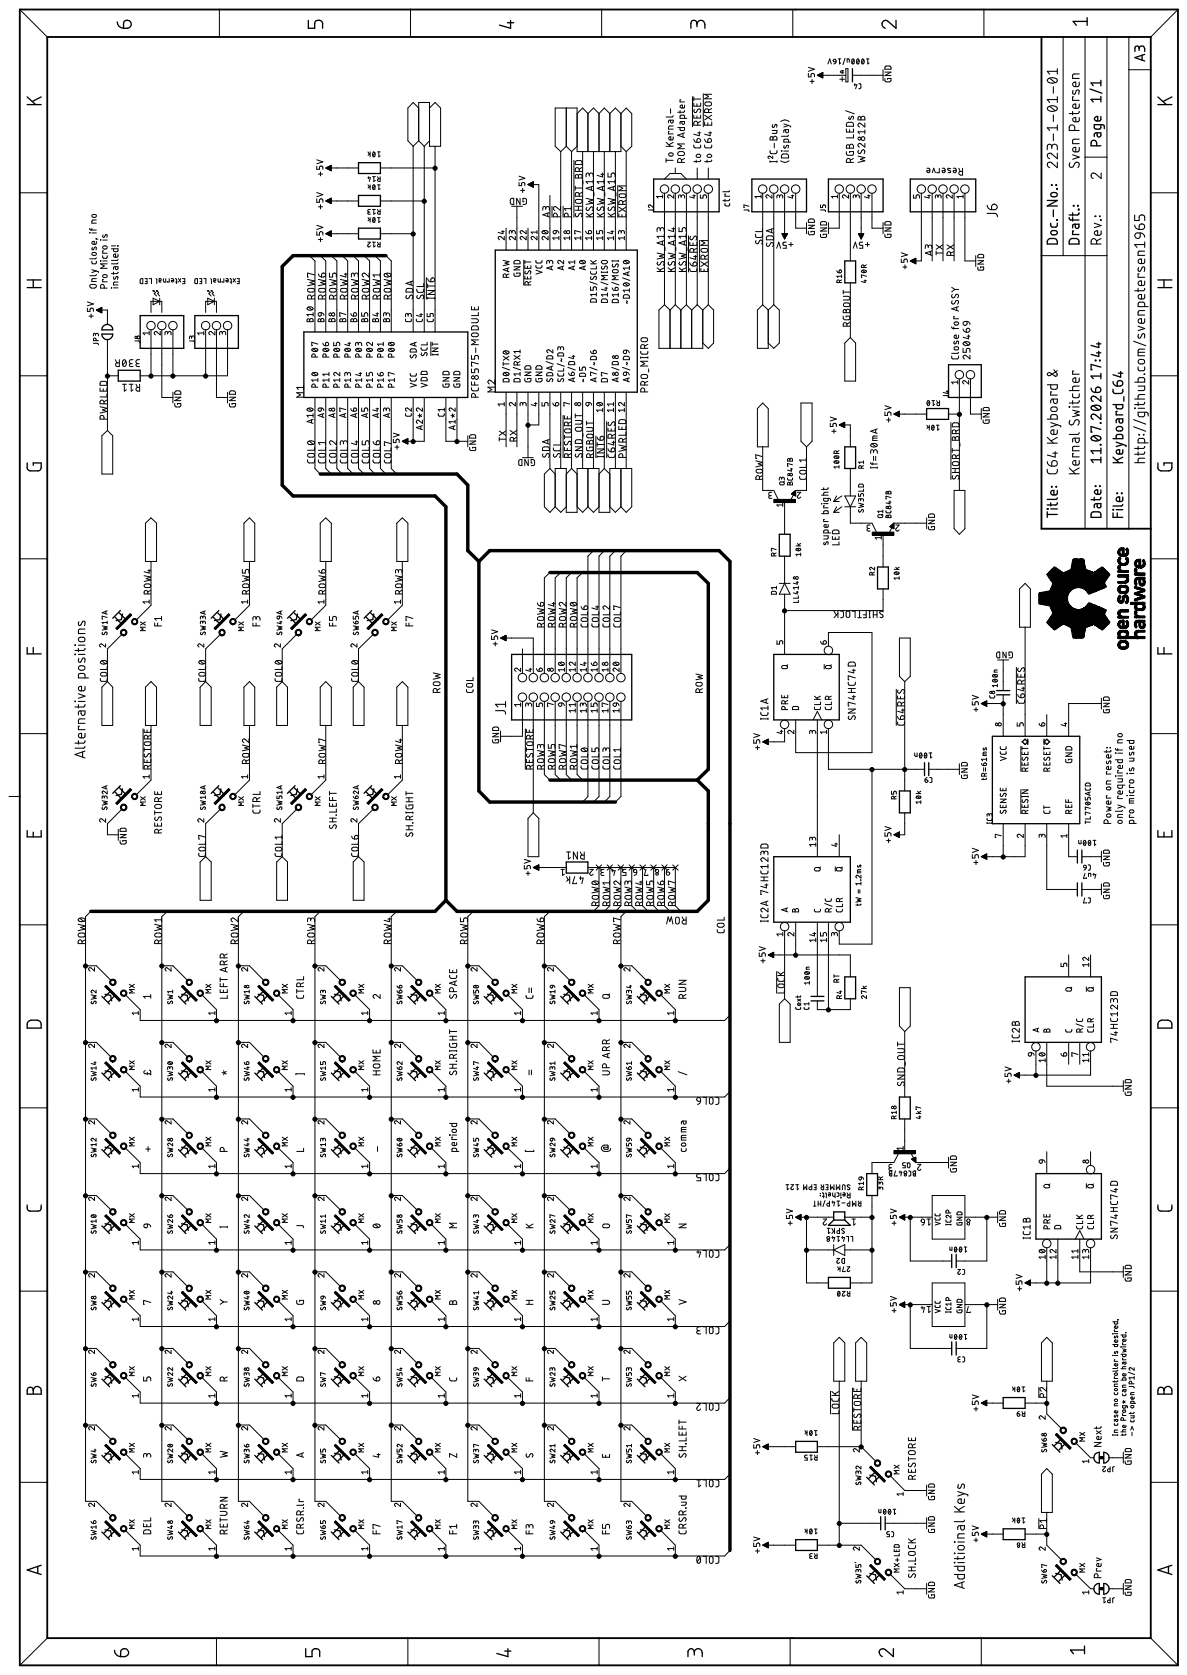
[picture p412: page 1]

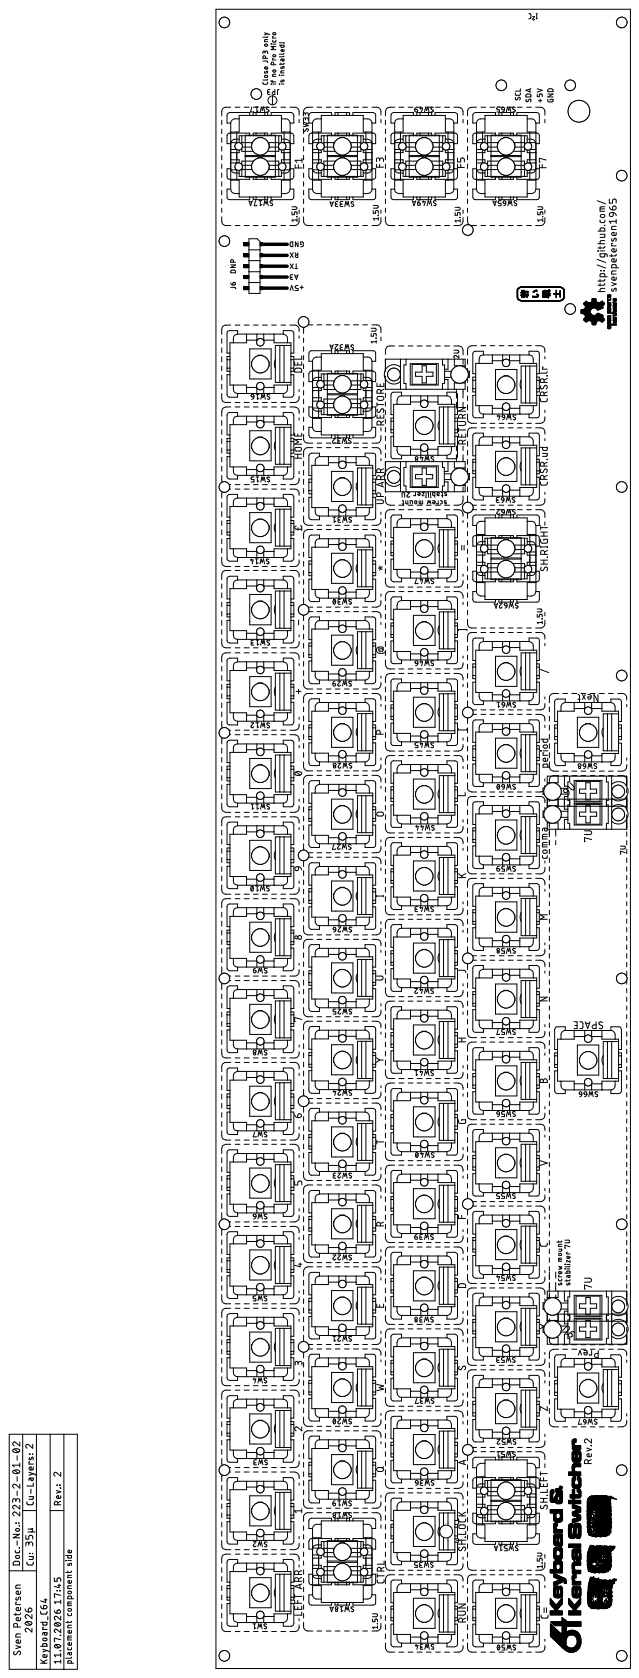
[picture p413: page 2]

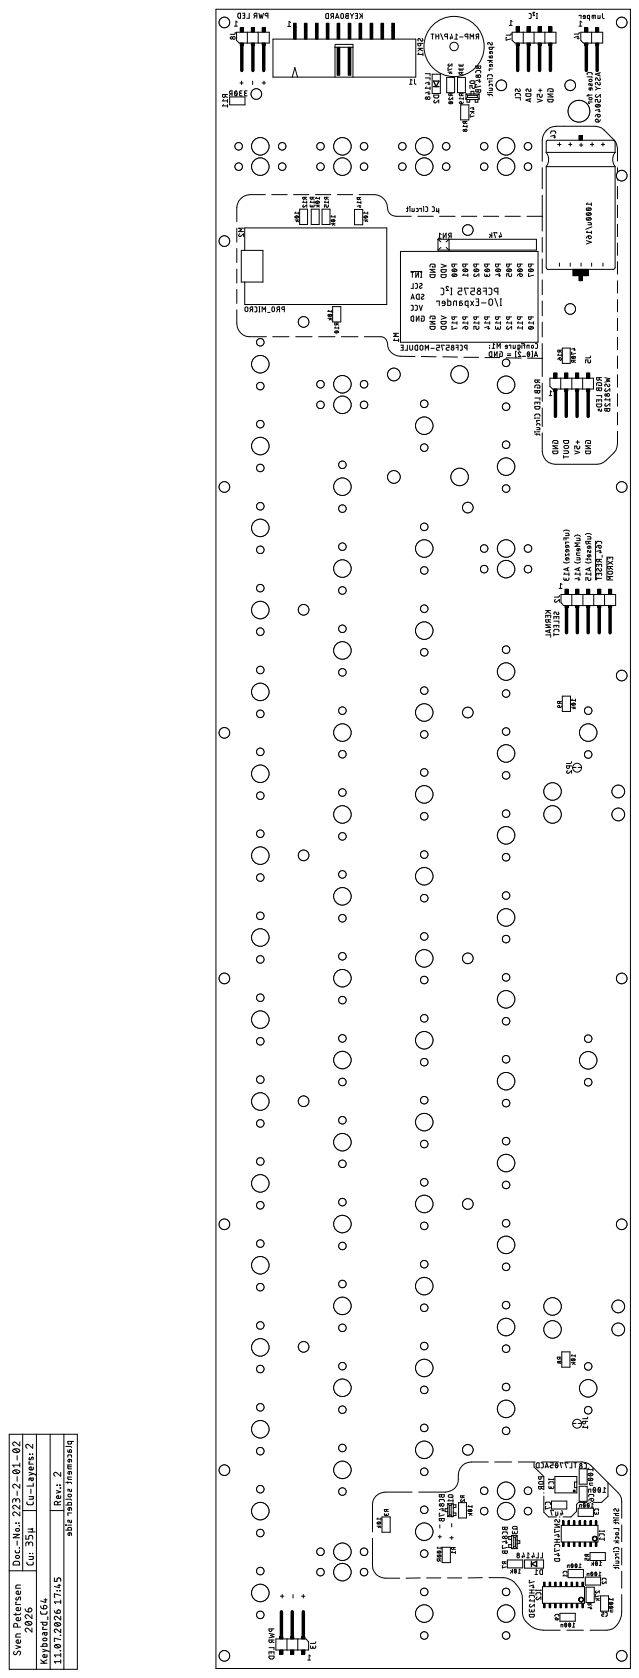
[picture p414: page 3]

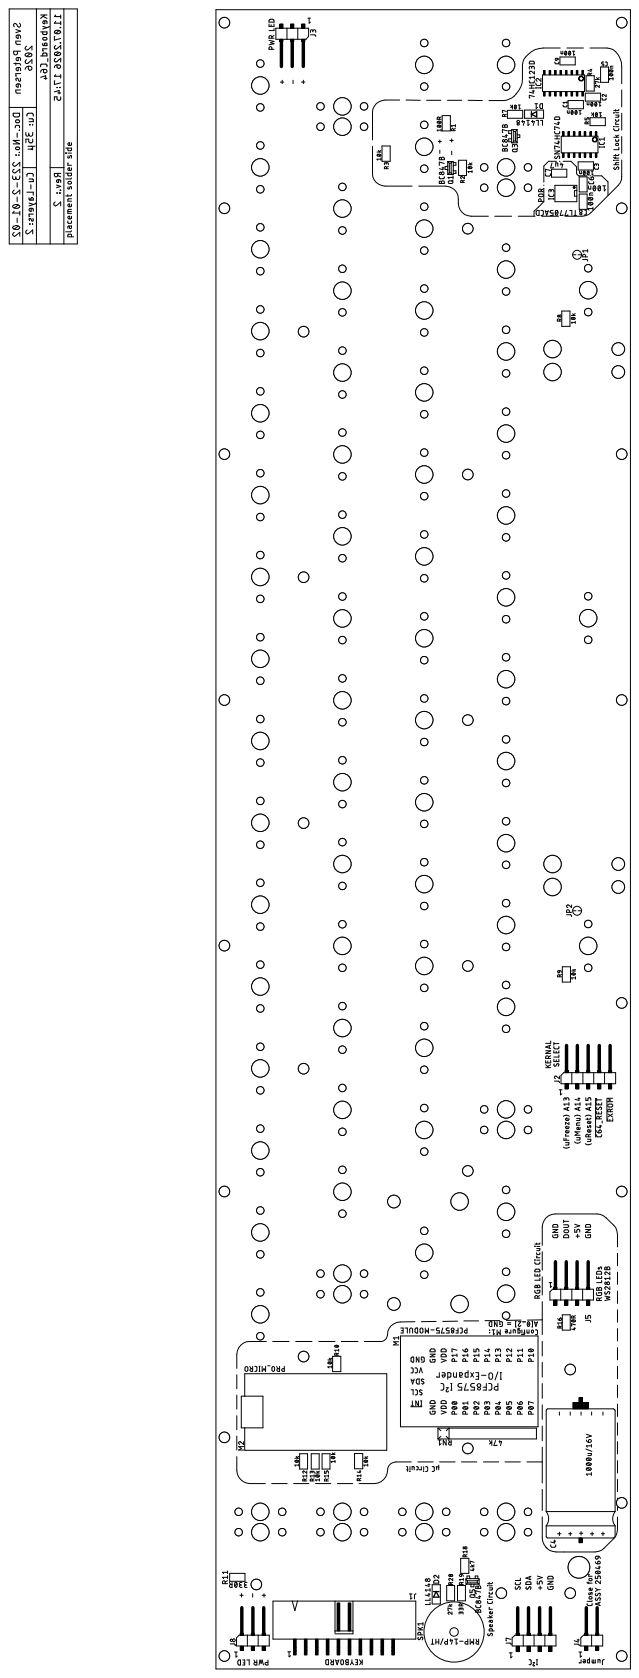
[picture p415: page 4]

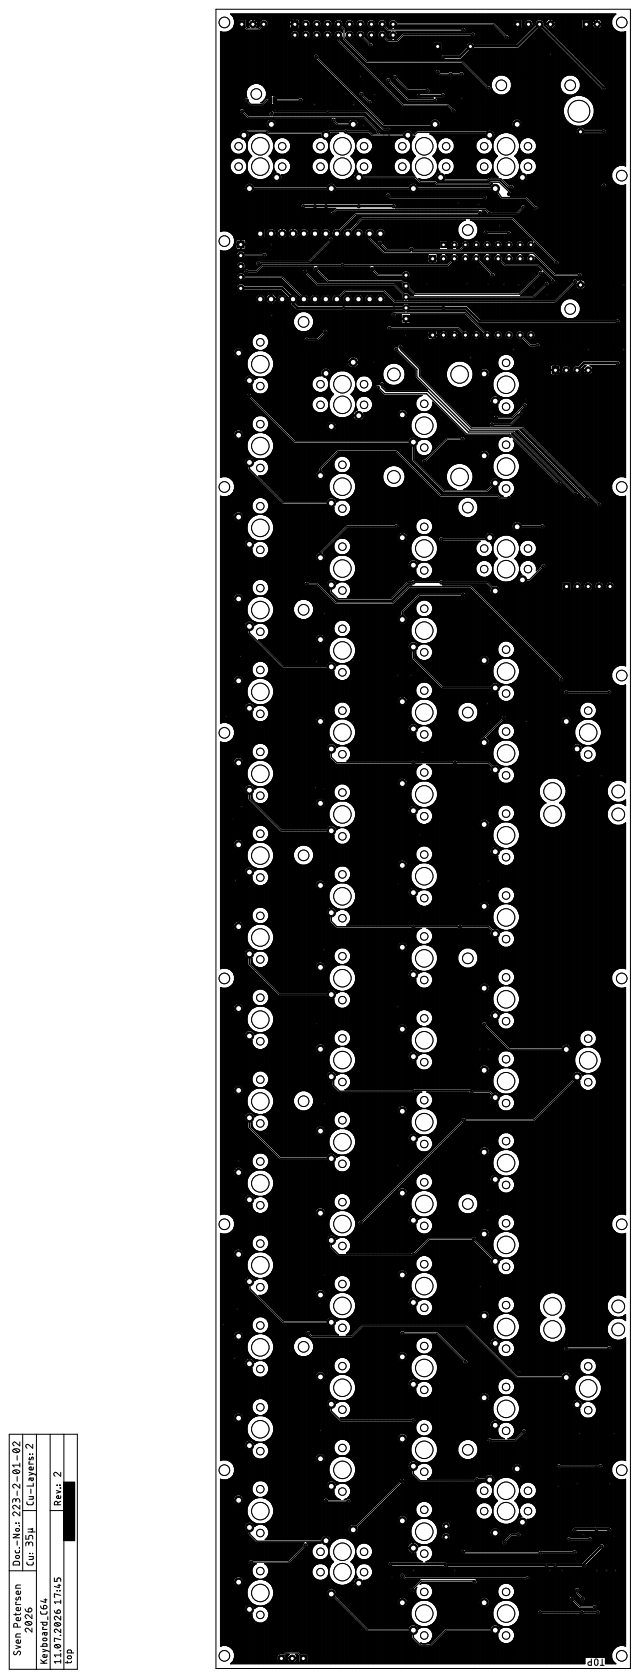
[picture p416: page 5]

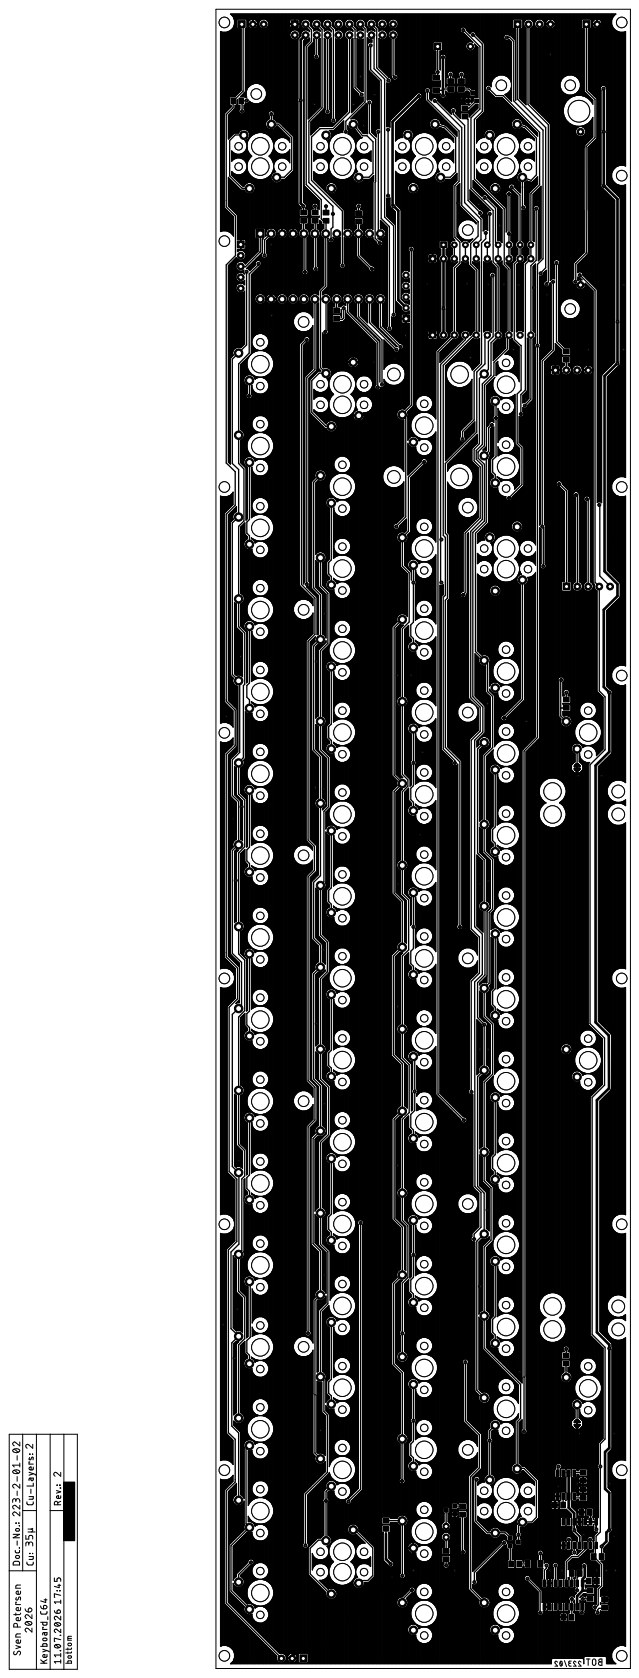
[picture p417: page 6]

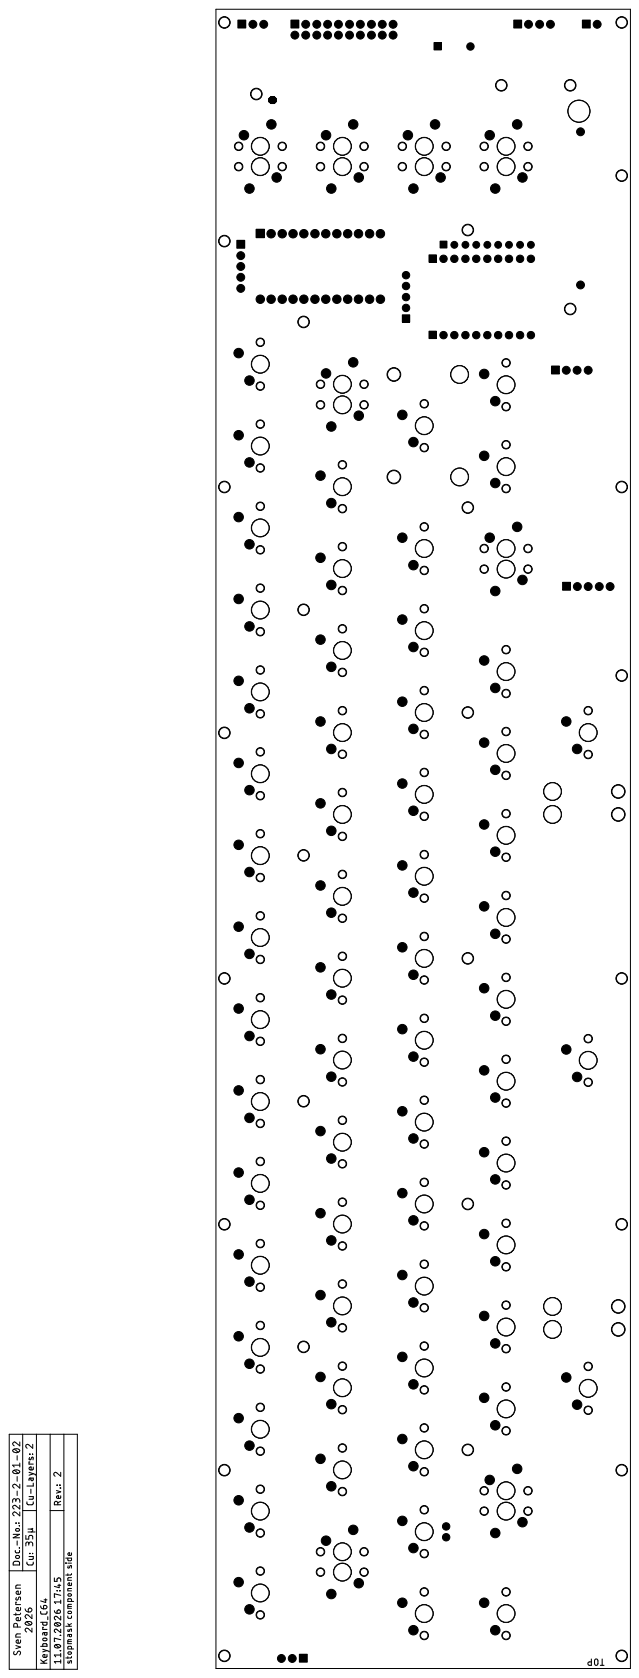
[picture p418: page 7]

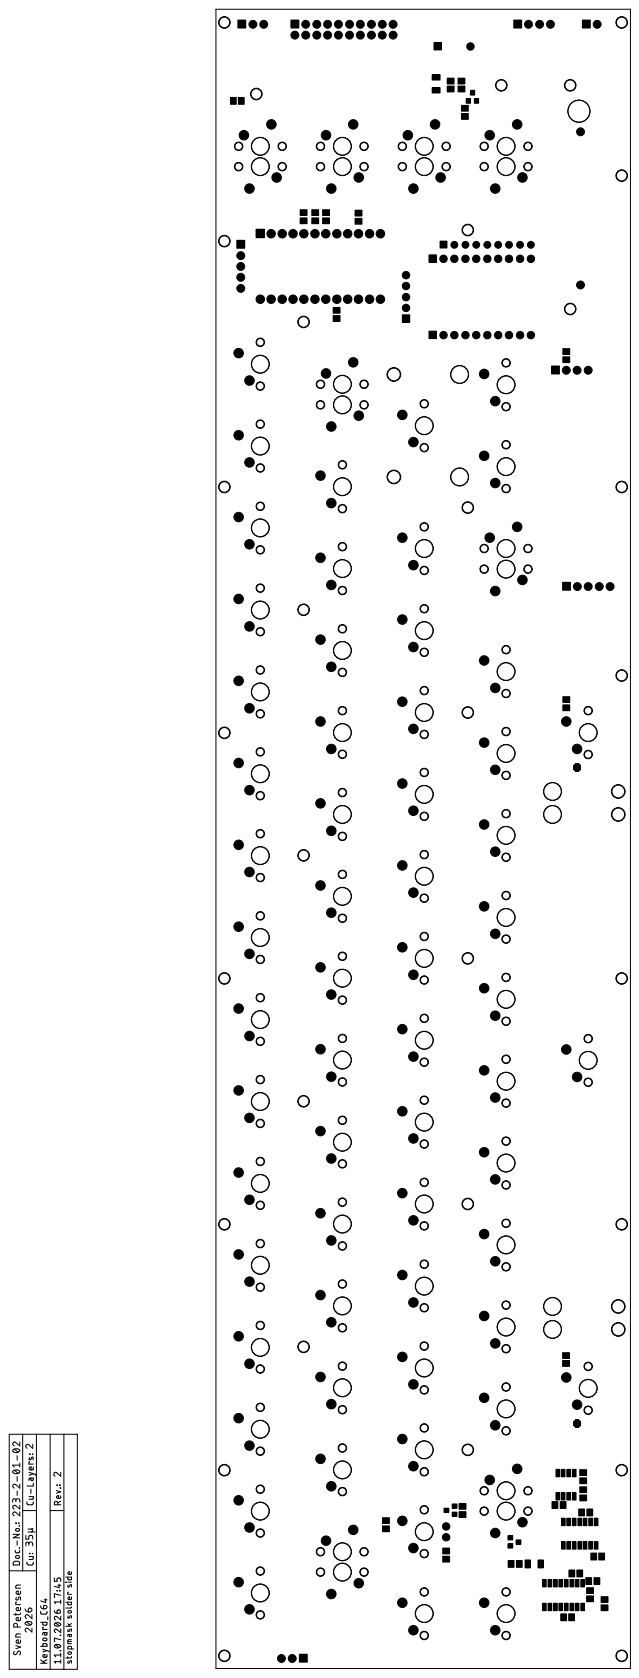
[picture p419: page 8]

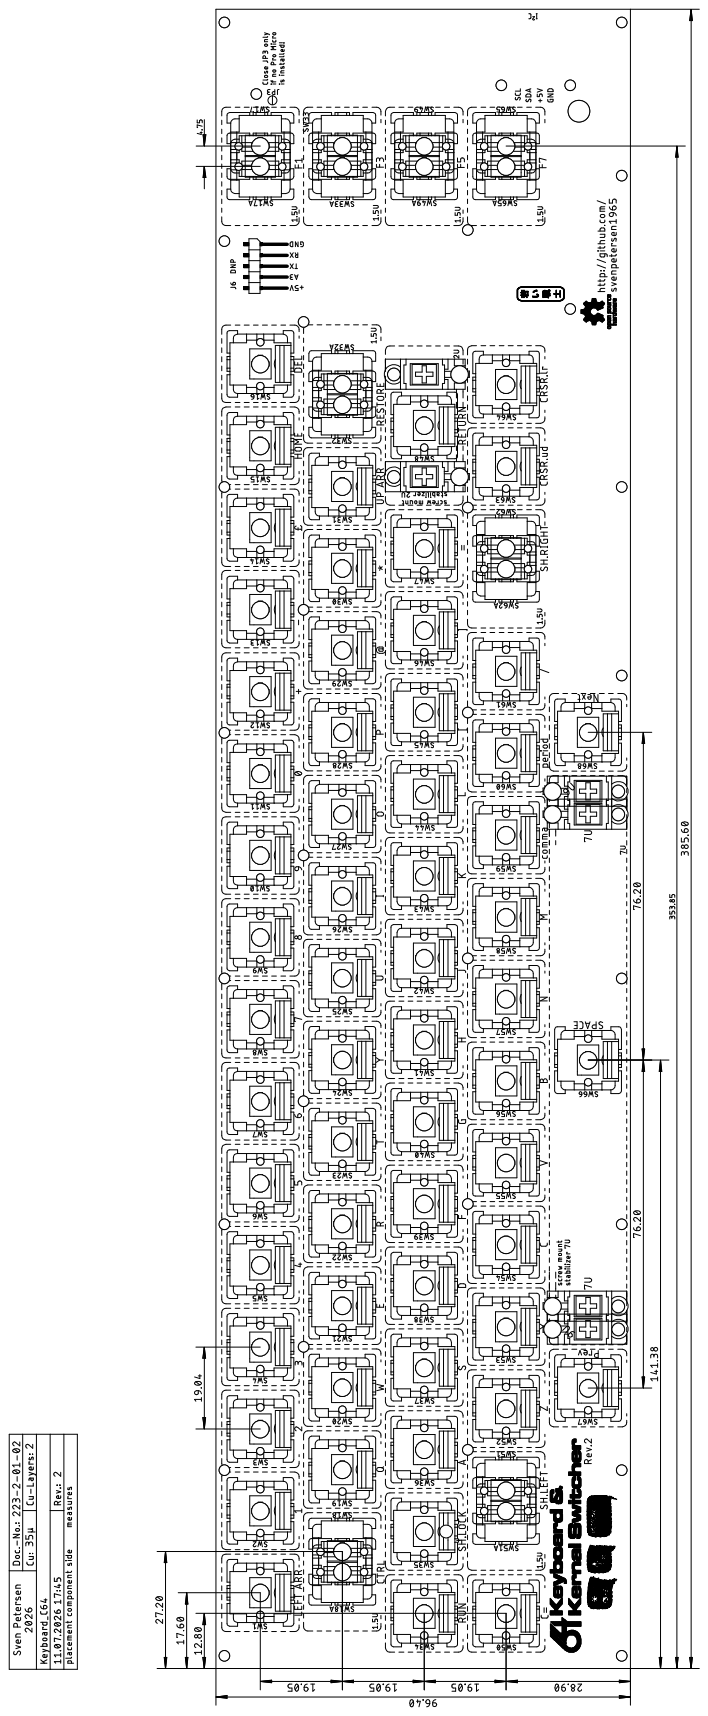
[picture p420: page 9]
