svenpetersen1965/C64-Keyboard/C64 Keyboard Standard Version/Rev. 1/pdf/sch_brd.pdf

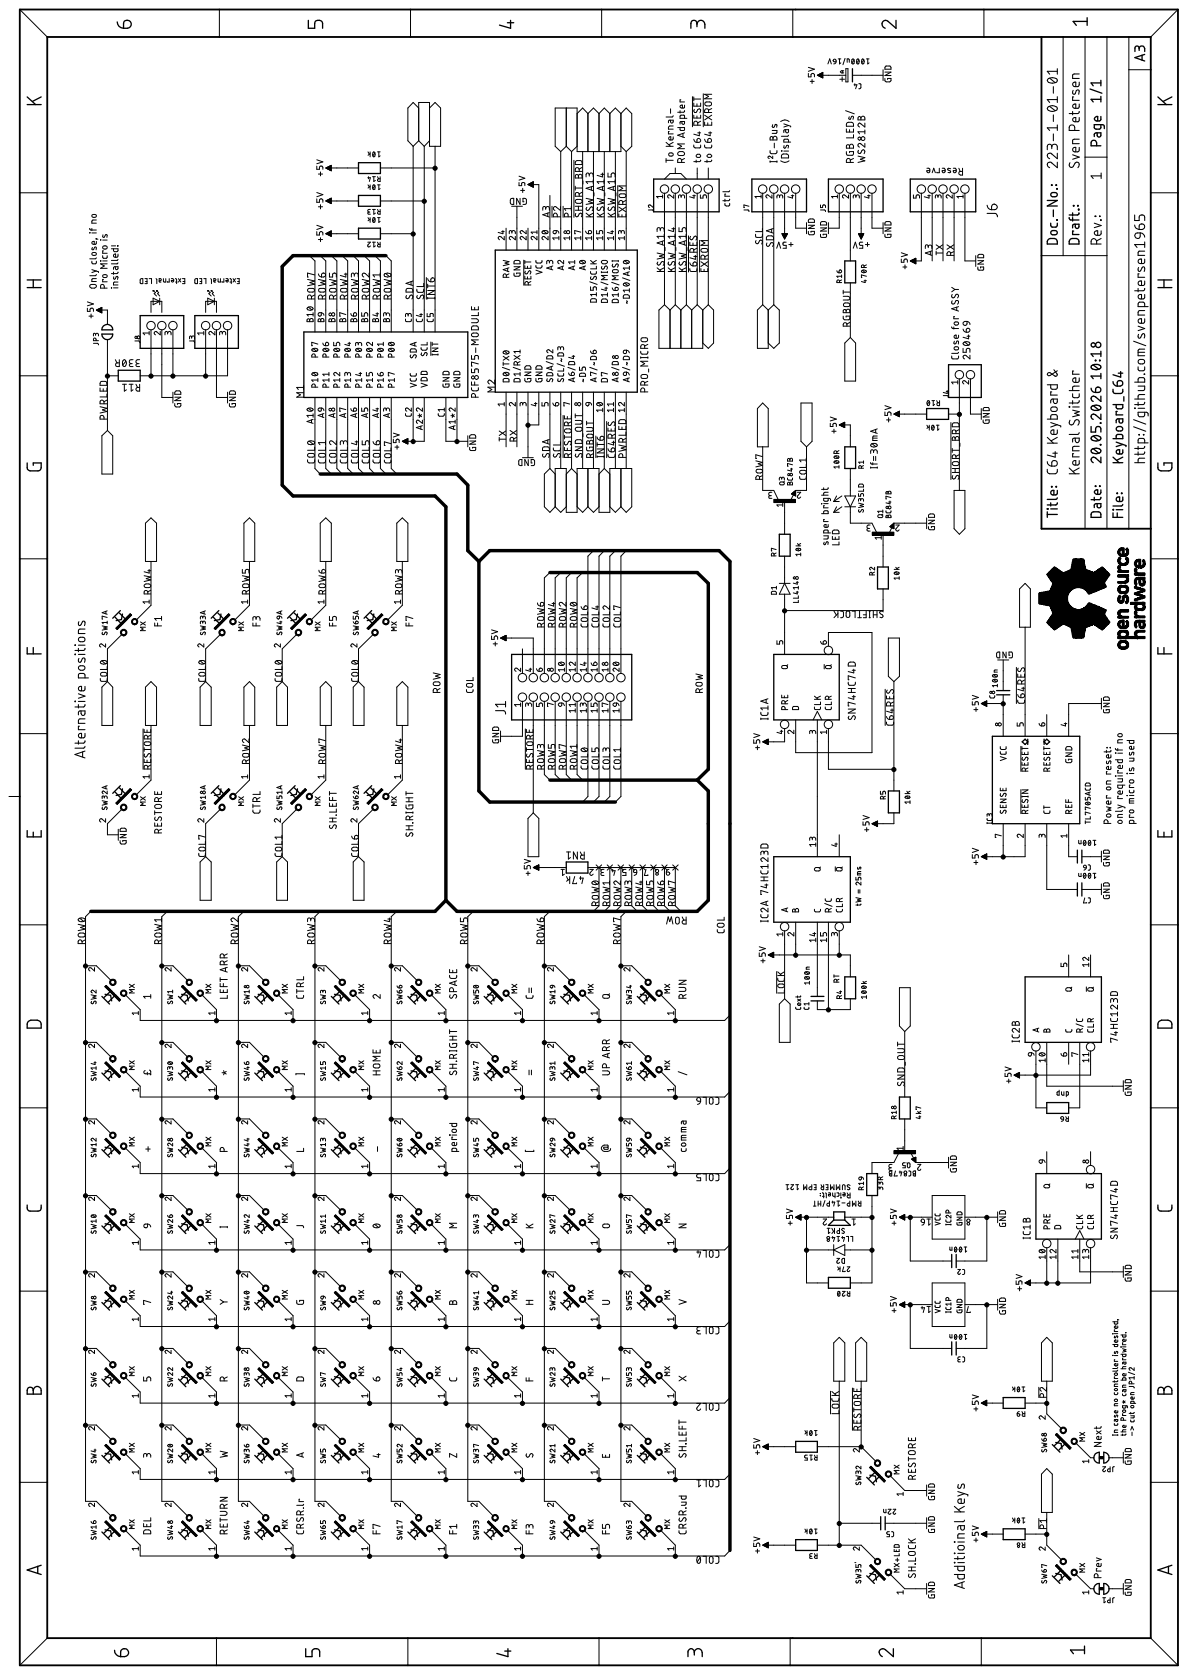
[picture p421: page 1]

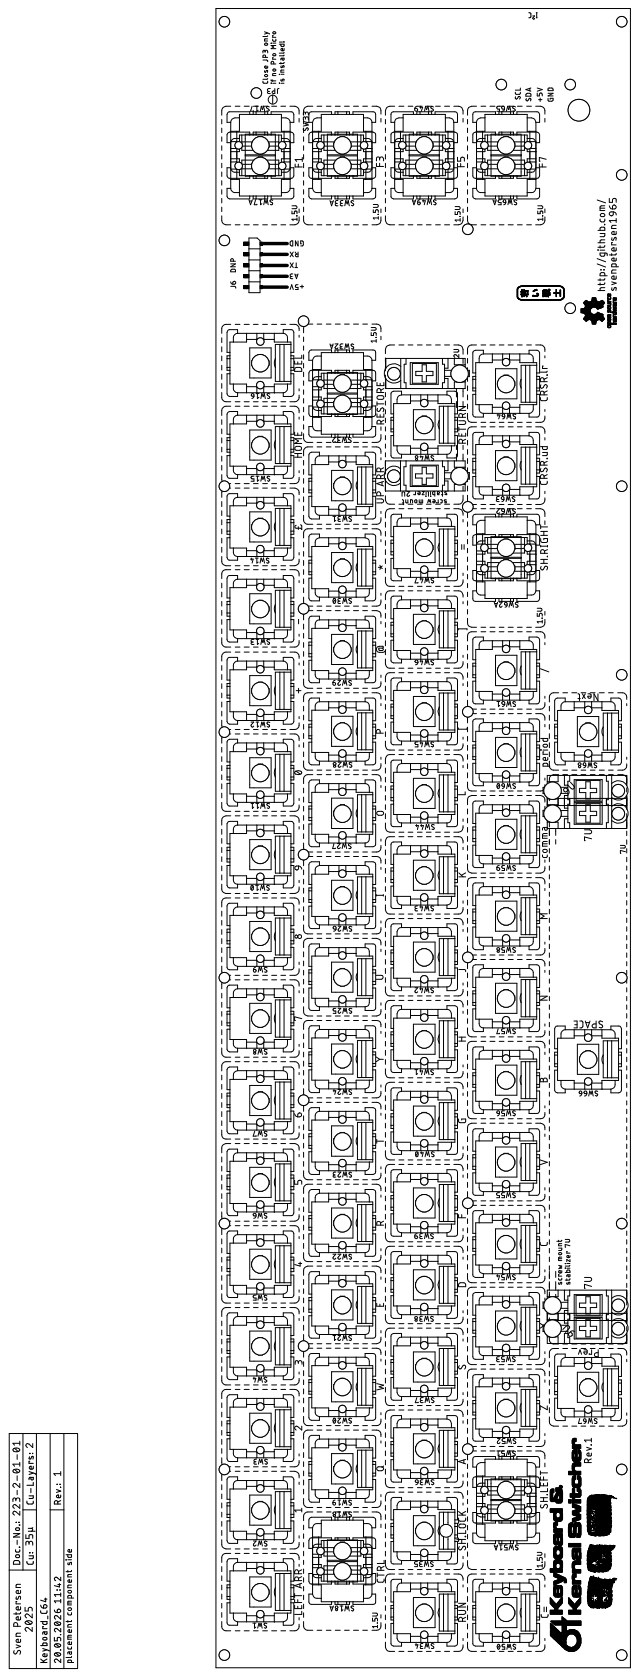
[picture p422: page 2]

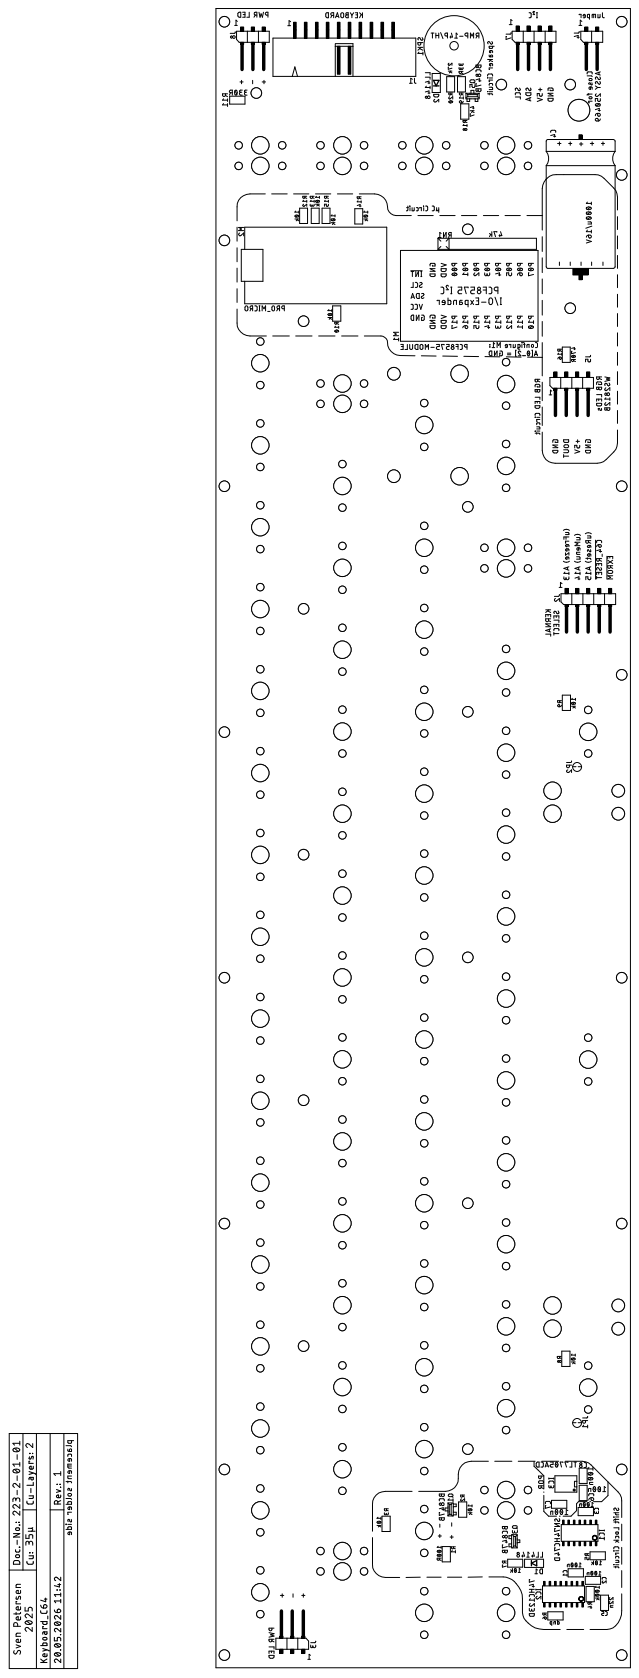
[picture p423: page 3]

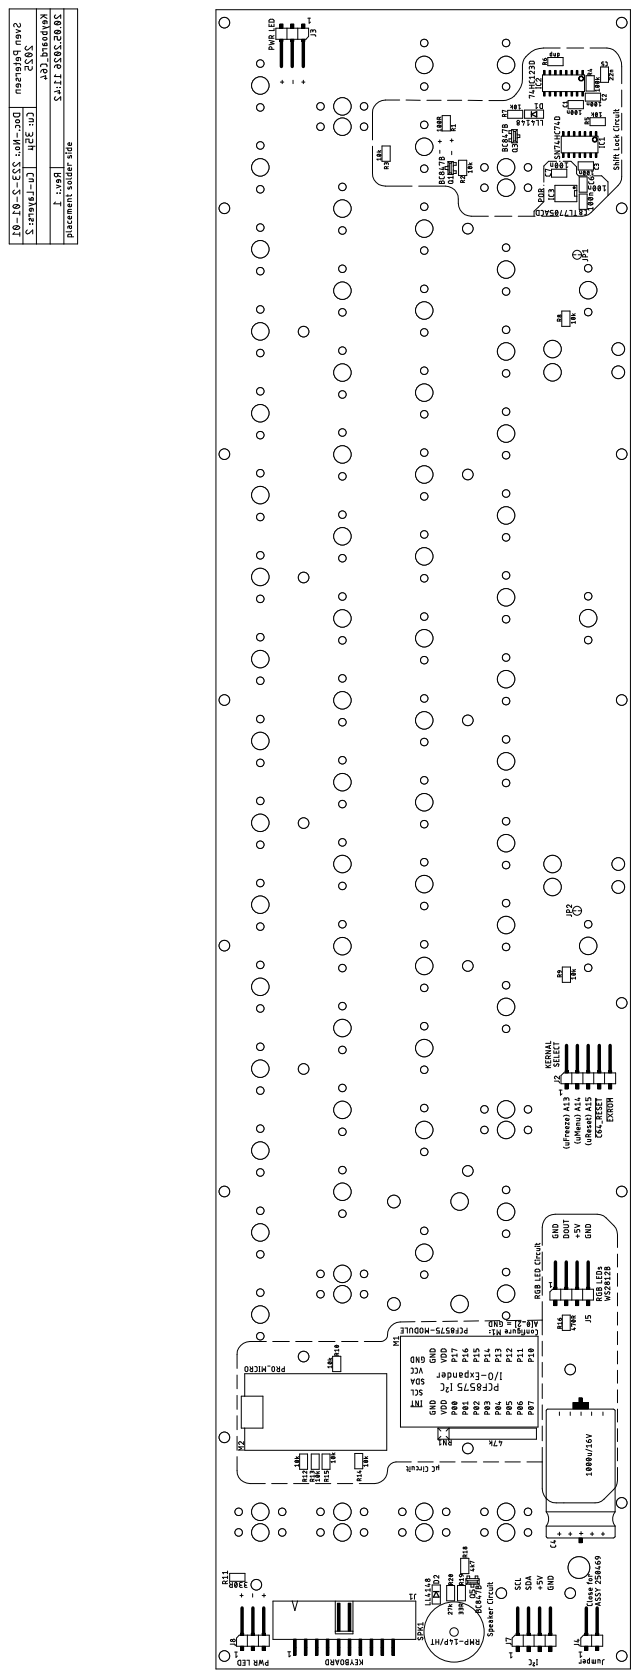
[picture p424: page 4]

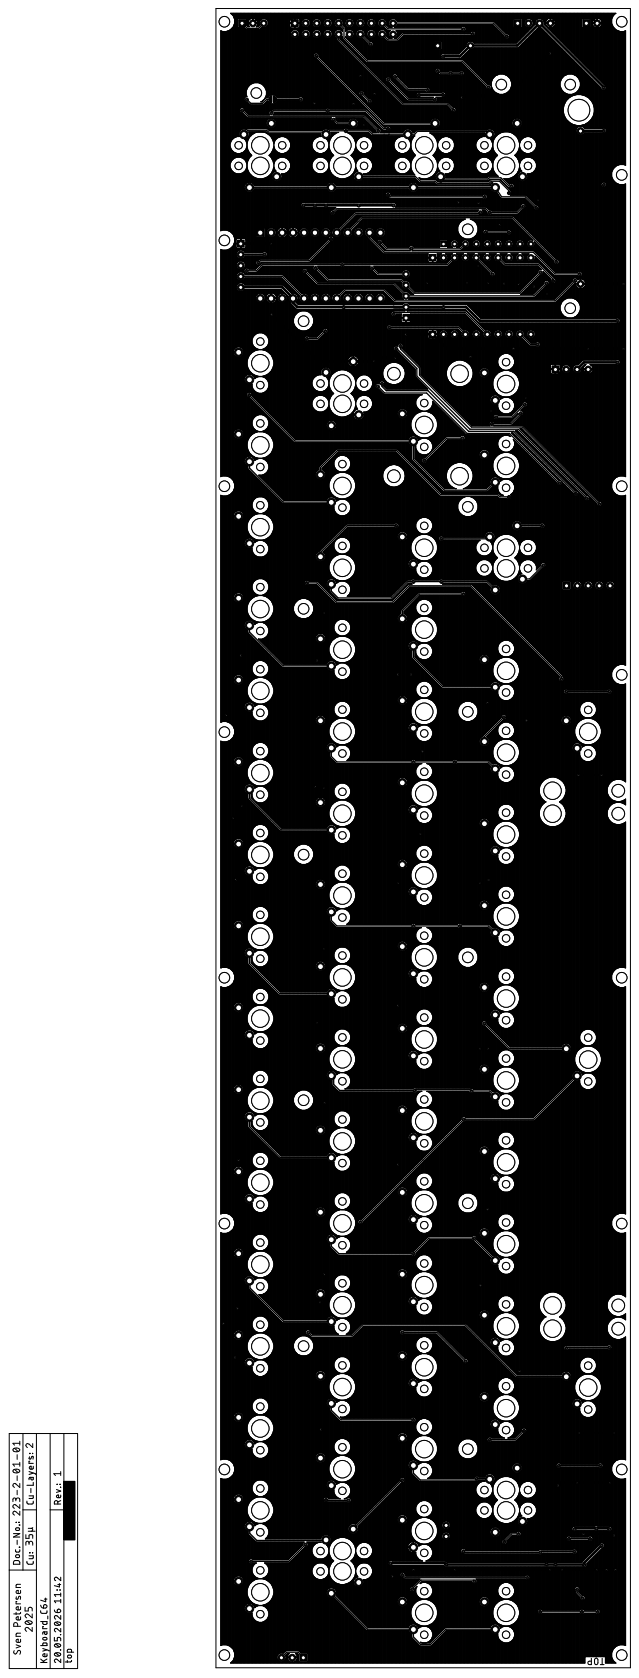
[picture p425: page 5]

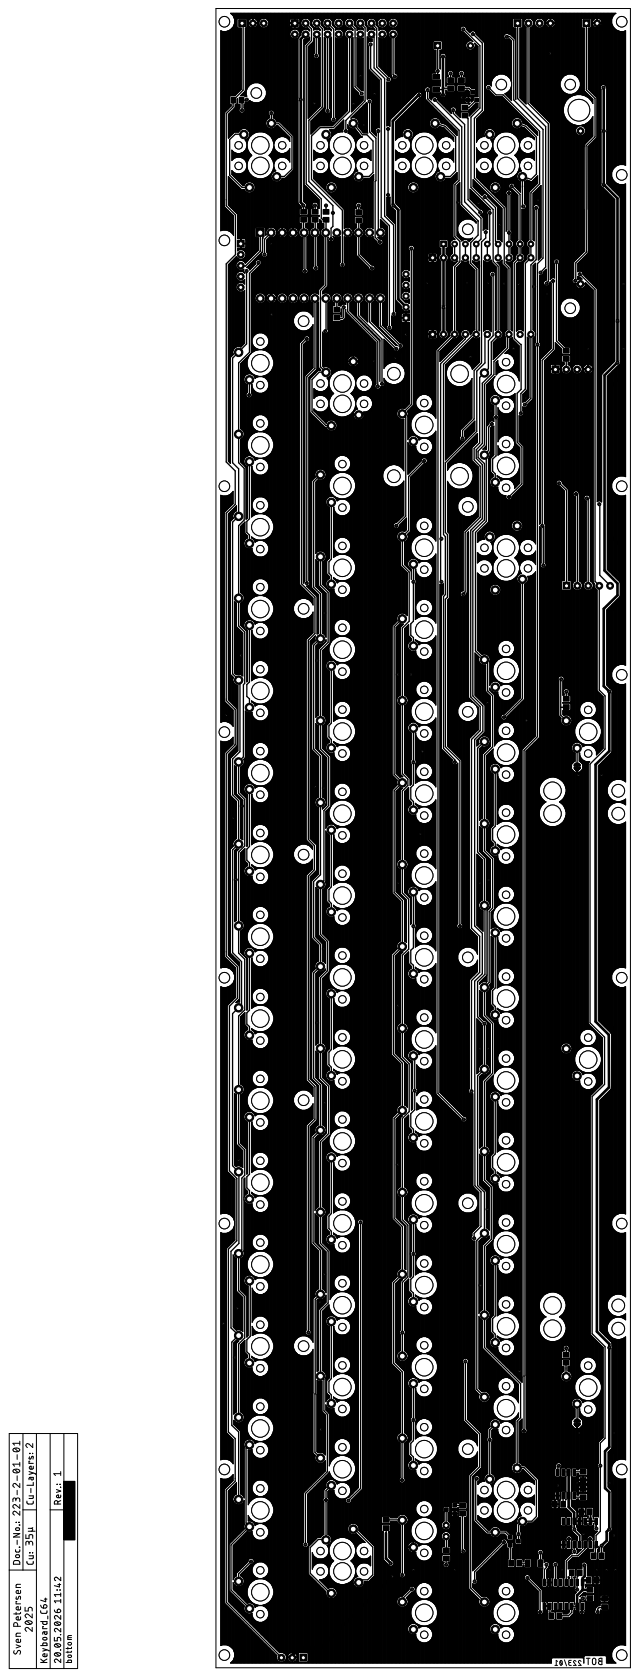
[picture p426: page 6]

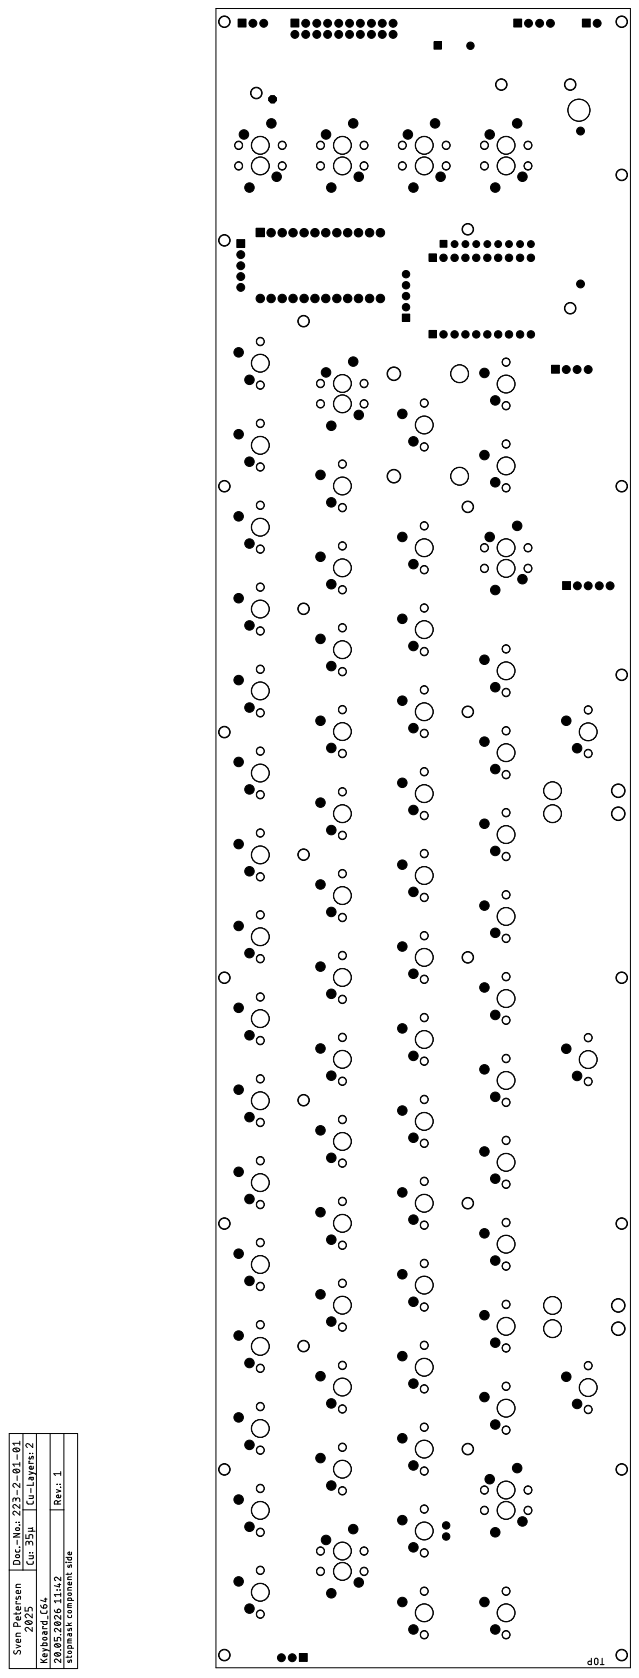
[picture p427: page 7]

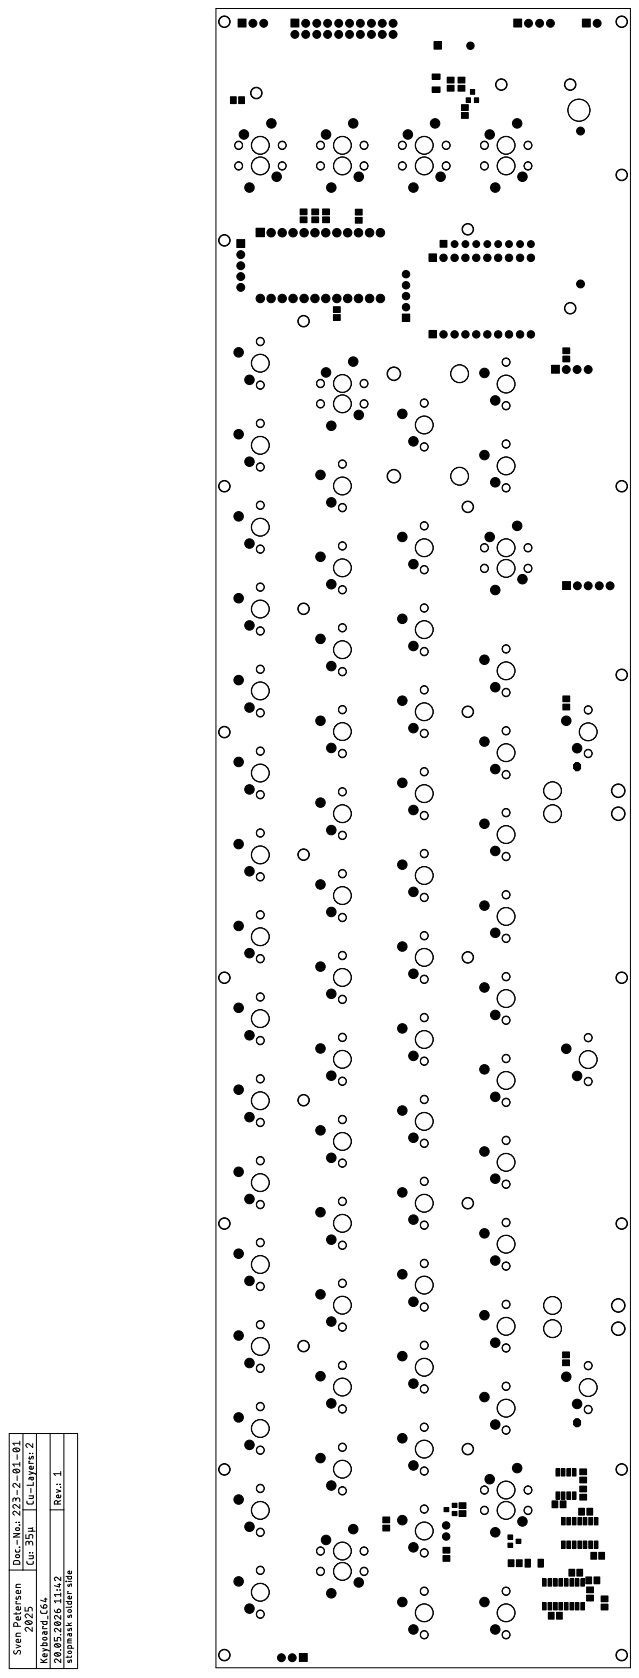
[picture p428: page 8]

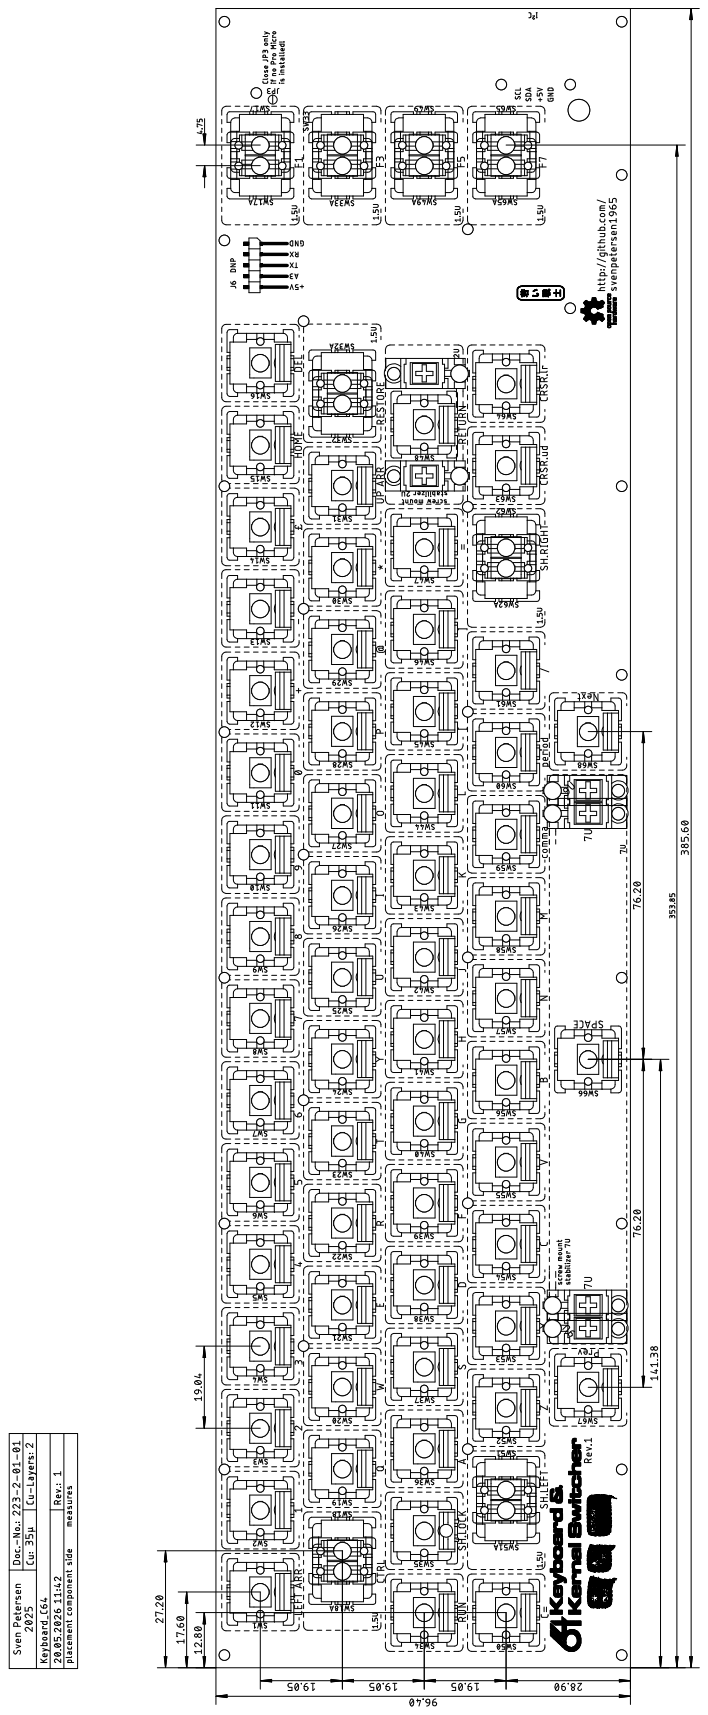
[picture p429: page 9]
